Yannas-Sun/E-skin_MSc_final_report/power scalability/DATA/raw/README.md

# Raw inputs

This folder contains source evidence only. `canonical/` holds the continuous-read power matrix, source photographs, targeted retests and supplements; `intake/` holds the dated voltage additions before they are consumed by the review scripts. Do not edit these records in place. The scripts in `../../script/Main/` read them and write derived outputs under `../analysis/`.
