Yannas-Sun/E-skin_MSc_final_report/power scalability/DATA/reference/README.md

# Reference snapshots

These frozen analyses and figure packages are retained because current manifests cite their hashes. They document earlier report versions and are useful for audit or comparison. They are not additional current measurements and should not be used as a replacement for `../analysis/current/`.
