Yannas-Sun/E-skin_MSc_final_report/data scalability/analysis/20260907_delta_zero_review/README.md

# DELTA zero-load audit

This snapshot contains the independent audit, timing checks, per-slot activity statistics and path/hash records for the 45 selected DELTA zero-load windows. The report''s ordinary-mask trend and byte ledger use the derived CSVs in ../../data together with these audit outputs. Raw recordings remain under ../../data/DELTA/Zero_load/.
