Yannas-Sun/E-skin_MSc_final_report/data scalability/analysis/20260907_n4_connector_retest_review/README.md

# N=4 connector-reinstallation review

This snapshot documents the post-reinstallation M0-M3 simultaneous full-coverage DELTA batch. Three consecutive main windows passed the independent audit and are the selected N=4 dynamic performance set. Organization and hash-verification files distinguish this batch from the pre-reinstallation diagnostic batch in ../20260907_n4_full_coverage_review/.
