Yannas-Sun/E-skin_MSc_final_report/power scalability/DATA/reference/report_v2_4_analysis/README_CN.md

# Power record: reference / report_v2_4_analysis

Derived or source record for the report's power-scalability evidence. Raw measurements are retained as recorded; derived tables and figures are generated from the canonical inputs.

See power scalability/README.md and the nearest parent README for scope and provenance. Do not edit raw records in place.
