Yannas-Sun/E-skin_MSc_final_report/data scalability/data/DELTA/Dynamic_load/README.md

# DELTA dynamic batches

Seven three-window batches are indexed. Five complete passing batches provide the 15-window performance subset; two batches remain diagnostic because of earlier sequence or connector findings.

| Scenario | Windows | PASS / CHECK | Mean packet (B) | USB (Mbit/s) |
|---|---:|---:|---:|---:|
| Earliest M1 large-area batch (diagnostic) | 3 | 0 / 3 | 272.23 +/- 11.24 | 0.433820 +/- 0.019034 |
| M1 large-area follow-up | 3 | 3 / 0 | 282.42 +/- 4.74 | 0.452052 +/- 0.007582 |
| M1 repeated press/release | 3 | 3 / 0 | 210.64 +/- 10.57 | 0.337729 +/- 0.016879 |
| M1 rolling input | 3 | 3 / 0 | 357.72 +/- 11.18 | 0.573369 +/- 0.017977 |
| M1 + M3 simultaneous large-area | 3 | 3 / 0 | 510.90 +/- 11.14 | 0.815880 +/- 0.017786 |
| M0-M3 simultaneous full coverage, before connector reinstallation (diagnostic) | 3 | 1 / 2 | 1,674.37 +/- 55.07 | 2.634962 +/- 0.067917 |
| M0-M3 simultaneous full coverage, after connector reinstallation | 3 | 3 / 0 | 1,471.55 +/- 29.89 | 2.347583 +/- 0.048143 |

The main window is fixed at 10 seconds to recording stop. The pre-reinstallation N=4 batch is retained as diagnostic evidence; its connector-contact finding is not pooled with the post-reinstallation performance batch. No N=3 dynamic or independent small-area batch is present.
