Yannas-Sun/E-skin_MSc_final_report/data scalability/analysis/20260907_final_data_review/before_catalog/README.md

# Archived or internal record

This README belongs to data scalability\analysis\20260907_final_data_review\before_catalog, a superseded snapshot, audit workspace or historical report version. It is retained for provenance only and is outside the current report evidence boundary.

See the nearest current README for the release scope. No measurement data were changed.
