Yannas-Sun/E-skin_MSc_final_report/power scalability/DATA/analysis/current/report_v2_8_analysis/README.md

# Report v2.8 analysis snapshot

This is the latest compiled numerical snapshot used to export the current Power figure set. It contains configuration summaries, branch readings, group summaries, additivity checks, module-drop changes and a complete source_manifest.json.

The snapshot represents 30 ZERO/MAX configuration entries, 64 selected branch observations, 32 paired module-level load differences and seven pointwise targeted branch updates. No new complete-configuration repeat was added.

Use source_manifest.json to verify the upstream report_v2_4_analysis, raw-record, review and script hashes. The CSV fields are descriptive: between-combination SD is not repeatability, sequential branch sums are not simultaneous peaks, and voltage differences are not high-speed transient measurements.
