Yannas-Sun/E-skin_MSc_final_report/data scalability/data/FULL/N=1/200Hz/README.md

# Data record: FULL / N=1 / 200Hz

Canonical record for the report's data-scalability experiments. Raw files in this directory are retained unchanged.

Use the nearest parent README for the condition summary. The run indexes and selected windows are in the parent data directory; report-linked figures are under the LaTeX figures/data directory.
