Yannas-Sun/E-skin_MSc_final_report/data scalability/analysis/20260907_delta_zero_review/coverage_review.md

# DELTA 零载记录：覆盖范围、来源与时间戳复核

复核时间：2026-09-07。对象为 `20260907_013132_404213` 至
`20260907_020930_401399` 的 45 次记录。仅阅读原始目录并生成本分析目录中的派生文件；
读取前后文件大小及修改时间一致。原始流的独立解码验证见同次审计的其他输出。

## 实验覆盖

- 四个槽位的全部 15 种非空组合均齐全，每种恰好 3 次记录，无缺项。
- N=1、2、3、4 分别有 12、18、12、3 次记录。
- 15 个 batch 的重复编号均为 1、2、3，同一 batch 的模块组合保持一致。
- 45 次均标记 `DELTA`、`zero_load`、目标 200 Hz，实际开始观测模式为 DELTA。
- 每次请求录制 40 s，前段 10 s；实际总时长 40.000074–40.053896 s，
  主分析窗口 30.000074–30.053896 s。45 次均正常到时结束，没有未完成记录。
- 所有 block 均为 1。`batch_recording_method` 明确为
  `consecutive_capture_windows_same_setup`：这是同一次装配下连续采集的三次时间重复，
  并非三个独立重新接线、重新装配或重新加载的实验区组。重复统计应如实注明这一层级。

## 记录来源及身份的边界

全部 45 次保存的六项本地文件哈希一致（STM32 ELF、Teensy HEX、GUI、recorder、controls、
module detection）。版本目录为 `four-module-variable-spi`。这支持本地构建/记录器来源一致；
哈希没有读取设备 Flash，且 `deployment_confirmed=false`，不能单靠这些 JSON 证明板上镜像。
用户的烧录过程记录可作为另一个来源补充。

SPI 10 MHz、DELTA 阈值 8 是本地配置元数据，目标 200 Hz 是 GUI 设置；这些字段不是
SPI 波形测量或固件配置回读。45 次均采用自动槽位检测并冻结预期集合，但
`board_identity_handling=slots_only`、物理板映射为空。M0–M3 是 CS/IRQ 槽位，
协议未传输唯一板卡身份码；跨组合比较同名槽位时，仍需由实验操作记录确认是否为同一块物理板。

## 完整性状态为何全程 CHECK、主窗口 PASS

主窗口全部 45 次 PASS：270,412 个有效 MUL1 包、576,926 次预期模块更新，
有效模块更新数与预期数相等，诊断载荷为零。574,042 个 ESKD 与 2,884 个 ESKF
均在已建立的文件内基线后被应用。逐次 packet CSV 的主窗口有效包数与 summary 完全一致。

全程全部标记 CHECK REQUIRED，原因是录制是在正在运行的 DELTA 流中截取窗口：
45 次文件开头均有尚未在该文件内建立基线的 ESKD，累计 10,540 个模块帧。
这不能等同为实时 GUI 丢帧或缓存失效。30 次末端保留各 1 B 截断边界，
累计 30 B；另有 35 个跨录制起点的外包，其已知后缀累计 10,189 B 单独记账。
主窗口排除了最初 10 s，已获得完整帧基线；正常文件边界字节不作为内部传输错误。

全程及主窗口的会话差分计数均未出现 outer/inner CRC、序号缺口、重复、倒序、
format error 或 DELTA base mismatch；缺失预期模块更新均为零。
这支持“这些捕获窗口内未观测到所检查的传输/重建错误”，不构成物理 ADC 扫描绝不丢失的证明。

## 到包时间不是 SPI 时钟

主窗口共 270,367 个文件内相邻包间隔：

| 时间来源 | 中位数 | P95 | P99 | 最小值 | 最大值 |
|---|---:|---:|---:|---:|---:|
| PC 包完成时刻差 | 4.8551 ms | 10.8040 ms | 18.4817 ms | 0 ms | 4040.8594 ms |
| Teensy `host_ms` 差 | 5 ms | 5 ms | 6 ms | 3 ms | 7 ms |

PC 有 38,603 个零间隔，表示多个包共享同一次接收处理的完成时间戳；没有负间隔。
23 次记录出现过 PC 间隔超过 100 ms，累计 162 次；Teensy 时间戳没有超过 100 ms 的间隔。
这些相邻包的 MUL1 序号步长全部为 1。

最大的三个 PC 间隔分别为：

| run_id | PC 间隔 | 同一对包的 Teensy 间隔 | 序号步长 |
|---|---:|---:|---:|
| `20260907_020041_855845` | 4040.8594 ms | 5 ms | 1 |
| `20260907_014545_965962` | 3783.2828 ms | 5 ms | 1 |
| `20260907_015550_103879` | 3737.0086 ms | 5 ms | 1 |

这表明 PC 记录的完成时间明显受到接收缓冲、批处理或调度停顿影响；没有证据把它归因为
SPI SCK 不稳定。`host_ms` 由 Teensy 在构建/入队 MUL1 时调用 `millis()` 写入，
其 1 ms 分辨率也不是 SPI 边沿或 ADC 扫描时刻测量。

按同一批包的首尾 Teensy 时间戳计算，各次频率约为 200.0733–200.4065 Hz；
主窗口包数除以 PC 窗口时长则为 199.3419–204.0041 Hz。特别是
`20260907_015217_328962` 的主窗口有 6,121 个包，PC 统计约 204.0041 Hz，
这些包在 Teensy 时间轴上首尾相隔 30.549 s（约 200.3339 Hz）。
缓冲使 PC 窗口与源端时间窗口不完全对应，不能把 204 Hz 解读为实际扫描加速。
统计接收吞吐可以使用 PC 窗口，但分析扫描节奏、ESKF 时间间隔或短期时序应同时报告
Teensy 时间轴，并明确两者测量位置。绝对单程延迟不能从未同步的两个时钟直接求得。

复现：`python -B timing_review.py`。该脚本冻结上述 run_id 范围并递归定位目录，
方便整理目录后再次运行。详细输出为 `coverage_review.json`、`timing_summary.json`
及 `timing_per_run.csv`。
