Yannas-Sun/E-skin_MSc_final_report/data scalability/analysis/20260907_full_completion_review/ANALYSIS_CN.md

# FULL 补测完成审计：新 M012 批次与 N=4

固定六条新完成记录，只读 raw/packet_log/module_log/events/summary，不改原文件。旧 42 条不算新增未审计。M012 新批次独立存放，原 Repeat 1–3 与原失败证据不覆盖。

| 新批次 | n | 主窗 Hz 均值 ± 样本 SD | 完整包长度 B | 完整包吞吐 Mbit/s 均值 ± SD | main/full PASS |
|---|---:|---:|---:|---:|---:|
| M0+M1+M2 / N=3 | 3 | 200.084479 ± 0.057550 | 3172 | 5.077344 ± 0.001460 | 3/1 |
| M0+M1+M2+M3 / N=4 | 3 | 200.066062 ± 0.034040 | 4216 | 6.747828 ± 0.001148 | 3/2 |

逐包核验候选 48,070 / 有效 MUL1 48,070，有效 ESKF 168,243；主窗口候选 36,017 / 有效 MUL1 36,017 / ESKF 126,058。核对 192,280 行 module_log。

长度按 N 动态验证：40+1044N，因此 N=3 为 3172 B、N=4 为 4216 B。扫描每个 MAGIC，包括可能被坏候选覆盖的内部 MAGIC；候选与有效包分别统计。独立核对外 CRC、内 CRC、版本/flags/mask、MUL1 和模块序号、实际有效槽位、日志 offset/长度/序号/时间/字段、raw SHA256 及原 summary 同口径计数。

独立非零问题：`{}`。

全部六条主窗口 PASS，可用于各自条件的性能分析。全窗口三条 PASS，另三条仅因结束时保留 1 B M 片段而 CHECK；没有内部 unassigned、CRC、序号、漏更新或原日志未解析的有效重叠包。原状态不改。

启动边界共 4 个：2 个用前段真实尾字节+后段真实前缀双层 CRC 验证；2 个每批首段仅补推定 M 验证一致性。边界后缀单列，不回填前缀，不混入完整包率/K/q。

## 每段状态及时间停顿线索

- `20260907_004948_668301`：N=3；候选/有效 8005/8005；main=PASS / full=CHECK REQUIRED；主窗 200.138830 Hz。最大 PC 包完成间隔 32.222400 ms（桥端相邻间隔 5 ms）；最大桥端 host_ms 间隔 6 ms（2243844→2243845）。
- `20260907_005028_724004`：N=3；候选/有效 8014/8014；main=PASS / full=PASS；主窗 200.090418 Hz。最大 PC 包完成间隔 54.175100 ms（桥端相邻间隔 5 ms）；最大桥端 host_ms 间隔 6 ms（2252091→2252092）。
- `20260907_005108_797842`：N=3；候选/有效 8018/8018；main=PASS / full=CHECK REQUIRED；主窗 200.024190 Hz。最大 PC 包完成间隔 278.793500 ms（桥端相邻间隔 5 ms）；最大桥端 host_ms 间隔 6 ms（2258809→2258810）。
- `20260907_005250_875035`：N=4；候选/有效 8003/8003；main=PASS / full=CHECK REQUIRED；主窗 200.066611 Hz。最大 PC 包完成间隔 32.093100 ms（桥端相邻间隔 5 ms）；最大桥端 host_ms 间隔 6 ms（2278237→2278238）。
- `20260907_005330_930696`：N=4；候选/有效 8013/8013；main=PASS / full=PASS；主窗 200.031751 Hz。最大 PC 包完成间隔 48.704400 ms（桥端相邻间隔 5 ms）；最大桥端 host_ms 间隔 6 ms（2286880→2286881）。
- `20260907_005410_996854`：N=4；候选/有效 8017/8017；main=PASS / full=PASS；主窗 200.099825 Hz。最大 PC 包完成间隔 18.478100 ms（桥端相邻间隔 5 ms）；最大桥端 host_ms 间隔 6 ms（2296625→2296626）。

PC 完成间隔受读取、缓冲与调度影响，不等同 SPI 时钟周期；桥端 host_ms 也是协议时间字段。这些停顿线索与序号/CRC审计分开保留，不能只凭一次时间间隔定位硬件、USB或PC根因。

历史必须保留：原 M012 `20260907_000133_670681` 的主窗口仍为 CHECK，包含短缺/损坏候选及一个 raw 可恢复、PC漏解析的包。本轮新批次通过，不能改写为之前全部 48 条均无错误。新三条 M012 是补测批次；此前两条 PASS 可由父任务在明确批次来源后另行汇总，原失败条不覆写。

三段是同一 setup 的连续时间重复，不等于独立重新搭建 block；物理板身份不能从槽位ID唯一确定；记录内本地源文件hash不等于设备flash读回。本轮完成的是FULL零载条件，DELTA及动态/K实验仍需独立数据。

迁移后脚本按 summary.run_id 递归定位当前目录，可查父任务 run_index/path_map；原summary历史files路径不改。复现：`python -B audit_records.py`。新完成未纳入记录：无
