Yannas-Sun/E-skin_MSc_final_report/data scalability/analysis/20260907_n3_full_review/ANALYSIS_CN.md

# N=3 FULL 独立审计：保留异常与原统计口径

固定 12 条已完成记录，M012/M013/M023/M123 各 3 条；不改原始 raw、packet_log、module_log 或 summary。旧 N=1/N=2 不计作新增未审计。

| 组合 | PASS 性能 n | PASS 主窗 Hz 均值 ± 样本 SD | 全3条诊断 Hz 均值 ± SD |
|---|---:|---:|---:|
| M0+M1+M2 | 2 | 200.131100 ± 0.000728 | 200.091843 ± 0.067998 |
| M0+M1+M3 | 3 | 199.766908 ± 0.556959 | 199.766908 ± 0.556959 |
| M0+M2+M3 | 3 | 200.165942 ± 0.036616 | 200.165942 ± 0.036616 |
| M1+M2+M3 | 3 | 200.218529 ± 0.040178 | 200.218529 ± 0.040178 |

原日志共 96,120 个候选，其中 96,119 个外 CRC 有效，拒绝 1 个；主窗口候选 72,029、有效 72,028。核对 module_log 384,476 行，有效 ESKF 288,357 个。独立全 MAGIC 扫描另找到一个 CRC 有效但原日志漏解析的重叠包，故 forensic 数量与原日志口径分开。

主窗口有效 ESKF 216,084 个；11 条 PASS 性能子集仅包含 66,027 个主窗口 MUL1 / 198,081 个 ESKF。异常记录仍保留在全部 12 条诊断统计中。

## 首段异常：20260907_000133_670681（M0+M1+M2 Repeat 1）

异常发生在 elapsed **19.4723392 s**（主窗口开始后 9.4723392 s），PC 记录完成时间 **00:01:53.143020 +01:00**。原统计完整候选 8003 / CRC 有效 8002；主窗口候选 6002 / 有效 6001。该段 main/full CHECK 原样保留，性能汇总的 M012 仅使用另外两条 PASS，n=2；全三条另列诊断统计，不静默删除异常。

| 观察 | 序号 | raw 字节 offset | 长度/状态 |
|---|---:|---:|---|
| 前有效包 | 1675976 | 12326391 | 3172 B；双层 CRC 有效 |
| 被拒候选 | 1675977 | 12329563 | 声明 3172 B；外 CRC 错 |
| raw 中有效、原日志未解析包 | 1675978 | 12331711 | 3172 B；外 CRC 与三个 ESKF 内 CRC 全有效 |
| 原日志恢复有效解析 | 1675979 | 12334883 | 3172 B；双层 CRC 有效 |

5977 头到 5978 头实际相隔 **2148 B**，比头中声明 3172 B 少 **1024 B**。这直接支持字节流存在短缺/畸形片段，不能仅凭 raw 判定发生在 Teensy 构包、USB/驱动、串口缓冲或 PC 读取的哪一层。不能声称已证明 USB 物理丢了两个包。

当时 framer 从 5977 头取满声明的 3172 B，包含下一个有效 5978 的前 1024 B。CRC 被拒后，后续重同步跳过 5978 余下的 2148 B，直到 5979。因而原 Session **lost=2** 包含 **1 个短缺/损坏候选 5977，加 1 个 raw 中仍完整有效但被 PC 解析跳过的 5978**。独立所有 MAGIC 扫描恢复的是证据，未回填原日志或修改原计数。

原日志将区间 **[12332735,12334883)** 的 2148 B 标为 interior unassigned；这些字节实际是有效包 5978 的后缀，不是随机垃圾。若按独立有效包范围看，无法由有效包覆盖的是较早的 **[12329563,12331711)** 2148 B 短缺候选片段。两种范围碰巧同为 2148 B，但位置与含义不同，不能混淆。另有 1 B 结束边界。

有效包对应三个模块内序号为：5976 的 M0/M1/M2 = 8040/8041/8040；raw 恢复 5978 为 8042/8043/8042；5979 为 8043/8044/8043。原日志成功包跨过两次序号；计入 raw 可恢复包后只剩一次缺口。原 summary 的模块更新 18003/18003 是**以已接受外 CRC 有效包为条件**，不包含整个被拒包，不能据此声称主窗口完全没有传输异常。

## M013 Repeat 3：199.123828 Hz

20260907_001505_375008 的主窗口为 5974 个有效包 / 30.001432 s = **199.123828 Hz**；CRC、MUL1/模块序号和日志一致性没有异常，保留为 PASS，n=3 性能统计不得为提高均值而剔除。

桥端 host_ms 在连续序号 **1836089→1836090** 之间相隔 **123 ms**，三个模块内序号各增加 1。PC 完成时间最大间隔 **301.3735 ms**（1836053→1836054），对应桥端 host_ms 仅隔 5 ms，说明 PC 接收/调度时间和桥端时间不能混为一个时钟。数据支持这一段存在输出/观测节奏停顿，不能用低帧率直接断言包序号丢失，也不能仅凭记录定位停顿根因。末尾保留 **1020 B** 未完成包片段，是结束边界，不是首段的 interior 故障。

## 逐段原始状态

- `20260907_000133_670681`：main=CHECK REQUIRED / full=CHECK REQUIRED；候选/有效=8003/8002；主窗=200.013328 Hz；cross-check={}；full理由=['outer_crc_error', 'pc_parser_errors', 'outer_sequence_gap_events', 'session_lost_frames', 'session_outer_crc_errors', 'session_sequence_gap_events', 'unassigned_raw_bytes_in_full_capture']。
- `20260907_000213_737553`：main=PASS / full=PASS；候选/有效=8016/8016；主窗=200.131615 Hz；cross-check={}；full理由=[]。
- `20260907_000253_764287`：main=PASS / full=CHECK REQUIRED；候选/有效=7998/7998；主窗=200.130585 Hz；cross-check={}；full理由=['unassigned_raw_bytes_in_full_capture']。
- `20260907_001345_234235`：main=PASS / full=CHECK REQUIRED；候选/有效=8005/8005；主窗=200.094736 Hz；cross-check={}；full理由=['unassigned_raw_bytes_in_full_capture']。
- `20260907_001425_309099`：main=PASS / full=PASS；候选/有效=8018/8018；主窗=200.082161 Hz；cross-check={}；full理由=[]。
- `20260907_001505_375008`：main=PASS / full=CHECK REQUIRED；候选/有效=7988/7988；主窗=199.123828 Hz；cross-check={}；full理由=['unassigned_raw_bytes_in_full_capture']。
- `20260907_001710_986331`：main=PASS / full=CHECK REQUIRED；候选/有效=8007/8007；主窗=200.144160 Hz；cross-check={}；full理由=['unassigned_raw_bytes_in_full_capture']。
- `20260907_001751_034069`：main=PASS / full=CHECK REQUIRED；候选/有效=8015/8015；主窗=200.145451 Hz；cross-check={}；full理由=['unassigned_raw_bytes_in_full_capture']。
- `20260907_001831_069491`：main=PASS / full=CHECK REQUIRED；候选/有效=8014/8014；主窗=200.208216 Hz；cross-check={}；full理由=['unassigned_raw_bytes_in_full_capture']。
- `20260907_003258_918645`：main=PASS / full=PASS；候选/有效=8008/8008；主窗=200.231866 Hz；cross-check={}；full理由=[]。
- `20260907_003339_025463`：main=PASS / full=CHECK REQUIRED；候选/有效=8031/8031；主窗=200.250342 Hz；cross-check={}；full理由=['unassigned_raw_bytes_in_full_capture']。
- `20260907_003419_073823`：main=PASS / full=PASS；候选/有效=8017/8017；主窗=200.173378 Hz；cross-check={}；full理由=[]。

建议：首条 M012 Repeat 1 保留为完整性失败证据，并补一条同条件重复用于达到 3 条 PASS 性能数据；明确后补的时间与新 run_id，不覆写原 Repeat 1。其余 11 条主窗口可用；低率 PASS 记录保留。若研究目标包括恢复能力，可将此次坏包后的漏解析作为已发现的 PC 恢复行为局限，不能宣称协议已无损恢复。

三次是同一 setup 的时间重复，不是三个独立 block。所有有效完整包应为 3172 B（20+16+3×1044+4）。槽位不是唯一板卡身份；本地代码哈希不是设备 flash 读回。raw 本身无 PC 到达时间，主窗口依赖日志完成时间。

脚本按 summary.run_id 递归定位，因此搬迁后可复跑；原 summary 的历史 files 路径不改，可查父任务 run_index/path_map。复现：`python -B audit_records.py`。新完成未纳入记录：无
