Yannas-Sun/E-skin_MSc_final_report/power scalability/DATA/analysis/current/report_v2_8_figures/single_module_screening.pdf

Blocked, zero load | Continuous, zero load | Continuous, loaded

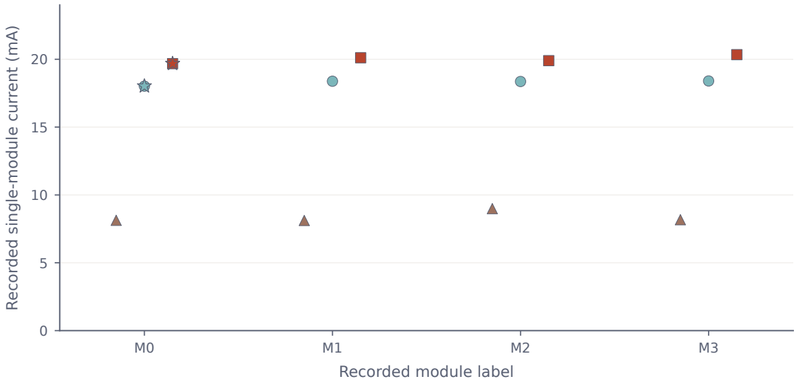
[picture p20: figure]
Recorded module label; Recorded single-module current (mA)
