Yannas-Sun/E-skin_MSc_final_report/data scalability/figures/exports/02b_usb_theoretical_200hz.pdf

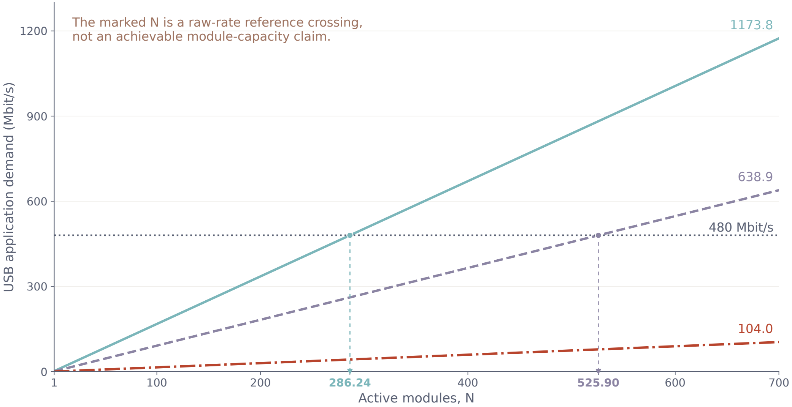
[picture p44: figure]
Active modules, N; USB application demand (Mbit/s); 480 Mbit/s; not an achievable module-capacity claim.

The marked N is a raw-rate reference crossing,

## 02B USB: 200 Hz demand across 700 modules

N = 1–700 | fixed round frequency = 200 Hz | theoretical demand, not achieved throughput

Nominal periodic ESKF only: T=1 s; q=min(1,1/fT); q_other=0. Continuous-cycle approximation. H(M) = 24 + 4M B; N <= M. Current M = 4; N > 4 uses M = max(4, N) as extrapolation.

FULL / mean DELTA K_D=480
Mean DELTA K_D=240

Mean DELTA K_D=0
USB 2.0 HS: 480 Mbit/s raw signaling
