Yannas-Sun/E-skin_MSc_final_report/data scalability/figures/exports/02d_host_spi_theoretical_200hz.pdf

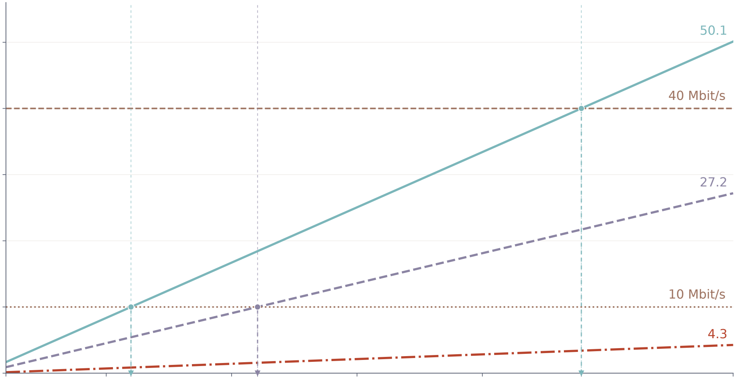
[picture p45: figure]
10 Mbit/s; 40 Mbit/s

1 | 5 5.99 | 1011.03 | 15 | 20 | 23.95 | 30

## Active modules, N

0

10

20

30

40

50

## Host SPI demand (Mbit/s)

# 02D Host SPI: 200 Hz mean DELTA demand

N = 1–30 | nominal periodic reference q=0.005 | no padding or MUL1 wrapper

Nominal periodic ESKF only: T=1 s; q=min(1,1/fT); q_other=0. Continuous-cycle approximation.
Mean SCK budget; no gaps, software or retries. FULL bursts may exceed a round deadline. N>4: extrapolation.

## Mean DELTA, K_D=0 Mean DELTA, K_D=240 FULL / mean DELTA K_D=480

## 10 MHz tested setting: 10 Mbit/s raw 40 MHz untested reference: 40 Mbit/s raw
