Yannas-Sun/E-skin_MSc_final_report/data scalability/figures/exports/07_delta_model_k.pdf

0 | 120 | 240 | 360 | 480
| | Changed cells per module, K

0

20

40

60

80

100

Equivalent round size (kB)

N=1: 1.08

N=25: 26.22

N=50: 52.42

N=100: 104.82

B Selected module counts

0

20

40

60

80

100

Equivalent round size (kB)

# DELTA frame-length model for 100 modules

Ordinary DELTA frames | K = changed cells per module | decimal kB = 1,000 B

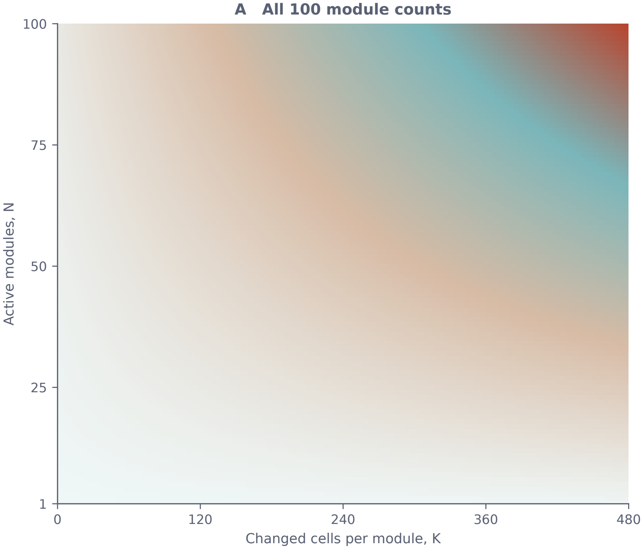
[picture p46: figure]
Changed cells per module, K; Active modules, N; A All 100 module counts

## LDELTA(N, K) = 24 + 4max(4, N) + N(84 + 2K) B

Four module headers are retained for N <= 4; one header per module is assumed for N > 4. Same K is assumed in each module. At K=480, DELTA equals FULL; K>480 triggers FULL fallback. N>4 is an extended logical-round model, not a current MUL1 packet.
