Yannas-Sun/E-skin_MSc_final_report/data scalability/analysis/20260907_delta_followup_review/raw_audit.md

# 三条新增 DELTA 记录：独立原始协议审计

固定记录：20260907_050453_154588、20260907_050533_183636、20260907_050613_222506。原始目录未移动或分类，GUI与原始summary未修改。

记录元数据均误选zero_load；用户明确确认三条均为大面积动态加载，与上一批相同。派生分析标记actual_condition=large_area（用户确认），原始summary保持不变。

完整扫描24,033个MUL1候选、24,033个有效模块内帧，并逐项核对96,132条模块CSV。共28个原始/记录生成文件前后SHA-256一致：True。

|窗口|候选MUL1|有效MUL1|ESKD|ESKF|初始无锚点ESKD|模块序号不连续|
|---|---:|---:|---:|---:|---:|---:|
|full_run|24033|24033|23897|136|201|0|
|initial|6024|6024|5994|30|201|0|
|main|18009|18009|17903|106|0|0|

|Repeat|原主窗口状态|独立协议结论|主窗K_D|主窗q_ESKF|主窗平均包B|主窗PC包率Hz|
|---|---|---|---:|---:|---:|---:|
|1|PASS|NO DETECTED PROTOCOL ANOMALY|74.534876|0.00666223|278.472352|200.109580|
|2|PASS|NO DETECTED PROTOCOL ANOMALY|76.134093|0.00599800|281.112962|200.040035|
|3|PASS|NO DETECTED PROTOCOL ANOMALY|79.836096|0.00499750|287.671831|200.091476|

跨ESKD与ESKF统一检查模块sequence，共发现0次不连续。有效ESKF建立新基线不会使本审计跳过sequence检查；此项独立检查覆盖原GUI的检查盲点，原GUI状态保持不变。

## CRC、缓存和文件边界

- 20260907_050453_154588：raw/log/summary差异={}；外CRC坏候选=0；外层序号事件=0；base不连续=0；目标缺更新=0；锚点后未应用=0。
  开始边界=[{"packet_sequence": 208203, "prefix_bytes": 1, "suffix_bytes": 123, "evidence": "inferred_single_magic_byte_not_recorded", "verified": true, "errors": [], "event_errors": [], "previous_run_id": null}]；未分配区=[{"offset": 1938633, "bytes": 1, "kind": "trailing"}]。
- 20260907_050533_183636：raw/log/summary差异={}；外CRC坏候选=0；外层序号事件=0；base不连续=0；目标缺更新=0；锚点后未应用=0。
  开始边界=[{"packet_sequence": 216213, "prefix_bytes": 1, "suffix_bytes": 131, "evidence": "actual_previous_raw_tail", "verified": true, "errors": [], "event_errors": [], "previous_run_id": "20260907_050453_154588"}]；未分配区=[{"offset": 1953647, "bytes": 1, "kind": "trailing"}]。
- 20260907_050613_222506：raw/log/summary差异={}；外CRC坏候选=0；外层序号事件=0；base不连续=0；目标缺更新=0；锚点后未应用=0。
  开始边界=[{"packet_sequence": 224225, "prefix_bytes": 1, "suffix_bytes": 125, "evidence": "actual_previous_raw_tail", "verified": true, "errors": [], "event_errors": [], "previous_run_id": "20260907_050533_183636"}]；未分配区=[{"offset": 1991913, "bytes": 1, "kind": "trailing"}]。

初始未锚定ESKD表示文件尚未包含基线，不证明传输丢帧；开始边界包不混入完整包数、K或q。实际前一文件尾部拼接与仅补magic单字节的推断在JSON中分别标注。

q=全部有效ESKF/(ESKF+ESKD)，K_D仅由普通ESKD两层mask计数。ESKF触发原因没有独立事件字段，不能由ESKF或其出现时刻确诊硬件重启、供电原因或丢失物理扫描。序号跳变仅表明记录中的编号不连续。

PC包完成时间决定初始/主窗口，桥host_ms是桥端时间字段；两者都不是直接SCK波形测量。三次连续录制是同一setup的时间重复。复现：`python -B -X utf8 raw_audit.py`。
