Yannas-Sun/E-skin_MSc_final_report/data scalability/analysis/20260907_delta_followup_review/REVIEW_CN.md

# 新增三条 M1 大面积动态加载记录分析

固定分析 2026-09-07 05:04:53、05:05:33、05:06:13 开始的三条记录，ID 分别为 20260907_050453_154588、20260907_050533_183636、20260907_050613_222506。

**结论：三条主分析窗口均通过本次独立协议检查，可以用于 M1、N=1 大面积动态加载的描述统计。上一批跨 ESKF 的模块序号回退/前跳在本批没有复现。** 这是本批观察结果，不能据此宣布旧故障已永久消除，或推断物理 SPI 时钟稳定性。

## 1. 实验条件与标签纠正

三条均为 M1 槽位、N=1、DELTA、目标 200 Hz、阈值 8、本地 SPI 配置 10 MHz。每条完整记录约 40 s，前 10 s 不进入主分析窗口，主窗口各约 30 s。

原 metadata 的 condition 均为 zero_load；用户在本次对话明确确认实际做的是“大面积动态加载，与上一批相同”。分析使用 actual_condition=large_area，确认来源另存 [condition_correction.json](condition_correction.json)。原始 summary、日志和图片中的采集时标签保留，不把这三条当作零载补测。

三段属于同一 batch 的 Repeat 1/2/3，是同一设置下连续的时间窗口，n=3、batch_n=1。没有新增独立装配、精确力、面积或加载节奏的记录，不能用 n=3 表示三个独立装配样本。槽位不是板卡唯一身份码；本地文件哈希不是设备烧录回读。

## 2. 数据完整性

完整解析全部 24,033 个有效 MUL1 和对应 24,033 个内帧，逐项核对 96,132 条逐槽日志。

| 范围 | 有效 MUL1 | 普通 ESKD | ESKF | 模块内序号不连续 |
|---|---:|---:|---:|---:|
| 完整三段 | 24,033 | 23,897 | 136 | 0 |
| 前 10 s 合计 | 6,024 | 5,994 | 30 | 0 |
| 主窗口合计 | 18,009 | 17,903 | 106 | 0 |

内外 CRC、帧布局、mask/K、FULL sentinel、外层序号、跨 ESKD/ESKF 的模块内序号、DELTA base 链、预期 M1 更新、raw 与 CSV/summary 对照均未发现异常。主窗口没有未建立基线的 DELTA，也没有基线建立后未能应用的帧。

原 GUI 全程 CHECK 保留：合计 201 个初始 ESKD 在各文件中尚无基线，三条各留末尾 1 B。三段分别在 0.2431、0.4443、0.2806 s 建立文件内基线，均早于主窗口。两个相邻文件边界经真实前尾/后首拼接验证；第一段开始边界仅补缺失 magic 单字节属于推断，证据等级已分别记录。

上一批三条大面积记录共 14 次模块内序号异常，本批为 0；两批应分别保留。上一批仍作为异常诊断数据，不能因为补测通过而改写其 CHECK，也不应直接混成六次合格实验。

## 3. 主窗口传输表现

包长和流量均包含 ESKF 成本；USB 列为实际完整有效 MUL1 字节除以主窗口实际时长，不是 USB 物理链路总占用。

| Repeat | 有效包数 | PC 包率 Hz | 平均 MUL1 B | 有效 USB Mbit/s | 普通 ESKD 平均 K | ESKF 数量 | ESKF 比例 |
|---|---:|---:|---:|---:|---:|---:|---:|
| 1 | 6,004 | 200.1096 | 278.4724 | 0.445800 | 74.5349 | 40 | 0.66622% |
| 2 | 6,002 | 200.0400 | 281.1130 | 0.449871 | 76.1341 | 36 | 0.59980% |
| 3 | 6,003 | 200.0915 | 287.6718 | 0.460485 | 79.8361 | 30 | 0.49975% |
| 三段均值 ± 样本 SD | — | 200.0804 ± 0.0361 | 282.4190 ± 4.7368 | 0.452052 ± 0.007582 | 76.8350 ± 2.7192 | — | 0.58859% ± 0.08380 个百分点 |

本例 N=1、最大槽位数 M=4，完整 MUL1 普通 DELTA 长度为 124+2K B，ESKF 为 1084 B。因此平均模型为：

\[\overline L=(1-q)(124+2\overline K_D)+1084q.\]

第三段 ESKF 最少，但平均包长最大，因为普通 ESKD 的平均 K 更大。评价带宽需要同时看 K 的分布和 ESKF 占比，不能只数 ESKF。普通 K 的中位数为 30/34/37，均值明显更高，反映动态记录中的高 K 段对平均流量有较大贡献；这不是字节模型误差。

相对于同一 N=1 的 FULL 每包 1084 B，在相同包率下，本批平均完整 MUL1 字节量减少约 73.95%，已计入 ESKF。此数值对应本批实际加载动作，不能推广成所有动态条件的固定压缩率。

相对于同一 N=1 的 FULL 每包 1084 B，在相同包率下，本批平均完整 MUL1 字节量减少约 73.95%，已计入 ESKF。此数值对应本批实际加载动作，不能推广成所有动态条件的固定压缩率。

上一批大面积三段的诊断均值为 272.2347 B、0.433820 Mbit/s。本批分别为 282.4190 B、0.452052 Mbit/s，包长约高 3.74%。用户确认实验类型相同，但实际加载波形未严格量化，因此不能据这点变化断言压缩算法改进或退化。

## 4. 时序与 ESKF 的解释

| Repeat | 主窗 PC 最大完成间隔 ms | 同窗桥端最大入队间隔 ms | 桥端首尾包跨度率 Hz |
|---|---:|---:|---:|
| 1 | 47.5784 | 7 | 200.1467 |
| 2 | 17.2000 | 7 | 200.0667 |
| 3 | 17.5684 | 7 | 200.0933 |

桥端时间字段在三段主窗口均未出现上一批的 22–126 ms 长间隔。PC 时间可能受串口接收批处理和调度影响；本批 PC 间隔大于桥端间隔，不能将其解释为 SPI SCK 不稳定。

三段完整记录的 ESKF 数分别为 50/46/40，主窗为 40/36/30。前两段部分 ESKF 的间隔短于通常约 1 s 的间隔，但内外序号和缓存链仍连续。这说明出现较多 ESKF 不必伴随本批可检测的传输异常，不能仅凭 ESKF 出现就解释上一批错误。

日志没有独立的 ESKF 触发原因字段。本次只报告全部 ESKF 和事件时间，不把这些事件强制拆成定时、K 超限或其他恢复原因，也不以时间间隔推断硬件重启。协议计数和 host_ms 都不能替代直接 SCK 波形或每次物理扫描计数。

## 5. 交付与后续使用

- [独立 raw 审计](raw_audit.md)、[机器可读结果](raw_audit.json)、[审计脚本](raw_audit.py)。
- [逐段/逐窗统计](statistics.csv)、[统计说明](statistics.md)、[快照与全部统计](statistics.json)。
- [PC/桥端时间核对](timing_review.json)、[复现脚本](timing_review.py)。
- [实际条件确认记录](condition_correction.json)。

可以使用这三条的主窗口制作 M1 大面积动态结果及 n=3 的时间重复统计。全部原始文件和现有图片保持原样，未移动目录或更新主索引；后续分类应使用用户确认的大面积动态条件，并与旧 CHECK 批次区分。

28 个现存记录文件共 21,944,443 B 在独立审计前后 SHA-256 一致，其中 raw 二进制合计 5,884,196 B；root 另核对 18 个原始测量文件均未变化。没有修改 GUI、设备固件或论文。
