Yannas-Sun/E-skin_MSc_final_report/data scalability/analysis/20260907_delta_followup_review/statistics.md

# M1 后续三条：统计审查

**用户已确认实际为大面积动态加载，与上一批相同。** 三条metadata仍保留`zero_load`原标签；派生分析使用`recorded_condition=zero_load / actual_condition=large_area`，纠正依据见[condition_correction.json](condition_correction.json)。这不是由曲线推断出的条件，也不是零载噪声补测。

新批run_id为20260907_050453_154588、20260907_050533_183636、20260907_050613_222506；同一batch、Block 1、Repeat 1/2/3。每条约40 s，主窗从10 s开始约30 s。三次均完整保留；n=3是同一setup的连续时间窗口，不是独立装配、独立板卡或独立加载重复。

全部对照均为CS槽位M1、N=1、M=4、DELTA、目标200 Hz、阈值8、本地SPI配置10 MHz。旧Large_area记录load_layers=both；新批原metadata为unspecified，用户确认按同一大面积加载条件操作，具体力、接触面积和节奏未量化。旧零载仅作为不同加载条件的基线。槽位不提供实体板卡UID，本地配置也不是烧录读回证明。

## 每批主窗与全程：均值 ± 样本SD

| 记录批次 | 窗口 | Hz | 有效包均长/B | 有效USB/Mbit/s | 普通ESKD K | 总ESKF q/% |
|---|---|---:|---:|---:|---:|---:|
| 新Large_area（用户确认） | main | 200.080364 ± 0.036080 | 282.419048 ± 4.736771 | 0.452052 ± 0.007582 | 76.835022 ± 2.719229 | 0.588591 ± 0.083800 |
| 新Large_area（用户确认） | full_run | 200.260260 ± 0.055897 | 244.821743 ± 3.369895 | 0.392226 ± 0.005507 | 58.022086 ± 1.959209 | 0.565899 ± 0.062967 |
| 旧Large_area（both层） | main | 199.181124 ± 0.797879 | 272.234655 ± 11.242027 | 0.433820 ± 0.019034 | 70.668405 ± 5.597340 | 0.842627 ± 0.171190 |
| 旧Large_area（both层） | full_run | 199.552504 ± 0.537483 | 244.100126 ± 2.807931 | 0.389688 ± 0.004837 | 56.851206 ± 1.226607 | 0.756002 ± 0.127756 |
| 旧zero_load（层未指定） | main | 200.338411 ± 0.027872 | 130.206632 ± 0.029988 | 0.208683 ± 0.000059 | 0.711124 ± 0.015177 | 0.499113 ± 0.000048 |
| 旧zero_load（层未指定） | full_run | 200.570462 ± 0.235133 | 130.206797 ± 0.033799 | 0.208925 ± 0.000281 | 0.713935 ± 0.018851 | 0.498546 ± 0.000578 |

各行n=3、batch=1；SD的分母为n−1。均值是三条run均值等权平均；没有把数千帧当作独立实验重复。三个不同批次分别列出，不按Repeat编号配对，也不混成n=9。

## 新批逐条结果

| Repeat | 窗口 | Hz | 均长/B | USB/Mbit/s | K均值 | K中位数 [Q1,Q3] | ESKF / ESKD | q/% | 原summary状态 |
|---:|---|---:|---:|---:|---:|---:|---:|---:|---|
| 1 | main | 200.109580 | 278.472352 | 0.445800 | 74.534876 | 30 [4,105] | 40 / 5964 | 0.666223 | PASS |
| 1 | full_run | 200.207177 | 242.041453 | 0.387667 | 56.376052 | 13 [1,64] | 50 / 7959 | 0.624298 | CHECK REQUIRED |
| 2 | main | 200.040035 | 281.112962 | 0.449871 | 76.134093 | 34 [8,103] | 36 / 5966 | 0.599800 | PASS |
| 2 | full_run | 200.255005 | 243.854200 | 0.390664 | 57.501067 | 16 [1,71] | 46 / 7965 | 0.574210 | CHECK REQUIRED |
| 3 | main | 200.091476 | 287.671831 | 0.460485 | 79.836096 | 37 [8,111] | 30 / 5973 | 0.499750 | PASS |
| 3 | full_run | 200.318600 | 248.569574 | 0.398345 | 60.189138 | 16 [1,74] | 40 / 7973 | 0.499189 | CHECK REQUIRED |

K由普通有效ESKD的histogram重算。中位数和四分位数用排序后(n−1)p位置线性插值，IQR=Q3−Q1；不为ESKF虚构物理K。JSON还提供各批合并ESKD histogram的描述性分位数，其样本单位是帧，不能代替run级不确定度。

## 有效字节与完整性口径

有效USB吞吐率=有效完整MUL1字节×8/该窗实际秒数；包率=完整有效MUL1数/实际秒数；Lmean=有效完整字节/完整包数。raw_arrival吞吐单独保留，涉及读取块和截断边界，不冒充有效完整包字节或USB物理总线占用。

本次N=1、M=4：ESKD完整MUL1=124+2K B；ESKF完整MUL1=1084 B。逐窗核验B_valid=40P+84 n_D+2ΣK+1044 n_F（另含任何诊断字节），所有ESKF都计入实际吞吐。q=n_F/(n_F+n_D)。ESKF触发原因没有线上字段，q不能拆成周期/高K/命令等原因。

内部summary/histogram/字节恒等式检查问题：[]。新三条GUI summary主窗PASS、全程CHECK REQUIRED均原样保留；全程初始无锚点ESKD和尾部字节不等同物理传输丢包。详细计数和错误字段在CSV/JSON。

独立raw审计资格：[新批raw审计](raw_audit.md)核验三条主窗共18,009个完整MUL1=17,903 ESKD+106 ESKF，与本统计一致；CRC、格式、K、base、外层序号以及跨全部ESKD/ESKF的内层序号异常均为0。因此仅新批主窗标记独立PASS。全程201个初始无锚点ESKD及每条尾部1 B仍保留CHECK REQUIRED；不称所有完整capture无误。

旧Large_area三条[独立审计](../20260907_delta_large_area_review/raw_audit.json)内层序号不连续事件分别为[1, 11, 2]，均保持CHECK REQUIRED；表中数值仅为含原异常窗口的描述性对照。新三条没有复现这些异常，但不能据一次批次推断原因已修复。两批不合并为n=6，也不覆盖旧异常记录。

## 描述性对照

- 新批相对旧Large_area（both层）：主窗平均有效包长差10.184393 B（3.741%），有效USB率差0.018232 Mbit/s，普通K均值差6.166616。条件关系：same_nominal_large_area_user_confirmed_not_quantitatively_matched。
- 新批相对旧zero_load（层未指定）：主窗平均有效包长差152.212417 B（116.901%），有效USB率差0.243369 Mbit/s，普通K均值差76.123897。条件关系：different_load_condition_baseline_only。

新批与旧Large_area按用户确认的相同名义加载条件作批次描述比较，但加载力、面积与节奏并未测定；不据均值差认定改进、退化或某ESKF触发原因。与旧零载的差异不能称为噪声增加。全部窗口均保留，未以高低速率筛选。

## 复现

运行`statistics_generate.py`读取固定9个summary；运行`statistics_generate.py --from-snapshot`仅用statistics.json内冻结输入。`--refresh-raw-audit`只额外读取同目录派生raw_audit.json。输入SHA256、原metadata与两种scope保存在JSON；不改原记录、索引或图。

[逐run逐窗CSV](statistics.csv) · [输入快照与全部结果](statistics.json) · [生成脚本](statistics_generate.py)
