Yannas-Sun/E-skin_MSc_final_report/data scalability/analysis/20260907_delta_large_area_review/raw_audit_CN.md

# DELTA 大面积加载三条记录：独立原始数据审计

**结论：三条记录的原 GUI 主窗口状态都是 PASS，但独立模块序号检查均需 CHECK。不能把这一批写成“没有任何数据完整性异常”。** 全部 CRC、外层 MUL1 序号、已建立基线后的 DELTA base 链和目标槽位更新检查通过；另外发现 14 次模块内序号不连续，全部在主窗口，且发生在有效 ESKF 上。原始 summary 的 PASS/CHECK 状态未被修改。

固定记录为 `20260907_040621_371357`、`20260907_040701_400114`、`20260907_040741_429011`。均为 M1 槽位、DELTA、large_area，元数据加载层为 both，目标 200 Hz、本地 SPI 设置 10 MHz、阈值 8。三次是同一批次下连续 40 秒时间窗口，每次前 10 秒保留为初始段，后约 30 秒为主窗口；不是三个独立装配或独立加载重复。面积数值、载荷大小、动作节奏和加载协议字段未记录，不能仅凭 large_area/both 标签补写这些实验事实。

## 1. 审计方法与原始文件

直接复用、未修改 `analysis/20260907_delta_zero_review/raw_audit.py` 的 `audit_one()`。其独立 struct/zlib 解码器重新核验 raw 中的包长、内外 CRC、四槽描述符、掩码 popcount、模块序号、DELTA base 链、逐包/逐槽日志以及主/全窗口统计。审计不是重新运行 GUI 的 PASS 判断。

六类原始文件逐条记录在审计前后计算 SHA-256：`mul1_raw.bin`、`packet_log.csv`、`module_log.csv`、`events.jsonl`、`summary.json`、`experiment_log.md`；共 18 个文件全部不变。本审计没有移动文件、修改测量值或重写原始状态。JSON 中 source_directory 保存审计读取时的路径，分类后的当前位置应查分类映射。

## 2. 完整性与窗口计数

|窗口|完整有效 MUL1|有效模块帧|ESKD|ESKF|文件起始无基线 ESKD|
|---|---:|---:|---:|---:|---:|
|全程|23,947|23,947|23,766|181|303|
|前 10 秒|6,020|6,020|5,990|30|303|
|主窗口|17,927|17,927|17,776|151|0|

- 完整包内外 CRC 错误、协议布局/掩码长度错误：0。
- 外层 MUL1 序号间断、重复、倒退：0。
- 目标 M1 缺少有效更新：0；每个有效 MUL1 都有 M1 更新。
- ESKD base 与前一个有效模块帧不连续、文件基线建立后的链断裂、链断裂后未应用的 DELTA 帧：0。
- 原始字节、packet/module CSV 和原 summary 的交叉检查差异：0；共核对 95,788 条逐槽日志。
- 模块内序号不连续：14 次。它们是另外的检查维度，不能被上述零错误计数抵消。

## 3. 必须保留的模块序号异常

|Repeat|主窗口内异常|具体事实|
|---|---:|---|
|1|1|37.345769 秒，ESKD 序号 35295 后收到 ESKF 序号 2，再收到 ESKD 序号 3、base=2。相邻外层包序号连续；桥端 host_ms 间隔为 27 ms。|
|2|11|24.974586–35.117520 秒之间，11 次从不同较大序号回退到 ESKF 序号 2；随后有效 DELTA 从 3、base=2 继续。回退事件对应桥端相邻时间差为 22–48 ms。|
|3|2|18.811820 秒与 18.815980 秒，模块序号为 4724 → ESKF 4728 → ESKF 4730 → ESKD 4731。前跳包含 4725、4726、4727、4729 共四个未在记录中观测到的序号值；第一处桥端相邻时间差为 126 ms。|

14 次均在主窗口，12 次为回退到 ESKF 序号 2，2 次为 ESKF 前跳。所有事件的前一包、当前包和后一包的外/内序号、base、marker、flags、包长、PC 时间与桥端 host_ms 已写入 JSON 的 `inner_sequence_discontinuities[].context`。

原 GUI 后端收到有效 ESKF 时直接设置新的基线；只有 ESKD 才核对前置 base，因此这一类跨 ESKF 的模块序号变化没有进入原 PASS 条件。这里保留原 PASS，同时给出独立 `CHECK REQUIRED`。

本地固件源码 `data_scalability_protocol.c` 显示：FULL 和 DELTA 编码均递增 `next_sequence`；普通周期 FULL、过大 K 回退以及 DELTA_RESYNC 请求均不会把该序号清零；`DataScalability_Init()` 才将其清零。故反复回到序号 2 与重新初始化/复位模式相符，属于需要核查的线索，尚不能由这些 USB 记录确诊硬件复位、供电问题或具体故障原因。局部日志也未证明烧录内容与本地源码完全一致。

三次记录期间 `commands` 都为空，没有已记录的用户或 PC 自动 RESYNC 命令。但 Teensy 本地自动处理不一定表现为 PC 发出的命令，所以不能据此排除桥端自动同步。第三次的四个未观测序号也不能直接解释为四个丢失物理扫描：需要区分编码、重新编码、桥端接受/丢弃以及 USB 入队。

桥端时间也在上述事件处拉长，尤其第三次 126 ms，因此这一批不能把所有间隔都归为 PC 缓冲，或者直接称为“只是 clk 不稳定”。桥端 host_ms 同样不是独立 SCK 波形测量。

## 4. 文件边界与初始化前缀

三条全程原状态均为 CHECK REQUIRED。每条初始未锚定 ESKD 数分别为 44、139、120，首次文件内有效 ESKF 基线分别在 0.222691、0.672563、0.584547 秒建立，均早于主窗口。它们表示录制文件没有保存之前的基线，不能称为已证明的传输丢帧。

Repeat 1 的开始包缺失一个未记录的 magic 字节 `M`：补入已知字节后可通过 CRC，属于推断证据。Repeat 3 的开始包缺失前一条文件尾部的一个字节：与 Repeat 2 实际尾字节拼接可通过 CRC，属于实际跨文件证据。两种证据在 JSON 中区分。Repeat 2、3 各有一个尾部字节没有形成完整包；无内部未分配字节。边界包不混入完整包数、K、q 或主窗口平均值。

## 5. 主窗口统计

|Repeat|有效包数|平均包长 B|普通 ESKD 的 K 均值|ESKF 总比例|PC 完成包率 Hz|PC 完成吞吐 Mbit/s|
|---|---:|---:|---:|---:|---:|---:|
|1|5,998|284.672558|77.044377|0.816939%|199.915985|0.455285|
|2|5,950|269.233950|68.397181|1.025210%|198.332449|0.427183|
|3|5,979|262.797458|66.563658|0.685733%|199.294937|0.418994|

三次记录等权的均值 ± 样本 SD，n=3 时间重复：

- 平均包长：272.234655 ± 11.242027 B。
- 普通 ESKD 的 K 均值：70.668405 ± 5.597340。
- ESKF 总比例：0.842627% ± 0.171190 个百分点。
- PC 完成包率：199.181124 ± 0.797879 Hz。
- PC 完成吞吐：0.433820 ± 0.019034 Mbit/s。

这组统计描述包含上述异常的实际记录，不应作为“无异常动态基线”不加说明地进入主结论。没有为了得到 PASS 或缩小 SD 删除事件时段。

K 仅由有效 ESKD 两层掩码的置位数得到，ESKF 不反推 K。各 run 的 ESKD 最大 K 分别为 480、479、479；ESKF 的成因可能不止一种，不能从 ESKF 包倒推出其原本 K，也不能将全部 ESKF 按 1 秒周期归类。q 的定义是全部有效 ESKF / (ESKF+ESKD)。

主窗口包长采用完整外层有效包的实测长度，吞吐采用其字节数除以实际 PC 主窗口时长；原始串口 read 块到达字节率属于不同统计。所有均值保留同步完整帧成本。时序和流量可如实描述当前记录，但不能代替物理扫描连续性或 SCK 稳定性证明。

## 6. 下一步核查

优先核查按压过程中 M1 是否重新初始化、是否出现供电/复位事件，并同步记录 NRST、供电或固件复位原因；对第三条 126 ms 的序号前跳补桥端/模块端事件记录，区分编码后未输出、桥端重同步和实际数据缺失。GUI 的独立模块序号提示也应覆盖跨 ESKF 的序号回退与前跳。当前记录保留作为诊断证据，是否重测应在原因核查后决定。

审计明细见同目录 `raw_audit.json`。当前记录位置由 `organization_plan.json` 映射至 `data/DELTA/Dynamic_load/N=1/200Hz/M1/Large_area/Repeat_1..3/`；JSON 的 `organized_directory` 为分类后位置，`source_directory` 保留审计时位置。分类索引保留原主窗口 PASS，独立检查标记为 CHECK，并排除出正常主矩阵；记录本身没有删除。本文件仅记录数据证据和适用边界，不修改固件、GUI 或测量文件。
