Yannas-Sun/E-skin_MSc_final_report/data scalability/analysis/20260907_delta_press_release_review/REVIEW_CN.md

# 新增大面积反复按压、释放：三条记录分析

固定记录为 20260907_051941_159689、20260907_052021_196300、20260907_052101_230925，对应 2026-09-07 05:19:41、05:20:21、05:21:01 开始的三段录制。

**三条主窗口均通过独立协议审计，可用于 M1、N=1 的大面积反复按压、释放场景统计。** 没有复现最早一批大面积数据中的跨 ESKF 模块序号异常。本结论限于本批观测窗口，不表示已查明或永久消除了旧故障原因。

## 条件与统计单位

实际条件由用户明确说明为“大面积反复按压、释放”。原 metadata 仍为 zero_load，派生记录使用 actual_condition=large_area、actual_load_protocol=repeated_press_release；纠正依据见 [condition_correction.json](condition_correction.json)。原始 summary、日志及图片保持原标签，不把本批归作零载实验。

三条均为 M1 槽位、N=1、DELTA、目标200 Hz、阈值8、本地SPI配置10 MHz，来自同一batch的Repeat1/2/3。每段约40 s，保留固定10–40 s主窗口，包含其中的加载和静息部分，不另挑高活动片段。n=3表示同一设置下连续的时间窗口，batch_n=1，不作为独立装配或三个独立板卡样本。

加载层在原记录中为unspecified；没有精确力、接触面积、按压频率或每次动作时间标记，不补写这些变量。M1为通信槽位，协议不传唯一板卡身份。记录中的SPI/阈值及文件哈希属于本地配置证据，不是设备读回或SCK实测。

## 独立完整性检查

完整扫描24,059个有效MUL1及对应内帧，并核对96,236条逐槽日志。

| 窗口 | 有效MUL1 | ESKD | ESKF | 跨ESKD/ESKF模块序号异常 |
|---|---:|---:|---:|---:|
| 全程三段 | 24,059 | 23,938 | 121 | 0 |
| 前10 s合计 | 6,020 | 5,990 | 30 | 0 |
| 主窗口合计 | 18,039 | 17,948 | 91 | 0 |

内外CRC、帧布局、K/mask、FULL sentinel、外层序号、模块内序号、DELTA base链、M1更新，以及raw/CSV/summary对照均无异常。基线建立后未能应用的帧数为0。

全程原CHECK保留：初始无文件基线的ESKD共367个；R1/R2各有末尾1 B，R3没有末尾残片。各文件在0.0414、0.9295、0.8225 s建立基线，均早于主窗口。R2/R3开始边界经前文件尾部真实拼接验证；R1缺失magic单字节的恢复仅属于推断，已区分记录。

## 主窗口传输统计

| Repeat | 有效包数 | PC包率 Hz | 平均包长 B | 有效USB Mbit/s | 普通K均值 | 普通K最大值 | ESKF数量 |
|---|---:|---:|---:|---:|---:|---:|---:|
| 1 | 6,012 | 200.3720 | 222.1826 | 0.356153 | 46.8579 | 314 | 31 |
| 2 | 6,014 | 200.4604 | 208.2840 | 0.334022 | 39.9469 | 293 | 30 |
| 3 | 6,013 | 200.4330 | 201.4455 | 0.323011 | 36.5101 | 264 | 30 |

三段等权均值±样本SD（n=3）：

- PC有效包率：200.4218 ± 0.0453 Hz。
- 平均完整MUL1包长：210.6374 ± 10.5670 B。
- 有效完整包USB流量：0.337729 ± 0.016879 Mbit/s。
- 普通ESKD的K：41.1050 ± 5.2702；逐段中位数18/15/14。
- 总ESKF比例：0.50446%，段间SD为0.00968个百分点。

本例N=1、M=4，普通DELTA的完整MUL1为124+2K B，ESKF为1084 B，采用：

\[\overline L=(1-q)(124+2\overline K_D)+1084q.\]

字节恒等式核对无差异。所有ESKF计入均值和流量；不把ESKF假设成某个观测到的物理K值。相对于同N、相同实际包率的FULL，本批平均完整包字节量减少 **80.57% ± 0.97个百分点**。这不包括USB物理链路额外开销，也不是所有加载动作都成立的固定节省比例。

## 按压、释放与同步事件

包长曲线呈现重复升高、回落的过程，与用户说明的重复加载场景相符。包长反映超过阈值的变化单元数量，不能仅凭峰高判断实际压力，也不能在缺少独立动作标记时，把每个峰严格标成按压或释放。

本批普通K最大值314/293/264，对应普通包峰值752/710/652 B。上一批通过审查的大面积动态记录平均K为76.8350、包长282.4190 B；本批平均K为41.1050、包长210.6374 B。两批带宽差异与K分布不同相符，动作强度、节奏和静息比例没有精确匹配，不能据此判断固件性能改变。两批按加载描述分别报告，不简单合并成六次同条件重复。

三段全程ESKF数为41/40/40，主窗为31/30/30。所有相邻ESKF的桥端时间间隔为997–999 ms，与约每秒一次同步的节奏相符，未出现密集的额外同步簇。第一段主窗31次与约30 s窗口的边界相位相容，不把多出的一次直接定为故障恢复。

协议没有逐帧触发原因字段，因此上述是事件时间的描述；不强行将全部ESKF确认为定时触发，也不能仅凭普通K最大值低于480就证明从未发生K超限回退。

## 时序

| Repeat | 主窗PC最大完成间隔 ms | 主窗桥端最大入队间隔 ms | 桥端首尾包跨度率 Hz |
|---|---:|---:|---:|
| 1 | 18.2242 | 7 | 200.3600 |
| 2 | 46.1612 | 7 | 200.3799 |
| 3 | 19.4200 | 7 | 200.4200 |

外层包序号连续。PC时间受读取批处理和调度影响，host_ms为Teensy构造/入队MUL1时的时间字段；两者都不是直接SPI时钟或物理扫描计数。因此本批支持“观测窗口内未发现协议序号或完整性异常”，不据此宣称绝对不会丢帧或SCK已经实测稳定。

## 文件与复现

- [独立raw审计](raw_audit.md)、[JSON](raw_audit.json)、[审计脚本](raw_audit.py)。
- [统计说明](statistics.md)、[逐窗CSV](statistics.csv)、[输入快照及统计](statistics.json)。
- [时间审查JSON](timing_review.json)、[时间审查脚本](timing_review.py)。
- [加载条件记录](condition_correction.json)。

独立审计前后28个现存记录文件共20,355,183 B的SHA256一致，raw合计4,586,577 B。未移动或分类原始目录，未改原数据、图、索引、GUI、设备固件及论文。此次结果单列为大面积反复按压/释放场景，后续分类可使用派生的实际条件和加载协议。
