Yannas-Sun/E-skin_MSc_final_report/data scalability/analysis/20260907_delta_press_release_review/statistics.md

# 大面积反复按压、释放：三条统计与对照

用户说明实际加载为“大面积反复按压、释放”。三条原metadata仍是zero_load，派生分析标为actual_condition=large_area、actual_load_protocol=repeated_press_release；原文件未修改。实际面积、力、节奏、占空比及层未量化，不补填这些值。

新批为CS槽位M1，N=1、M=4、DELTA、目标200 Hz、阈值8、本地SPI配置10 MHz；三条同一batch、Block 1、Repeat 1/2/3，每条约40 s，主窗从10 s开始约30 s。n=3指同一setup的连续时间窗口，不是独立装配或独立受试板卡。所有窗口都保留。

主统计固定使用约10–40 s，包含该窗内的静息与活动，不按曲线切出较高或较低流量片段。原记录没有加载事件标记，不能精确把某个峰识别为按压或释放。

## 每批、每窗：均值 ± 样本SD（n=3，batch=1）

| 批次 | 窗口 | Hz | Lmean/B | 有效USB/Mbit/s | 普通K均值 | 总q/% | 对FULL等包率节省/% |
|---|---|---:|---:|---:|---:|---:|---:|
| 新批：大面积反复按压、释放 | main | 200.421829 ± 0.045262 | 210.637391 ± 10.566960 | 0.337729 ± 0.016879 | 41.104951 ± 5.270197 | 0.504463 ± 0.009675 | 80.568506 ± 0.974812 |
| 新批：大面积反复按压、释放 | full_run | 200.483039 ± 0.115011 | 190.626021 ± 7.899521 | 0.305733 ± 0.012493 | 31.055305 ± 3.938115 | 0.502933 ± 0.007455 | 82.414574 ± 0.728738 |
| 上一批：大面积动态加载 | main | 200.080364 ± 0.036080 | 282.419048 ± 4.736771 | 0.452052 ± 0.007582 | 76.835022 ± 2.719229 | 0.588591 ± 0.083800 | 73.946582 ± 0.436971 |
| 上一批：大面积动态加载 | full_run | 200.260260 ± 0.055897 | 244.821743 ± 3.369895 | 0.392226 ± 0.005507 | 58.022086 ± 1.959209 | 0.565899 ± 0.062967 | 77.414968 ± 0.310876 |

SD使用三个run统计值、分母n−1；没有把帧数当作独立实验样本数。上一批只使用050453_154588、050533_183636、050613_222506三条，来自冻结统计快照；两批分开，不把Repeat编号当作配对实验。

## 新批逐条普通ESKD分布与完整帧

| Repeat | 窗口 | K均值 | 中位数 | Q1–Q3 | IQR | 普通K最大值 | ESKF / ESKD | q/% |
|---:|---|---:|---:|---:|---:|---:|---:|---:|
| 1 | main | 46.857883 | 18 | 1–81 | 80 | 314 | 31 / 5981 | 0.515635 |
| 1 | full_run | 35.331201 | 5 | 0–53 | 53 | 314 | 41 / 7974 | 0.511541 |
| 2 | main | 39.946858 | 15 | 1–65 | 64 | 293 | 30 / 5984 | 0.498836 |
| 2 | full_run | 30.257612 | 4 | 0–45 | 45 | 293 | 40 / 7981 | 0.498691 |
| 3 | main | 36.510112 | 14 | 2–59.5 | 57.5 | 264 | 30 / 5983 | 0.498919 |
| 3 | full_run | 27.577101 | 4 | 0–38 | 38 | 264 | 40 / 7983 | 0.498567 |

K分布仅来自有效普通ESKD的histogram；分位数使用(n−1)p位置线性插值，IQR=Q3−Q1。JSON另列每批合并帧的描述性分布，不能代替run级SD。ESKF不赋予物理K=480。观察到的普通Kmax低于480也不能排除某ESKF由高K触发，因为该次普通K未在线上传输。

## 实际混合字节与FULL参照

使用完整有效MUL1字节与该窗实际秒数：f=P/t、Lmean=B_valid/P、USB_valid=8B_valid/t。raw到达吞吐单独输出，保留读取块和边界差异。ESKF全部计入实际字节，没有从DELTA吞吐中删去。

M=4、N=1时包装为24+4M=40 B，普通包为124+2K B，ESKF包为1084 B。逐窗核对B_valid=40P+84n_D+2ΣK+1044n_F+诊断字节；q=n_F/(n_F+n_D)。等价Lmean=40+(1−q)(84+2K_D)+1044q（本数据每包一个有效模块且无诊断载荷）。

匹配FULL参照为(24+4M)+1044N=1084 B/包。等实际包率节省=1−Lmean/1084，使用本批实际f不变的反事实FULL字节率；它不是两批实际速率之比，不是新测FULL，也不是USB物理总线总开销。协议未记录ESKF触发原因，因此不将q自动归因于周期或按压。

统计与字节恒等式核验问题：[]。

## 完整性与比较边界

[独立raw审计](raw_audit.json)与本统计计数一致：新主窗18,039个MUL1=17,948 ESKD+91 ESKF；全程24,059=23,938 ESKD+121 ESKF。外内CRC、格式、K、base、目标更新及跨ESKD/ESKF内序号连续性未发现异常，新三条仅主窗标记独立PASS。原全程CHECK REQUIRED保留：有367个初始无锚点ESKD，Repeat 1/2各有1 B尾片，Repeat 3没有尾片。输入summary的SHA与独立审计清单一致，审计前后原文件SHA未改变。

新批相对上一批主窗均长差-71.781657 B（-25.417%），有效USB差-0.114323 Mbit/s，普通K均值差-35.730070。两批都为大面积加载，但反复按压/释放节奏和力没有定量匹配，不能据差值认定算法改进或退化。

最初Large_area批次仅作诊断背景：主窗均长272.234655±11.242027 B，USB0.433820±0.019034 Mbit/s；三条已有内序号事件[1, 11, 2]，保持CHECK REQUIRED，不进入本次通过审计批次的均值，也不被新记录覆盖。

## 复现

statistics_generate.py默认仅读取固定三条新summary及上一轮派生统计快照。--from-snapshot只读取本目录statistics.json；--refresh-raw-audit额外读取同目录派生审计及条件纠正文档。JSON保留输入metadata、scopes和SHA，原data、索引及图未改。

[逐run逐窗CSV](statistics.csv) · [输入及汇总JSON](statistics.json) · [生成脚本](statistics_generate.py)
