Yannas-Sun/E-skin_MSc_final_report/data scalability/analysis/20260907_delta_rolling_review/REVIEW_CN.md

# 新增 rolling 三条记录分析

固定记录：20260907_053858_001637、20260907_053938_027960、20260907_054018_056649，分别于2026-09-07 05:38:58、05:39:38、05:40:18开始。

**三条主窗口均通过独立协议审计，可以用于M1、N=1的rolling结果统计。** 本批没有发现CRC、内外序号、缓存链或目标模块更新异常，也未复现早先大面积记录中跨ESKF的模块序号回退/前跳。本结论限于本次观测窗口。

## 实验条件

用户明确说明新记录为rolling（滚动加载）。原metadata仍写zero_load，分析采用actual_condition=rolling；[condition_correction.json](condition_correction.json)保存用户说明，原summary、日志、图和索引不改写。

三条均为M1通信槽位、N=1、DELTA、目标200 Hz、阈值8、本地SPI设置10 MHz。加载层未指定，没有滚动物尺寸、接触面积、力、速度、路径或逐动作时间标记，不补写这些参数。槽位不等于唯一实体板卡身份；本地配置及文件哈希不是设备回读或SCK实测。

三段属于同一batch的Repeat1/2/3，每段约40 s，统计保持固定10–40 s主窗口。n=3为同一设置下连续时间窗口，batch_n=1，不代表三个独立装配或三个独立板卡。主窗口保留其中的滚动、过渡和静息时间，不挑选活动段。前10 s仅是排除于主统计的记录前段，不假定其始终零载。

## 完整性

独立完整扫描24,051个MUL1及其内帧，核对96,204条逐槽日志。

| 范围 | 有效MUL1 | ESKD | ESKF | 模块内序号不连续 |
|---|---:|---:|---:|---:|
| 全程 | 24,051 | 23,931 | 120 | 0 |
| 前10 s合计 | 6,018 | 5,988 | 30 | 0 |
| 主窗口合计 | 18,033 | 17,943 | 90 | 0 |

内外CRC、布局/K/mask、FULL sentinel、跨全部ESKD与ESKF的模块内序号、外层序号、base链、M1更新，以及raw/CSV/summary对照均无异常。建立基线后未能应用的帧数为0。

全程原CHECK保留：初始无文件内基线的ESKD分别195/182/162个，共539个；R1/R2各有尾部1 B，R3无尾部残片。三条分别在0.9753、0.8918、0.7911 s建立基线，均早于主窗口。R2/R3开始边界经真实前尾/后首拼接验证，R1缺失magic单字节的补足仍单列为推断；跨文件内外序号间距与排除的边界包一致。

## 主窗口统计

| Repeat | 有效包数 | PC包率 Hz | 平均包长 B | 有效USB Mbit/s | 普通K均值 | 普通K最大值 | ESKF数 |
|---|---:|---:|---:|---:|---:|---:|---:|
| 1 | 6,010 | 200.3279 | 344.8403 | 0.552649 | 108.5661 | 245 | 30 |
| 2 | 6,011 | 200.3434 | 364.8870 | 0.584822 | 118.6400 | 250 | 30 |
| 3 | 6,012 | 200.3960 | 363.4278 | 0.582636 | 117.9071 | 254 | 30 |

三段等权均值±样本SD，n=3：

- 有效包率：200.3558 ± 0.0357 Hz。
- 完整MUL1包长：357.7184 ± 11.1766 B。
- 有效完整包USB流量：0.573369 ± 0.017977 Mbit/s。
- 普通ESKD的K：115.0377 ± 5.6166；各段中位数126/134/135，IQR为88/90/83。
- 总ESKF比例：0.499085%，段间SD为0.000083个百分点。

USB流量为有效完整MUL1字节×8/实际窗口时长，不是USB物理链路全部开销。全部ESKF成本保留；N=1、M=4时，单条记录的平均模型为：

\[\overline L=(1-q)(124+2\overline K_D)+1084q.\]

相对于同N、相同实际包率下每包1084 B的FULL，本批完整包字节量减少 **67.00% ± 1.03个百分点**。此比例对应本批记录的加载方式和活动时间分布。

## 与此前动态记录比较

以下三批分别统计，均为主窗口、n=3连续时间重复，不合并成一个n=9结果。

| 用户说明的场景 | 平均包长 B | 有效USB Mbit/s | 普通K均值 |
|---|---:|---:|---:|
| 大面积动态加载（05:04批次） | 282.42 | 0.45205 | 76.84 |
| 大面积反复按压、释放（05:19批次） | 210.64 | 0.33773 | 41.10 |
| Rolling（本批） | 357.72 | 0.57337 | 115.04 |

Rolling的普通K最大值245–254，比前一批按压/释放的264–314低，但其平均K更高，平均流量也更高。曲线显示滚动阶段较长时间存在变化单元；带宽取决于整个窗口内K的分布和ESKF占比，不能只看最高峰。因外部力、速度、接触面积和活动时长未严格量化，这些是不同输入场景的描述性比较，不用于判断固件算法改变或推断压力大小。

这批增加了rolling的三段时间重复证据。它仍只覆盖N=1/M1，不单独验证跨模块数的扩展规律。

## ESKF与时序

全程每条40次ESKF，主窗每条30次；所有相邻ESKF桥端时间间隔为997–999 ms，与约每秒一次同步的节奏相符。日志没有逐帧触发原因字段，因此不将全部事件强制确认成定时触发，也不通过普通K上界反推ESKF的触发原因。

| Repeat | 主窗PC最大完成间隔 ms | 主窗桥端最大入队间隔 ms | 桥端首尾包跨度率 Hz |
|---|---:|---:|---:|
| 1 | 15.9971 | 7 | 200.2933 |
| 2 | 24.6621 | 7 | 200.3600 |
| 3 | 17.7504 | 7 | 200.3867 |

PC时间受读取批处理、调度影响，host_ms为Teensy构造/入队MUL1的时间字段；二者不等同于实际SCK或物理扫描时间。表中间隔与序号检查共同支持本窗口内未发现协议完整性异常，不证明所有未来负载下绝对无丢帧，也不诊断SCK频率稳定性。

## 文件与验证

- [独立raw审计](raw_audit.md)、[机器可读结果](raw_audit.json)、[复现脚本](raw_audit.py)。
- [统计说明](statistics.md)、[逐窗CSV](statistics.csv)、[快照与完整统计](statistics.json)。
- [时序核对](timing_review.json)、[时序脚本](timing_review.py)。
- [实际条件说明](condition_correction.json)。

28个现存记录文件共23,462,282 B在独立审计前后SHA256一致；raw合计7,507,441 B。未移动或分类原始目录，未改原数据、图片、主索引、GUI、设备固件或论文。后续分类应采用用户确认的rolling条件，保留原记录标签作为来源。
