Yannas-Sun/E-skin_MSc_final_report/data scalability/analysis/20260907_delta_rolling_review/statistics.md

# Rolling 三条：统计与前两批对照

用户说明实际条件为rolling。三条原metadata仍为zero_load，派生分析使用actual_condition=rolling；不改原文件，也不把这些记录当作零载。力、接触面积、滚动速度、路径、占空比及加载层未定量记录，不补填。

三条均为CS槽位M1、N=1、M=4、DELTA、目标200 Hz、阈值8、本地SPI配置10 MHz；同一batch、Block 1、Repeat 1/2/3。每条约40 s，固定主窗约10–40 s，包含静息与活动，不按曲线切片。n=3是同一setup内连续时间窗口，不是独立装配、独立板卡或独立加载实验。

## 每批每窗：均值 ± 样本SD（n=3、batch=1）

| 批次 | 窗口 | Hz | Lmean/B | 有效USB/Mbit/s | 普通ESKD K | 总ESKF q/% | 对FULL等包率节省/% |
|---|---|---:|---:|---:|---:|---:|---:|
| 新批：rolling | main | 200.355757 ± 0.035694 | 357.718373 ± 11.176607 | 0.573369 ± 0.017977 | 115.037712 ± 5.616590 | 0.499085 ± 0.000083 | 67.000150 ± 1.031052 |
| 新批：rolling | full_run | 200.416814 ± 0.106551 | 312.114150 ± 22.347766 | 0.500431 ± 0.035989 | 92.121782 ± 11.230616 | 0.498940 ± 0.000271 | 71.207182 ± 2.061602 |
| 前批：大面积反复按压、释放 | main | 200.421829 ± 0.045262 | 210.637391 ± 10.566960 | 0.337729 ± 0.016879 | 41.104951 ± 5.270197 | 0.504463 ± 0.009675 | 80.568506 ± 0.974812 |
| 前批：大面积反复按压、释放 | full_run | 200.483039 ± 0.115011 | 190.626021 ± 7.899521 | 0.305733 ± 0.012493 | 31.055305 ± 3.938115 | 0.502933 ± 0.007455 | 82.414574 ± 0.728738 |
| 前批：大面积动态加载 | main | 200.080364 ± 0.036080 | 282.419048 ± 4.736771 | 0.452052 ± 0.007582 | 76.835022 ± 2.719229 | 0.588591 ± 0.083800 | 73.946582 ± 0.436971 |
| 前批：大面积动态加载 | full_run | 200.260260 ± 0.055897 | 244.821743 ± 3.369895 | 0.392226 ± 0.005507 | 58.022086 ± 1.959209 | 0.565899 ± 0.062967 | 77.414968 ± 0.310876 |

各批单独统计，SD分母n−1。前两批从既有冻结statistics.json获取，均主窗独立PASS；不同批次的Repeat编号不表示配对，不合并为n=9，也不把内帧数当独立重复数。

## 新批逐条

| Repeat | 窗口 | Hz | Lmean/B | USB/Mbit/s | K均值 | 中位数 [Q1,Q3] | IQR | 普通Kmax | ESKF / ESKD | q/% |
|---:|---|---:|---:|---:|---:|---:|---:|---:|---:|---:|
| 1 | main | 200.327872 | 344.840266 | 0.552649 | 108.566054 | 126 [67,155] | 88 | 245 | 30 / 5980 | 0.499168 |
| 1 | full_run | 200.295905 | 292.971043 | 0.469447 | 82.501004 | 93 [1,146] | 145 | 245 | 40 / 7972 | 0.499251 |
| 2 | main | 200.343414 | 364.887040 | 0.584822 | 118.640027 | 134 [75,165] | 90 | 250 | 30 / 5981 | 0.499085 |
| 2 | full_run | 200.457551 | 336.671655 | 0.539907 | 104.462589 | 109 [53,155] | 102 | 250 | 40 / 7979 | 0.498815 |
| 3 | main | 200.395985 | 363.427811 | 0.582636 | 117.907054 | 135 [80,163] | 83 | 254 | 30 / 5982 | 0.499002 |
| 3 | full_run | 200.496987 | 306.699751 | 0.491939 | 89.401754 | 103 [3,153] | 150 | 254 | 40 / 7980 | 0.498753 |

K由有效普通ESKD的histogram重算；分位数在(n−1)p位置线性插值，IQR=Q3−Q1。普通Kmax是ESKD中实际观察到的最大值，ESKF不赋予物理K=480。普通Kmax低于480不能排除某ESKF的高K触发，因为完整帧未携带该次普通变化计数。

## 实际混合字节与FULL参照

f=P/t，Lmean=B_valid/P，有效USB=8B_valid/t；t使用实际窗口时长，B_valid是有效完整MUL1字节。raw到达字节率另列，保留读取块与边界差异。全部ESKF都计入实际吞吐。

M=4、N=1时包装40 B，普通MUL1=124+2K B，ESKF MUL1=1084 B。逐窗核验B_valid=40P+84n_D+2ΣK+1044n_F+诊断字节；q=n_F/(n_F+n_D)。本数据每包一个有效模块且无诊断字节，亦满足Lmean=40+(1−q)(84+2K_D)+1044q。

同M/N的FULL参照为(24+4M)+1044N=1084 B/包；等实际包率节省=1−Lmean/1084，保持本批实际f不变。它是匹配协议字节模型的反事实FULL比较，不是新测FULL或不同批次raw速率比，也不代表USB物理总线全部开销。没有在线触发原因字段，不能把全部ESKF自动归因为周期刷新。

统计与混合字节恒等式问题：[]。

## 独立完整性与解释限制

[独立raw审计](raw_audit.json)与本统计一致：主窗18,033个MUL1=17,943 ESKD+90 ESKF；全程24,051=23,931 ESKD+120 ESKF。外内CRC、格式、K、base、缺模块更新、跨全部ESKD/ESKF内序号以及日志/summary差异均未发现异常，新三条只对主窗标独立PASS。

全程原CHECK REQUIRED保留：初始无锚点ESKD为195/182/162（合计539），尾片1/1/0 B，不能套用其他批次的边界数量。summary SHA与独立审计源文件清单一致，审计前后原文件SHA不变。

- Rolling相对前批：大面积反复按压、释放：主均长差147.080981 B（69.827%），有效USB差0.235640 Mbit/s，普通K均值差73.932760。
- Rolling相对前批：大面积动态加载：主均长差75.299324 B（26.662%），有效USB差0.121317 Mbit/s，普通K均值差38.202690。

这是不同加载方式/批次的描述比较；滚动路径、力和节奏未匹配，不能把差异归因于算法改进、退化或统一噪声变化。加载事件没有同步标记，不精确识别单次滚动接触或释放。

最初Large_area批次仍为诊断背景：主均长272.234655±11.242027 B，三条内序号事件[1, 11, 2]，保留CHECK REQUIRED。该旧批未加入上述通过审计批次的统计，也未被新数据覆盖。

## 复现

statistics_generate.py仅读固定三条新summary及前批派生统计快照；--from-snapshot仅从本目录statistics.json重建，--refresh-raw-audit额外读取同目录派生raw审计与条件说明。JSON冻结原metadata、scopes、源SHA与独立审计。原data、索引和图未改。

[逐run逐窗CSV](statistics.csv) · [输入与全部汇总JSON](statistics.json) · [生成脚本](statistics_generate.py)
