Yannas-Sun/E-skin_MSc_final_report/data scalability/analysis/20260907_delta_zero_review/ANALYSIS_CN.md

# DELTA 零负载 N=1～4：整理与核验总结

**全部15种组合完成，每组合三段，共45条主窗口PASS；本轮零负载主矩阵已齐，无需为补齐组合或重复次数再测。**

每组合三段是同一次设置下的连续时间重复，n=3、batch_n=1；不是三次独立重新接线或装配。
均值 ± SD 使用段间样本标准差，不把数千帧当作独立实验重复。各段统一保留40秒原记录，主分析使用10秒之后的实际约30秒。
PC包率与流量按包完成时间窗口统计，不能直接当作ADC扫描频率或SPI边沿频率。ESKF已计入平均包长和实测流量，不能再重复加算。

## 覆盖与主要结果

| N | 组合数 | 时间段数 n | USB完整包流量 / Mbit/s | 普通 ESKD K | 平均包长 / B | 等帧率USB字节减少 |
|---|---:|---:|---:|---:|---:|---:|
| 1 | 4 | 12 | 0.2326 ± 0.0264 | 8.26 ± 8.29 | 145.24 | 86.60% |
| 2 | 6 | 18 | 0.4039 ± 0.0259 | 8.64 ± 4.11 | 251.98 | 88.16% |
| 3 | 4 | 12 | 0.5776 ± 0.0387 | 9.10 ± 4.05 | 360.74 | 88.63% |
| 4 | 1 | 3 | 0.7625 ± 0.0124 | 10.04 ± 0.72 | 475.15 | 88.73% |

此表在每个N内等权汇总各组合，因每组合都是三段，也等于所有段的等权均值。表中SD为跨该N全部段的样本SD，包含组合差异；每组合的三次段间SD见下表。N=4仅有一种组合。USB减少按同一实际帧率的 `1−L_DELTA/L_FULL` 计算，FULL包长分别1084、2128、3172、4216 B；它将帧率变化与字节压缩收益分开。两种模式分时采集，并非同时配对测量。

## 每组合结果

每行n=3、batch_n=1；保留全部45条，没有按帧率或K筛选。

| N | 组合 | PC包率 / Hz | 平均包长 / B | USB / Mbit/s | 普通 K | 总 ESKF / % | 等帧率USB字节减少 |
|---|---|---:|---:|---:|---:|---:|---:|
| 1 | M0 | 200.124 ± 0.034 | 145.991 ± 1.811 | 0.2337 ± 0.0029 | 8.61 ± 0.92 | 0.505218 ± 0.009543 | 86.53% |
| 1 | M1 | 200.338 ± 0.028 | 130.207 ± 0.030 | 0.2087 ± 0.0001 | 0.71 ± 0.02 | 0.499113 ± 0.000048 | 87.99% |
| 1 | M2 | 200.168 ± 0.079 | 170.636 ± 0.620 | 0.2732 ± 0.0009 | 21.03 ± 0.31 | 0.499556 ± 0.000209 | 84.26% |
| 1 | M3 | 200.001 ± 0.573 | 134.116 ± 0.368 | 0.2146 ± 0.0007 | 2.67 ± 0.18 | 0.499668 ± 0.000946 | 87.63% |
| 2 | M0+M1 | 200.119 ± 0.018 | 233.440 ± 2.375 | 0.3737 ± 0.0038 | 3.98 ± 0.60 | 0.499695 ± 0.000048 | 89.03% |
| 2 | M0+M2 | 200.324 ± 0.481 | 269.002 ± 3.994 | 0.4311 ± 0.0060 | 12.91 ± 1.01 | 0.501880 ± 0.003617 | 87.36% |
| 2 | M0+M3 | 199.856 ± 0.348 | 236.267 ± 2.604 | 0.3778 ± 0.0045 | 4.69 ± 0.66 | 0.500251 ± 0.000796 | 88.90% |
| 2 | M1+M2 | 200.107 ± 0.095 | 265.939 ± 0.383 | 0.4257 ± 0.0008 | 12.15 ± 0.10 | 0.499556 ± 0.000048 | 87.50% |
| 2 | M1+M3 | 201.613 ± 2.071 | 239.454 ± 4.828 | 0.3862 ± 0.0043 | 5.51 ± 1.19 | 0.495985 ± 0.005085 | 88.75% |
| 2 | M2+M3 | 200.216 ± 0.018 | 267.788 ± 0.553 | 0.4289 ± 0.0009 | 12.61 ± 0.14 | 0.499307 ± 0.000127 | 87.42% |
| 3 | M0+M1+M2 | 200.196 ± 0.016 | 389.648 ± 9.040 | 0.6240 ± 0.0145 | 13.95 ± 1.51 | 0.499473 ± 0.000048 | 87.72% |
| 3 | M0+M1+M3 | 200.133 ± 0.055 | 327.993 ± 3.342 | 0.5251 ± 0.0055 | 3.62 ± 0.56 | 0.499639 ± 0.000127 | 89.66% |
| 3 | M0+M2+M3 | 200.109 ± 0.015 | 367.875 ± 4.160 | 0.5889 ± 0.0067 | 10.30 ± 0.70 | 0.499695 ± 0.000048 | 88.40% |
| 3 | M1+M2+M3 | 200.200 ± 0.051 | 357.445 ± 11.992 | 0.5725 ± 0.0191 | 8.54 ± 2.00 | 0.501323 ± 0.003301 | 88.73% |
| 4 | M0+M1+M2+M3 | 200.600 ± 0.845 | 475.148 ± 5.720 | 0.7625 ± 0.0124 | 10.04 ± 0.72 | 0.499833 ± 0.000288 | 88.73% |

## 完整性检查

- 独立解析全程360,824个完整有效MUL1及769,607个有效模块内帧，并逐行核对packet_log、module_log和summary。
- 主窗口270,412个MUL1、576,926次预期模块更新，包含574,042个ESKD和2,884个ESKF；有效更新覆盖率100%。
- 主窗口内外CRC、布局/长度错误、内外序号缺口、重复/倒序、DELTA基线断裂、缺失目标模块更新、诊断载荷、内部未分配字节均未检出；三个阶段分别保留计数。
- 45条full_run仍保持原CHECK REQUIRED。记录从运行中的DELTA流截取，文件起点尚无本文件ESKF基线，累计10,540个初始无锚点ESKD；不是已证实的实时GUI丢帧。96个“记录×活跃模块”的文件基线都在首秒内建立，主窗口前已完成。
- 30条文件末端各有1 B边界碎片；35个跨文件起点包另记账。其中20个用前段真实尾字节核对，15个只补单字节标记的分析属于推断，不视为完整原始证据。边界字节不回填或删改。
- 锚点后未应用更新与由已观测错误导致的FULL恢复事件均为0。本轮没有故障恢复样本，不能由此估计发生故障后的恢复时长或宣称物理扫描绝不丢失。

## ESKF与K：能回答什么

总ESKF比例约0.5%，各段为0.4901%～0.5162%；分母是有效模块内帧而非USB外包。marker不含触发原因，因此不把这些计数全部命名为“周期FULL”，也不把高于0.5%的部分直接判为异常恢复。

普通ESKD的K只由掩码计算；ESKF不伪记为真实K=480。新的N=1/2/3/4普通K均值为8.26、8.64、9.10、10.04。
本轮的跨N变化比历史记录温和，但不能据此证明K为常数或将变化归因于固件。记录跨组合、时间和接线条件，尚无ABBA顺序控制。
同一槽位标签的结果也并不一致：M2的普通K大约21～25，主要来自FSR1；M1多数明显较低。需要区分模块/层差异与模块数量效应。
M0～M3是CS/IRQ槽位，记录没有唯一板卡身份；跨组合物理板一致性仍依赖实际接线约定。逐槽位、逐层结果单独保存。

## 时间戳的限制

PC相邻包完成时间最大间隔为4.0409秒；对应两包序号连续、Teensy host_ms仅差5 ms。
所有主窗口相邻桥端时间戳间隔为3～7 ms。PC存在批量处理和调度停顿，不能称为SPI时钟不稳定。
主窗口PC包率范围199.3419～204.0041 Hz；按同一批包的桥端首尾时间估计约200.0733～200.4065 Hz。
例如最高PC包率记录在约30秒接收窗口中包含源端约30.549秒跨度的数据。这是窗口与缓冲效应，不是扫描频率已升至204 Hz。
本次保留这些记录及其实际接收统计，不事后挑选“更稳定”的窗口。USB流量图与字节模型检验应同时报告Lmean、PC窗口时长及时间戳来源。

## 整理与可追溯性

45个目录已分类为 `DELTA/Zero_load/N=<N>/200Hz/<槽位组合>/Repeat_1..3/`。
270个原文件合计306,090,893 B，搬迁前后SHA256逐文件一致；原run_id、batch_id、Repeat、采集时间、状态及嵌入旧路径均保留。
当前data总索引93条（FULL48＋DELTA45），其中92条主PASS、1条先前FULL失败。
用于主矩阵的90条为FULL45＋DELTA45，30种“模式×组合”配置；原FULL补测选择和失败证据完整保留。
本地固件与记录器哈希一致，属于本地文件来源记录，不是设备Flash读回。原deployment_confirmed字段不补造。
旧固件历史数据仍独立归档；本次没有更新论文PDF或将历史结果改名为新版实测。

## 文件入口

- [整理后的DELTA零载数据](../../data/DELTA/Zero_load/README.md)
- [45条run索引](run_index.csv) / [15组合统计](stats_combinations_pass.csv) / [N汇总](stats_by_n_balanced.csv)
- [匹配FULL比较](stats_full_comparison.csv) / [逐槽位跨N活动量](module_activity_by_slot_n.csv)
- [独立原始流审计](raw_audit_CN.md) / [覆盖与时间戳复核](coverage_review.md) / [详细统计说明](statistical_note.md)
- [270文件路径和哈希](path_map.csv) / [搬迁验证](organization_verification.json) / [总目录验证](catalog_validation.json)

本轮完成的是FULL/DELTA零载主矩阵。DELTA动态负载、独立恢复实验、SPI波形/时序和长时稳定性需分别按相应证据确认，不能由零载PASS代替。
