Yannas-Sun/E-skin_MSc_final_report/data scalability/analysis/20260907_delta_zero_review/raw_audit_CN.md

# DELTA 零载 45 条记录独立原始数据审计

固定快照：20260907_013132_404213 至 20260907_020930_401399，共45条；15个槽位组合，每组合连续三次。

所有统计保留原记录状态，不自动重标。前10秒为初始窗口，主窗口从10秒至实际结束；完整窗口包含两者。边界跨文件包单列，不混入完整包率、K和q。

|窗口|候选MUL1|有效MUL1|有效ESK|ESKF|ESKD|无锚点前缀|锚点后未应用|
|---|---:|---:|---:|---:|---:|---:|---:|
|full_run|360824|360824|769607|3847|765760|10540|0|
|initial|90412|90412|192681|963|191718|10540|0|
|main|270412|270412|576926|2884|574042|0|0|

原始字节/日志独立校验出现问题的run：无。

原summary状态：主窗口{'PASS': 45}；全窗口{'CHECK REQUIRED': 45}。全窗口CHECK的原因保留逐run JSON，不重标为PASS。

35个开始边界包中，20个由前一run实际尾字节拼接验证，15个仅补已知magic单字节M后验证；两者证据等级不同。所有可重建边界均通过CRC。尾部未分配共30B，内部0B。

96个模块/run的首次文件内FULL基线最迟在0.9942713s建立。初始前缀不属于锚点后链断裂，本批锚点后未应用帧和真正FULL恢复事件均为0。

PC完成时间存在批量到达：最大相邻完成间隔4.0408594s，run 20260907_020041_855845，seq 2996399→2996400，elapsed=17.9833607s；对应桥host_ms差仅5ms且内外序号连续。PC窗口帧率不能直接当作硬件瞬时采集频率，也不能据此断言硬件暂停。

|槽位组合|n|主窗口Hz均值±样本SD|平均包B|K_D均值|q_ESKF|
|---|---:|---:|---:|---:|---:|
|M0|3|200.1238 ± 0.0339|145.9908|8.6139|0.0050522|
|M1|3|200.3384 ± 0.0279|130.2066|0.7111|0.0049911|
|M2|3|200.1683 ± 0.0785|170.6365|21.0254|0.0049956|
|M3|3|200.0012 ± 0.5734|134.1158|2.6728|0.0049967|
|M0,M1|3|200.1194 ± 0.0180|233.4398|3.9813|0.0049969|
|M0,M2|3|200.3242 ± 0.4812|269.0017|12.9062|0.0050188|
|M0,M3|3|199.8561 ± 0.3477|236.2665|4.6889|0.0050025|
|M1,M2|3|200.1066 ± 0.0945|265.9385|12.1474|0.0049956|
|M1,M3|3|201.6132 ± 2.0713|239.4545|5.5103|0.0049598|
|M2,M3|3|200.2164 ± 0.0184|267.7885|12.6134|0.0049931|
|M0,M1,M2|3|200.1956 ± 0.0156|389.6481|13.9469|0.0049947|
|M0,M1,M3|3|200.1326 ± 0.0553|327.9933|3.6187|0.0049964|
|M0,M2,M3|3|200.1087 ± 0.0154|367.8746|10.2987|0.0049969|
|M1,M2,M3|3|200.1995 ± 0.0514|357.4449|8.5440|0.0050132|
|M0,M1,M2,M3|3|200.6002 ± 0.8454|475.1478|10.0445|0.0049983|

K_D仅由有效ESKD的64字节mask逐位计数；ESKF不反推K。q=ESKF/(ESKF+ESKD)。组均值按每条run等权，SD为三次时间重复间样本SD；帧内K离散性另存JSON人口SD和分位数。

无锚点前缀表示录制开始时没有记录前置FULL，不能据此声称传输丢帧；只有已建立锚点后的base链破坏才计实际文件内缓存错误。ESKF触发原因未被协议编码，不能仅按marker判断周期/回退/恢复。

本轮 raw SHA256、每个完整候选长度/外CRC、内CRC、掩码popcount、逐槽日志、模块序号与base、主/全窗口summary均有独立核对。边界包实际拼接与单字节推断在JSON中分开。原始到达字节按read块的窗口归属沿用summary，不能由raw单独恢复串口read时间。

复现：`python -B -X utf8 raw_audit.py`。仅按固定organization_plan的旧/新路径及summary.run_id定位，分类搬迁后仍可运行，不扫描后来加入的数据。
