Yannas-Sun/E-skin_MSc_final_report/data scalability/analysis/20260907_delta_zero_review/statistical_note.md

# DELTA 零载45条：主窗口统计与FULL匹配比较

固定读取 organization_plan.json 的45个run_id；每条40 s、前10 s预留，统计使用 scopes.main 的实际约30 s窗口。所有原记录保留，完整性PASS子集另表，不按帧率或K筛选。

15种非空槽位组合各3段、每组合1个batch。均为DELTA、zero_load、目标200 Hz、threshold=8、M=4。三段是同一setup内的时间重复；没有重新搭建的独立重复证明。

主窗口状态：{'PASS': 45}；全程状态：{'CHECK REQUIRED': 45}。全部45条full_run的初始DELTA前缀无法仅从文件建立cache，另30条有尾部1 B；这些全程状态不能改写为PASS。主窗口在10 s之后，所有valid_expected_update覆盖率为1，summary错误计数为0。独立raw验证由同目录其他审计负责。

主窗口共270,412个完整MUL1、576,926个有效内帧，其中ESKD=574,042、ESKF=2,884。

## 每组合：均值 ± 样本SD，n=3，batch=1

| 组合 | Hz | 平均MUL1 / B | USB完整包 / Mbit/s | 普通ESKD K | 总ESKF q / % | 等帧率USB字节减少 / % |
|---|---:|---:|---:|---:|---:|---:|
| M0 | 200.123782 ± 0.033941 | 145.990807 ± 1.810518 | 0.233730 ± 0.002877 | 8.613862 ± 0.919943 | 0.505218 ± 0.009543 | 86.532 |
| M1 | 200.338411 ± 0.027872 | 130.206632 ± 0.029988 | 0.208683 ± 0.000059 | 0.711124 ± 0.015177 | 0.499113 ± 0.000048 | 87.988 |
| M2 | 200.168298 ± 0.078507 | 170.636486 ± 0.619767 | 0.273248 ± 0.000895 | 21.025408 ± 0.310532 | 0.499556 ± 0.000209 | 84.259 |
| M3 | 200.001229 ± 0.573447 | 134.115776 ± 0.367613 | 0.214586 ± 0.000679 | 2.672837 ± 0.182948 | 0.499668 ± 0.000946 | 87.628 |
| M0_M1 | 200.119365 ± 0.018001 | 233.439827 ± 2.375007 | 0.373726 ± 0.003769 | 3.981317 ± 0.596506 | 0.499695 ± 0.000048 | 89.030 |
| M0_M2 | 200.324237 ± 0.481191 | 269.001661 ± 3.993924 | 0.431095 ± 0.005961 | 12.906154 ± 1.011630 | 0.501880 ± 0.003617 | 87.359 |
| M0_M3 | 199.856098 ± 0.347656 | 236.266520 ± 2.603806 | 0.377757 ± 0.004532 | 4.688880 ± 0.656148 | 0.500251 ± 0.000796 | 88.897 |
| M1_M2 | 200.106606 ± 0.094515 | 265.938521 ± 0.382745 | 0.425729 ± 0.000791 | 12.147445 ± 0.095969 | 0.499556 ± 0.000048 | 87.503 |
| M1_M3 | 201.613154 ± 2.071304 | 239.454457 ± 4.828412 | 0.386167 ± 0.004339 | 5.510255 ± 1.190507 | 0.495985 ± 0.005085 | 88.747 |
| M2_M3 | 200.216373 ± 0.018360 | 267.788450 ± 0.553186 | 0.428925 ± 0.000851 | 12.613421 ± 0.139410 | 0.499307 ± 0.000127 | 87.416 |
| M0_M1_M2 | 200.195619 ± 0.015613 | 389.648094 ± 9.039914 | 0.624047 ± 0.014480 | 13.946874 ± 1.514108 | 0.499473 ± 0.000048 | 87.716 |
| M0_M1_M3 | 200.132622 ± 0.055319 | 327.993327 ± 3.341699 | 0.525138 ± 0.005490 | 3.618700 ± 0.560355 | 0.499639 ± 0.000127 | 89.660 |
| M0_M2_M3 | 200.108726 ± 0.015357 | 367.874610 ± 4.159847 | 0.588919 ± 0.006670 | 10.298696 ± 0.696998 | 0.499695 ± 0.000048 | 88.402 |
| M1_M2_M3 | 200.199540 ± 0.051394 | 357.444932 ± 11.991720 | 0.572481 ± 0.019135 | 8.543993 ± 2.000684 | 0.501323 ± 0.003301 | 88.731 |
| M0_M1_M2_M3 | 200.600197 ± 0.845397 | 475.147794 ± 5.719526 | 0.762543 ± 0.012375 | 10.044483 ± 0.717198 | 0.499833 ± 0.000288 | 88.730 |

SD以每段统计值为样本，分母n−1；ESKD K从有效ESKD mask histogram加权重算，与summary均值核对。ESKF没有普通变化计数，不能当成K=480的物理变化；K_effective=(1−q)K_D+480q仅是字节等效值。q分母是有效ESKF+ESKD模块内帧，不是含完整帧的USB包数。

总q逐段范围为0.490116%–0.516236%，接近0.5%的周期参考，但协议没有trigger code，不能把记录中的全部ESKF都归因于周期同步或据间隔推断触发原因。

## 按N平衡描述

对同一N下每种组合先取三段均值，再等权平均组合。下表SD是组合均值之间的样本SD；N=4只有一个组合，因此该SD未定义。CSV另列所有run均值的描述性SD，不能与组合间SD混用。

| N | 组合数 / 时间窗口数 | USB均值 / Mbit/s | 组合间SD | 普通K均值 | 总q均值 / % |
|---:|---:|---:|---:|---:|---:|
| 1 | 4 / 12 | 0.232562 | 0.029155 | 8.255808 | 0.500889 |
| 2 | 6 / 18 | 0.403900 | 0.027389 | 8.641245 | 0.499445 |
| 3 | 4 / 12 | 0.577646 | 0.041085 | 9.102066 | 0.500032 |
| 4 | 1 / 3 | 0.762543 | 未定义 | 10.044483 | 0.499833 |

## 同一CS槽位的活动差异

| 槽位 | N=1 K | N=2 K | N=3 K | N=4 K |
|---|---:|---:|---:|---:|
| M0 | 8.614 | 5.653 | 8.293 | 6.753 |
| M1 | 0.711 | 3.764 | 3.184 | 2.187 |
| M2 | 21.025 | 21.913 | 20.564 | 24.597 |
| M3 | 2.673 | 3.236 | 4.367 | 6.641 |

每个槽位在N=1/2/3/4中分别有3/9/9/3段，来自1/3/3/1个组合批次，均衡平均不改变槽位权重。M2的普通mask活动较高，主要来自FSR1通道；M3在本次按N分组中描述性增加，其他槽位并非一致单调。因此不能由总体K随N的变化推断统一噪声增长机制。CS槽位不是物理板卡UID，采集时间、搭接/装配、负载确认和实体映射未被控制；不能归因于某块板、供电、SPI时钟或模块数本身。

## FULL对照与字节口径

每个DELTA组合匹配 data/primary_matrix.csv 中同组合最新完整FULL批次的三条主窗口，不把两个不同批次的Repeat编号当作成对实验。FULL参考包长来自测量，均符合40+1044N。等实际帧率USB减少=1−L_DELTA/L_FULL；这比较整个MUL1包。去掉共同40 B包装后另算模块载荷减少，两个百分数不混称。

stats_full_comparison.csv另列各批实际raw到达字节率的比值，该比值包含实际包率和读块边界影响。它不是等频率字节减少，也不是USB总线物理带宽占用；没有把FULL组均值的变化传播成配对置信区间。

完整性PASS不保证严格200 Hz或每轮截止时间。保留M1_M3等较高/波动包率和所有较低包率记录；这里不依据统计差异推断时钟故障。原始模块扫描是否全部送达及具体时间停顿原因需额外证据。

## 独立raw审计与时间边界

[独立raw审计](raw_audit_CN.md)核对的主窗口MUL1/ESKD/ESKF总数与本统计一致；交叉校验问题run为[]。全窗口有10,540个录制起点后的无锚点ESKD，全部位于前10 s；主窗口无此前缀。它们解释文件独立重放的初始状态限制，不能直接当作传输丢包。

PC包完成时间受到缓冲和调度影响。独立审计记录的最大间隔如下；对应MUL1序号仍连续，桥端时间相邻仅5 ms。保持原PASS、原时长和原字节率，不自动删除、校正时间戳或推断硬件停顿。

| run_id | PC间隔 / s | 桥端间隔 / ms | 到达序号 |
|---|---:|---:|---:|
| 20260907_020041_855845 | 4.0408594 | 5 | 2996400 |
| 20260907_014545_965962 | 3.7832828 | 5 | 2822430 |
| 20260907_015550_103879 | 3.7370086 | 5 | 2937579 |

因此跨采集批次的raw到达速率差异还可能包含主窗口边界积压影响；等帧率的包长比较减少这类速率差异的混入，但不代表测得物理扫描截止时间。

## 输出与复现

stats_generate.py默认只读固定plan的source/destination位置；完成快照后可用 --from-snapshot 从本目录JSON重建，完全不再访问原记录。输入summary SHA256和FULL索引SHA256保存在 zero_load_stats_summary.json。所有一致性问题会列入JSON；不会据问题自动删除某条记录。

[每条主统计](stats_runs.csv) · [全部组合](stats_combinations.csv) · [PASS组合](stats_combinations_pass.csv) · [平衡N描述](stats_by_n_balanced.csv) · [FULL匹配](stats_full_comparison.csv) · [模块逐次](module_activity_runs.csv) · [同槽位按N](module_activity_by_slot_n.csv) · [机器可读汇总](zero_load_stats_summary.json)
