Yannas-Sun/E-skin_MSc_final_report/data scalability/analysis/20260907_full_completion_review/TIMING_NOTE_CN.md

# FULL 补测与 N=4：六条记录的时间核对

本说明核对本目录 run_index.csv 中的六条完成记录。主窗口状态、时长和字节率来自原 summary，时间分布来自 packet_log.csv，内帧序号来自 module_log.csv；独立 raw CRC 与边界恢复证据另见 ANALYSIS_CN.md。原始文件和状态均不修改。

| 新批次 | 时间重复 n | 主窗口 MUL1 包率 / Hz | USB 完整包数据率 / Mbit/s | 完整包长 / B |
|---|---:|---:|---:|---:|
| M012 补测，BATCH_6b6313d281364eaa891ce82942b3d531 | 3 | 200.084479 ± 0.057550 | 5.077344 ± 0.001460 | 3172 ± 0 |
| N4，BATCH_9fd1ea44282d4e30a57739ebb1856112 | 3 | 200.066062 ± 0.034040 | 6.747828 ± 0.001148 | 4216 ± 0 |

均值与样本 SD 按每段主窗口统计值计算，n 表示同一 setup 内的连续时间重复，不是独立重建次数。每段约 40 s，前 10 s 预留。六条主窗口均 PASS，CRC、序号间断和目标模块缺失错误增量均为零。

## 时间分布

表中六个分箱依次为 PC 完成时间 [10,15)、[15,20)、[20,25)、[25,30)、[30,35)、[35,40) s。本次六条均没有 40 s 后、实际截止前的主窗口完整包。

| run_id | 最大 PC 完成间隔 / ms | 该间隔对应桥端间隔 / ms | 最大桥端间隔 / ms | 六个 5 s 分箱的有效包数 |
|---|---:|---:|---:|---|
| 20260907_004948_668301 | 32.2224 | 5 | 6 | 1002, 1000, 1001, 1001, 1000, 1001 |
| 20260907_005028_724004 | 54.1751 | 5 | 6 | 1000, 999, 1002, 1001, 1001, 1000 |
| 20260907_005108_797842 | 278.7935 | 5 | 6 | 1000, 1001, 1000, 1000, 1001, 1000 |
| 20260907_005250_875035 | 32.0931 | 5 | 6 | 1000, 1001, 1000, 1001, 1000, 1000 |
| 20260907_005330_930696 | 48.7044 | 5 | 6 | 1000, 1000, 999, 1002, 1001, 1000 |
| 20260907_005410_996854 | 18.4781 | 5 | 6 | 1001, 1000, 1000, 1000, 1001, 1001 |

M012 补测 Repeat 3（20260907_005108_797842）在 elapsed_s=38.727428 附近，序号 2264309→2264310 的 PC 完成观察相隔 **278.7935 ms**，桥端 host_ms 仅相隔 **5 ms**。主窗口有 1052 对相邻包共享 PC 时间戳，显示批量接收/处理的影响；序号连续，5 s 分箱保持约 1000 包。该条主包率为 200.024190 Hz，仍保留在整批三次统计中。

六条主窗口均未再次出现旧 M013 Repeat 3 的 123 ms 桥端入队停顿。旧 M013 低率记录依然属于主矩阵，不能因为现在有后续数据而将其剔除；其时间证据见 [原 N3 时间诊断](../20260907_n3_full_review/TIMING_NOTE_CN.md)。

host_ms 是 Teensy enqueueMultiPacket 构造 MUL1 时写入的 millis()，不是 STM32 的物理扫描时间，也不是 USB 总线事务时间。PC elapsed_s 是完成观察时间。可以确认新补测中存在 PC 观察停顿和批量化，同时桥端已记录的相邻入队间隔保持不超过 6 ms；不能据此证明所有物理扫描均已送达，也不能单凭 PC 间隔将责任定位到 USB、操作系统或某个设备。

## 完整性边界

M012 新批次全程状态为 1 PASS、2 CHECK；N4 为 2 PASS、1 CHECK。三条全程 CHECK 都只有文件末尾 1 B 截止片段，位于 004948、005108、005250 三条记录。其余三条尾部为 0 B。四条记录含已知跨开始边界包，005108 与 005410 没有该边界包。所有主窗口 PASS 保持原值；完整包字节率和 raw 块到达字节率不混用。

## 批次选择与可审计性

M012 的原 batch 保留两条 PASS 与一条 CHECK，原 Repeat 目录不移动、不改号。后续完整三次补测 batch 整体用于主矩阵同一组合的位置；选择理由是补齐完整批次，不依据哪条帧率更快。旧两条 PASS 仍具完整性资格，归辅助分析；失败记录持续用于可靠性评估。

主矩阵为 15 种非空槽位组合 × 每组 3 段 = **45 条**。全部原始记录为 **48 条，47 个主窗口 PASS、1 个 CHECK**。M012 全部 PASS 可作为 5 条、2 batches 的辅助诊断，不能标为同一批次或五次独立重建。索引分别保存完整性资格、主矩阵选择、选择理由和 replacement batch，不能用单一 PASS 标志覆盖这些含义。

## 复现

在本目录运行 audit_timing.py，读取固定六条索引与原 CSV/summary，输出 timing_audit.json；支持搬迁前或搬迁后的唯一文件位置。脚本复用上一轮只读时间算法，并在 JSON 中保存算法 SHA256。JSON 还保存每条日志 SHA256、分箱、最大间隔、间隔处序号和模块内帧序号。不会写原始数据。

[本次逐条索引](run_index.csv) · [时间结果 JSON](timing_audit.json) · [复现脚本](audit_timing.py) · [独立 raw 审计](ANALYSIS_CN.md) · [路径与 SHA256 映射](path_map.csv)
