Yannas-Sun/E-skin_MSc_final_report/data scalability/analysis/20260907_n2_large_area_review/raw_audit.md

# N=2 大面积覆盖三条 DELTA 记录：独立原始协议审计

固定记录：20260907_054752_155421、20260907_054832_183609、20260907_054912_204552。原始目录未移动或分类，GUI与原始summary未修改。

实际配置为N=2、目标槽位M1与M3、最大槽位数M=4。记录元数据均为zero_load；用户明确说明实际为“大面积覆盖”。派生分析保留原标签，另记actual_condition=large_area；不改写原始summary，也不推定两模块承受完全相同的加载。

完整扫描23,988个MUL1候选、47,976个有效模块内帧，并逐项核对95,952条模块CSV。共28个原始/记录生成文件前后SHA-256一致：True。

|窗口|候选MUL1|有效MUL1|ESKD|ESKF|初始无锚点ESKD|模块序号不连续|
|---|---:|---:|---:|---:|---:|---:|
|full_run|23988|23988|47680|296|628|0|
|initial|6020|6020|11980|60|628|0|
|main|17968|17968|35700|236|0|0|

|Repeat|原主窗口状态|独立协议结论|主窗K_D|主窗q_ESKF|主窗平均包B|主窗PC包率Hz|
|---|---|---|---:|---:|---:|---:|
|1|PASS|NO DETECTED PROTOCOL ANOMALY|76.176095|0.00676240|523.627651|199.611502|
|2|PASS|NO DETECTED PROTOCOL ANOMALY|71.193296|0.00617799|502.875605|199.605804|
|3|PASS|NO DETECTED PROTOCOL ANOMALY|71.791579|0.00676127|506.206344|199.633995|

每包两模块帧型由raw独立解码。下表顺序为M1/M3，D=ESKD、F=ESKF，计数单位为外层MUL1包；不能将含任意ESKF的包比例当作模块内q。

|Repeat|主窗DD|主窗DF|主窗FD|主窗FF|
|---|---:|---:|---:|---:|
|1|5908|48|33|0|
|2|5915|38|36|0|
|3|5913|43|30|4|

跨ESKD与ESKF统一检查模块sequence，共发现0次不连续。有效ESKF建立新基线不会使本审计跳过sequence检查；此项独立检查覆盖原GUI的检查盲点，原GUI状态保持不变。

## CRC、缓存和文件边界

- 20260907_054752_155421：raw/log/summary差异={}；外CRC坏候选=0；外层序号事件=0；base不连续=0；目标缺更新=0；锚点后未应用=0。
  开始边界=[{"packet_sequence": 581640, "prefix_bytes": 1, "suffix_bytes": 305, "evidence": "inferred_single_magic_byte_not_recorded", "verified": true, "errors": [], "event_errors": [], "previous_run_id": null}]；未分配区=[]。
- 20260907_054832_183609：raw/log/summary差异={}；外CRC坏候选=0；外层序号事件=0；base不连续=0；目标缺更新=0；锚点后未应用=0。
  开始边界=[]；未分配区=[]。
- 20260907_054912_204552：raw/log/summary差异={}；外CRC坏候选=0；外层序号事件=0；base不连续=0；目标缺更新=0；锚点后未应用=0。
  开始边界=[]；未分配区=[{"offset": 3563450, "bytes": 1, "kind": "trailing"}]。

初始未锚定ESKD表示文件尚未包含基线，不证明传输丢帧；开始边界包不混入完整包数、K或q。实际前一文件尾部拼接与仅补magic单字节的推断在JSON中分别标注。

q=全部有效ESKF/(ESKF+ESKD)，K_D仅由普通ESKD两层mask计数。ESKF触发原因没有独立事件字段，不能由ESKF或其出现时刻确诊硬件重启、供电原因或丢失物理扫描。序号跳变仅表明记录中的编号不连续。

PC包完成时间决定初始/主窗口，桥host_ms是桥端时间字段；两者都不是直接SCK波形测量。三次连续录制是同一setup的时间重复。复现：`python -B -X utf8 raw_audit.py`。
