Yannas-Sun/E-skin_MSc_final_report/data scalability/analysis/20260907_n2_large_area_review/REVIEW_CN.md

# N=2 大面积覆盖：M1＋M3 三条记录分析

固定记录为20260907_054752_155421、20260907_054832_183609、20260907_054912_204552，分别于2026-09-07 05:47:52、05:48:32、05:49:12开始。

**三条主窗口均通过独立协议审计，可用于M1＋M3、N=2的大面积覆盖结果统计。每一个完整MUL1包都含两个目标模块的有效更新。** 两模块跨ESKD/ESKF的序号、CRC、缓存链均未发现异常。本结论不推定两个模块承受相同外部加载，也不表示旧故障原因已经查明。

## 条件与窗口

用户确认实际为N=2大面积覆盖，**同时覆盖、加载M1和M3两个模块**。原metadata仍为zero_load；[condition_correction.json](condition_correction.json)记录实际large_area、large_area_coverage及同时加载关系，原summary、日志、图和索引保持不变。同时加载不等于两模块承受相等的力或覆盖面积；这些量未记录。

目标槽位为M1、M3，N=2、最大槽位数M=4、DELTA、目标200 Hz、阈值8、本地SPI配置10 MHz。加载层未指定，未记录精确力、面积及动作时间。槽位不等于唯一实体板卡身份；本地配置/文件哈希不是设备读回或SCK实测。

同一batch连续Repeat1/2/3，每条约40 s，固定主窗10–40 s，不按峰值选择片段。n=3是同一设置的时间重复，batch_n=1，不能作为三个独立装配或三个独立板卡样本。

## 独立完整性检查

完整解析23,988个MUL1和47,976个有效模块内帧，核对95,952条逐槽日志。每个有效外包都包含M1、M3各一个有效内帧。

| 窗口 | 有效MUL1包 | 有效模块内帧 | ESKD内帧 | ESKF内帧 | 模块序号不连续 |
|---|---:|---:|---:|---:|---:|
| 全程 | 23,988 | 47,976 | 47,680 | 296 | 0 |
| 前10 s合计 | 6,020 | 12,040 | 11,980 | 60 | 0 |
| 主窗口合计 | 17,968 | 35,936 | 35,700 | 236 | 0 |

主窗口M1为17,865 ESKD＋103 ESKF，M3为17,835 ESKD＋133 ESKF，各17,968个有效内帧。内外CRC、帧布局/K/mask、FULL sentinel、内外序号、base链、预期更新、raw/CSV/summary对照均无异常；建立基线后未能应用的帧为0。

全程原CHECK保留：初始无文件内基线的ESKD共628个，六个模块×记录均在0.862 s之前建立基线。三条末尾残片为0/0/1 B；仅R1有开始跨界后缀305 B，补缺失magic单字节属于推断。R2/R3起点无需跨文件拼包，跨录制内外序号连续。边界证据分别记录，不套用此前批次的残片数量。

## 主窗口传输结果

| Repeat | 有效包数 | PC包率 Hz | 平均MUL1 B | 有效USB Mbit/s | ESKF内帧 M1/M3 |
|---|---:|---:|---:|---:|---:|
| 1 | 5,989 | 199.6115 | 523.6277 | 0.836177 | 33 / 48 |
| 2 | 5,989 | 199.6058 | 502.8756 | 0.803015 | 36 / 38 |
| 3 | 5,990 | 199.6340 | 506.2063 | 0.808448 | 34 / 47 |

三段等权均值±样本SD（n=3）：包率199.6171 ± 0.0149 Hz，平均包长510.9032 ± 11.1448 B，有效USB流量0.815880 ± 0.017786 Mbit/s。全部ESKF均包含在包长与流量中。

本例固定包装为24+4M=40 B。双模块全FULL为2128 B，全普通DELTA且两个K均为0时为208 B。以相同实际包率的2128 B FULL为参照，平均完整包字节量减少 **75.99% ± 0.52个百分点**。这是协议字节参照，不是新测FULL或USB物理总线总开销。

有效包率约199.62 Hz，略低于目标200 Hz；该观察窗口内内外序号连续，不把与目标的差值直接解释为丢失物理扫描或不稳定SCK。

## 双模块ESKF不能按单模块方式计数

下面按M1/M3顺序，D为ESKD，F为ESKF，单位为外层MUL1包：

| Repeat | DD | DF | FD | FF | 含任一ESKF的包数 |
|---|---:|---:|---:|---:|---:|
| 1 | 5,908 | 48 | 33 | 0 | 81 |
| 2 | 5,915 | 38 | 36 | 0 | 74 |
| 3 | 5,913 | 43 | 30 | 4 | 77 |
| 合计 | 17,736 | 129 | 99 | 4 | 232 |

两个模块多数时候独立发送同步帧，仅4个包同时含两个ESKF。

- 模块内ESKF比例为236/35,936，约0.657%；其分母是模块内帧。
- 含任一ESKF的外包比例为232/17,968，约1.29%；其分母是MUL1包。
- FF为4个包，占比约0.022%；不能把全部含ESKF的包都按2128 B计费。

本批每包两个模块都成功更新，因此逐模块平均模型为：

\[\overline L=40+\sum_{m\in\{1,3\}}\left[(1-q_m)(84+2\overline K_{D,m})+1044q_m\right].\]

q_m是该模块的ESKF比例，K_D,m仅统计该模块普通ESKD。该求和不要求两个模块的ESKF独立或同时发生。逐包类型的长度分别为DD：208+2(K_M1+K_M3)；DF/FD：1168+2K_D；FF：2128 B。实际字节账核对采用每个内帧的类型与K，避免重复或遗漏同步成本。

全部普通ESKD合并后的K均值约73.05，三段SD约2.72；这是按普通内帧汇集的值，不代表两个模块K或外部加载相同。逐模块K与q在统计附件中单列。

逐模块主窗均值±样本SD：M1的K为75.0307±3.4592、ESKF比例为0.57324%（SD0.02552个百分点）；M3的K为71.0738±2.6885、ESKF比例为0.74020%（SD0.09193个百分点）。这两种指标分别描述普通帧分布和同步帧占比，不由其中一个替代另一个。

两个模块在三条记录中均出现过普通K=480，内帧长度为84+2×480=1044 B，与单模块ESKF等长，仍是合法ESKD。这为接近等长边界的双模块传输增加了观测证据；较高的普通包峰值本身不是协议错误。不能据此推断两个模块的K峰值必定在同一时刻，或已测试所有更高活动条件。

## 时序与较密集ESKF

| Repeat | 主窗PC最大完成间隔 ms | 主窗桥端最大入队间隔 ms | M1相邻ESKF间隔范围 ms | M3相邻ESKF间隔范围 ms |
|---|---:|---:|---:|---:|
| 1 | 48.5940 | 7 | 10–1002 | 5–1003 |
| 2 | 17.3086 | 7 | 5–1003 | 5–1005 |
| 3 | 21.9381 | 7 | 5–1002 | 5–1004 |

ESKF间隔范围按每个槽位的全程记录计算。不能把M1和M3交错事件的总时间线误解为任一模块的刷新周期。

本批每个模块都存在接近约1 s的同步间隔，也存在5–10 ms的短间隔。但短间隔处内帧序号、CRC和base链仍正常，没有因出现较密集ESKF就出现可检测的协议错误。协议未传逐帧触发原因，不能直接确认为K超限回退、定时同步或故障恢复；完整帧也不提供该次普通变化计数。

PC时间可能受接收批处理/调度影响，host_ms为Teensy构造/入队MUL1的时间字段，二者均不等于SCK或直接扫描时间。本批桥端最大相邻入队间隔7 ms支持窗口内规律交付的观察，不作为对SPI时钟稳定性的实测结论。

## 结果使用与文件

本批可以补充N=2、M1＋M3同时大面积覆盖加载的主窗口结果。跨N比较还需说明模块组合、实际加载方式以及每模块K，不能因为N=2总包长近似N=1的两倍，就认为同输入、固定K的扩展假设已经验证。原始误选的零载标签不进入零载统计。

- [独立raw审计](raw_audit.md)、[JSON](raw_audit.json)、[脚本](raw_audit.py)。
- [统计说明](statistics.md)、[逐窗CSV](statistics.csv)、[逐模块CSV](statistics.modules.csv)、[快照与统计](statistics.json)。
- [按模块的同步与时序核对](timing_review.json)、[脚本](timing_review.py)。
- [条件说明](condition_correction.json)。

28个现存记录文件共27,165,756 B在独立审计前后哈希一致；raw合计10,796,198 B。未移动/分类原目录，未改原始数据、图片、主索引、GUI、设备固件或论文。
