Yannas-Sun/E-skin_MSc_final_report/data scalability/analysis/20260907_n2_large_area_review/statistics.md

# N2 大面积覆盖：统计与模块/包级ESKF口径

用户确认“同时覆盖、加载两个模块（M1、M3）”。原metadata的zero_load保留；派生actual_condition=large_area、actual_load_protocol=large_area_coverage。两模块同时加载，但各自力、接触面积、节奏及层未量化，不能据此认定等力或等面积。条件依据见[condition_correction.json](condition_correction.json)。

配置为M1+M3、N=2、M=4、DELTA、目标200 Hz、阈值8、本地SPI配置10 MHz。同一batch、Block 1、Repeat 1/2/3；每条约40 s，固定主窗10–40 s，全部保留，不按波峰切片。n=3是同一setup内连续时间窗口，不是独立装配。

## 主窗和全程：均值 ± 样本SD（n=3，batch=1）

| 窗口 | Hz | Lmean/B | 有效USB/Mbit/s | 普通K pooled-inner | 内帧ESKF q/% | 含任一ESKF包/% | 对FULL等包率节省/% |
|---|---:|---:|---:|---:|---:|---:|---:|
| main | 199.617100 ± 0.014906 | 510.903200 ± 11.144828 | 0.815880 ± 0.017786 | 73.053657 ± 2.720607 | 0.656722 ± 0.033708 | 1.291185 ± 0.058649 | 75.991391 ± 0.523723 |
| full_run | 199.879464 ± 0.083032 | 450.057033 ± 11.136328 | 0.719652 ± 0.017507 | 57.910341 ± 2.733397 | 0.616979 ± 0.025403 | 1.217287 ± 0.044405 | 78.850703 ± 0.523324 |

SD分母n−1，以三个run统计值计算。pooled-inner K的单位是一个普通模块ESKD内帧；它不是每个MUL1包两模块变化数之和。模块帧数和包数均不能当作独立实验重复。

## 逐条包统计与异步完整帧

| Repeat | 窗口 | Hz | Lmean/B | USB/Mbit/s | ESKF / ESKD内帧 | DD | DF | FD | FF |
|---:|---|---:|---:|---:|---:|---:|---:|---:|---:|
| 1 | main | 199.611502 | 523.627651 | 0.836177 | 81 / 11897 | 5908 | 48 | 33 | 0 |
| 1 | full_run | 199.783613 | 462.741742 | 0.739586 | 101 / 15883 | 7891 | 58 | 43 | 0 |
| 2 | main | 199.605804 | 502.875605 | 0.803015 | 74 / 11904 | 5915 | 38 | 36 | 0 |
| 2 | full_run | 199.929319 | 441.886722 | 0.706769 | 94 / 15902 | 7904 | 48 | 46 | 0 |
| 3 | main | 199.633995 | 506.206344 | 0.808448 | 81 / 11899 | 5913 | 43 | 30 | 4 |
| 3 | full_run | 199.925460 | 445.542636 | 0.712603 | 101 / 15895 | 7901 | 53 | 40 | 4 |

顺序固定为M1、M3：D=ESKD，F=ESKF。例如DF仅M3发ESKF。q_inner=nF/(nD+nF)；packet_any=(DF+FD+FF)/P；nF=DF+FD+2FF。两模块可异步发ESKF，不假设一次完整刷新同时占据两个模块。

## 逐模块普通ESKD分布

| Repeat | 窗口 | 槽位 | 有效更新数 | 覆盖率 | K均值 | 中位数 [Q1,Q3] | IQR | Kmax | ESKF / ESKD | q_m/% |
|---:|---|---|---:|---:|---:|---:|---:|---:|---:|---:|
| 1 | main | M1 | 5989 | 1.000000 | 78.831598 | 29 [8,78] | 70 | 480 | 33 / 5956 | 0.551010 |
| 1 | main | M3 | 5989 | 1.000000 | 73.513887 | 24 [8,58] | 50 | 480 | 48 / 5941 | 0.801469 |
| 1 | full_run | M1 | 7992 | 1.000000 | 64.073594 | 22 [7,55] | 48 | 480 | 43 / 7949 | 0.538038 |
| 1 | full_run | M3 | 7992 | 1.000000 | 57.996849 | 18 [4,40] | 36 | 480 | 58 / 7934 | 0.725726 |
| 2 | main | M1 | 5989 | 1.000000 | 74.193852 | 21 [8,58] | 50 | 480 | 36 / 5953 | 0.601102 |
| 2 | main | M3 | 5989 | 1.000000 | 68.191732 | 22 [5,59] | 54 | 480 | 38 / 5951 | 0.634497 |
| 2 | full_run | M1 | 7998 | 1.000000 | 58.220070 | 17 [4,39] | 35 | 480 | 46 / 7952 | 0.575144 |
| 2 | full_run | M3 | 7998 | 1.000000 | 53.739245 | 16 [4,40] | 36 | 480 | 48 / 7950 | 0.600150 |
| 3 | main | M1 | 5990 | 1.000000 | 72.066655 | 19 [6,64.25] | 58.25 | 480 | 34 / 5956 | 0.567613 |
| 3 | main | M3 | 5990 | 1.000000 | 71.515901 | 25 [10,68] | 58 | 480 | 47 / 5943 | 0.784641 |
| 3 | full_run | M1 | 7998 | 1.000000 | 56.921800 | 15 [4,39] | 35 | 480 | 44 / 7954 | 0.550138 |
| 3 | full_run | M3 | 7998 | 1.000000 | 56.503841 | 20 [6,45] | 39 | 480 | 57 / 7941 | 0.712678 |

K从各模块histogram重算；分位数采用(n−1)p线性插值，IQR=Q3−Q1。普通K=480仍合法，对应1044 B模块帧；ESKF不伪造物理K。q_m的分母为该模块有效内更新数，两个q_m与包级含F比例不可混称。CSV/JSON另存逐模块均值±SD。

## 实际混合字节

M=4的包装为24+4M=40 B；N=2的FULL完整MUL1为40+2×1044=2128 B；双D且K1=K3=0时为40+2×84=208 B。逐窗核验B_valid=40P+84nD+2ΣK+1044nF+诊断字节。也按各模块核验Lmean=40+Σ_m[(1−q_m)(84+2K_D,m)+1044q_m]。全部ESKF计入实际字节，不能套用N1的1084 B分母。

f=P/t、Lmean=B_valid/P、有效USB=8B_valid/t，t采用实际窗口秒数。raw到达吞吐另列。FULL等实际包率节省=1−Lmean/2128，是同M/N且保持本批f不变的协议字节反事实，不是新测FULL或物理USB总开销。没有ESKF触发原因码，不自动拆成周期/高K/命令。

统计、packet mix和字节恒等式检查问题：[]。

## 独立完整性与参照

[独立raw审计](raw_audit.json)与本统计一致：主窗17,968个MUL1、35,936内更新=35,700 ESKD+236 ESKF；全程23,988个MUL1、47,976内更新=47,680 ESKD+296 ESKF。两个槽位在每个有效包都更新；外内CRC、格式、K、base、跨ESKD/ESKF内序号与日志差异未见异常。仅主窗标独立PASS，原全程CHECK REQUIRED保持。

本批初始无锚点ESKD分别[174, 200, 254]，尾部未归属字节分别[0, 0, 1]；不套用其他批次。summary和packet_log的SHA与独立审计源清单一致。

- N1/M1大面积动态加载主PASS批次：L=282.419048±4.736771 B，USB=0.452052±0.007582 Mbit/s，仅作名义场景对照；不能假定本批两模块各自复现该N1负载或固定K线性扩展。
- N2/M1_M3旧零载批次：L=239.454457±4.828412 B，USB=0.386167±0.004339 Mbit/s，f=201.613154±2.071304 Hz。槽位组合相同但加载条件不同，另批描述不合并。

槽位不是实体板卡UID，各槽位受力、面积及节奏未定量匹配；以上差异不能推断算法退化、某模块噪声或单独的模块数效应。最初N1 Large_area的CHECK记录及内序号事件仍在参照审计中保留，不被后续PASS覆盖。独立raw审计保留当时的条件说明快照，本次用户确认不改写该历史审计。

## 复现

默认固定读取三条新summary和packet_log，以及两份既有派生统计。--from-snapshot仅从statistics.json重建；--refresh-condition仅读同目录条件说明，保留已冻结的历史raw审计；--refresh-raw-audit读取同目录派生raw审计及条件说明。源SHA、metadata、scopes、packet模式计数均冻结。原data、索引及图未修改。

[逐run逐窗CSV](statistics.csv) · [逐模块CSV](statistics.modules.csv) · [全部汇总JSON](statistics.json) · [脚本](statistics_generate.py)
