Yannas-Sun/E-skin_MSc_final_report/data scalability/analysis/20260907_n4_connector_retest_review/raw_audit_CN.md

# DELTA N=4 connector 重装后复测：独立原始数据审计

固定快照：20260907_115145_448767 至 20260907_115305_535263，共3条；M0--M3同时全覆盖动态加载，connector重新安装后连续三次。

所有统计保留原记录状态，不自动重标。前10秒为初始窗口，主窗口从10秒至实际结束；完整窗口包含两者。边界跨文件包单列，不混入完整包率、K和q。

|窗口|候选MUL1|有效MUL1|有效ESK|ESKF|ESKD|无锚点前缀|锚点后未应用|
|---|---:|---:|---:|---:|---:|---:|---:|
|full_run|23968|23968|95872|493|95379|1421|0|
|initial|6020|6020|24080|120|23960|1421|0|
|main|17948|17948|71792|373|71419|0|0|

原始字节/日志独立校验出现问题的run：无。

原summary状态：主窗口{'PASS': 3}；全窗口{'CHECK REQUIRED': 3}。全窗口CHECK的原因保留逐run JSON，不重标为PASS。

3个开始边界包中，2个由前一run实际尾字节拼接验证，1个仅补已知magic单字节M后验证；两者证据等级不同。所有可重建边界均通过CRC。尾部未分配共3B，内部0B。

各槽位首次文件内FULL基线最迟在0.8544744s建立。初始前缀不属于锚点后链断裂，本批锚点后未应用帧和真正FULL恢复事件均为0。

PC完成时间存在批量到达：最大相邻完成间隔0.0185052s，run 20260907_115145_448767，seq 2494062→2494063，elapsed=18.1579428s；对应桥host_ms差仅5ms且内外序号连续。PC窗口帧率不能直接当作硬件瞬时采集频率，也不能据此断言硬件暂停。

|槽位组合|n|主窗口Hz均值±样本SD|平均包B|K_D均值|q_ESKF|
|---|---:|---:|---:|---:|---:|
|M0,M1,M2,M3|3|199.4136 ± 0.0682|1471.5498|135.1519|0.0051956|

K_D仅由有效ESKD的64字节mask逐位计数；ESKF不反推K。q=ESKF/(ESKF+ESKD)。组均值按每条run等权，SD为三次时间重复间样本SD；帧内K离散性另存JSON人口SD和分位数。

无锚点前缀表示录制开始时没有记录前置FULL，不能据此声称传输丢帧；只有已建立锚点后的base链破坏才计实际文件内缓存错误。ESKF触发原因未被协议编码，不能仅按marker判断周期/回退/恢复。

本轮 raw SHA256、每个完整候选长度/外CRC、内CRC、掩码popcount、逐槽日志、模块序号与base、主/全窗口summary均有独立核对。边界包实际拼接与单字节推断在JSON中分开。原始到达字节按read块的窗口归属沿用summary，不能由raw单独恢复串口read时间。

复现：`python -B -X utf8 raw_audit.py`。仅按固定organization_plan的旧/新路径及summary.run_id定位，分类搬迁后仍可运行，不扫描后来加入的数据。
