Yannas-Sun/E-skin_MSc_final_report/data scalability/analysis/20260907_n4_full_coverage_review/raw_audit.md

# N=4 四模块同时全覆盖三条 DELTA 记录：独立原始协议审计

固定记录：20260907_060147_020562、20260907_060227_053987、20260907_060307_083182。原始目录未移动或分类，GUI与原始summary未修改。

实际配置为N=4、目标槽位M0/M1/M2/M3、最大槽位数M=4。记录元数据均为zero_load；用户明确说明“四模块同时全覆盖按下”。派生分析保留原标签，另记actual_condition=large_area及用户说明；不改写原始summary，不推定四模块受力相等。

完整扫描23,725个MUL1候选、94,896个有效模块内帧，并逐项核对94,900条模块CSV。共28个原始/记录生成文件前后SHA-256一致：True。

|窗口|候选MUL1|有效MUL1|ESKD|ESKF|初始无锚点ESKD|模块序号不连续|
|---|---:|---:|---:|---:|---:|---:|
|full_run|23725|23725|94392|504|1308|14|
|initial|6016|6016|23944|120|1308|0|
|main|17709|17709|70448|384|0|14|

|Repeat|原主窗口状态|独立协议结论|主窗K_D|主窗q_ESKF|主窗平均包B|主窗PC包率Hz|
|---|---|---|---:|---:|---:|---:|
|1|PASS|NO DETECTED PROTOCOL ANOMALY|153.777017|0.00506022|1619.422215|199.242989|
|2|CHECK REQUIRED|CHECK REQUIRED|160.553446|0.00546915|1674.125085|195.050159|
|3|CHECK REQUIRED|CHECK REQUIRED|167.399512|0.00574077|1729.552645|195.954634|

每包四模块帧型由raw独立解码，JSON顺序为M0/M1/M2/M3，D=ESKD、F=ESKF、X=槽位无有效更新。下表按一包内有效ESKF个数统计，含X的包独立列出；不能将含任意ESKF的包比例当作模块内q。

|Repeat|主窗0F|主窗1F|主窗2F|主窗3F|主窗4F|有槽位未更新|
|---|---:|---:|---:|---:|---:|---:|
|1|5857|121|0|0|0|0|
|2|5740|97|12|1|1|1|
|3|5757|112|8|1|1|0|

跨ESKD与ESKF统一检查模块sequence，共发现14次不连续。有效ESKF建立新基线不会使本审计跳过sequence检查；此项独立检查覆盖原GUI的检查盲点，原GUI状态保持不变。

## 20260907_060227_053987 的模块序号事件

|elapsed s|前帧→当前帧|后帧|桥host_ms差/ms|PC间隔/ms|窗口|
|---:|---|---|---:|---:|---|
|22.8446298|ESKD 122721 → ESKF 122729|ESKF 122731|614|567.292000|main|
|22.8446298|ESKD 127226 → ESKF 127234|ESKF 127236|614|567.292000|main|
|22.8446298|ESKD 125252 → ESKF 125260|ESKF 125262|614|567.292000|main|
|22.8446298|ESKD 183545 → ESKF 183667|ESKD 183668|614|567.292000|main|
|22.8492335|ESKF 122729 → ESKF 122731|ESKD 122732|5|4.603700|main|
|22.8492335|ESKF 127234 → ESKF 127236|ESKD 127237|5|4.603700|main|
|22.8492335|ESKF 125260 → ESKF 125262|ESKD 125263|5|4.603700|main|

## 20260907_060307_083182 的模块序号事件

|elapsed s|前帧→当前帧|后帧|桥host_ms差/ms|PC间隔/ms|窗口|
|---:|---|---|---:|---:|---|
|16.7725519|ESKD 129412 → ESKF 129420|ESKF 129422|453|417.575800|main|
|16.7725519|ESKD 133917 → ESKF 133925|ESKF 133927|453|417.575800|main|
|16.7725519|ESKD 131943 → ESKF 131951|ESKF 131953|453|417.575800|main|
|16.7725519|ESKD 190349 → ESKF 190441|ESKD 190442|453|417.575800|main|
|16.7747294|ESKF 129420 → ESKF 129422|ESKD 129423|5|2.177500|main|
|16.7747294|ESKF 133925 → ESKF 133927|ESKD 133928|5|2.177500|main|
|16.7747294|ESKF 131951 → ESKF 131953|ESKD 131954|5|2.177500|main|

## CRC、缓存和文件边界

- 20260907_060147_020562：raw/log/summary差异={}；外CRC坏候选=0；外层序号事件=0；base不连续=0；目标缺更新=0；锚点后未应用=0。
  开始边界=[{"packet_sequence": 748310, "prefix_bytes": 1, "suffix_bytes": 975, "evidence": "inferred_single_magic_byte_not_recorded", "verified": true, "errors": [], "event_errors": [], "previous_run_id": null}]；未分配区=[{"offset": 11016021, "bytes": 1, "kind": "trailing"}]。
- 20260907_060227_053987：raw/log/summary差异={}；外CRC坏候选=0；外层序号事件=1；base不连续=0；目标缺更新=4；锚点后未应用=0。
  开始边界=[{"packet_sequence": 756290, "prefix_bytes": 1, "suffix_bytes": 1007, "evidence": "actual_previous_raw_tail", "verified": true, "errors": [], "event_errors": [], "previous_run_id": "20260907_060147_020562"}]；未分配区=[{"offset": 11459767, "bytes": 1, "kind": "trailing"}]。
  外层序号760731→760736，未观测编号4个，elapsed=22.7522755s、raw_offset=5768383、桥host_ms差=522ms。这是记录编号缺口，不能直接等同物理扫描丢失数。
  有效MUL1 seq=760736，elapsed=22.7522755s、raw_offset=5768383，目标槽位[0, 1, 2, 3]未有效更新，status={0: '0x80', 1: '0x80', 2: '0x80', 3: '0x86'}。该包保留，不从计数中删除。
- 20260907_060307_083182：raw/log/summary差异={}；外CRC坏候选=0；外层序号事件=1；base不连续=0；目标缺更新=0；锚点后未应用=0。
  开始边界=[{"packet_sequence": 764155, "prefix_bytes": 1, "suffix_bytes": 669, "evidence": "actual_previous_raw_tail", "verified": true, "errors": [], "event_errors": [], "previous_run_id": "20260907_060227_053987"}]；未分配区=[{"offset": 11926123, "bytes": 1, "kind": "trailing"}]。
  外层序号767419→767424，未观测编号4个，elapsed=16.7725519s、raw_offset=3712149、桥host_ms差=453ms。这是记录编号缺口，不能直接等同物理扫描丢失数。

初始未锚定ESKD表示文件尚未包含基线，不证明传输丢帧；开始边界包不混入完整包数、K或q。实际前一文件尾部拼接与仅补magic单字节的推断在JSON中分别标注。

本批模块序号事件均在有效ESKF上前跳，ESKF当时即提供完整基线；下一批观察到的ESKD的base与前一个有效模块帧匹配，锚点后未应用ESKD为0。这并不填补序号缺口：未录到的数据、异常真正开始时刻及触发原因仍未知。JSON逐事件保留首个后续ESKD及其PC/桥端时间，不能将这段观察间隔称为物理故障恢复延迟。

q=全部有效ESKF/(ESKF+ESKD)，K_D仅由普通ESKD两层mask计数。ESKF触发原因没有独立事件字段，不能由ESKF或其出现时刻确诊硬件重启、供电原因或丢失物理扫描。序号跳变仅表明记录中的编号不连续。

PC包完成时间决定初始/主窗口，桥host_ms是桥端时间字段；两者都不是直接SCK波形测量。三次连续录制是同一setup的时间重复。复现：`python -B -X utf8 raw_audit.py`。
