Yannas-Sun/E-skin_MSc_final_report/data scalability/analysis/20260907_n4_full_coverage_review/REVIEW_CN.md

# N=4 同时全覆盖：最终检查结论

## 一段通过，两段有记录缺口

用户确认M0、M1、M2、M3同时全覆盖按下，模式仍是DELTA。三段各40 s，主分析窗口固定为10–40 s。原文件中zero_load标签保留为来源，派生条件改记large_area / full_coverage_all_modules。没有按错误时段或帧率剪裁记录。

| Repeat | 独立主窗 | 包率 / Hz | 平均包长 / B | 有效USB / Mbit/s | 外层缺号 | 内序号事件 | 已收到包内缺模块更新 |
|---:|---|---:|---:|---:|---:|---:|---:|
| 1 | PASS | 199.243 | 1619.42 | 2.581268 | 0 | 0 | 0 |
| 2 | CHECK REQUIRED | 195.050 | 1674.13 | 2.612307 | 4 | 7 | 4 |
| 3 | CHECK REQUIRED | 195.955 | 1729.55 | 2.711311 | 4 | 7 | 0 |

R2在22.7522755 s出现760731→760736的外层缺号，桥端相邻包间隔522 ms；该760736包为40 B，CRC有效，但四槽均没有有效更新。22.8446298 s四槽有效ESKF到达；其模块内序号前跳，之后M0～M2又各发生一次前跳。R3在16.7725519 s出现767419→767424、桥端453 ms间隔和四槽ESKF前跳，之后M0～M2再次前跳。两段各7次内序号事件，共14次；外层共有8个未观测编号。

全部已解析候选的内外CRC、布局、K和base链检查正常；有效ESKF后建立了基线，随后收到的ESKD可应用，锚点后未应用ESKD为0。**这些事实不能填补未观测编号，不能说“只因PC缓冲、系统没有丢帧”，也不能确定是ESKF、高K或SCK导致。** 外层与模块内的编号缺口分别报告，不能直接相加为物理扫描丢失数。

三段全部保留的诊断均值±样本SD：包率196.749261±2.206474 Hz，包长1674.366648±55.065612 B，有效USB 2.634962±0.067917 Mbit/s，普通内帧K=160.576658±6.811278，ESKF内帧比例0.542338%±0.034258个百分点。相同已观测包率下，相对4216 B FULL的字节减少约60.29%；因为该组含缺号和空更新包，此数值不能当作无损压缩性能结论。

只有R1主窗口独立通过，n=1无法计算段间SD。R1仍可作为明确标注的单段实例；整个N4批次作为诊断资料保留，不加入完整三次通过的动态性能子集。全程的初始1308个无锚点ESKD和尾片1/1/1 B与主窗内部事件分开记录。

[N4独立审计](../20260907_n4_full_coverage_review/raw_audit.md) / [逐模块统计及字节模型](../20260907_n4_full_coverage_review/statistics.md)。

记录已分类至data/DELTA/Dynamic_load/N=4/200Hz/M0_M1_M2_M3/Full_coverage_all_modules/Repeat_1～3；原审计文件内时间戳路径为分类前来源。

[全部实验最终总结](../20260907_final_data_review/FINAL_SUMMARY_CN.md)。
