Yannas-Sun/E-skin_MSc_final_report/data scalability/analysis/20260907_n4_full_coverage_review/statistics.md

# N4 同时全覆盖按下：完整统计与异常保留

用户确认所有四个模块同时全覆盖按下。派生条件为large_area / full_coverage_all_modules，原metadata的zero_load不改；固件实际模式为DELTA。每模块力、接触面积、加载层及节奏未量化，不推断四模块等力或等面积。条件说明见[condition_correction.json](condition_correction.json)。

配置M0/M1/M2/M3、N=4、M=4、目标200 Hz、阈值8、本地SPI配置10 MHz。三条同一batch，Repeat 1/2/3是连续40 s时间窗口；主窗固定10–40 s，全部保留。没有将数千内帧视为独立实验，没有切除异常段或以速度选择记录。

## 全部三窗口描述：均值 ± 样本SD（包含CHECK）

| 窗口 | Hz | Lmean/B | 有效USB/Mbit/s | 普通K pooled-inner | 内帧q/% | 含任一ESKF包/% | 对FULL观察字节减少/% |
|---|---:|---:|---:|---:|---:|---:|---:|
| main | 196.749261 ± 2.206474 | 1674.366648 ± 55.065612 | 2.634962 ± 0.067917 | 160.576658 ± 6.811278 | 0.542338 ± 0.034258 | 1.998686 ± 0.091870 | 60.285421 ± 1.306110 |
| full_run | 197.695224 ± 1.560516 | 1450.197708 ± 66.196450 | 2.293133 ± 0.091094 | 132.437310 ± 8.231232 | 0.531216 ± 0.025318 | 1.997730 ± 0.068808 | 65.602521 ± 1.570125 |

以上n=3、batch=1是包含失败窗口的描述统计，不能作为三次全部通过的性能证明。SD使用run统计值、分母n−1。pooled-inner K是一个普通模块内帧的变化数，不是四个模块每包K之和。

## 逐条结果与完整性

| Repeat | 窗口 | Hz | Lmean/B | USB/Mbit/s | 原summary | 独立raw | 外层缺号 | 已收到包内缺更新 |
|---:|---|---:|---:|---:|---|---|---:|---:|
| 1 | main | 199.242989 | 1619.422215 | 2.581268 | PASS | PASS | 0 | 0 |
| 1 | full_run | 199.457222 | 1380.504575 | 2.202813 | CHECK REQUIRED | CHECK REQUIRED | 0 | 0 |
| 2 | main | 195.050159 | 1674.125085 | 2.612307 | CHECK REQUIRED | CHECK REQUIRED | 4 | 4 |
| 2 | full_run | 196.487528 | 1457.857506 | 2.291607 | CHECK REQUIRED | CHECK REQUIRED | 4 | 4 |
| 3 | main | 195.954634 | 1729.552645 | 2.711311 | CHECK REQUIRED | CHECK REQUIRED | 4 | 0 |
| 3 | full_run | 197.140921 | 1512.231042 | 2.384981 | CHECK REQUIRED | CHECK REQUIRED | 4 | 0 |

R2主窗有一个40 B状态包，四个模块都没有有效内更新，不能当成正常的DDDD/K=0包。R2、R3各缺4个外层序号，真实含义不能直接等同物理扫描损失数。已收到包内缺更新与外层缺号分别保留，不凭空补帧或补字节。

## 独立PASS子集（另列，原三条不删除）

| 窗口 | PASS窗口n | batch n | Hz | Lmean/B | USB/Mbit/s | run间SD |
|---|---:|---:|---:|---:|---:|---|
| main | 1 | 1 | 199.242989 | 1619.422215 | 2.581268 | 未定义（n<2） |
| full_run | 0 | 0 | 未定义 | 未定义 | 未定义 | 未定义（n<2） |

当前主窗仅R1独立通过，n=1的SD未定义；全程没有独立PASS窗口。R2/R3各有7次跨ESKF内序号前跳与一次外层缺号，仍保留CHECK，不能称三个重复通过。

## 每包0–4个ESKF

| Repeat | 窗口 | 0F | 1F | 2F | 3F | 4F | 全DDDD | 含无更新槽包 | ESKF / ESKD内帧 |
|---:|---|---:|---:|---:|---:|---:|---:|---:|---:|
| 1 | main | 5857 | 121 | 0 | 0 | 0 | 5857 | 0 | 121 / 23791 |
| 1 | full_run | 7818 | 161 | 0 | 0 | 0 | 7818 | 0 | 161 / 31755 |
| 2 | main | 5741 | 97 | 12 | 1 | 1 | 5740 | 1 | 128 / 23276 |
| 2 | full_run | 7709 | 137 | 12 | 1 | 1 | 7708 | 1 | 168 / 31268 |
| 3 | main | 5757 | 112 | 8 | 1 | 1 | 5757 | 0 | 135 / 23381 |
| 3 | full_run | 7724 | 152 | 8 | 1 | 1 | 7724 | 0 | 175 / 31369 |

模式顺序M0/M1/M2/M3；D=ESKD，F=ESKF，X=无有效内更新。0F包含可能的XXXX状态包，故与DDDD分开。完整16种D/F模式及异常模式在JSON/CSV保留。packet_any=(1F+2F+3F+4F)/P；q_inner=nF/(nD+nF)，nF=Σ_k k×包数(kF)。不能把两种比例混为一谈，不能假设四模块同步发完整帧。

## 逐模块ESKD与更新覆盖

| Repeat | 窗口 | 槽位 | 有效更新 | 覆盖率 | K均值 | 中位数 [Q1,Q3] | IQR | Kmax | ESKF / ESKD | q_m/% |
|---:|---|---|---:|---:|---:|---:|---:|---:|---:|---:|
| 1 | main | M0 | 5978 | 1.00000000 | 137.277068 | 113 [89,162] | 73 | 379 | 30 / 5948 | 0.501840 |
| 1 | main | M1 | 5978 | 1.00000000 | 155.071465 | 103 [59,217] | 158 | 480 | 31 / 5947 | 0.518568 |
| 1 | main | M2 | 5978 | 1.00000000 | 171.304640 | 149 [106,221] | 115 | 411 | 30 / 5948 | 0.501840 |
| 1 | main | M3 | 5978 | 1.00000000 | 151.455111 | 115 [70,204] | 134 | 471 | 30 / 5948 | 0.501840 |
| 1 | full_run | M0 | 7979 | 1.00000000 | 108.275224 | 97 [39,141] | 102 | 379 | 40 / 7939 | 0.501316 |
| 1 | full_run | M1 | 7979 | 1.00000000 | 122.838876 | 72 [38,172] | 134 | 480 | 41 / 7938 | 0.513849 |
| 1 | full_run | M2 | 7979 | 1.00000000 | 139.277491 | 121 [64,190] | 126 | 411 | 40 / 7939 | 0.501316 |
| 1 | full_run | M3 | 7979 | 1.00000000 | 124.672503 | 89 [46,161] | 115 | 471 | 40 / 7939 | 0.501316 |
| 2 | main | M0 | 5851 | 0.99982912 | 139.390961 | 113 [88,161] | 73 | 392 | 32 / 5819 | 0.546915 |
| 2 | main | M1 | 5851 | 0.99982912 | 162.879642 | 120 [83,224] | 141 | 480 | 35 / 5816 | 0.598188 |
| 2 | main | M2 | 5851 | 0.99982912 | 169.231787 | 141 [87,238] | 151 | 440 | 31 / 5820 | 0.529824 |
| 2 | main | M3 | 5851 | 0.99982912 | 170.707610 | 122 [75,254] | 179 | 478 | 30 / 5821 | 0.512733 |
| 2 | full_run | M0 | 7859 | 0.99987277 | 119.065370 | 99 [62,135] | 73 | 392 | 42 / 7817 | 0.534419 |
| 2 | full_run | M1 | 7859 | 0.99987277 | 132.217430 | 96 [47,163.75] | 116.75 | 480 | 45 / 7814 | 0.572592 |
| 2 | full_run | M2 | 7859 | 0.99987277 | 139.562164 | 103 [58,199] | 141 | 440 | 41 / 7818 | 0.521695 |
| 2 | full_run | M3 | 7859 | 0.99987277 | 142.761223 | 94 [59,195.5] | 136.5 | 478 | 40 / 7819 | 0.508971 |
| 3 | main | M0 | 5879 | 1.00000000 | 140.614845 | 115 [82,169] | 87 | 398 | 32 / 5847 | 0.544310 |
| 3 | main | M1 | 5879 | 1.00000000 | 152.683967 | 102 [56,234] | 178 | 480 | 41 / 5838 | 0.697398 |
| 3 | main | M2 | 5879 | 1.00000000 | 197.839405 | 167 [113,286] | 173 | 448 | 32 / 5847 | 0.544310 |
| 3 | main | M3 | 5879 | 1.00000000 | 178.433407 | 136 [92,257] | 165 | 478 | 30 / 5849 | 0.510291 |
| 3 | full_run | M0 | 7886 | 1.00000000 | 121.759179 | 97 [64,145] | 81 | 398 | 42 / 7844 | 0.532589 |
| 3 | full_run | M1 | 7886 | 1.00000000 | 126.752265 | 78 [45,167] | 122 | 480 | 51 / 7835 | 0.646716 |
| 3 | full_run | M2 | 7886 | 1.00000000 | 163.335671 | 128 [69,242] | 173 | 448 | 42 / 7844 | 0.532589 |
| 3 | full_run | M3 | 7886 | 1.00000000 | 148.709024 | 107 [67,213] | 146 | 478 | 40 / 7846 | 0.507228 |

K从各slot有效ESKD histogram重算；分位数为(n−1)p线性插值，IQR=Q3−Q1。ESKF不赋予物理K=480。覆盖率c_m=已收到有效内更新数/P，只描述已收到有效外包的更新完整度，不能证明每次预期扫描都已传到PC。

## 准确字节账

包装24+4M=40 B；四模块FULL完整MUL1=40+4×1044=4216 B；四模块全D且各K=0为40+4×84=376 B。实际有效外包字节B_valid=40P+84nD+2ΣK+1044nF+诊断载荷字节，全部ESKF及40 B状态包均保留。

存在缺更新时必须带覆盖率：Lmean=40+Σ_m c_m[(1−q_m)(84+2K_D,m)+1044q_m]+诊断字节/P。R2的c_m<1，不能套用每包四个完整内更新的简化均值。f=P/t、有效USB=8B_valid/t，另存全模块更新包率和raw到达字节率。

1−Lmean/4216仅表示保持实际收到包率不变时相对FULL模型的观察字节减少。失败窗口缺帧、缺更新也影响观察流量，不能把它解释为可靠压缩收益或修复后的性能。没有补足丢失包的字节，更没有将低帧率筛掉。ESKF线上无触发原因码，不据短间隔诊断原因。

统计/日志/混合字节恒等式检查问题：[]。这只表示计算一致，绝不表示协议完整性没有异常。

[独立raw审计](raw_audit.json)及[资格判定](qualification.json)已附入并核对SHA，逐窗风险在JSON的independent_review_reasons保留。逐slot全部K histogram、有效更新数和每包D/F/X模式均与独立raw一致。原全程初始无锚点与尾部边界CHECK也保持；异常不会因CRC通过或统计一致而消失。

## 复现

默认固定读取三条新summary、packet_log和本目录条件说明。--from-snapshot只读statistics.json；--refresh-raw-audit仅读同目录派生raw审计，按事件保留CHECK。原metadata、scopes、日志模式及SHA均冻结；源data与索引未改。

[逐run逐窗CSV](statistics.csv) · [逐模块CSV](statistics.modules.csv) · [全部汇总JSON](statistics.json) · [脚本](statistics_generate.py)
