Yannas-Sun/E-skin_MSc_final_report/data scalability/analysis/20260907_delta_zero_review/before_documents/PLAN_CN.md

# 新版固件 Data 实验安排（半天）

2026-09-06。状态：计划，尚未执行。用户确认半天以内，逻辑分析仪、示波器、电流测量设备齐全。**本轮只重做 Data，Power 和 Calibration 不安排重测。**

**当前 GUI 操作已按用户要求改为三连录（2026-09-06）：** 每点一次 Record x3，在同一配置下自动产生 Repeat 1、2、3，默认每段40 s、每段前缀10 s，合计约120 s；Block不自动递增，三段共享batch_id。先做FULL零载时，15种组合各点一次即可得到45段，无需再把每个组合手动录三遍。下文142行CSV保留为原“每行一次、三个区组”的设计清单，不能把当前三连录直接当作完成三个独立区组；若逐行各点一次会增加到三倍记录数。新数据分析应区分同一装配下的连续时间窗口与重新建立条件的独立重复，按batch_id保留关联。

目标：N=1–4 的数据实测图表统一使用配套 four-module-variable-spi 固件，同时补齐重复性、SPI时序、FULL/DELTA比较、完整同步帧及更新完整性。N>4、40 MHz、理想容量交点仍为理论预测。

## 1. 当前选定的半天方案

现场使用 halfday_schedule.csv；每行都是 PLANNED_NOT_RUN，采集后回填实际 run_id。

| 项目 | 条件 | 记录数 |
|---|---|---:|
| 零载 | 全部15种模块组合×FULL/DELTA×3区组 | 90 |
| 动态 | 7条件×FULL/DELTA×3次重新加载 | 42 |
| K排查 | 固定M0，ABBA及BAAB各一组 | 8 |
| 连续运行 | N4 DELTA零载/动态，各5分钟 | 2 |
| 合计 | 140个短记录、2个长记录 | 142 |

短记录40 s，前10 s建立基线/稳定，后30 s分析；长记录310 s，后300 s分析。分析窗口总80 min，原始录制约103.7 min，装夹、接线、预热和检查另计。主数据132段是第一优先级；时间不足时顺延K/长时扩展，不把未完成重复写成已经完成。

## 2. 正式采集前的记录工具与试录制

- 固定STM32、Teensy配套固件及PC记录器SHA256，固定物理模块与CS/IRQ映射。统一200 Hz、10 MHz、阈值8、持续USB接收，记录接线、预热、环境与加载规程。
- 2026-09-06 GUI已接入本CSV计划，并将Settings简化为人工实验条件选项。手动录制自动识别近期正常通信槽位和实际模式，Record时锁定清单；计划录制仍保留CSV预期模块，用自动检测核对。目标扫描率/本地固件配置自动记录来源，实际包率另测，不能把配置值当设备读回。
- 打开Settings时暂停热力图刷新，接收和录制继续；Save或关闭后恢复最新画面。当前先做FULL零载时，可用手动设置选择zero_load和轮次，等待模块识别后Record；Next仍按混合计划发送模式/频率，勿用来代替手动FULL零载的下一次记录。板卡唯一身份未随协议传输，物理标签与槽位映射用人工约定/备注保留。
- GUI已支持可配置时长，短记录默认40 s、前缀10 s，长记录310 s、前缀10 s。保留全部前缀，每模块从文件首个有效ESKF建立基线，分别保存full_run和main统计；短记录分析预先规定的后30 s，不按结果挑稳定片段。
- dump_usb_stream虽支持时长参数，但逐包打印且元数据、缓存检查不足，不直接当作已验证的正式性能记录器。采集时避免高频控制台输出干扰接收。
- 先试录N4 FULL、DELTA各一段，核对raw、条件、时间窗、实际模式、K/q、状态和解析。试录标PILOT，预先决定是否纳入。出错先定位，冻结修正版后开始正式区组；异常run保留。
- 历史数据已归档到 data scalability/history/pre_variable_spi_20260906/data；新记录保存到活动data目录。绘图入口已支持--data-root，历史复现显式指定归档；正式新版图表的run选择/manifest仍须在采集后按新数据更新。PLAN编号不是实际run_id，必须回填真实时间和路径。

## 3. SPI波形验证

记录SCK、CS/NSS、MISO、IRQ，必要时加MOSI；保存仪器采样率、窗口和触发条件。

| 检查 | 预期/输出 |
|---|---|
| FULL | 1044 B，8352个SCK |
| 普通ESKD | L=84+2K，时钟数8L |
| K=27示例 | 138 B，1104个SCK；实测以实际K为准 |
| 头/体读取 | 16 B头与剩余L−16 B之间CS始终低；测软件停顿 |
| 长短交替 | 短DELTA→完整ESKF→DELTA正常，无错位 |
| N1–4 | 在各N的FULL/DELTA保存波形，测CS时长、IRQ等待和轮次间隔 |

先测单模块，再随主矩阵采集各N波形。SPI利用率如果称“实测”，各N/模式必须有实际时钟/CS记录及窗口、重复数。只用USB内帧求和，应标“由新版实测内帧推算的SPI字节需求”。失败SPI事务的全部时钟不能仅由USB保留的16 B诊断头恢复。

CS时间包含停顿，不能用8L/10 MHz代替实际时长。零载不等于K=0；不要为了构造K=480/481无限加力。精确K边界是受控输入/测试固件任务，单列版本，不要求半天完成。

## 4. 零载矩阵：90段

| N | 物理模块组合 | FULL段数 | DELTA段数 |
|---|---|---:|---:|
| 1 | M0、M1、M2、M3 | 12 | 12 |
| 2 | M0M1、M0M2、M0M3、M1M2、M1M3、M2M3 | 18 | 18 |
| 3 | M0M1M2、M0M1M3、M0M2M3、M1M2M3 | 12 | 12 |
| 4 | M0M1M2M3 | 3 | 3 |
| 合计 | 15组合×2模式×3区组 | 45 | 45 |

每区组全部15组合，每组合FULL/DELTA相邻，模式先后平衡。CSV固定种子20260906，并把同接线组合的零载、动态集中，减少换线。三个区组重新建立条件，记录实际偏离；不要先做全部FULL再做全部DELTA。

主图先在每区组内等权平均同N各组合，再对三个区组均值计算均值±SD，标n_blocks=3，并保留组合数、run数及逐模块结果。六种双模块组合不是同一条件六次重复，帧数不是独立样本数。三个区组是务实的小规模重复设计，不是已完成统计功效论证。

## 5. 动态矩阵：42段

每行FULL/DELTA各3次，共6段。每次重新执行加载。

| 条件 | 模块 | 段数 |
|---|---|---:|
| 原小面积按压3×1.6 cm | M1 | 6 |
| 原大面积按压 | M1 | 6 |
| 原rolling，固定路径/节奏 | M1 | 6 |
| 标准全区域动态N1 | M1 | 6 |
| 标准全区域动态N2 | M1、M3 | 6 |
| 标准全区域动态N3 | M0、M1、M3 | 6 |
| 标准全区域动态N4 | 四模块 | 6 |

先固定施力幅度/参考质量、面积、垫片、位置、加载层、节奏和占空比。rolling固定路径/往返次数。手动加载记录其不确定性，FULL/DELTA使用同样规程并平衡先后、规定卸载恢复时间；不是完全相同ADC输入的逐字节比较。

标准N1–4保持每模块相同活动条件，不把同一总力分给更多模块。静态重物不等于高K。无法同时控制所有模块/层时写明实际对象，不宣称全覆盖。这条动态曲线标“所选嵌套组合”，不能声称完全消除模块身份影响。

大面积条件只有确实与标准N1相同时才合并；届时动态36段、主数据126段，当前CSV保守保留两者。全组合动态增强方案会使主数据增加到198段，不列半天要求。

## 6. K随N：8段初步配对

A=M0单独工作；B=四模块工作。固定M0的FSR、装配、接线和零载状态，只比较M0。做ABBA及BAAB各一组，合计2区组8段，每段后30 s分析，比较区组内ΔK=mean(K_B)−mean(K_A)及返回A后是否恢复。

若重现趋势，用示波器检查目标模块电源/参考/地线扰动，用逻辑分析仪检查扫描周期、IRQ等待和SPI相位；这是Data机制排查，不是重做Power scalability。一次改变一个因素。FULL原始矩阵可补充看漂移/差分，但总线活动不同，不是完全相同电气条件。

不先调高阈值掩盖趋势；当前也没有运行时阈值命令。停止轮询会改变STM32等待DMA行为，不能假设未轮询模块仍以原频率扫描。如果K依赖N，报告保留依赖，固定K外推是条件预测。扩展版才是4区组16段；半天不标n=4。

## 7. 完整性、同步和恢复

全部132段主记录都检查完整性。N4 DELTA零载/动态另各记录310 s，后300 s分析；每条件长运行n=1，不写成三次长时重复。正常长记录不主动插入故障。

另用独立事件日志记录FULL↔DELTA、RESYNC DELTA，时间允许各10次，观察每模块完整基线及随后DELTA链。若要保留异常恢复结论，再做有时标的单模块复位/PC暂停接收，建议各3次；时间不足就保留为未验证，不能从正常运行推断恢复时间。

记录命令/故障起止、涉及模块、首个有效ESKF和随后有效ESKD。准确测所有物理扫描损失还需生成/排队/丢弃计数或独立硬件观测；USB日志不足以证明。PC暂停期间自身记录器不能观察未接收的数据，恢复起点需独立标记。

9月5日5个有效USB包缺6次模块更新，不等于6次物理扫描丢失。按窗口核验status、未更新、诊断字节、CRC、序号/base链。启动、稳态、受控异常分开；首个ESKF前无基线前缀单列。连续MUL1序号不能证明所有扫描送达，约199 Hz包率不能证明10 MHz SCK不稳定。零错误只报告该条件/时长内未观察到错误。

## 8. 每段输出与模型修订

| 类别 | 输出 |
|---|---|
| 来源 | run_id、日期/时区、两端固件/PC哈希、区组、物理模块/槽位、模式、阈值、负载、时间窗 |
| 字节/速率 | raw字节/T、有效包字节/包数、USB包率、各模块更新率、全目标模块更新包率 |
| 活动量 | 仅ESKD的K1/K2/K统计；ESKF/ESKD计数和完整帧比例q |
| 完整性 | status、未更新、诊断字节、CRC/格式/序号/base异常、会话计数起止差 |
| 波形 | SCK频率/个数、CS时长/停顿、IRQ等待、采集窗口 |
| 对照 | 配对FULL/DELTA流量差、平均包长差，同时报告更新覆盖率 |

- 逐包长度40+Σ槽长。正常模块混合平均长度q×1044+(1−q)×(84+2×mean(K_D))；未更新/诊断用通用逐槽模型。ESKF不当作真实K=480。
- raw碎片/无效字节单列，分子分母对应，不把全部raw除以仅有效包数当作干净平均包长。
- ESKF标记不能区分周期同步、高K回退和异常恢复；无事件证据的原因标unknown，完整帧成本仍计入q。
- 逐包代入本帧K得到精确一致只是结构检查，不是独立预测能力。可用前两区组K/q预测第三组平均包长，保留偏差。
- 0.41%等现象分开实际帧率、平均包长和bit/s解释。模块未更新或帧率下降不能伪装成压缩收益。
- 当前编码比较相邻原始扫描，PC缺少未发送的小变化；缓存链完整不等于原始ADC无损，也不保证偏差始终≤8。报告last reported value等用词需与代码核对。

## 9. 本轮能弥补哪些问题

| Data问题 | 证据 |
|---|---|
| 开销常数、FULL/DELTA交点 | 统一24+4M、M=4；每模块交点480；逐包核验 |
| SPI变长与FULL回归 | 新版波形、同条件FULL/DELTA配对 |
| K随N、固定K外推 | 全组合、逐模块分析和ABBA/BAAB |
| 忽略ESKF | 真实q进入混合模型，原因未知不猜测 |
| 字节/帧率/流量混淆 | 分开Lmean、f、R及有效更新率 |
| 缓存/模块未更新 | 窗口内事件及缓存链，恢复需要独立时标 |
| N4动态、rolling没有重复 | 每模式每条件3次重新加载；SD和n按run/区组 |
| 容量数字 | 新版帧长、q、实测时序修正条件预测；40 MHz/N>4仍理论 |

压力面积、CV/MAD、零点纠正、平台合并、P-H1及加载功耗属于另两章，不安排重测，也不能因本轮Data完成而打勾为解决。

## 10. 四小时顺序

| 时间 | 工作 |
|---|---|
| 0–30 min | 工具/版本、N4试录制、SPI基本波形；工具未就绪则顺延 |
| 30–75 min | 区组1：30段零载+14段动态，按接线组合集中 |
| 75–120 min | 区组2，重新执行条件与加载 |
| 120–165 min | 区组3，补齐主数据重复 |
| 165–180 min | K的ABBA/BAAB，共8段 |
| 180–200 min | 两段5分钟连续运行，独立模式/resync检查 |
| 200–240 min | 核验完整性/条件/重复数，备份、补缺及超时缓冲 |

这是预算，接线、稳定和故障排查可能超时。优先保主矩阵、SPI和可追溯性。50/100 Hz目前只作历史补充，不进入新版200 Hz主图；40 MHz、阈值扫描、精确K边界、更多长时重复另排。

## 文件

- halfday_schedule.csv：当前142行现场顺序。
- acquisition_schedule.csv：154行Data扩展计划（132主数据+16 K+6长运行），半天不执行全部。
- run_metadata_template.json：建议字段参考；GUI实际输出schema_version=2，以summary.metadata及test_condition为准。
- generate_schedule.py：固定种子生成计划、核对计数，不连接硬件。
- schedule_summary.json：段数及时间核验。

区组、配对与避免伪重复原则参考：[NIST随机区组](https://www.itl.nist.gov/div898/handbook/pri/section3/pri332.htm)。协议与工具要求依据当前项目源码及既有88条记录审计。

实验尚未执行。2026-09-06已完成PC GUI/记录器更新、13+8项离线测试及原生协议回归，并对88次历史实验470文件完成SHA256归档核验；没有修改STM32/Teensy固件、报告或历史原始文件内容，也未将实验项目打勾。范围为仅重做Data。
