Yannas-Sun/E-skin_MSc_final_report/data scalability/figures/exports/05_module_scaling.pdf

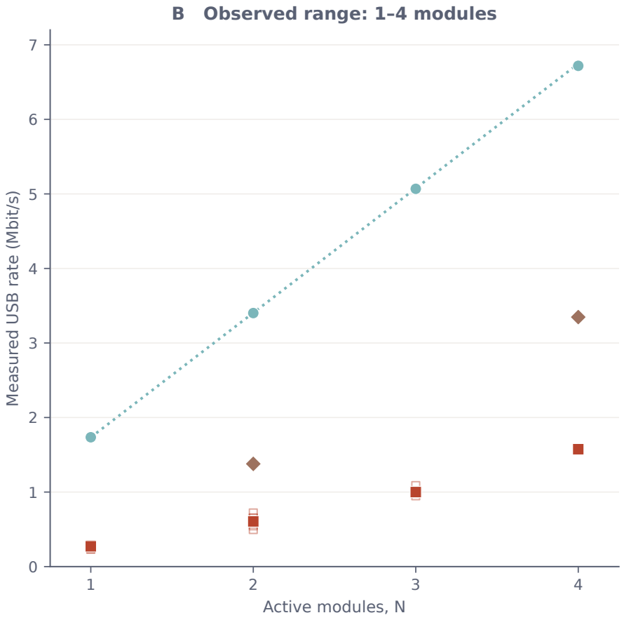
[picture p48: figure]
Active modules, N; Measured USB rate (Mbit/s); B Observed range: 1–4 modules

A 1–100 modules: bandwidth demand model

# Module scaling: observations and conditional projections

Target 200 Hz | observed N = 1–4 | modelled extension to N = 100

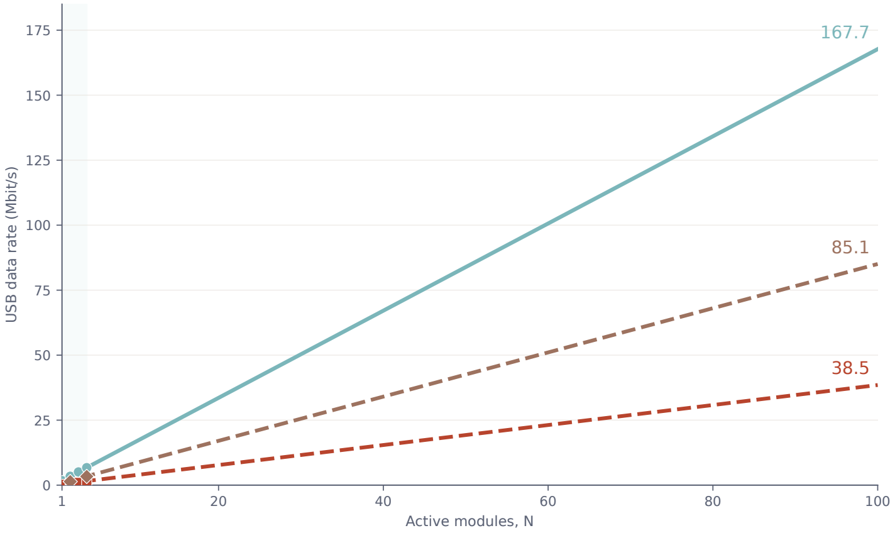
[picture p49: figure]
Active modules, N; USB data rate (Mbit/s)

DELTA projections hold the N=4 mean payload constant: 236.47 B/module (zero load), 527.44 B/module (full coverage).
Payload means include periodic syncs; projections assume 200 Hz and unchanged activity per module. Beyond N=4 is unmeasured. Filled markers: arithmetic means of run rates; open markers: individual runs. All recorded runs, including CHECK REQUIRED, are retained.

FULL: theoretical model
DELTA zero load: projection

DELTA full coverage: projection FULL observed

DELTA zero load observed
DELTA full coverage observed
