Yannas-Sun/E-skin_MSc_final_report/power scalability/DATA/analysis/current/voltage_drop_by_N_20260907/module_drop_N1.pdf

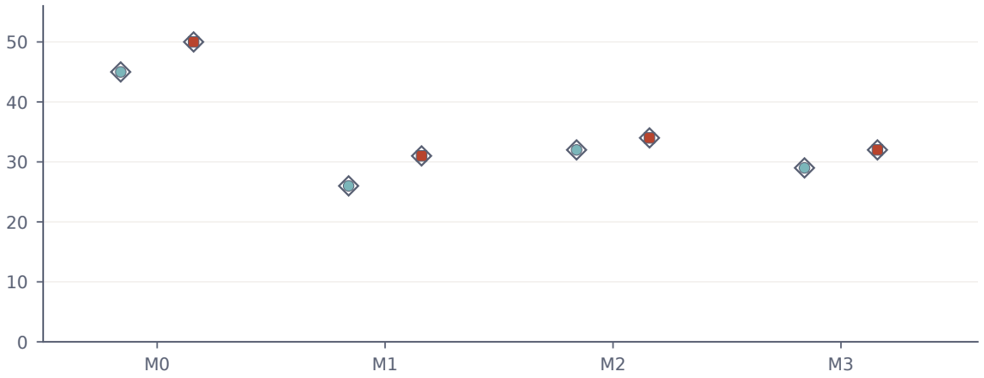
[picture p50: figure]

### Module ID

### Source-to-module difference (mV)

### N = 1 | n = 1 per module

Points = individual combinations; diamonds = means. SD unavailable: n=1 per module.

Zero load | Loaded (recorded) | Mean ± combination SD
