Yannas-Sun/E-skin_MSc_final_report/power scalability/DATA/analysis/current/voltage_drop_by_N_20260907/module_drop_N2.pdf

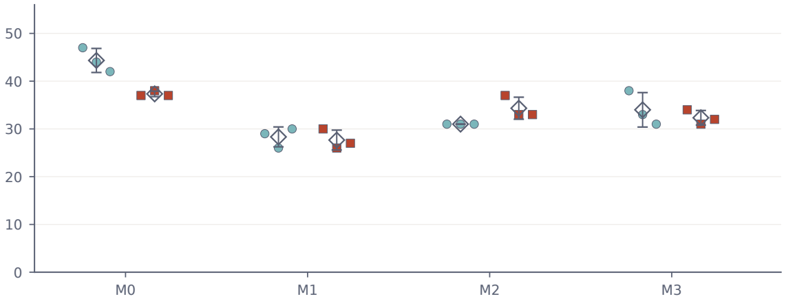
[picture p51: figure]

### Module ID

### Source-to-module difference (mV)

### N = 2 | n = 3 per module

Points = individual combinations; diamonds = means; SD describes combination spread.

Zero load | Loaded (recorded) | Mean ± combination SD
