Yannas-Sun/E-skin_MSc_final_report/power scalability/DATA/analysis/current/voltage_drop_by_N_20260907/module_drop_N3.pdf

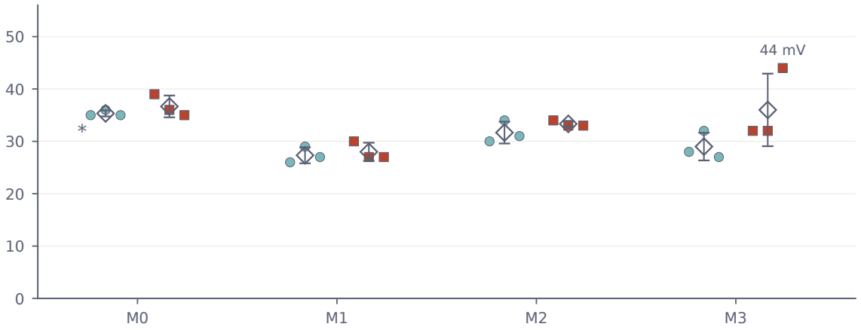
[picture p52: figure]

### Module ID

### Source-to-module difference (mV)

### N = 3 | n = 3 per module

Points = individual combinations; diamonds = means; SD describes combination spread. * One ZERO M0 value uses the separate retest; the 44 mV loaded M3 point is retained.

Zero load | Loaded (recorded) | Mean ± combination SD
