Yannas-Sun/E-skin_MSc_final_report/data scalability/archive/README.md

# Data scalability archive

This archive contains material removed from the active evidence path for the current report. Nothing was deleted.

| Archive path | Contents and reason |
|---|---|
| legacy_analysis/20260906_current_data_review | Superseded current-data review snapshot from 6 September |
| legacy_analysis/20260906_n2_full_review | Superseded N=2 FULL review snapshot |
| legacy_analysis/20260906_record_boundary | Earlier recording-boundary audit |
| legacy_analysis/20260906_v2_review | Earlier v2 parser and per-run analysis output |
| generated_cache/figure_review | Two temporary PNG checks for the 02E figure |
| generated_cache/figure_source_pycache | Python bytecode generated while running figure scripts |
| generated_cache/script_pycache | Python bytecode generated while running monitor/helper scripts |
| legacy_scripts/archive_legacy_data.ps1 | One-time migration utility that created the historical pre-variable-SPI archive; not part of current recording workflow |
| historical_documents/Data_Scalability_CN.md | Superseded standalone Chinese planning note, replaced by docs/Data_Scalability.md |
| historical_documents/CHANGELOG_CN.md | Original Chinese changelog, replaced by concise English docs/CHANGELOG.md |
| historical_documents/current_recordings_README_CN.md | Original Chinese diagnostic-figure note, replaced by figures/current_recordings/README.md |

The active history/pre_variable_spi_20260906/ directory is intentionally retained because the paper appendix cites it as historical provenance. The 2026-09-07 audit directories are also retained because they support final selection and diagnostic statements.

move_manifest.json records every source-to-destination move performed during this reorganisation.
