Yannas-Sun/E-skin_MSc_final_report/power scalability/archive/workflow/README.md

# Archived power workflow

`power_v28_figures.py` is the exact historical export script cited by the report appendix. The source release copy is `../../../report_versions/v2.8/workflow/power_v28_figures.py`; this package-local copy has the same SHA-256 and is retained for discoverability. It is not part of the active analysis workflow.
