Yannas-Sun/E-skin_MSc_final_report/power scalability/DATA/archive/m0_n1_n2_preview_20260907/README.md

# Latest M0 retest preview

This directory is an isolated preview generated from the report v2.4 compiled view plus five pointwise M0 retests. Its tables and figures are not copied into the manuscript automatically.

- data/ contains the compiled preview tables and source manifest.
- figures/ contains PNG/SVG previews and their manifests.
- preview_gallery.md is the English quick-review page; ../../archive/historical_documents/preview_gallery_cn_original.md preserves the earlier source note.
- ../../archive/historical_snapshots/preview_removed_mean_heatmap/ contains the retired mean-drop heatmap.

The preview retains 30 combination/load entries and 64 selected branch observations. It does not add a complete repeat or establish transient power capacity.
