Yannas-Sun/E-skin_MSc_final_report/hardware/firmware/archive/legacy-components/docs/E_skin_plan_report.pdf

# Planning Report: Scalable Electronics for Modular Multi-Layer e-Skin

### Student: Yange Sun Supervisor: Alexis W.M. Devillard

### April 23, 2026

Abstract

This planning report investigates scalable electronics for modular multi-layer e-skin, with particular attention to three system-level challenges: data scalability, power scalability, and calibration scalability. Building on the baseline platform developed by Devillard et al. and its later extension by Dutta et al., the report reviews the current literature, identifies key technical bottlenecks, and proposes preliminary experimental directions for a more compact and scalable modular architecture. As this is an early-stage planning report, the emphasis is placed primarily on literature review and theory-driven experimental design rather than on completed implementation. The experimental workflow presented here should therefore be understood as provisional and may be refined in response to results obtained at different stages of the project. Some figures were generated with AI assistance to help illustrate concepts and design ideas, and may not be fully accurate in scale, proportion, or geometry.

Word count: 3985

I acknowledge the use of Gemini 3 pro (Google, https: // gemini. google. com/ app (https://gemini.google.com/app) ) to help me with language polishing and image generation. I confirm that no content generated by AI has been presented as my own idea.

## Contents

1 Project Specification | 3
2 Literature Review | 4

2.2 Baseline Prototype e-Skin and Its Extension Towards Embodied Tactile

2.3 Research Gap: No Scalable Reference Architecture for e-Skin Electronics . | 8
2.6.1 | Power and Thermal Constraints Are Not Treated as First-Class
3 Implementation Plan and Objectives | 10
4 Risks and Mitigations | 13
5 Evaluation | 13
6 Ethical Analysis | 13
7 Preliminary Results | 14

## 1 Project Specification

Electronic skin (e-skin) is an important area in robotics because it enables distributed tactile sensing over large and curved surfaces, supporting safer interaction, richer perception, and more adaptive manipulation [1–5]. Recent work has advanced multi-modal sensing [6– 13], large-area fabrication [10,14–22], and robotic deployment [2,4,5,9,11,12,20,21,23–28]. However, much of this work still focuses on sensors [29–39], materials [12,15,16,29,40,41], structures [9,16], and AI-driven or bio-inspired algorithms [4,5,11,12,20,21,25–28,42,43], while giving less attention to a key barrier to practical deployment, namely electronics scalability.

A promising route is a modular e-skin architecture, where larger systems are built by integrating multiple modules without major redesign. Previous studies have already explored this direction [6–8, 10, 13, 18, 21, 40, 42, 44–46]. Building on the multi-modal, multi-layer platform of Devillard et al. [23] and its later extension by Dutta et al. [24], this project investigates how the baseline prototype can be redesigned into a compact and scalable modular system. The project is primarily hardware-oriented. It does not aim to replace the sensing principles of the baseline device, but to develop and evaluate an electronics architecture that supports miniaturisation, multi-module integration, and future multi-patch expansion while preserving useful tactile performance.

To address this aim, the project tests four hypotheses.

- H1 (Core). A miniaturised five-module patch can preserve the core sensing capability of the baseline platform, such that normal- and shear-force regression NMSE remain within 20% of the baseline under comparable experimental conditions.
- H2 (Data scalability). A hierarchical host–patch–module architecture can reduce communication load sufficiently to support scalable multi-module integration while keeping per-host bandwidth below a defined limit for several patches. In addition, event-driven algorithms can be combined with clock synchronization without violating H1.
- H3 (Calibration scalability). A repeatable calibration workflow can be established such that calibration transfer error after disassembly and reassembly remains below 10%, indicating that the system remains functional and maintainable as module count increases.
- H4 (Power scalability). A scalable patch-level power architecture can support stable operation of the miniaturised five-module patch, such that power consumption remains below a defined limit under continuous multimodal acquisition and scales approximately linearly with sampling rate and the number of enabled modules.

The main contribution of the project is therefore a miniaturised five-module scalable eskin patch together with a reference architecture for scalable data, power, and calibration management. Larger goals, including multi-patch chaining, whole-arm deployment, and dual-arm robotic implementation, are treated as longer-term extensions rather than primary MSc deliverables [6,19,42,47]. Success will be judged by whether the proposed architecture can manage communication load, preserve acceptable force-sensing accuracy relative to the baseline, and maintain calibration repeatability after reassembly.

## 2 Literature Review

This section begins with a detailed review of the two foundational papers on which this project is based. It then examines, summarises, and compares related studies in the field to identify the main bottlenecks and research gaps that constrain electronics scalability. Finally, it discusses a number of existing and potential approaches for addressing these limitations.

### 2.1 Overview

The development of electronic skin (e-skin) has progressed from individual tactile sensors and small arrays for basic contact or pressure detection [1, 2, 33, 38, 39, 43], to large-area flexible robotic skins that introduced challenges in wiring, readout, and deployment [18, 21,44]. More recent work has moved towards bio-inspired multimodal systems integrating force, vibration, temperature, and texture sensing, supported by advances in soft materials [3, 26, 48]. As sensing scale and complexity have increased, AI, neuromorphic sensing, and event-driven processing have also become important for tactile inference and data handling [4,27,49]. Overall, e-skin development has shifted from simple tactile sensing to intelligent multimodal systems, with scalability and deployability becoming increasingly important [5, 50].

### 2.2 Baseline Prototype e-Skin and Its Extension Towards Embodied Tactile Perception

This project builds on the modular multi-layer e-skin platform introduced by Devillard et al. [23] and later extended by Dutta et al. [24]. Together, these studies provide the main hardware and methodological basis for the present work: the former establishes the prototype design and readout architecture, while the latter extends it towards embodied tactile perception.

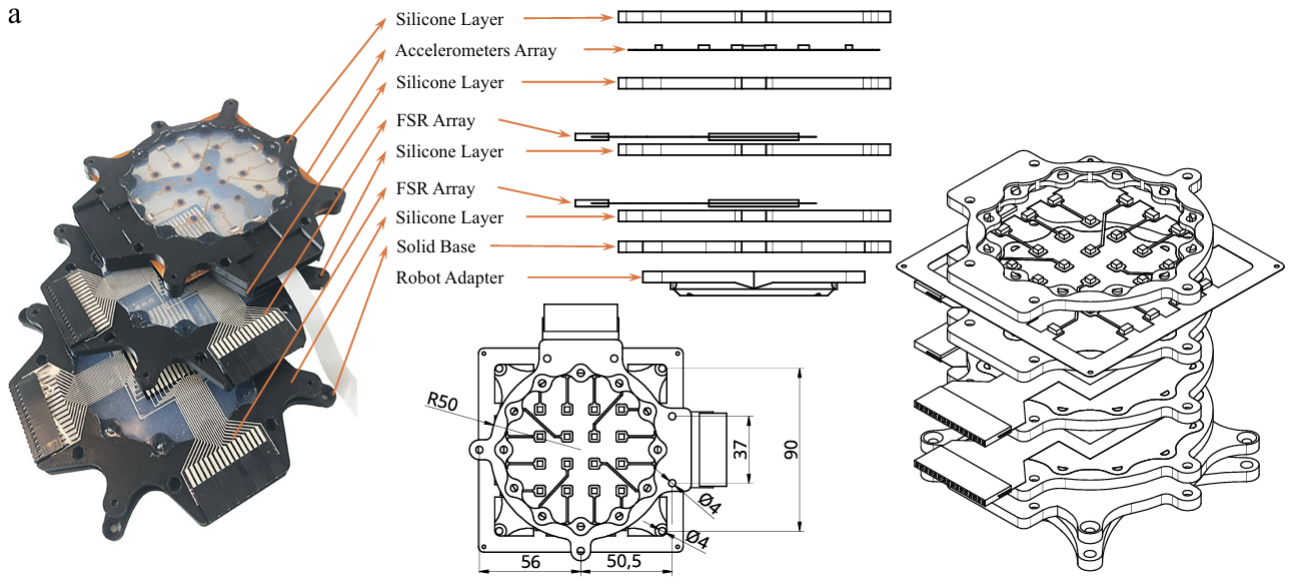
[picture p54: figure]

Figure 1: Structural design of the baseline modular multi-layer e-skin platform [24].

### 2.2.1 Modular Structure

As shown in Figure 1, the baseline e-skin is a modular 1
, multi-modal artificial skin inspired by biological skin. It consists of multiple sensorized layers embedded within silicone, including an outer vibration-sensing layer, two internal force-sensing layers, silicone interlayers, a solid base, and a robot adapter. This layered design allows sensing configuration and local compliance to be varied while keeping the overall patch geometry consistent. In the later study, the same structure is further treated as an embodiment variable rather than a fixed sensing substrate.

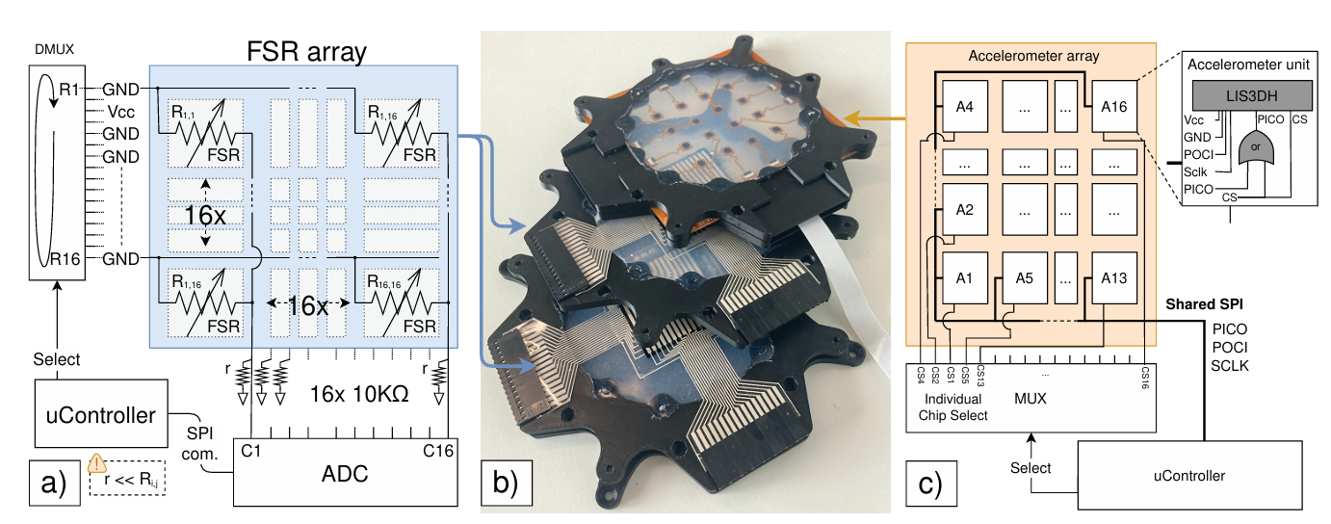
[picture p55: figure]

Figure 2: Baseline modular multi-layer e-skin platform and its sensing architecture [23].
(a) FSR array readout architecture. (b) Photograph of the assembled multi-layer e-skin prototype. (c) Accelerometer array architecture.

### 2.2.2 Hardware Structure

The prototype integrates force and vibration sensing within the same contact area. Two 16×16 FSR arrays provide 512 taxels for distributed force sensing, while a 4×4 array of 3-axis LIS3DH accelerometers provides 48 vibration channels. The system uses Ecoflex 00-31 and DragonSkin 30A as alternative silicone materials, with overall dimensions of approximately 120 × 120 × 25 mm. As shown in Figure 2(a), FSR readout uses matrix scanning with row–column addressing, while the accelerometer array uses SPI with multiplexed chip selection, as shown in Figure 2(c). Data are acquired by a Teensy 4.1 at 700 Hz with real-time USB transmission [23]. A full summary of the hardware parameters is provided in Appendix A Table A1.

### 2.2.3 Algorithmic Implementation

The two papers differ mainly in algorithmic scope. Devillard et al. use task-specific models for force estimation and object-property prediction, whereas Dutta et al. introduce the Latent Filter, an action-conditioned deep state-space model for embodied tactile perception [24]. As shown in Figure 3, this model combines modality-specific encoders,

1The term ‘modular” in the paper [23] is different from the meaning of modular” adopted in this report. Here, modular” refers to local modularity within a single e-skin unit, namely a layered structure in which sensing and silicone layers can be detached, replaced, and reconfigured. It does not yet refer to a system-level modular network of multiple e-skin patches.

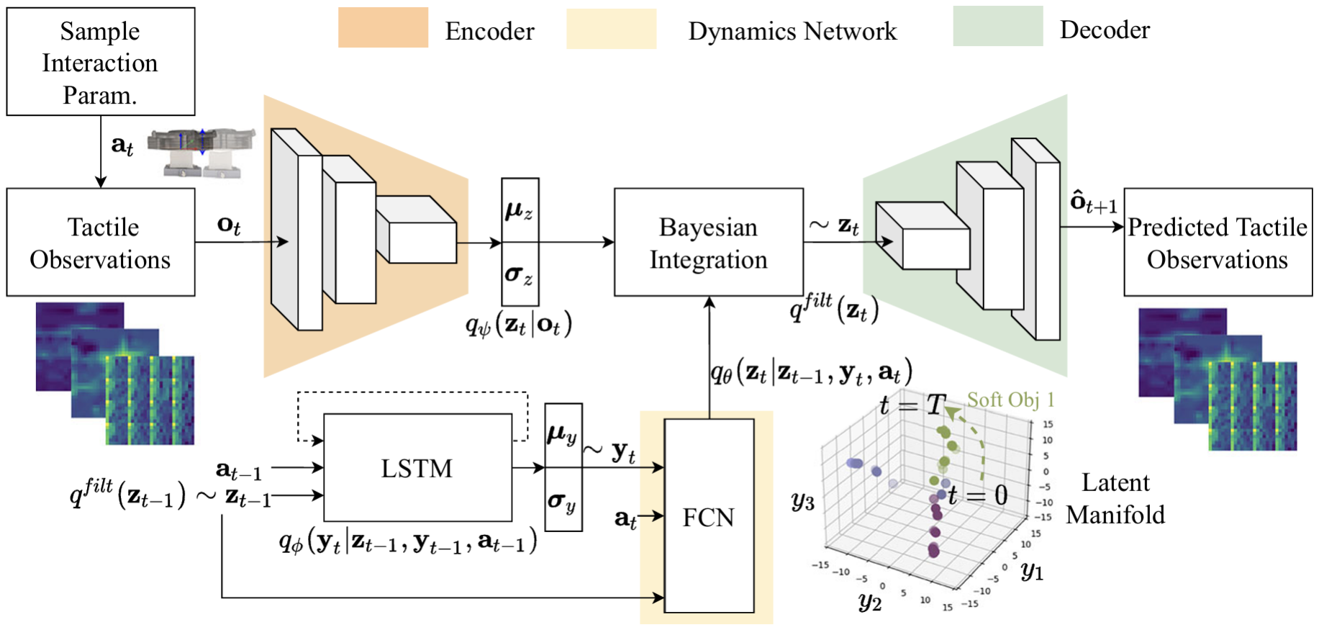
[picture p56: figure]

Figure 3: Architecture of the proposed Latent Filter for embodied tactile perception [24].

latent inference, dynamics modelling, and reconstruction. The full Latent Filter algorithm is provided in Appendix B Algorithm B1.

### 2.2.4 Experimental Design

Both studies use similar robotic experiments based on pressing, precession, and sliding over structured objects [23, 24]. The later work extends the earlier one by using a richer object set and incorporating robot proprioceptive and action information, while retaining the same multimodal sensing platform and 700 Hz acquisition setting.

### 2.2.5 Performance and Findings

Taken together, the two papers show that the platform can capture both quasi-static force and dynamic vibration signals in a robust and interpretable way. As shown in Figure 4a, the earlier work demonstrates reasonable normal- and shear-force estimation performance and shows that combining two FSR layers can improve force sensing [23]. As shown in Figure 4b, the later work further shows that multimodal sensing and interaction strategy strongly affect perceptual performance [24]. Overall, the baseline platform provides a strong starting point for this project while also exposing the need for a more compact and scalable electronics architecture.

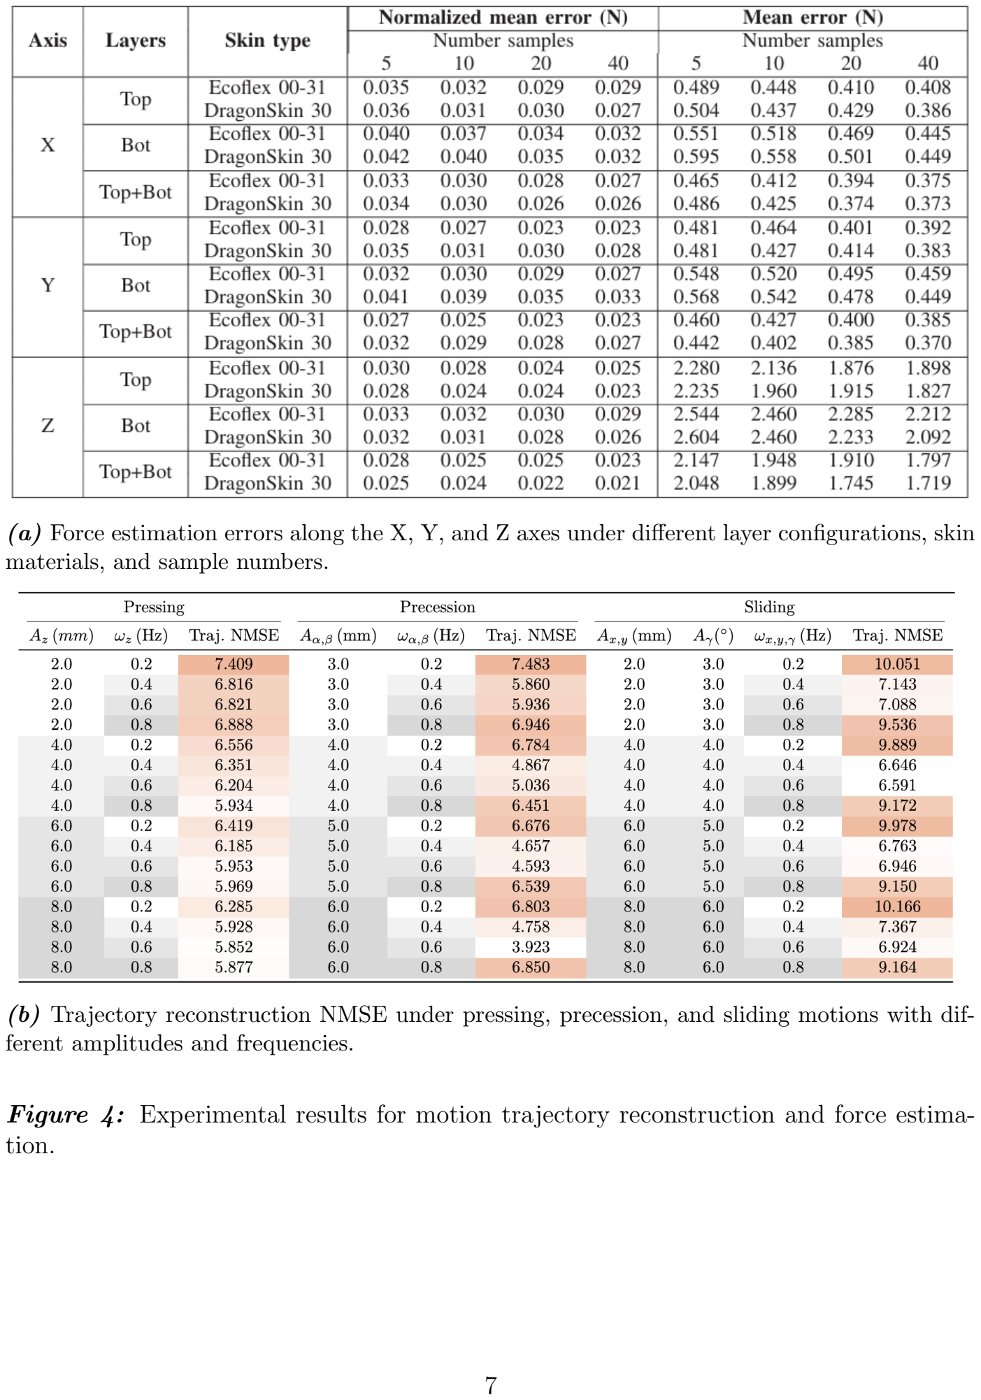
[picture p57: page 7]

(a) Force estimation errors along the X, Y, and Z axes under different layer configurations, skin materials, and sample numbers.
(b) Trajectory reconstruction NMSE under pressing, precession, and sliding motions with different amplitudes and frequencies.

Figure 4: Experimental results for motion trajectory reconstruction and force estimation.

### 2.3 Research Gap: No Scalable Reference Architecture for e-Skin Electronics

This project investigates how an existing e-skin prototype can be redesigned into a scalable, generalisable, and deployable modular platform, and is therefore positioned primarily as a hardware-oriented study. Devillard et al. provide the main hardware foundation, while Dutta et al. serve mainly as a software-side reference for later evaluation.

Although existing reviews discuss e-skin in terms of materials, sensing mechanisms, hardware, signal processing, and applications [3–5, 26, 43, 48], scalability is rarely treated as a systems-engineering problem. Many studies mention large-area deployment, but few define a modular power and data backbone that can scale from one patch to many [19,21,27,51]. Similarly, modular e-skin studies mainly focus on function, structure, or materials rather than on data, power, and calibration scalability [6–8,10,13,21,40,42,44–46]. Appendix C Table A3 and Appendix C Table A2 summarise these limitations. The key gap is therefore the lack of a scalable reference architecture to support the transition from one patch to many.

### 2.4 Data Scalability

As e-skin systems scale, data volume increases rapidly, making bandwidth and synchronization central bottlenecks.

### 2.4.1 Bandwidth is Under-Specified

The baseline prototype already suggests that communication load can become a limiting factor [23]. Although multimodal sensing and high refresh rates improve tactile richness [6–13, 23, 24], they also greatly increase channel count and transmission demand. The key challenge is therefore to reduce communication load without significantly sacrificing sensing performance.

Hierarchical signal processing.
Hierarchical architectures such as HEX-O-SKIN and ROBOSKIN distribute processing locally before patch-level transmission [7, 8, 18, 21, 42, 46]. This improves maintainability and scalability, but existing implementations use lower sensor density and sampling rates than the present prototype, so hierarchical processing alone is unlikely to be sufficient.

Event-driven algorithms.
Event-driven methods reduce traffic by transmitting only salient changes [19, 27, 49, 52– 54]. SoDP is effective but threshold-sensitive [19], while Cao’s dual-layer design is more relevant here because it better matches the two-layer FSR structure [52].

### 2.4.2 synchronization is under-specified

Data scalability also depends on reliable temporal alignment. Intra-module synchronization is required across sensing modalities, while inter-module synchronization is required across distributed controllers. Existing solutions include programmable units, synchronization protocols, and hardware-level implementations [55–57], but scalable multimodal e-skin still lacks a clear synchronization strategy.

### 2.5 Calibration Scalability

### 2.5.1 Calibration Does Not Scale with Sensor Count

As sensor count increases, calibration becomes a major bottleneck. Dense FSR arrays require per-taxel correction, while multi-layer systems also require cross-layer alignment for reliable shear-force inference. Because calibration depends on material properties, geometry, and assembly conditions, methods developed for one prototype may not transfer well to another. A scalable e-skin system therefore requires a calibration pipeline that is repeatable, transferable, and extensible.

Automatic in situ calibration.
Automatic in situ calibration improves deployment efficiency by calibrating sensors directly on the robot using controlled contact and force–torque sensing [58]. However, it remains essentially a taxel-level method.

Plenum-based array calibration.
Plenum-based calibration improves throughput by exposing an entire skin patch to a uniform pressure field, allowing many taxels to be calibrated in parallel [28]. This is more scalable than point-by-point calibration.

Limitations and possible improvements.
Neither approach fully addresses dense modular e-skin. The in situ method remains limited by hysteresis and coupling effects [58], while the plenum-based method is constrained by pressure noise, leakage, and chamber robustness [28]. Current methods therefore do not yet provide a complete solution for high-density, multi-layer, modular calibration.

### 2.6 Power Scalability

### 2.6.1 Power and Thermal Constraints Are Not Treated as First-Class Design

Variables

As e-skin systems scale in area, sensor density, and functional complexity, power consumption becomes a systems-level constraint. This is especially important for large or mobile robotic platforms, where additional sensors, controllers, and communication interfaces increase both electrical demand and thermal load, with possible effects on sensing stability and long-term reliability.

However, power and thermal issues are still rarely treated as core design variables. Existing work has proposed partial solutions, including event-driven acquisition [19, 27, 53], structural simplification [9], neuromorphic approaches [25], and modular patch-level integration [13, 21, 23]. These studies address parts of the problem, but do not define a complete power architecture for modular multi-layer e-skin.

Distributed energy perspectives for scalable robotics.
Mukherjee et al. argue that energy in robotics should be treated as a system-architecture problem rather than only a battery-capacity issue [59]. This perspective is relevant here because scalable e-skin depends not only on supplying power, but also on how it is distributed and regulated.

Limitations and possible improvements.
The literature still lacks a general reference architecture for modular multi-layer e-skin power design, particularly for power-tree design, domain isolation, subsystem monitoring, and power scaling with system size. This is the gap targeted by the present project.

## 3 Implementation Plan and Objectives

This section provides a detailed description of the final objectives of the project and the milestones for each phase.

### 3.1 Primary Objective

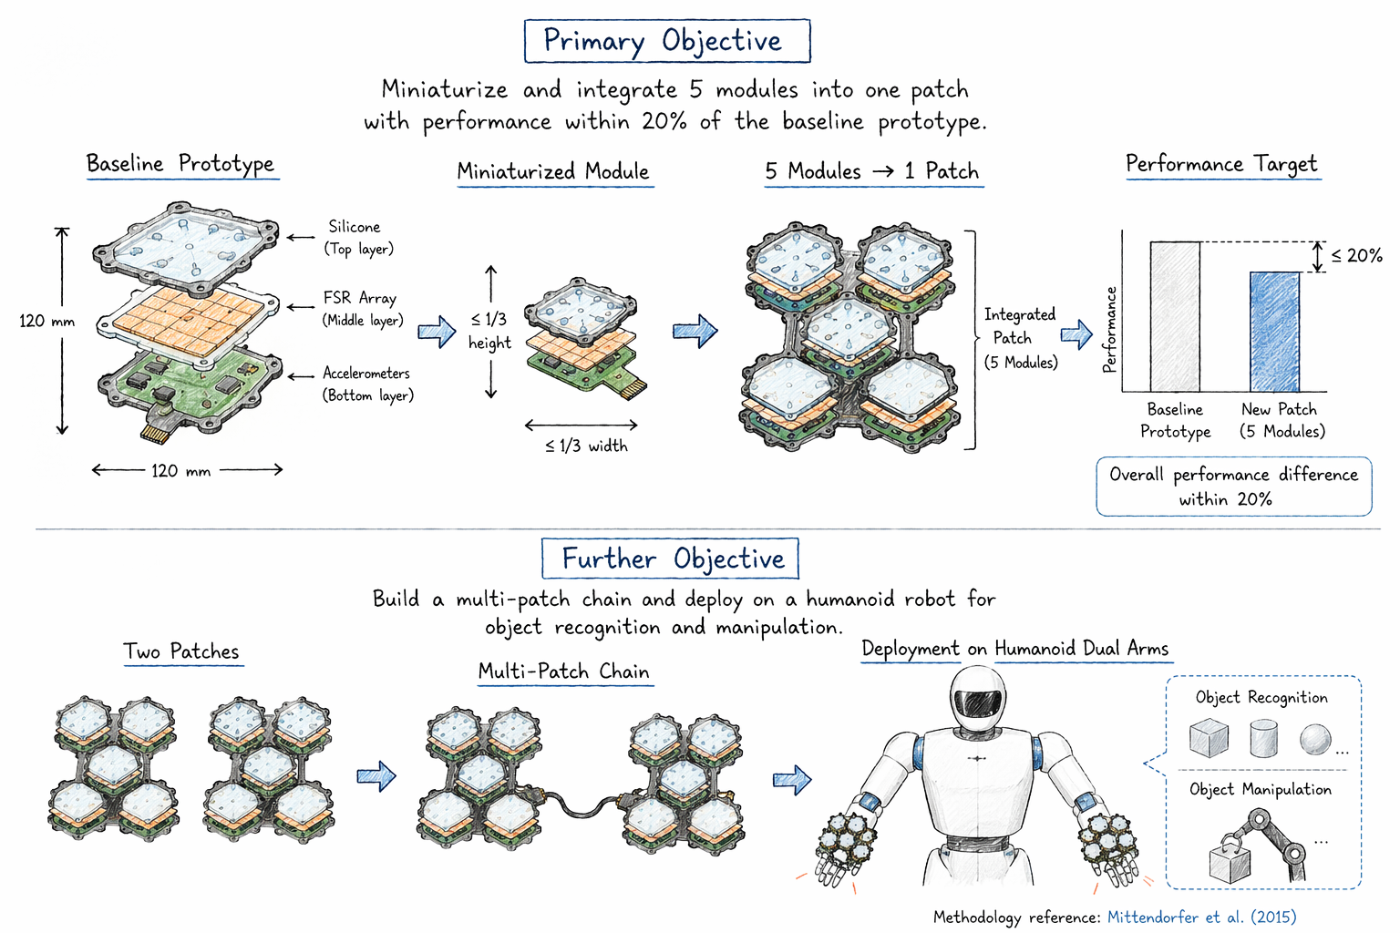
[picture p58: figure]

Figure 5: Figure illustration of the project objectives.

The primary objective of this project is to transform the current modular multi-layer e-skin prototype into a more compact and scalable system. Specifically, the electronics and structural footprint will be reduced to at least one third of the original size while preserving the core sensing functions of the baseline design.

Building on this miniaturised design, the project aims to integrate five e-skin modules into a single patch and evaluate it using a protocol similar to that in Section 2.2.4 [23]. The target is to keep tactile sensing performance close to the baseline prototype, defined here as the Ecoflex 00-31 structure with both sensing layers. Using Figure 4a as reference, the final mean force estimation error should remain within 20% of baseline:

- X-axis shear force: 0.375 ± 0.075 N

- Y-axis shear force: 0.385 ± 0.077 N
- Z-axis normal force: 1.797 ± 0.3594 N

Force estimation error is used as the main criterion because it more directly reflects core tactile sensing capability than trajectory RMSE shown in Figure 4b. Figure 5 illustrates the objective more clearly.

### 3.2 Intermediate Milestones

To achieve the final objective, the project is divided into five intermediate milestones, as illustrated in Figure 6.

O0. Modular system architecture (preliminarily completed in theory)

Define the overall scalable system architecture:

- O0.1 Define module-level and patch-level interfaces for sensing, communication, and power.
- O0.2 Establish an integration strategy for combining five miniaturised modules into one patch.
- O0.3 Specify the partitioning between module electronics, patch coordination, and host-side processing.
- O0.4 Ensure extensibility towards future multi-patch deployment.

O1. Data scalability

Establish reliable multimodal data acquisition for the five-module patch:

- O1.1 Build a continuous streaming pipeline for the integrated patch.
- O1.2 Maintain low frame drop, low timing jitter, and stable packet delivery.
- O1.3 Preserve temporal alignment between FSR and accelerometer signals.
- O1.4 Assess host-side logging and processing load for future expansion.

O2. Power scalability

Evaluate whether the integrated patch remains energetically practical:

- O2.1 Develop a power architecture for stable five-module operation.
- O2.2 Quantify current draw as a function of sampling rate. 2
- O2.3 Quantify current draw as a function of enabled modules or sensors.
- O2.4 Assess suitability for future dual-patch deployment.

2Preliminary Power Budget calculate in subsection 7.3

O3. Calibration scalability

Develop a repeatable and transferable calibration workflow:

- O3.1 Define a repeatable calibration procedure for the integrated patch.
- O3.2 Define a synchronization calibration procedure.
- O3.3 Control inter-module variation across the assembled patch.
- O3.4 Verify post-reassembly performance against the baseline.

O4. Reference design package

Deliver a reusable package for future e-skin development:

- O4.1 Consolidate the electronics architecture, firmware, and calibration workflow.
- O4.2 Document module design, patch integration, and validation in reproducible form.
- O4.3 Summarise validation results for future comparison.
- O4.4 Deliver a reference toolkit for future extensions.

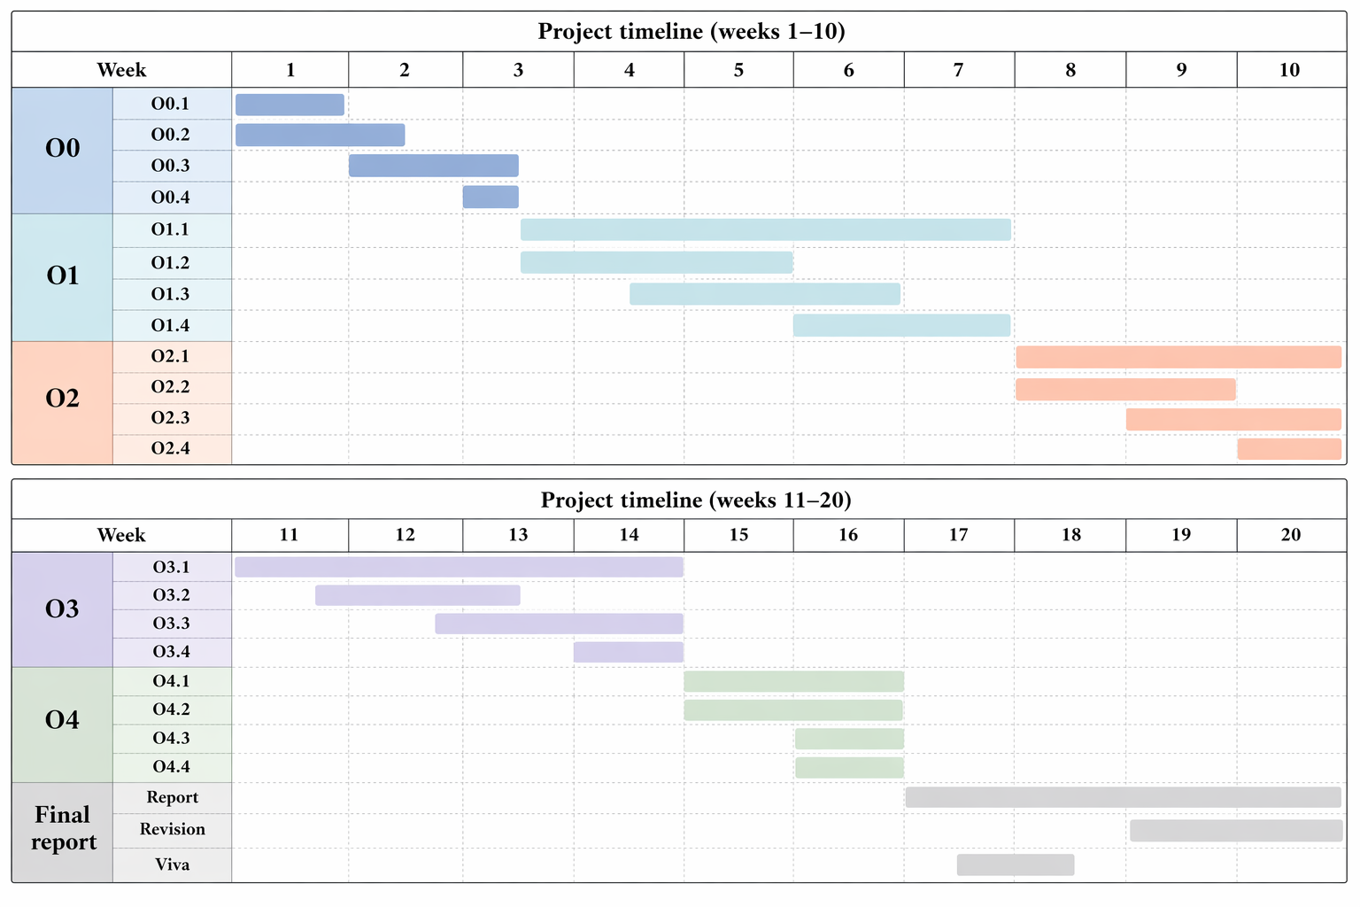
[picture p59: figure]

Figure 6: Project timeline over 20 weeks. The first phase, covering Weeks 1–10, focuses on modular system architecture, data scalability, and power scalability. The second phase, covering Weeks 11–20, focuses on calibration scalability, delivery of the reference design package, final report writing, revision, and viva preparation.

## 4 Risks and Mitigations

As the project progresses from a single baseline prototype to a miniaturised five-module patch and, potentially, a multi-patch system, several technical risks may affect system reliability and scalability. The main risks concern high-throughput streaming, timing consistency, analog sensing quality, calibration transferability, and future system expansion. Table A5 summarises the key risks, causes, and mitigation strategies.

At the current stage, data instability and timing inconsistency are the most critical because they determine whether the five-module patch can operate as a coherent multimodal sensing system. Calibration-related risks become more important after assembly and reassembly, when small mechanical variations may reduce repeatability. Multi-patch scaling is treated as a forward-looking risk so that early design choices do not constrain future expansion.

## 5 Evaluation

The evaluation plan is organised around four main milestones. Table A6 defines the metrics for O1 data scalability, including streaming reliability, packet stability, inter-modal temporal alignment, and host-side readiness for future expansion. Table A7 addresses O2 power scalability, covering stable power delivery, current draw versus sampling rate, current draw versus enabled modules, and the suitability of the resulting power budget for future dual-patch deployment. Table A8 evaluates O3 calibration scalability, including calibration repeatability, synchronization calibration, inter-module consistency, and post-reassembly performance retention. Table A9 defines the criteria for O4 reference design package, focusing on completeness, reproducibility, validation coverage, and future usability.

Together, these tables translate the project objectives into measurable criteria by specifying metrics, protocols, acceptance thresholds, and statistical analysis where appropriate. In addition, preliminary outcomes from O0, discussed in Section 7.1.2, are summarised in Table 1 and Table 2, which provide an initial basis for the current architecture choices.

## 6 Ethical Analysis

This project involves relatively low direct ethical risk because it does not use human participants, animal subjects, or biological specimens. The work is based on robotic e-skin hardware and controlled robot–object interactions, and the collected data are nonpersonal sensor and calibration data. The main ethical considerations therefore concern safe engineering practice, responsible data handling, and the longer-term implications of tactile sensing in robotics.

A project-specific issue is safety during robotic testing and waste generated through iterative prototyping. Since experiments might will be conducted on a Kinova robotic arm, testing must follow laboratory risk assessments and established robot-safety procedures, including collision prevention, emergency stop access, workspace clearance, and supervised operation. More broadly, the work should remain consistent with recognised standards such as ISO 10218 and ISO/TS 15066 for future human–robot interaction contexts. In addition, PCB fabrication, silicone moulding, and component replacement may generate material waste, so unnecessary iteration should be minimised and waste should be handled responsibly.

Overall, the ethical risk is low, but safe experimentation and responsible design remain essential.

## 7 Preliminary Results

At present, the work completed in this project is mainly theoretical. In particular, the main progress so far has been the development of the Data Throughput Model and the design of the Modular System Architecture.

### 7.1 Modular System Architecture

### 7.1.1 Module Structure

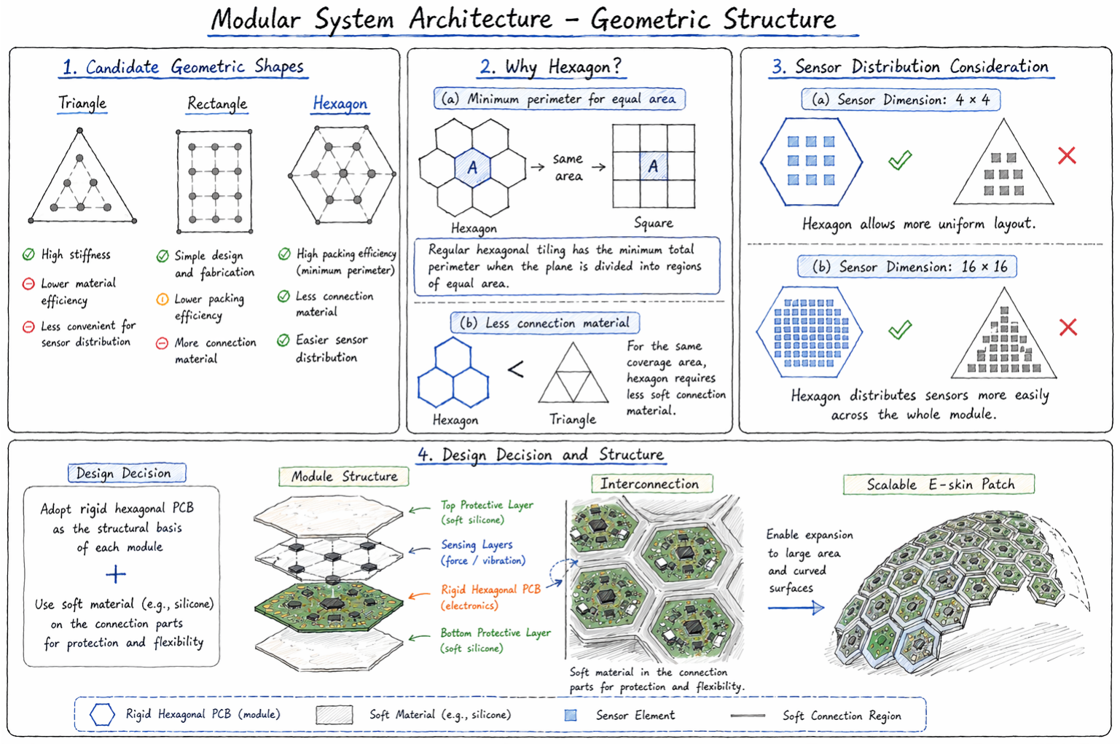
[picture p60: figure]

Figure 7: Figure illustration of the proposed geometric structure in the modular e-skin architecture.

At present, the regular geometric forms most commonly adopted in modular e-skin designs are triangular [7,8,42] , rectangular [6], and hexagonal [7,8,13,42] units. These geometries are widely used because they provide clear tessellation rules, facilitate physical assembly, and support scalable integration over larger sensing areas.

Currently, some studies have compared triangular and hexagonal mechanical structures and found that triangular configurations can provide higher bending and torsional stiffness

[60]. However, these advantages are not the primary concern for e-skin scalability. By contrast, a well-known study from a biomimetic perspective explains why honeycombs are predominantly hexagonal: when a plane is divided into regions of equal area, regular hexagonal tiling achieves the minimum total perimeter [61].

In other words, for the same coverage area, hexagonal modules require less compliant interconnection material between adjacent units. In addition, given that the sensor dimensions in this project are 4×4 and 16×16, a regular hexagon provides a more practical basis than a triangle for distributing sensors across the entire module area.

For these reasons, the proposed design will preliminarily adopt a rigid hexagonal PCB as the structural basis of each module, while using compliant materials such as silicone to protect the interconnecting regions. This configuration is expected to better support future e-skin expansion over large areas and curved surfaces. Figure 7 illustrates modular structure more clearly.

### 7.1.2 Macro Structure

The system hierarchy is defined as follows:

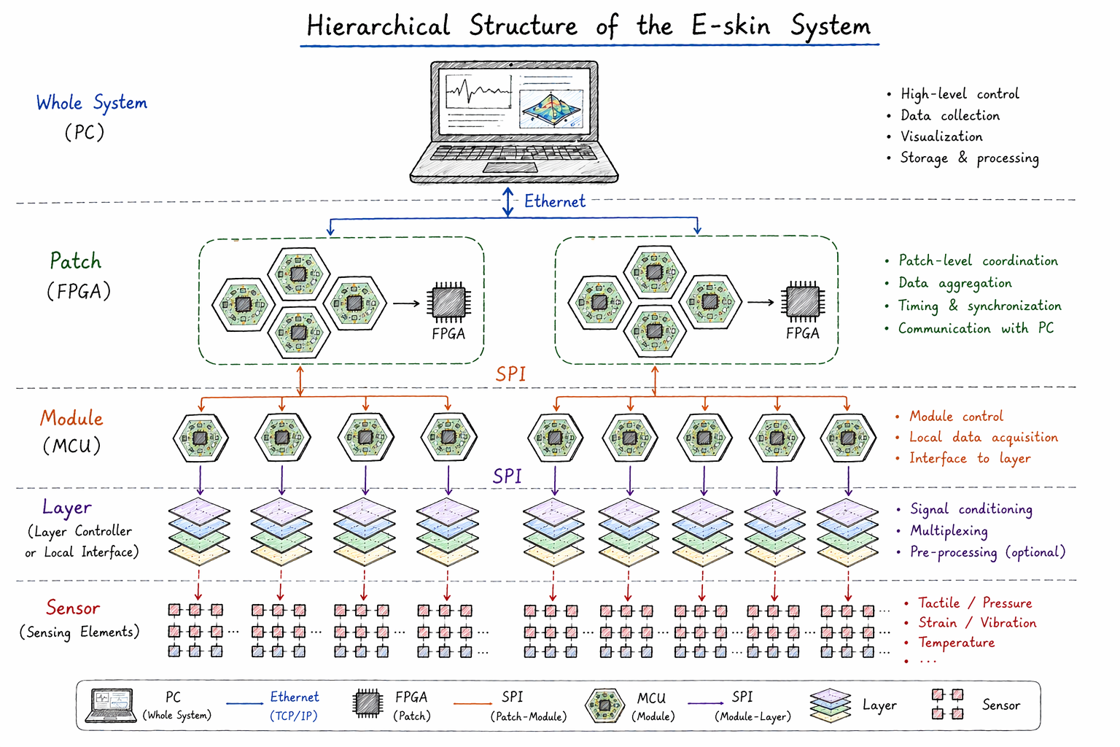
[picture p61: figure]

Figure 8: Figure illustration of the hierarchical structure of the proposed modular e-skin system.

This structure is intended to support both modular integration and future scalability.

Hierarchical Structure
At the macro level, the proposed e-skin follows a hierarchy from system to patch, module, layer, and sensor. The whole system is currently a PC responsible for high-level control, logging, and processing. Each patch contains a patch-level controller that aggregates data from five modules, aligns timing, packetizes the data stream, and communicates with the host via Ethernet. Each module is controlled by a local MCU, and is further divided into sensing layers and individual sensors.

A key design question is whether the patch-level controller should be a high-performance MCU or an FPGA. Although an FPGA increases cost and development complexity, it is better suited to parallel aggregation, deterministic timing, synchronization, and SPI-to-Ethernet bridging as system scale increases. For this reason, the current design provisionally adopts an FPGA at the patch level. Table 1 presents the preliminary decision matrix, and Figure 8 illustrates the hierarchy.

Table 1: Preliminary decision matrix for the patch-level controller selection. Higher scores indicate a more favorable option.

Criterion | Weight | High-performance
| | MCU | FPGA
Hardware cost | 0.20 | 5 | 2
Bring-up simplicity / development risk | 0.20 | 5 | 2
Parallel multi-module aggregation | 0.20 | 2 | 5
Synchronization | 0.20 | 3 | 5
SPI-to-Ethernet bridging scalability | 0.20 | 2 | 5
Weighted total | 1.00 | 3.4 | 3.8

Communication Protocol
The communication protocol follows the same hierarchy. Communication between the PC and each patch uses Ethernet, which provides a robust host-to-patch link and is supported by the DTM analysis in Section 7.2.3. Within each patch, SPI is provisionally retained between the patch-level controller and the five modules. Although SPI is not ideal for long-term scaling, it remains suitable at this stage because distances are short, module count is limited, and deterministic high-throughput communication is required. Alternative protocols such as RS-485, CAN-FD, and LVDS involve either lower effective throughput or greater physical-layer complexity; a comparison is given in Table A4. SPI is therefore used here as a practical short-range solution.

A second open question concerns the module-level controller. Reusing one Teensy 4.1 per module is likely to be inefficient, so two alternatives are considered: a master–slave design and a lower-cost MCU design. The latter currently appears more favorable in cost, integration, and scalability. Table 2 summarises this preliminary comparison; the final choice will be made after O0.2.

Table 2: Decision matrix for module-level controller selection. Higher scores indicate a more favorable option.

Criterion | Weight | Master–slave | Cheaper MCU
Hardware cost | 0.35 | 4 | 5
Wiring / integration simplicity | 0.20 | 2 | 4
Determinism | 0.20 | 3 | 4
Firmware reuse | 0.15 | 5 | 3
Scalability / modularity | 0.10 | 2 | 5
Weighted total | 1.00 | 3.35 | 4.35

### 7.1.3 Edge Computing (Optional)

Edge computing is considered here as an optional extension of the proposed architecture. The core idea is to distribute part of the computation across different levels of the system, rather than transmitting all raw data to the final host controller. This concept has already been explored in recent e-skin research designed by Li et al.,2026 [53].

In the present design, a similar idea could be introduced through the hierarchical structure by adding encoder and decoder functions at different levels. In principle, each level could first process its own data locally, for example through feature extraction or compression, and then transmit only the reduced representation to the upper or lower level, where further decoding or interpretation would be performed. A possible future direction is to explore a VAE-based method for this purpose. However, this remains only a preliminary concept at the current stage. The specific implementation strategy will require further study and practical validation.

### 7.2 Data Throughput Model

This section estimates the raw data throughput at each level of the hierarchy.

### 7.2.1 DTM for each module

Each module contains two FSR layers and one accelerometer array, giving

Cmodule = 512 + 48 = 560

channels per frame. At 700 Hz, the sample throughput is

Rsamples,module = 560 × 700 = 392,000 samples/s

Assuming 16-bit encoding³
, the raw module bandwidth is

Rmodule,raw = 392,000 × 2 = 784,000 B/s ≈ 0.784 MB/s

With 20 B/frame metadata (timestamp, frame counter, module ID, flags, and CRC),

3
In this section, B denotes byte and b denotes bit. 1 MB ≈ 1,000 kB ≈ 1,000,000 B ≈ 8,000,000 b.

Hmeta = 20 B/frame

the effective frame size is

Dmodule = 1120 + 20 = 1140 B/frame

and the total module bandwidth becomes

Rmodule,total = 1140 × 700 = 798,000 B/s ≈ 0.8 MB/s ≈ 6.4 Mb/s

### 7.2.2 DTM for each patch

One patch contains five modules, so the aggregated payload is

Dpatch,agg = 5 × 1140 = 5700 B/frame

Adding 20 B patch-level metadata gives

Dpatch,total = 5700 + 20 = 5720 B/frame

and the FPGA-side output bandwidth is

Rpatch,FPGA = 5720 × 700 = 4,004,000 B/s ≈ 4.0 MB/s ≈ 32.0 Mb/s

Since this exceeds the conventional Ethernet MTU, fragmentation is required. With a maximum UDP payload of 1472 B,

Npkt =

5720

1472
= 4

Assuming 66 B Ethernet overhead per packet,

Dpatch,eth = 5720 + 4 × 66 = 5984 B/frame

so the required Ethernet bandwidth per patch is

Rpatch,eth = 5984 × 700 = 4,188,800 B/s ≈ 4.19 MB/s ≈ 33.5 Mb/s

### 7.2.3 DTM for the whole system and link budget

For two identical patches,

Rtotal,eth = 2 × 4,188,800 = 8,377,600 B/s ≈ 8.38 MB/s ≈ 67.0 Mb/s

This corresponds to

U100 =

8.38
12.5

≈ 67.0%

for 100BASE-TX , and

U1000 =

8.38
125

≈ 6.7%

for 1000BASE-T. The remaining headroom is

H100 = 12.5 − 8.38 = 4.12 MB/s

H1000 = 125 − 8.38 = 116.62 MB/s

with theoretical saturation at

Nmax,100 =

12.5
4.19

≈ 2–3 patches

for 100BASE-TX , and

Nmax,1000 =

125
4.19

≈ 29 patches

for 1000BASE-T.

At the current stage, 100BASE-TX is sufficient for two patches, whereas larger-scale applications will likely require 1000BASE-T. The initial implementation therefore adopts 100BASE-TX .

### 7.3 Preliminary Power Budget

Although O2.2 and O2.3 will provide direct current measurements in later stages, a rough estimate is useful at this point. For the accelerometer array, the LIS3DH datasheet reports a typical current of about 11–20 µA. For 16 sensors per module and 5 modules per patch, this gives a total accelerometer current of approximately

IACC,total ≈ 0.88–1.60 mA

or
PACC,total ≈ 2.9–5.3 mW

assuming a 3.3 V supply.

By contrast, controller-side power is likely to dominate. A Teensy 4.1 consumes approximately 100 mA at 600 MHz, so retaining one MCU on each of the five modules would require roughly

IMCU,total ≈ 500 mA

or

PMCU,total ≈ 1.65W.

FSR divider losses are more dependent on contact conditions, but under a simple 3.3 V voltage-divider assumption, one actively loaded taxel may already dissipate power on the order of sub-mW to about 1 mW. This suggests that aggregate FSR losses may also become significant when many taxels are simultaneously engaged.

These values are only preliminary estimates, but they already indicate that controller-side power is likely to dominate over accelerometer power, while FSR readout losses may become relevant under dense contact conditions. The estimates will be refined through direct measurements in O2.2 and O2.3.

## Appendix

### A. Additional Hardware Information

Table A1: Summary of key hardware parameters of the baseline modular multi-layer e-skin platform.

Parameter | Value | Notes
Prototype size | 120 × 120 × 25 mm | Overall e-skin dimensions.
Silicone materials | Ecoflex 00-31, DragonSkin 30A | Soft and relatively stiff embodiments.
FSR layers | 2 × 16 × 16 arrays | 512 taxels in total.
FSR cell size | 2 × 2 mm² | With 1 mm pitch.
Accelerometer layer | 4 × 4 LIS3DH array | 16 sensors and 48 channels in total.
Accelerometer spacing | 15 mm | Inter-sensor spacing.
LIS3DH size | 3 × 3 mm² | Sensor footprint.
LIS3DH sensitivity | 0.98 mg/LSB | Reported in the prototype paper.
LIS3DH range | ±16g | Dynamic range.
Microcontroller | Teensy 4.1 | Main acquisition unit.
Clock speed | 600 MHz | Supports synchronized high-rate sampling.
Sampling rate | 700 Hz | For FSR and accelerometer acquisition.
Communication | USB HS, 480 Mbit/s | Real-time host streaming.
FSR readout | Demux + 16-channel ADC | Matrix-scanned architecture.
Accelerometer bus | SPI | Selected over I²C for speed.

### B. Latent Filter Algorithm Pseudocode

Algorithm B1 Training logic of the action-conditioned Latent Filter

Require: tactile observations o1:T , action observations a1:T , parameters θ, ψ, ϕ
Require: encoder qψ(zt | ot), inference model qϕ(yt | zt−1, yt−1, at−1)
Require: dynamics model pθ(zt | zt−1, yt, at), decoder pθ(ot | zt)
Ensure: trained latent filter parameters
1: Initialize θ, ψ, ϕ
2: for each training epoch do
3: | for each sequence (o1:T , a1:T ) do
4: | Initialize z0, y0
5: | L ← 0
6: | for t = 1 to T do
7: | (µzt , σzt
| ) ← qψ(zt | ot) | ▷ encode tactile observation
8: | if t > 1 then
9: | (µyt , σyt
| ) ← qϕ(yt | zt−1, yt−1, at−1) | ▷ infer hidden latent state
10: | pθ(zt | zt−1, yt, at) | ▷ predict latent prior
11: | q
| filt(zt) ← BayesFuse(qψ(zt | ot), pθ(zt | zt−1, yt, at)) | ▷ Bayesian integration
12: | else
13: | q
| filt(zt) ← qψ(zt | ot) | ▷ use encoder output directly
14: | end if
15: | zt ∼ q
| filt(zt) | ▷ sample filtered latent variable
16: | oˆt ∼ pθ(ot | zt) | ▷ reconstruct tactile observation
17: | Lrec ← − log pθ(ot | zt) | ▷ reconstruction loss
18: | if t > 1 then
19: | Lz ← KL q filt(zt) ∥ pθ(zt | zt−1, yt, at)
| | ▷ latent dynamics regularization
20: | Ly ← KL(qϕ(yt | ·) ∥ p(yt | at, N)) | ▷ hierarchical prior regularization
21: | else
22: | Lz ← 0, Ly ← 0
23: | end if
24: | L ← L + Lrec + Lz + Ly
25: | end for
26: | Update θ, ψ, ϕ using Adam and backpropagation
27: | end for
28: end for

### C. Comparision between different modular e-skin prototype

Table A2: Comparison of representative modular e-skin systems from the perspective of scalability

Image | Prototype | Data scalability | Power scalability | Calibration scalability
ROBOSKIN Ohmura 2006 [44] | Curved-surface scalability | N/A | N/A
Cannata 2008 [46] | Embedded humanoid skin | Low-power optical design | N/A
Mittendorfer 2011 [42] | Local preprocessing | Active tactile modules | N/A
Maiolino 2013 [21] | Large-area patch tiling | N/A | Thermal-drift compensation
ProxySKIN 2024 [13] | EtherCAT-based distributed sensing | N/A | N/A
TacSuit 2024 [10] | Hierarchical event fusion | Local computing MCU | N/A
Xue 2025 [6] | Adjustable module size | N/A | N/A

Hierarchical Safety Framework
2024 [62]
Whole-body sensing | N/A | N/A
Living Layers 2025 [40] | Layered modular construction | N/A | N/A
Full-body Modular E-skin 2025 [45] | Full-body deployment | N/A | N/A

Modular Multi-Layer e-Skin 2025 [23]

Prototype-level multimodal DAQ | Prototype-level only | Prototype-level only

23

Table A3: Comparison of representative modular e-skin systems

Image | Prototype | Module form | Multilayer | Function | Sensors | Main characteristics

ROBOSKIN Ohmura
2006 [44]
Conformal patch | No | Curved-surface touch; conformal coverage
Pressure-sensitive tactile elements | Conformal scalable skin for
curved robot surfaces
Cannata 2008 [46] | Triangular cell | No | Whole-body touch; contact detection
Embedded artificial skin sensing elements

Early embedded humanoid
skin
Mittendorfer 2011 [42] | Hexagonal cell | No | Contact detection; multimodal tactile sensing
Multimodal tactile sensing module | Local preprocessing
Maiolino 2013 [21] | Triangular cell | No | Normal pressure; large-area touch
Capacitive tactile taxels | Robust patch tiling
ProxySKIN 2024 [13] | Triangular cell | No | Contact sensing; pre-contact detection; HRI
Tactile sensors + ToF proximity sensors

Multi-modal HRI skin

TacSuit 2024 [10] | Hexagonal cell | No | Pressure; proximity; vibration; temperature; collision detection
Pressure sensor, proximity sensor, accelerometer, temperature sensor

Hierarchical event fusion

Xue 2025 [6] | Rectangular cell | No | Collision detection; robot body touch
Multimodal flexible e-skin sensors | Adjustable module size

Hierarchical Safety
Framework 2024 [62]
Irregular patch | No | Whole-body safety monitoring; contact-aware robot safety
Whole-body tactile sensors | Hierarchical safety framework
Living Layers 2025 [40] | Layered patch | Yes | Modular e-skin construction | Bacterial-cellulose-based modular e-skin platform
Biofabricated layering

Full-body Modular E-skin
2025 [45]
Irregular patch | No | Whole-body touch; tactile gesture recognition

Pressure sensing points + pose information

Geometry-aware full body

Modular Multi-Layer e-Skin 2025 [23]

Multi-layer patch | Yes | Normal pressure; vibration; embodied tactile perception
FSR array + accelerometer layer | Core project platform

24

### D. Summary of differnet protocols

Table A4: Comparison of mainstream transmission protocols

Protocol | Bandwidth Max data rate | Signal wires Typical topology / distance | Key features
I²C | Low to medium 100 kb/s, 400 kb/s, 1 Mb/s, 3.4 Mb/s
2 | Short-distance, multi-drop
| | bus | Low pin count; easy expansion; low speed
I3C | Medium | 12.5 Mb/s SDR | 2 | Short-distance sensor bus | Higher speed; backward-compatible; efficient bus management
SPI | Medium to high
Typically up to tens of Mb/s 4 | Short-distance point-to-point
| | | | or multi-slave | High speed; full duplex; simple protocol
UART | Low to
medium

Typically kb/s to several
Mb/s
2 | Point-to-point, short to
medium distance

Simple interface; no clock; low complexity

CAN FD | Medium | 1 Mb/s arbitration, up to 8 Mb/s data phase
| | 2 | Differential multi-drop bus | Robust; anti-interference; good error detec- tion
RS-485 | Medium | Up to 10 Mb/s at short distance
2 or 4 | Long-distance differential bus Long range; strong noise immunity; indus-
| | | | trial use
USB 2.0 | High | 1.5 Mb/s, 12 Mb/s, 480 Mb/s 2 | Host-device, short cable | Plug-and-play; mature ecosystem; moderate complexity
USB 3.2 | Very high | 5 Gb/s, 10 Gb/s, 20 Gb/s | Depends on
| | connector | Host-device, short cable | Very high throughput; complex PHY

100BASE-TX
Ethernet
High | 100 Mb/s | 4 | Switched network, up to 100 m
Mature standard; reliable; network capable

1000BASE-

T Ethernet Very high | 1 Gb/s | 8 | Switched network, up to 100 m | High throughput; scalable; complex hardware

25

### E. Risk Metric

Table A5: Main project risks and mitigation strategies. Likelihood and impact are scored on a 1–5 scale, and the risk score is calculated
as L × I. Risk | Why it happens | L × I | Mitigation
Data dropouts | bandwidth spikes, host buffering, or
framing errors during continuous acquisition
3 × 4 = 12 | use fixed-size frames, CRC, ring buffers, and stress-test log-
ging before full integration
Timing jitter | non-deterministic firmware scheduling
and asynchronous acquisition paths
3 × 4 = 12 | use timer-driven acquisition, DMA where possible, and ex-
plicit timestamp validation
Noisy force readings | ADC reference instability, ground
bounce, and analog–digital interference
3 × 3 = 9 | separate analog and digital domains, improve grounding, and
add filtering and shielding if needed

Calibration does not
transfer

silicone assembly variance, layer shift, and reassembly inconsistency

4 × 4 = 16 | log full calibration metadata, add an alignment step, and
evaluate repeatability after reassembly

Multi-patch scaling fails bus contention, synchronization drift, and increased communication overhead

3 × 5 = 15 | use shared synchronization, deterministic framing, and vali-
date bandwidth limits early with DTM

PCB bring-up failure or
fabrication delay

miniaturisation may require more than one board spin, while fabrication and assembly delays can accumulate

4 × 5 = 20 | plan for at least two board spins, place the second order be-
fore full debugging of the first, and keep a fallback test board if possible

Silicone mould or
sensor-layer
misalignment

shrinking the footprint increases assembly sensitivity and makes layer registration more difficult

4 × 4 = 16 | introduce alignment features in the mould, use assembly jigs,
and verify registration before final bonding

FPGA toolchain
ramp-up

FPGA development adds learning overhead, bring-up risk, and debugging complexity compared with MCU-only designs

3 × 4 = 12 | start toolchain learning early, validate a minimal FPGA data path first, and keep the MCU option as a fallback

26

### E. Evaluation Metrics

Table A6: Evaluation metrics for O1 data scalability.

Obj. | Metric | Protocol | Acceptance criterion | Statistical test
O1.1 | Streaming success rate | 10 repeated multimodal streaming runs, each lasting 10 min, from the integrated five-module patch at 700 Hz. | ≥ 9/10 successful runs, with no unrecoverable failure. | Descriptive statistics.
O1.2 | Frame drop rate / jitter / CRC failure
3 long-duration runs, each lasting 50 min, under nominal load.

Frame drop < 1%, p95
inter-frame time < 1.5×
nominal period, CRC failure rate = 0.

Paired t-test or Wilcoxon.

O1.3 | Inter-modal alignment error | 30 shared physical events, repeated across 3 runs, using controlled tapping or press–release actions.

Median FSR–accelerometer lag < 5 ms, with no systematic drift.

Wilcoxon or paired t-test.

O1.4 | Host CPU usage / logging
stability

3 logging runs, each lasting 50 min, under nominal load and replayed higher traffic load.

Mean CPU usage < 70%, p95
CPU usage < 85%, no
dropped-write events.

Repeated-measures
ANOVA | or | Friedman
test.

27

Table A7: Evaluation metrics for O2 power scalability.

Obj. | Metric | Protocol | Acceptance criterion | Statistical test
O2.1 | Stable power delivery | 3 continuous runs of 30 min under full five-module operation, with rail voltage and current logged throughout. | No brownout or reset. Rail variation within ±5% of nominal voltage. | Descriptive statistics.
O2.2 | Current draw vs sampling rate | Measure current at 100, 300, 500, and
700 Hz, using 10 min runs at each condition.

Current increases
approximately linearly with sampling rate, with no unstable jump between adjacent settings.
Linear | regression | and
repeated-measures
ANOVA | or | Friedman
test.
O2.3 | Current draw vs enabled
modules

Measure current with 1, 2, 3, 4, and 5 modules enabled, using 10 min runs at each condition.

Current increases
approximately linearly with enabled module count.
Linear | regression | and
repeated-measures
ANOVA | or | Friedman
test.
O2.4 | Dual-patch power budget
suitability

Estimate total power from measured single-patch results and validate with one 20 min emulated dual-patch load test if feasible.

Projected dual-patch power remains within supply budget, with at least 20% margin.

Descriptive analysis.

28

Table A8: Evaluation metrics for O3 calibration scalability.

Obj. | Metric | Protocol | Acceptance criterion | Statistical test
O3.1 | Calibration repeatability | Repeat the full calibration procedure 3 times on the same five-module patch, with identical loading conditions and 10 test samples per module. | Inter-run calibration variation remains below 10%. | Repeated-measures
ANOVA | or | Friedman
| | | | test.
O3.2 | Synchronization calibration
error

Apply 30 shared physical events across 3 runs and compare the calibrated temporal offset between FSR and accelerometer signals.

Median residual
synchronization error remains below 5 ms.

Wilcoxon signed-rank
test or paired t-test.
O3.3 | Inter-module variation | Apply the same reference load to all 5
modules and compare normalized output before and after calibration.

Post-calibration inter-module variation remains below 10%.

One-way | ANOVA | or
Kruskal–Wallis test.
O3.4 | Post-reassembly performance retention
Disassemble and reassemble the patch 3 times, recalibrate, and evaluate force-regression performance using the same test protocol as H1.

Post-calibration performance remains within 20% of the
baseline prototype.

Paired t-test or Wilcoxon
signed-rank test.

29

Table A9: Evaluation metrics for O4 reference design package.

Obj. | Metric | Protocol | Acceptance criterion | Statistical test
O4.1 | Architecture package completeness | Review whether the electronics architecture, firmware workflow, and calibration procedure are all documented in one package. | All three components are documented and cross-referenced in a reusable form. | Checklist-based review.
O4.2 | Reproducibility of design documentation

A second reader follows the documentation to trace the module design, patch integration steps, and validation workflow.

≥ 90% of required steps can be reproduced without additional clarification.

Descriptive analysis.

O4.3 | Coverage of validation results | Check whether the package includes summarized results for data, power, and calibration validation.

Results from O1, O2, and O3 are all included and clearly linked to the corresponding objectives.

Checklist-based review.

O4.4 | Toolkit usability for future iterations

Review whether the final package includes reusable design files, procedures, and parameter records for later patch or multi-patch extension.

The toolkit supports at least one future single-patch iteration and provides sufficient
information for later
multi-patch extension.

Descriptive analysis.

30

## References

[1] Mark H. Lee. Tactile sensing: New directions, new challenges. The International Journal of Robotics Research, 19(7):636–643, 2000.
[2] Robert D. Howe. Tactile sensing and control of robotic manipulation. Advanced Robotics, 8(3):245–261, 1993.
[3] N. Yogeswaran, W. Dang, W.T. Navaraj, D. Shakthivel, S. Khan, E.O. Polat,
S. Gupta, H. Heidari, M. Kaboli, L. Lorenzelli, G. Cheng, and R. Dahiya. New materials and advances in making electronic skin for interactive robots. Advanced Robotics, 29(21):1359–1373, 2015.
[4] Xuemei Fu, Wen Cheng, Guanxiang Wan, Zijie Yang, and Benjamin C. K. Tee. Toward an ai era: Advances in electronic skins. Chemical Reviews, 124(17):9899– 9948, 2024.
[5] Elisabetta Leogrande, Mariangela Filosa, Sara Ballanti, Luca De Cicco, Stefano Mazzoleni, Rochelle Ackerley, Calogero Maria Oddo, and Francesco Dell’Olio. Electronic skin technologies: From hardware building blocks and tactile sensing to control algorithms and applications. Sensors and Actuators Reports, 9:100312, 2025.
[6] Guangming Xue, Guodong Chen, Lining Sun, and Huicong Liu. Multimodal flexible electronic skin with adjustable module size for robot collision detection. Industrial Robot: the international journal of robotics research and application, 52(2):258–265, 10 2024.
[7] Philipp Mittendorfer and Gordon Cheng. Integrating discrete force cells into multimodal artificial skin. In 2012 12th IEEE-RAS International Conference on Humanoid Robots (Humanoids 2012), pages 847–852, Nov 2012.
[8] P. Mittendorfer, E. Yoshida, and G. Cheng. Realizing whole-body tactile interactions with a self-organizing, multi-modal artificial skin on a humanoid robot. Advanced Robotics, 29(1):51–67, 2015.
[9] Qian Xu, Boyang Zhang, Yik Kin Cheung, Zhiwei Yang, Rui Jiao, Shuhuai Yao, Wei Hong, and Hongyu Yu. A bio-inspired origami capacitive robotic e-skin with multimodal sensing capabilities. npj Flexible Electronics, 2026.
[10] Tacsuit: A wearable large-area, bioinspired multimodal tactile skin for collaborative robots. IEEE Transactions on Industrial Electronics, 71(2):1708–1717, Feb 2024.
[11] Hakhyun Lim, Jungrak Choi, Chankyu Han, Dabin Kim, Hanbit Jin, Minki Kim, Yunjeong Kim, Jinhyeok Yang, Saerom Seo, Jaehoon Jung, Hunpyo Ju, Chan-Hwa Hong, Dongyoung Lee, Junseong Ahn, and Hye Jin Kim. Scalable in-situ fabrication of multimodal electronic skin for intelligent robotics and interactive systems. npj Flexible Electronics, 10(1):34, 2026.
[12] Chenhui Bai, Xinyu Dong, Quyang Liu, Ming Zhao, Kun Yang, Yu Niu, Hulin Zhang, and Wei Zhai. A self-powered hydrogel electronic skin with decoupled multimodal sensing for closed-loop human-machine interactions. Nature Communications, 17(1):2675, 2026.

[13] Francesco Giovinazzo, Francesco Grella, Marco Sartore, Manuela Adami, Riccardo Galletti, and Giorgio Cannata. From cyskin to proxyskin: Design, implementation and testing of a multi-modal robotic skin for human–robot interaction. Sensors (Basel, Switzerland), 24, 2024.
[14] Shahbaz Youssefi, Simone Denei, Fulvio Mastrogiovanni, and Giorgio Cannata. Skinware: A real-time middleware for acquisition of tactile data from large scale robotic skins. In 2014 IEEE International Conference on Robotics and Automation (ICRA), pages 6421–6426, May 2014.
[15] Beibei Shao, Ming-Han Lu, Tai-Chen Wu, Wei-Chen Peng, Tien-Yu Ko, Yung-Chi Hsiao, Jiann-Yeu Chen, Baoquan Sun, Ruiyuan Liu, and Ying-Chih Lai. Large-area, untethered, metamorphic, and omnidirectionally stretchable multiplexing self-powered triboelectric skins. Nature Communications, 15(1):1238, 2024.
[16] Xiao Chen, Youzhi Zhang, Jinmiao Chen, Haibin Wang, Luchuan Yu, and Xizhang Chen. Full-textile less-wires large-area flexible robot electronic skin for human–robot interaction. IEEE Sensors Journal, 26(2):1705–1715, Jan 2026.
[17] Ana Clara Pereira Resende da Costa, Mariangela Filosa, Alcimar Barbosa Soares, and Calogero Maria Oddo. Type ii mechanoreceptors and cuneate spiking neuronal network enable touch localization on a large-area e-skin. Nature Machine Intelligence, 7(8):1278–1291, 2025.
[18] Alexander Schmitz, Perla Maiolino, Marco Maggiali, Lorenzo Natale, Giorgio Cannata, and Giorgio Metta. Methods and technologies for the implementation of large-scale robot tactile sensors. IEEE Transactions on Robotics, 27(3):389–400, June 2011.
[19] Florian Bergner, Emmanuel Dean, and Gordon Cheng. Design and realization of an efficient large-area event-driven e-skin. Sensors, 20:1965, 03 2020.
[20] Yulong Li, Peng Cheng, Jinhua Hong, Yuting Wang, Xiaokai Wang, Lieen Guo, and Jizhong Liu. Large-area high-resolution skin-inspired flexible tactile sensor for robotic electronic skin. ACS Applied Electronic Materials, 7(19):8861–8870, 2025.
[21] Perla Maiolino, Marco Maggiali, Giorgio Cannata, Giorgio Metta, and Lorenzo Natale. A flexible and robust large scale capacitive tactile system for robots. IEEE Sensors Journal, 13(10):3910–3917, Oct 2013.
[22] Ravinder Dahiya, Nivasan Yogeswaran, Fengyuan Liu, Libu Manjakkal, Etienne Burdet, Vincent Hayward, and Henrik J¨orntell. Large-area soft e-skin: The challenges beyond sensor designs. Proceedings of the IEEE, 107(10):2016–2033, Oct 2019.
[23] Alexis WM Devillard, Anirvan Dutta, Zhihuan Zhang, Xiaoxiao Cheng, Mohsen Kaboli, and Etienne Burdet. Modular, multi-layer e-skin for robotics investigations and applications. In 2025 IEEE World Haptics Conference (WHC), pages 15–23, July 2025.
[24] Anirvan Dutta, Alexis W. M. Devillard, Zhihua Zhang, Xiaoxiao Cheng, and Etienne Burdet. Embodied tactile perception of soft objects properties. npj Robotics, 4(1):15, 2026.

[25] Andrea Ortone, Mariangela Filosa, Giacomo Indiveri, Giuseppe Desoli, Alberto Mazzoni, and Calogero Maria Oddo. Bioinspired spiking architecture enables energy constrained touch encoding. Nature Communications, 17(1):2108, 2026.
[26] Fengyuan Liu, Sweety Deswal, Adamos Christou, Yulia Sandamirskaya, Mohsen Kaboli, and Ravinder Dahiya. Neuro-inspired electronic skin for robots. Science Robotics, 7(67):eabl7344, 2022.
[27] Florian Bergner, Philipp Mittendorfer, Emmanuel Dean-Leon, and Gordon Cheng. Event-based signaling for reducing required data rates and processing power in a large-scale artificial robotic skin. In 2015 IEEE/RSJ International Conference on Intelligent Robots and Systems (IROS), pages 2124–2129, Sep. 2015.
[28] Joan Kangro, Anand Vazhapilli Sureshbabu, Silvio Traversaro, Daniele Pucci, and Francesco Nori. A plenum-based calibration device for tactile sensor arrays. IEEE Robotics and Automation Letters, 3(4):3937–3943, Oct 2018.
[29] Robert A. Nawrocki, Naoji Matsuhisa, Tomoyuki Yokota, and Takao Someya. 300-nm imperceptible, ultraflexible, and biocompatible e-skin fit with tactile sensors and organic transistors. Advanced Electronic Materials, 2(4):1500452, 2016.
[30] Arielle Berman, Baiyu Shi, Tomasz Zaluska, Annika Yong, Sean Clees, Chengyi Xu, Levent Beker, and Zhenan Bao. A skin-inspired, capacitive array for tactile modulus detection via a scalable rigid-island architecture. npj Flexible Electronics, 10(1):5, 2025.
[31] Zhou Lu, Yuan Su, Qi Ye, Ze Wang, Xiufang Shi, Gaofeng Li, and Jiming Chen. A low-cost super-resolution tactile sensor: Design, fabrication, and validation. IEEE Sensors Journal, 24(22):36518–36529, Nov 2024.
[32] M. Raibert. An all digital vlsi tactile array sensor. In Proceedings. 1984 IEEE International Conference on Robotics and Automation, volume 1, pages 314–319, March 1984.
[33] V.J. Lumelsky, M.S. Shur, and S. Wagner. Sensitive skin. IEEE Sensors Journal, 1(1):41–51, June 2001.
[34] Raunaq M. Bhirangi, Tess Lee Hellebrekers, Carmel Majidi, and Abhinav Kumar Gupta. Reskin: versatile, replaceable, lasting tactile skins. In Conference on Robot Learning, 2021.
[35] Mike Lambeta, Po-Wei Chou, Stephen Tian, Brian Yang, Benjamin Maloon, Victoria Rose Most, Dave Stroud, Raymond Santos, Ahmad Byagowi, Gregg Kammerer, Dinesh Jayaraman, and Roberto Calandra. Digit: A novel design for a low-cost compact high-resolution tactile sensor with application to in-hand manipulation. IEEE Robotics and Automation Letters, 5(3):3838–3845, July 2020.
[36] Jeremy A. Fishel and Gerald E. Loeb. Sensing tactile microvibrations with the biotac — comparison with human sensitivity. In 2012 4th IEEE RAS EMBS International Conference on Biomedical Robotics and Biomechatronics (BioRob), pages 1122–1127, June 2012.
[37] Wenzhen Yuan, Siyuan Dong, and Edward H. Adelson. Gelsight: High-resolution robot tactile sensors for estimating geometry and force. Sensors, 17(12), 2017.

[38] S.I. Yaniger. Force sensing resistors: A review of the technology. In Electro International, 1991, pages 666–668, April 1991.
[39] Z. Chu, P.M. Sarro, and S. Middelhoek. Silicon three-axial tactile sensor. In Proceedings of the International Solid-State Sensors and Actuators Conference - TRANS-DUCERS ’95, volume 1, pages 656–659, June 1995.
[40] Maximilian Krieger, Madalina Nicolae, and J¨urgen Steimle. Living layers: Designing modular e-skin with bacterial cellulose. In Proceedings of the Nineteenth International Conference on Tangible, Embedded, and Embodied Interaction, TEI ’25, New York, NY, USA, 2025. Association for Computing Machinery.
[41] Xuewen Wang, Yang Gu, Zuoping Xiong, Zheng Cui, and Ting Zhang. Silk-molded flexible, ultrasensitive, and highly stable electronic skin for monitoring human physiological signals. Advanced Materials, 26(9):1336–1342.
[42] Philipp Mittendorfer and Gordon Cheng. Humanoid multimodal tactile-sensing modules. IEEE Transactions on Robotics, 27(3):401–410, June 2011.
[43] Mallory L. Hammock, Alex Chortos, Benjamin C.-K. Tee, Jeffrey B.-H. Tok, and Zhenan Bao. 25th anniversary article: The evolution of electronic skin (e-skin): A brief history, design considerations, and recent progress. Advanced Materials, 25(42):5997–6038, 2013.
[44] Y. Ohmura, Y. Kuniyoshi, and A. Nagakubo. Conformable and scalable tactile sensor skin for curved surfaces. In Proceedings 2006 IEEE International Conference on Robotics and Automation, 2006. ICRA 2006., pages 1348–1353, May 2006.
[45] Shuo Jiang, Boce Hu, Linfeng Zhao, and Lawson L. S. Wong. Robot tactile gesture recognition based on full-body modular e-skin. CoRR, abs/2506.18256, 2025.
[46] Giorgio Cannata, Marco Maggiali, Giorgio Metta, and Giulio Sandini. An embedded artificial skin for humanoid robots. In 2008 IEEE International Conference on Multisensor Fusion and Integration for Intelligent Systems, pages 434–438, Aug 2008.
[47] Mahesh Soni and Ravinder Dahiya. Soft eskin: distributed touch sensing with harmonized energy and computing. Philosophical Transactions of the Royal Society A: Mathematical, Physical and Engineering Sciences, 378(2164):20190156, 12 2019.
[48] Kuniharu Takei, Wei Gao, Chuan Wang, and Ali Javey. Physical and chemical sensing with electronic skin. Proceedings of the IEEE, 107(10):2155–2167, Oct 2019.
[49] Chiara Bartolozzi, Paolo Motto Ros, Francesco Diotalevi, Nawid Jamali, Lorenzo Natale, Marco Crepaldi, and Danilo Demarchi. Event-driven encoding of off-theshelf tactile sensors for compression and latency optimisation for robotic skin. In 2017 IEEE/RSJ International Conference on Intelligent Robots and Systems (IROS), pages 166–173, Sep. 2017.
[50] Jie Wen, Chenxing Xiang, Lidan Zhang, Xuewei Shi, Shuqin Zhou, Ting Fan, Huiming Ning, Shu Wang, Kaiyan Huang, Alamusi Lee, Lingxiao Gao, E. Cheng, Ziying Wang, Kexu An, Mengmeng Yang, and Ning Hu. Recent advances in i/e-skin: mechanism, signal processing, and applications. Nano Materials Science, 2025.
[51] Tareq Assaf. A frequency modulation-based taxel array: A bio-inspired architecture for large-scale artificial skin. Sensors, 21:5112, 07 2021.

[52] Zhicheng Cao, Yijing Xu, Shifan Yu, Zijian Huang, Yu Hu, Lin Wansheng, Huasen Wang, Yanhao Luo, Yuanjin Zheng, Zhong Chen, Qingliang Liao, and Xinqin Liao. A programmable electronic skin with event-driven in-sensor touch differential and decision-making. Advanced Functional Materials, 35, 09 2024.
[53] Gaishan Li, Zhengnan Fu, Anubhab Tripathi, Junyi Yang, and Arindam Basu. An event-driven e-skin system with dynamic binary scanning and real time snn classification. 2026.
[54] Ariel Slepyan and Nitish Thakor. Towards scalable soft e-skin: Flexible event-based tactile-sensors using wireless sensor elements embedded in soft elastomer. In 2020 8th IEEE RAS/EMBS International Conference for Biomedical Robotics and Biomechatronics (BioRob), pages 334–339, Nov 2020.
[55] Chen Gao and Sabari Kannan Muthalagu. How to synchronize the timing between chips with programmable real-time unit. Application Note SPRADQ5, Texas Instruments, March 2025. Texas Instruments Application Note.
[56] Bo Xue, Zhitian Li, Pengyu Lei, Yingzi Wang, and Xudong Zou. Wicsync: A wireless multi-node clock synchronization solution based on optimized uwb two-way clock synchronization protocol. Measurement, 183:109760, 2021.
[57] Yueqi Wang, Tangyou Liu, Licheng Feng, Jinze Wang, Yang Yang, Jianjun Bao, Binghao Li, and Liao Wu. Hardware-based time synchronization for a multi-sensor system. pages 4600–4607, 10 2024.
[58] Lowiek Stockt, Remko Proesmans, and Francis wyffels. Automatic calibration for an open-source magnetic tactile sensor. 05 2024.
[59] Rudra Mukherjee, Priyanka Ganguly, and Ravinder Dahiya. Bioinspired distributed energy in robotics and enabling technologies. Advanced Intelligent Systems, 5(4):2100036, 2023.
[60] C.H. Wu, H.R. Wang, A.L. Liu, Z.H. Xie, Y.H. Deng, and Y. Zhang. Failure analysis of titanium honeycomb sandwich structures subjected to three-point bending in hightemperature condition. Engineering Failure Analysis, 165:108735, 2024.
[61] T. C. Hales. The honeycomb conjecture. Discrete & Computational Geometry, 25(1):1–22, 2001.
[62] Shuo Jiang and Lawson L.S. Wong. A hierarchical framework for robot safety using whole-body tactile sensors. In 2024 IEEE International Conference on Robotics and Automation (ICRA), pages 8021–8028, May 2024.
