Yannas-Sun/E-skin_MSc_final_report/power scalability/archive/legacy_analysis/DATA_analysis/figures/module_voltage_drop.pdf

14 | 17 | 16 | 18

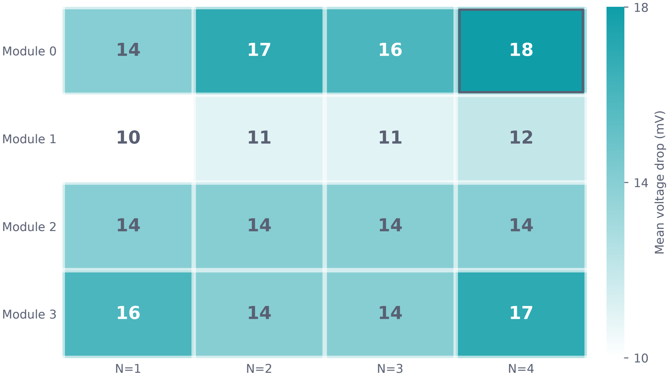
[picture p62: page 1]

N=1 | N=2 | N=3 | N=4

Module 0

Module 1

Module 2

Module 3

10 | 11 | 11 | 12
14 | 14 | 14 | 14
16 | 14 | 14 | 17

10

14

18

Mean voltage drop (mV)
