Yannas-Sun/E-skin_MSc_final_report/power scalability/archive/legacy_analysis/DATA_analysis/figures/peak_current_upper_estimate.pdf

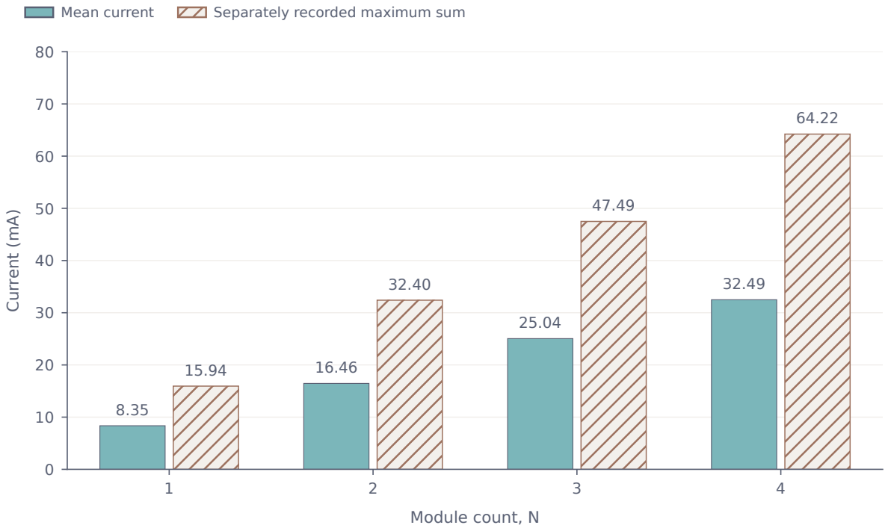
[picture p63: figure]
Module count, N; Current (mA); Mean current; Separately recorded maximum sum
