Yannas-Sun/E-skin_MSc_final_report/power scalability/archive/legacy_analysis/DATA_analysis/figures/single_module_screening.pdf

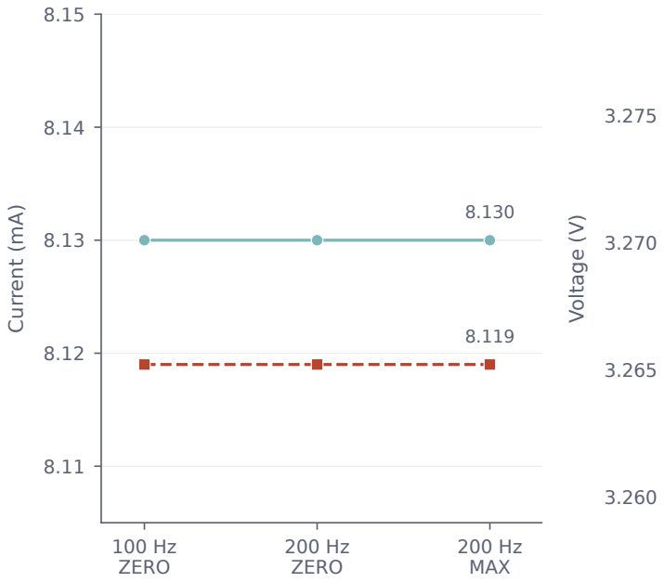
[picture p64: figure]
100 Hz ZERO; 200 Hz ZERO; 200 Hz MAX; Current (mA); Voltage (V)
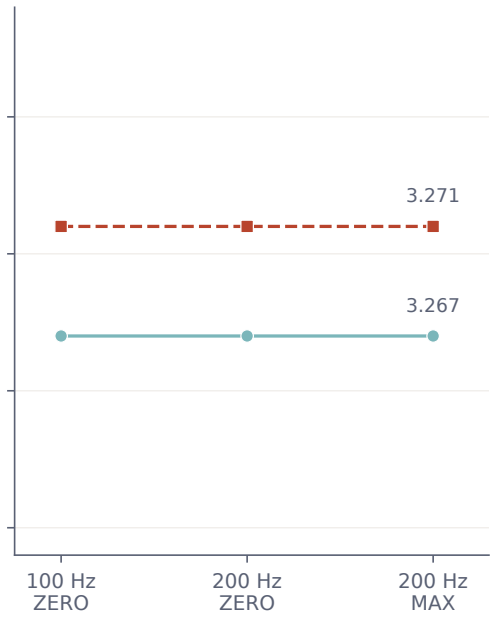
[picture p65: figure]
100 Hz ZERO; 200 Hz ZERO; 200 Hz MAX

Module 0 | Module 1
