Yannas-Sun/E-skin_MSc_final_report/power scalability/archive/legacy_analysis/DATA_analysis/figures/temperature_scaling.pdf

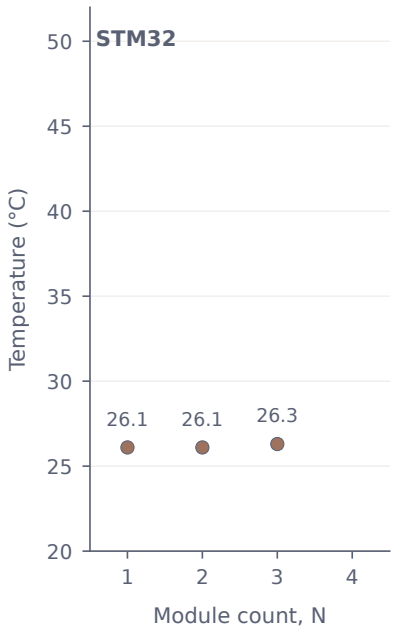
[picture p66: figure]
Module count, N; Temperature (°C); STM32

1 | 2 | 3 | 4
Module count, N

20

25

30

35

40

45

50

28.4 | 29.1 | 28.9

LM2596

1 | 2 | 3 | 4
Module count, N

20

25

30

35

40

45

50

43.6

45.3 45.7

Teensy
