Yannas-Sun/E-skin_MSc_final_report/power scalability/archive/legacy_analysis/DATA_analysis/figures/voltage_scaling.pdf

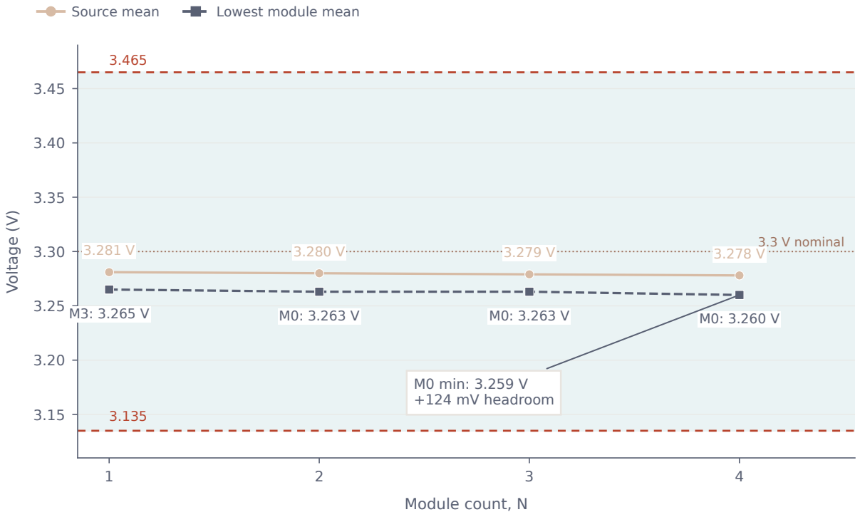
[picture p67: figure]
Module count, N; Voltage (V); 3.3 V nominal; M0 min: 3.259 V +124 mV headroom; Source mean; Lowest module mean
