Yannas-Sun/E-skin_MSc_final_report/power scalability/archive/legacy_analysis/DATA_analysis/figures/branch_current_balance.pdf

Module 0 | Module 1 | Module 2 | Module 3

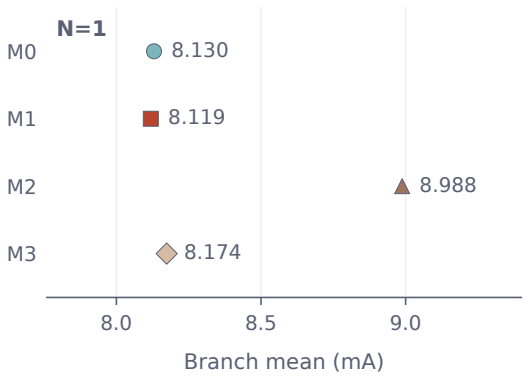
[picture p68: figure]
Branch mean (mA)
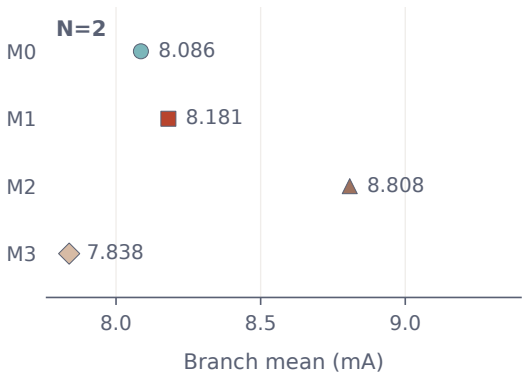
[picture p69: figure]
Branch mean (mA)
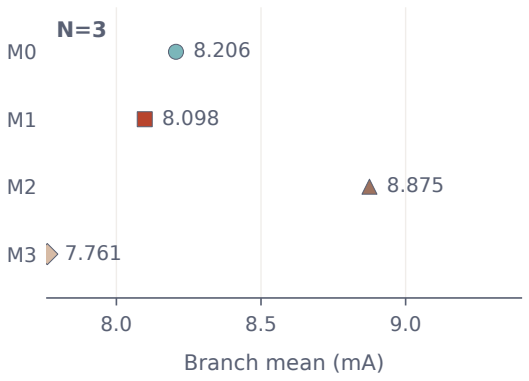
[picture p70: figure]
Branch mean (mA)
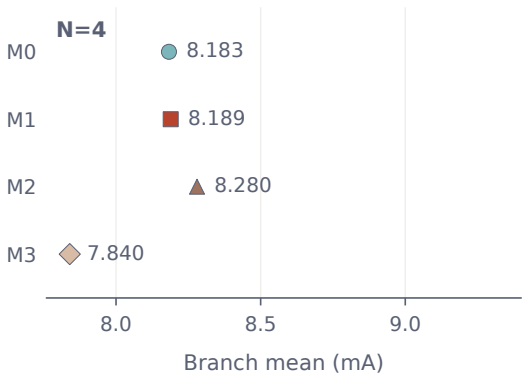
[picture p71: figure]
Branch mean (mA)
