Yannas-Sun/E-skin_MSc_final_report/power scalability/DATA/analysis/current/report_v2_8_figures/module_voltage_drop.png

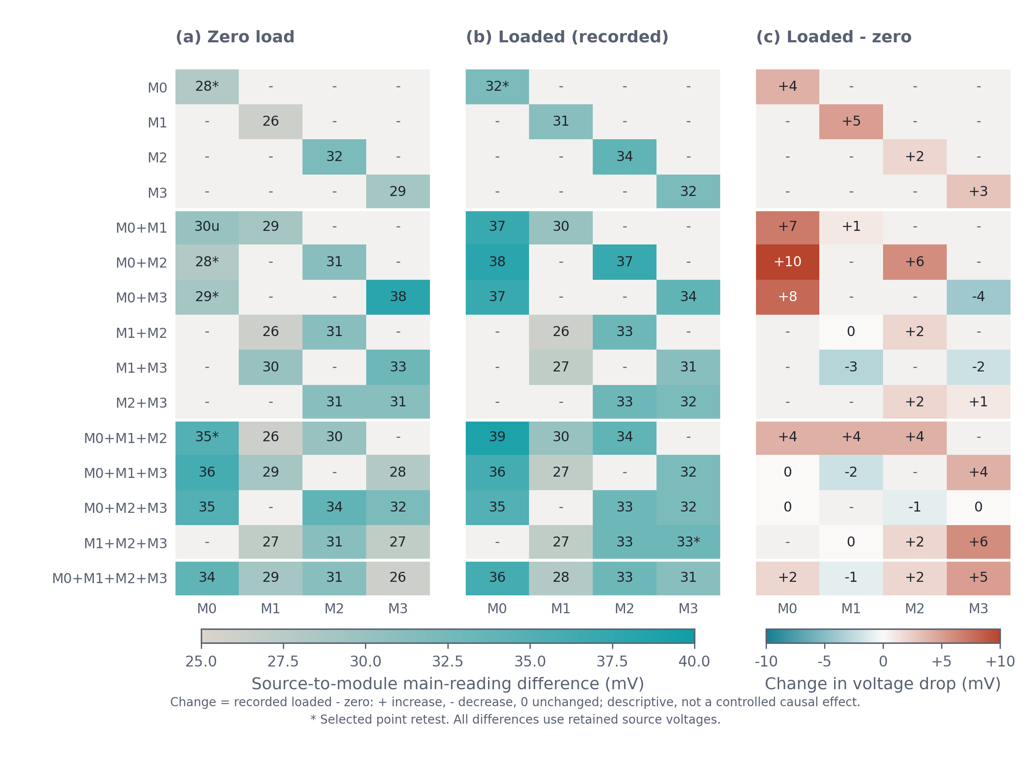
power scalability/DATA/analysis/current/report_v2_8_figures/module_voltage_drop.png
