Yannas-Sun/E-skin_MSc_final_report/power scalability/DATA/analysis/current/report_v2_8_figures/single_module_screening.png

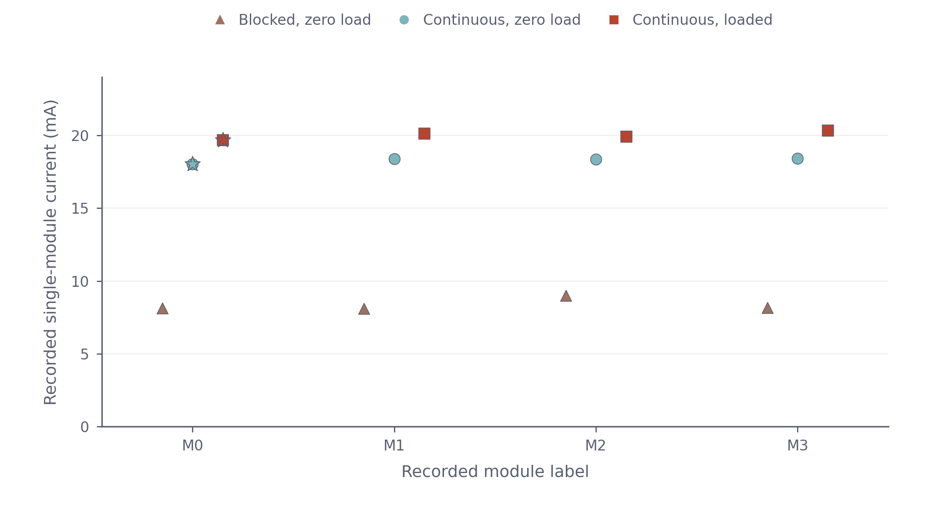
power scalability/DATA/analysis/current/report_v2_8_figures/single_module_screening.png
