Yannas-Sun/E-skin_MSc_final_report/power scalability/DATA/reference/report_v2_4_figures/temperature_scaling.png

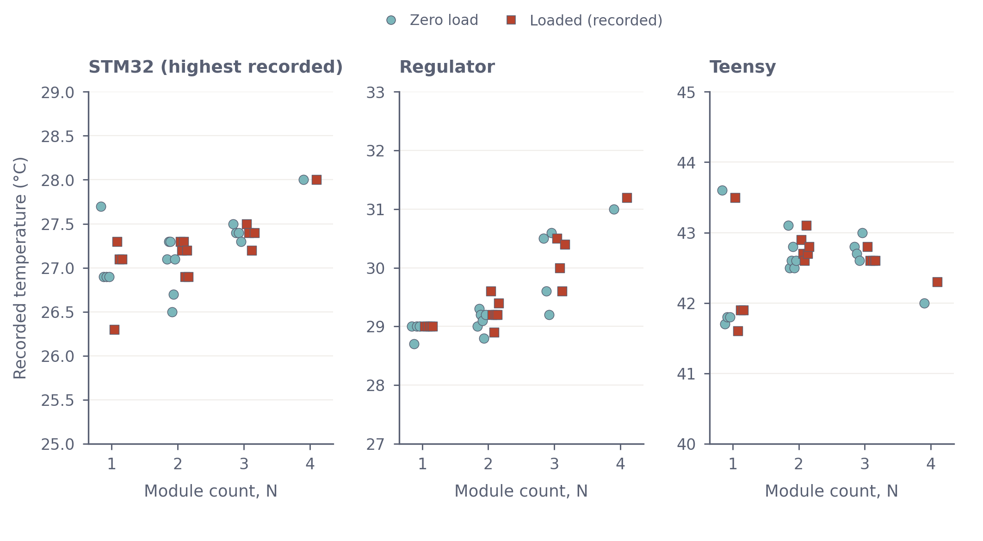
power scalability/DATA/reference/report_v2_4_figures/temperature_scaling.png
