Yannas-Sun/E-skin_MSc_final_report/data scalability/analysis/20260907_delta_large_area_review/run_index.csv

run_id | started_at | mode | condition | N | target_hz | modules | block | batch_id | repeat | old_relative_path | new_relative_path | duration_s | main_duration_s | main_packets | main_status | full_status | full_review_reasons | main_rate_Hz | main_Lmean_B | main_packet_Mbit_s | main_raw_arrival_Mbit_s | main_K_ESKD_mean | main_q_ESKF | main_ESKF_count | main_ESKD_count | source_local_firmware | deployment_confirmed | main_eligible | main_review_reasons | main_outer_crc_errors | main_outer_missing_sequence_numbers | main_missing_valid_expected_updates | main_interior_unassigned_raw_bytes | source_review | timing_note | replacement_batch_id | primary_matrix_selected | selection_reason | pc_max_completion_gap_ms | host_max_enqueue_gap_ms | host_packet_span_rate_Hz | independent_raw_audit | load_layers | load_description | independent_review_reasons | main_inner_sequence_events
20260907_040621_371357 | 2026-09-07T04:06:21.371357+01:00 | DELTA | large_area | 1 | 200 | M1 | 1 | BATCH_b85c7425a5b149dabf8cd9a9dcb33094 | 1 | 20260907_040621_371357 | DELTA/Dynamic_load/N=1/200Hz/M1/Large_area/Repeat_1 | 40.00260340000386 | 30.002603400003863 | 5998 | PASS | CHECK REQUIRED | initial_delta_prefix_cache_not_verifiable_from_file | 199.9159846241619 | 284.67255751917304 | 0.45528475705539073 | 0.45528475705539073 | 77.04437720625315 | 0.008169389796598866 | 49 | 5949 | four-module-variable-spi | False | False |  | 0 | 0 | 0 | 0 | 20260907_delta_large_area_review | PC maximum completion gap 106.9175 ms; bridge maximum enqueue gap 27 ms. Do not infer physical scan loss or SCK instability. |  | False | excluded_pending_independent_inner_sequence_review; original recorder PASS preserved | 106.91750000114553 | 27 | 199.91332755517035 | CHECK_inner_sequence_discontinuity | both | large_area; both layers; area/force/rhythm not recorded | inner_sequence_reset_to_2_on_ESKF | 1
20260907_040701_400114 | 2026-09-07T04:07:01.400114+01:00 | DELTA | large_area | 1 | 200 | M1 | 1 | BATCH_b85c7425a5b149dabf8cd9a9dcb33094 | 2 | 20260907_040701_400114 | DELTA/Dynamic_load/N=1/200Hz/M1/Large_area/Repeat_2 | 40.000133699999424 | 30.000133699999424 | 5950 | PASS | CHECK REQUIRED | initial_delta_prefix_cache_not_verifiable_from_file;unassigned_raw_bytes_in_full_capture | 198.33244943172085 | 269.2339495798319 | 0.427182629522756 | 0.4271828961882342 | 68.39718118526065 | 0.010252100840336134 | 61 | 5889 | four-module-variable-spi | False | False |  | 0 | 0 | 0 | 0 | 20260907_delta_large_area_review | PC maximum completion gap 55.7936 ms; bridge maximum enqueue gap 48 ms. Do not infer physical scan loss or SCK instability. |  | False | excluded_pending_independent_inner_sequence_review; original recorder PASS preserved | 55.793600011384115 | 48 | 198.33966793358672 | CHECK_inner_sequence_discontinuity | both | large_area; both layers; area/force/rhythm not recorded | inner_sequence_reset_to_2_on_ESKF | 11
20260907_040741_429011 | 2026-09-07T04:07:41.429011+01:00 | DELTA | large_area | 1 | 200 | M1 | 1 | BATCH_b85c7425a5b149dabf8cd9a9dcb33094 | 3 | 20260907_040741_429011 | DELTA/Dynamic_load/N=1/200Hz/M1/Large_area/Repeat_3 | 40.000762200012105 | 30.000762200012105 | 5979 | PASS | CHECK REQUIRED | initial_delta_prefix_cache_not_verifiable_from_file;unassigned_raw_bytes_in_full_capture | 199.29493657989755 | 262.79745776885767 | 0.41899362143522234 | 0.41899388809511406 | 66.56365779723812 | 0.0068573340023415285 | 41 | 5938 | four-module-variable-spi | False | False |  | 0 | 0 | 0 | 0 | 20260907_delta_large_area_review | PC maximum completion gap 127.6216 ms; bridge maximum enqueue gap 126 ms. Do not infer physical scan loss or SCK instability. |  | False | excluded_pending_independent_inner_sequence_review; original recorder PASS preserved | 127.62159999692813 | 126 | 199.29323909854648 | CHECK_inner_sequence_discontinuity | both | large_area; both layers; area/force/rhythm not recorded | inner_sequence_forward_gaps_on_ESKF | 2
