Yannas-Sun/E-skin_MSc_final_report/hardware/firmware/archive/legacy-components/docs/updates/README.md

# Progress update index

Progress reports are historical records, not deployment instructions. The newest dated report is the current summary for that experiment; older reports preserve the state and conclusions at their original date.

| Date | Report | Scope |
|---|---|---|
| 2026-08-30 | [Four-module FSR-only three-mode update](2026-08-30-four-module-fsr-only/PROGRESS_UPDATE.md) | FSR-only FULL/DELTA/SPATIAL path, scan-rate control, variable-length MUL1 blocks and GUI |
| 2026-08-30 | [Firmware reorganisation](2026-08-30-firmware-reorganisation/PROGRESS_UPDATE.md) | Active, research, diagnostics, simulation, archive and command classification |
| 2026-08-30 | [ACC array CMake configuration fix](2026-08-30-acc-array-cmake-fix/PROGRESS_UPDATE.md) | Standalone ACC build-cache repair |
| 2026-08-19 | [Scan-rate limitation analysis](2026-08-19-scan-rate-limit/PROGRESS_UPDATE.md) | STM32/Teensy scan-rate limits and transport roadmap |
| 2026-08-18 | [Four-module communication test](2026-08-18-four-module-communication/PROGRESS_UPDATE.md) | Four-module bridge and staged hardware validation |
| 2026-08-15 | [Four-module evaluation plan](2026-08-14-four-module-power-evaluation/PROGRESS_UPDATE.md) | Data, power, calibration and scalability test plan |
| 2026-08-12 | [ACC maximum-rate benchmark](2026-08-12-acc-rate-benchmark/PROGRESS_UPDATE.md) | Isolated ACC-rate measurement |
| 2026-08-12 | [SCLK frequency sweep](2026-08-12-sclk-frequency-sweep/PROGRESS_UPDATE.md) | ADC SCLK quality windows |
| 2026-08-12 | [Standalone FSR1 high-rate update](2026-08-12-fsr1-high-rate/PROGRESS_UPDATE.md) | High-rate FSR1 diagnostic path |
| 2026-08-11 | [Legacy SCLK scan reproduction](2026-08-11-sclk33-replication/PROGRESS_UPDATE.md) | SCLK33 reproduction and failure analysis |
| 2026-08-11 | [700 Hz fresh-scan attempt](2026-08-11-full-scan-700hz/PROGRESS_UPDATE.md) | Full-scan rate and hardware-limit result |
| 2026-08-10 | [700 Hz transport update](2026-08-10-700hz/PROGRESS_UPDATE.md) | 10 MHz HOST SPI transport experiment |
| 2026-08-10 | [80 MHz validation update](2026-08-10-80mhz/PROGRESS_UPDATE.md) | STM32 clock and NSS timing validation |
| 2026-08-10 | [Performance update](2026-08-10/PROGRESS_UPDATE.md) | DMA and ping-pong buffering |
| 2026-08-05 | [Integration update](2026-08-05/PROGRESS_UPDATE.md) | Complete-module integration |
| 2026-07-31 | [Bring-up update](2026-07-31/PROGRESS_UPDATE.md) | Initial sensor and board bring-up |

Chinese source reports, where present, remain linked by their original filenames for provenance.
