Yannas-Sun/E-skin_MSc_final_report/data scalability/data/DELTA/Dynamic_load/N=4/200Hz/M0_M1_M2_M3/Full_coverage_all_modules/Batch_after_connector_reinstallation/Repeat_3/mul1_length_over_time.png

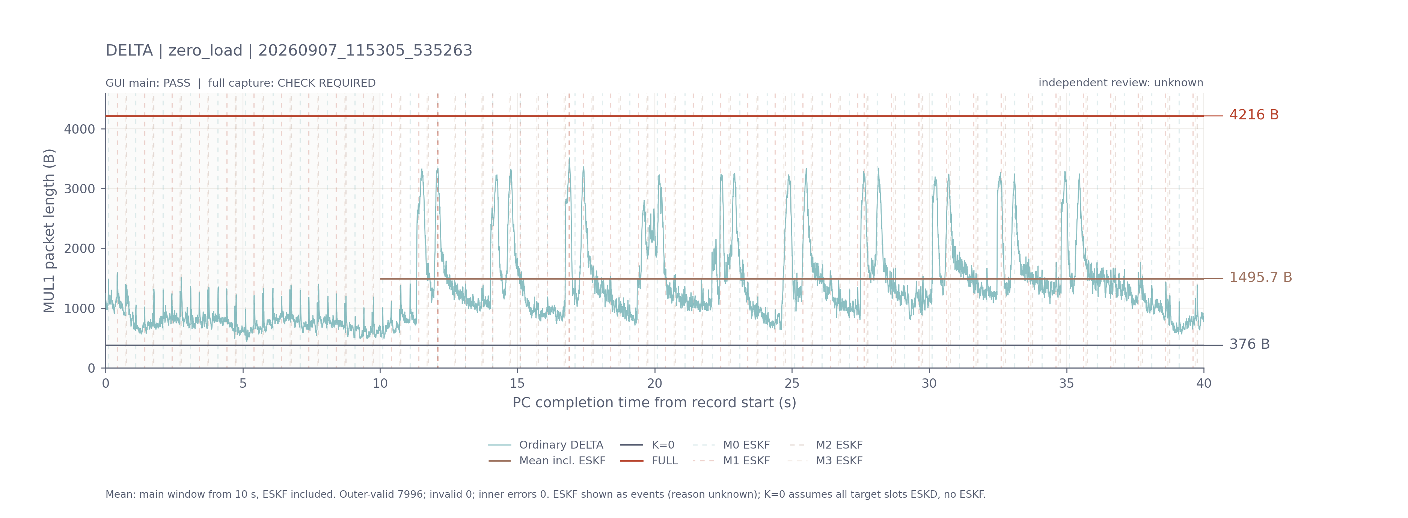
data scalability/data/DELTA/Dynamic_load/N=4/200Hz/M0_M1_M2_M3/Full_coverage_all_modules/Batch_after_connector_reinstallation/Repeat_3/mul1_length_over_time.png
