Yannas-Sun/E-skin_MSc_final_report/power scalability/DATA/raw/canonical/power_experiment_records/targeted_retests/20260907_M0-M1-M2_ZERO_M0/README.md

# Targeted M0 ZERO current retest

Current is from the preserved photograph; voltage 3.241 V is user-confirmed. New voltage MIN/MAX are not supplied.
See record.json for provenance and DATA/analysis/retest_reviews/m0_zero_retest_20260907 for comparison.
