Yannas-Sun/E-skin_MSc_final_report/data scalability/data/FULL/N=1/200Hz/M1/Repeat_1/experiment_log.md

# Experiment 20260906_230200_451593

Started: 2026-09-06T23:02:00.451593+01:00
Actual duration: 40.003054 s; requested: 40 s; settle: 10 s.
Result (main window): PASS: main window checks passed

## Conditions

```json
{
  "target_modules": [
    1
  ],
  "module_selection_source": "automatic",
  "target_mode": "FULL",
  "target_hz": 200,
  "delta_threshold": 8,
  "spi_setting_hz": 10000000,
  "condition": "zero_load",
  "block": "1",
  "repeat": "1",
  "operator": "",
  "load_protocol_id": "",
  "load_layers": "unspecified",
  "load_notes": "",
  "notes": "",
  "deployment_note": "",
  "deployment_confirmed": false,
  "board_identity_handling": "slots_only",
  "physical_modules_to_slots": {},
  "board_identity_source": "unknown_not_transmitted_by_protocol",
  "target_hz_source": "GUI default 200 Hz; not firmware readback",
  "module_detection_at_record": {
    "source": "recent_successful_protocol_slots_not_board_uids",
    "ready": true,
    "modules": [
      1
    ],
    "mode": "FULL",
    "slot_modes": {
      "1": "FULL"
    },
    "slot_last_success_monotonic": {
      "1": 185917.5495439
    },
    "last_packet_monotonic": 185917.5495439,
    "observed_at_monotonic": 185917.5495439,
    "window_span_seconds": 1.497287200007122,
    "window_seconds": 1.5,
    "stale_seconds": 0.5,
    "packet_count": 301,
    "limitation": "No response cannot establish whether a board is physically attached. The recent union can retain a briefly missing slot; recording freezes the set."
  },
  "observed_mode_at_record": "FULL",
  "observed_mul1_rate_at_record_Hz": 200.70768932103425,
  "spi_setting_source": "local firmware configuration; not measured or read back",
  "delta_threshold_source": "local firmware configuration; not measured or read back",
  "module_identity_source": "CS/IRQ slot; protocol carries no unique board identity",
  "N": 1,
  "M": 4,
  "local_provenance": {
    "source": "local_files_not_device_flash_readback",
    "firmware_variant": "four-module-variable-spi",
    "files": {
      "stm32_elf": {
        "path": "D:\\study\\programming\\ESKIN\\E-SKIN\\hardware\\new\\firmware\\active\\four-module-variable-spi\\stm32\\combined-system\\build\\Release\\ESKIN_STM32.elf",
        "sha256": "8fb1791504f3c2bf23dce9d57ca9b877b8cd1653d167dfe5a58b0c5176c4c8b6"
      },
      "teensy_hex": {
        "path": "D:\\study\\programming\\ESKIN\\E-SKIN\\hardware\\new\\firmware\\active\\four-module-variable-spi\\build\\teensy\\four_module.ino.hex",
        "sha256": "32a95ff60bef1029a8b25a62d4ece524abc97813955e6586fc50fc9bf4cd2a67"
      },
      "pc_monitor": {
        "path": "D:\\study\\programming\\ESKIN\\E-SKIN\\hardware\\new\\firmware\\active\\four-module-variable-spi\\pc\\four-module-fsr-monitor.py",
        "sha256": "f3cb2910054e26300a223cbac611e08eb4eae6ac6fa2a60ebd3c414695758949"
      },
      "pc_recorder": {
        "path": "D:\\study\\programming\\ESKIN\\E-SKIN\\hardware\\new\\firmware\\active\\four-module-variable-spi\\pc\\experiment_recording.py",
        "sha256": "aff5787daa91bdb16719b0601d71707307e9d3471f636192cc5308445bf1b9ed"
      },
      "pc_controls": {
        "path": "D:\\study\\programming\\ESKIN\\E-SKIN\\hardware\\new\\firmware\\active\\four-module-variable-spi\\pc\\experiment_controls.py",
        "sha256": "9e7ff3b5678de04c46dbf9653385e7dbac9a8ec59f95737122020de50299b194"
      },
      "pc_module_detection": {
        "path": "D:\\study\\programming\\ESKIN\\E-SKIN\\hardware\\new\\firmware\\active\\four-module-variable-spi\\pc\\module_detection.py",
        "sha256": "52e35e8991c13e70e8f1e64d7b32d6b25bfa0fa7aeda8ec2333033540eb59ec1"
      }
    }
  },
  "batch_id": "BATCH_d49624f461e24a80b1176d3a6386840c",
  "batch_repeat_index": 1,
  "batch_repeat_count": 3,
  "batch_recording_method": "consecutive_capture_windows_same_setup",
  "batch_interpretation": "Temporal repeats under one setup; not independent setup blocks or automatic reloading",
  "batch_initial_observations": "GUI at_record fields describe the initial batch request; each run measures its own statistics",
  "module_detection_at_repeat_start": {
    "source": "recent_successful_protocol_slots_not_board_uids",
    "ready": true,
    "modules": [
      1
    ],
    "mode": "FULL",
    "slot_modes": {
      "1": "FULL"
    },
    "slot_last_success_monotonic": {
      "1": 185917.5495439
    },
    "last_packet_monotonic": 185917.5495439,
    "observed_at_monotonic": 185917.5543796,
    "window_span_seconds": 1.4921880000038072,
    "window_seconds": 1.5,
    "stale_seconds": 0.5,
    "packet_count": 300,
    "limitation": "No response cannot establish whether a board is physically attached. The recent union can retain a briefly missing slot; recording freezes the set."
  },
  "module_detection_at_worker_start": {
    "source": "recent_successful_protocol_slots_not_board_uids",
    "ready": true,
    "modules": [
      1
    ],
    "mode": "FULL",
    "slot_modes": {
      "1": "FULL"
    },
    "slot_last_success_monotonic": {
      "1": 185917.5495439
    },
    "last_packet_monotonic": 185917.5495439,
    "observed_at_monotonic": 185917.554472,
    "window_span_seconds": 1.4921880000038072,
    "window_seconds": 1.5,
    "stale_seconds": 0.5,
    "packet_count": 300,
    "limitation": "No response cannot establish whether a board is physically attached. The recent union can retain a briefly missing slot; recording freezes the set."
  },
  "pre_record_commands": [],
  "stream_start_offset": 32042153,
  "live_parser_buffer_bytes_at_start": 1,
  "live_parser_continuous_across_recordings": true,
  "module_count": 1,
  "algorithm": "FULL",
  "modules": [
    "M1"
  ],
  "active_module_ids": [
    "M1"
  ],
  "scan_hz": 200,
  "target_scan_rate_hz": 200,
  "load_label": "zero_load"
}
```

## Scope checks

- full_run: CHECK REQUIRED; 40.003054 s; 8014 valid MUL1; 8014/8014 target updates.
  Review reasons: unassigned_raw_bytes_in_full_capture.
- main: PASS; 30.003054 s; 6010 valid MUL1; 6010/6010 target updates.
  Review reasons: none.

Raw bytes are assigned by chunk arrival; complete packet bytes by completion time.
Start-boundary packets: 1; suffixes are audited separately and excluded from complete packet rates, K and q.
Missing updates and unknown initial cache prefixes are not proven physical-scan losses.
Local artifact hashes identify source/build files; no device flash readback was performed by this recorder.
