Yannas-Sun/E-skin_MSc_final_report/Calibration scalability/DATA/module_1/FSR1/evaluation/analysis/dispersion/dispersion_variance.png

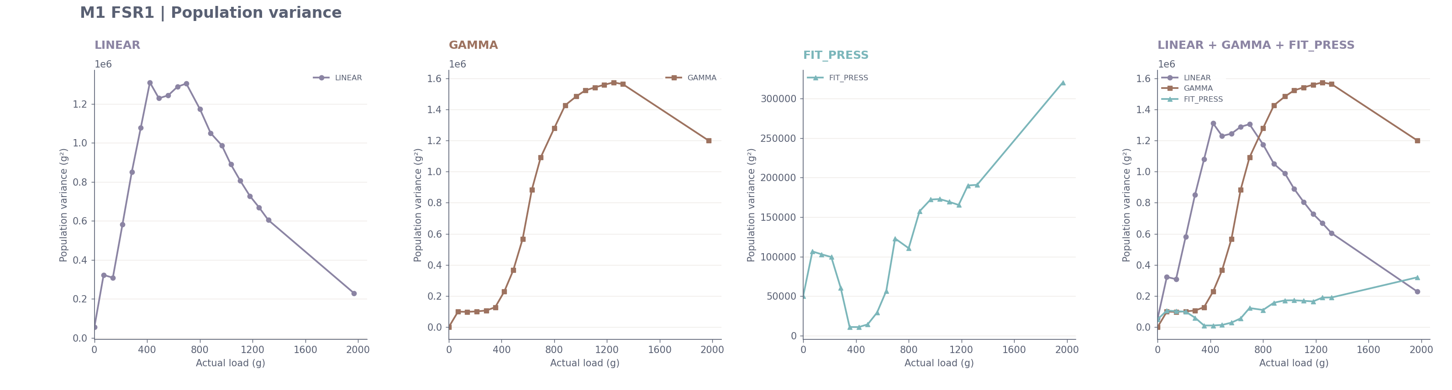
Calibration scalability/DATA/module_1/FSR1/evaluation/analysis/dispersion/dispersion_variance.png
