Yannas-Sun/E-skin_MSc_final_report/Calibration scalability/DATA/module_1/FSR1/evaluation/view_distribution/load_70g_20260907_090619_651549/distribution_comparison.png

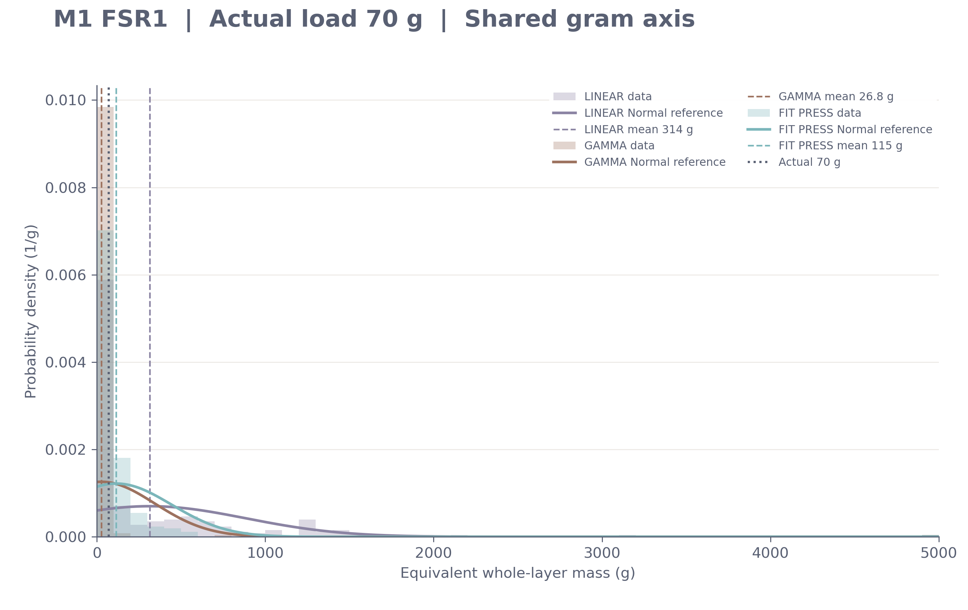
Calibration scalability/DATA/module_1/FSR1/evaluation/view_distribution/load_70g_20260907_090619_651549/distribution_comparison.png
