Yannas-Sun/E-skin_MSc_final_report/Calibration scalability/DATA/module_1/FSR1/evaluation/view_distribution/load_284g_20260907_090711_654414/distribution_comparison.png

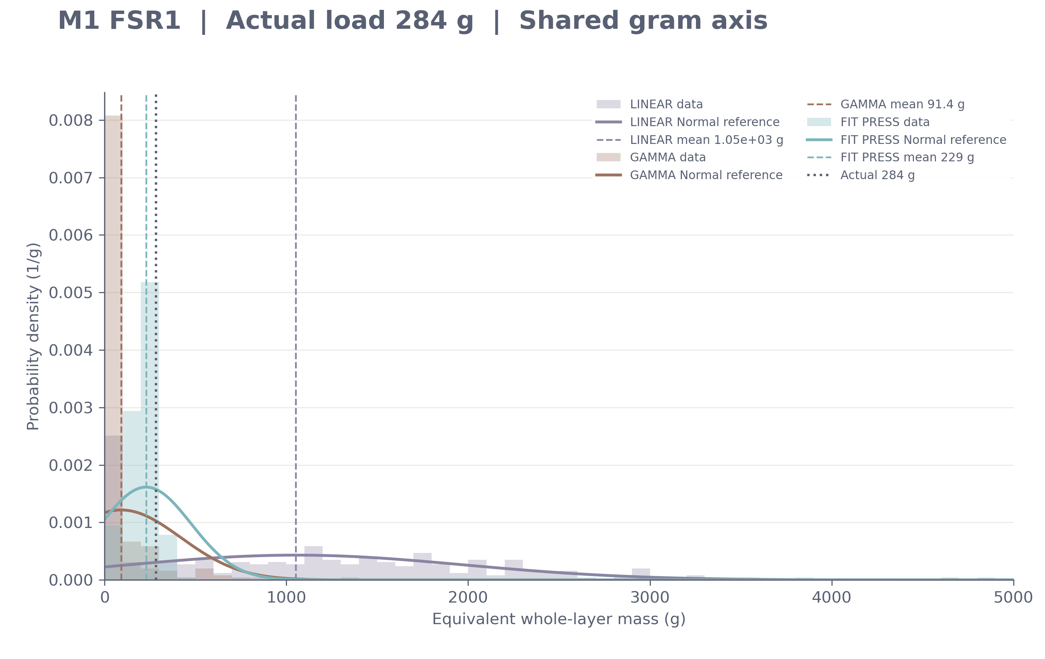
Calibration scalability/DATA/module_1/FSR1/evaluation/view_distribution/load_284g_20260907_090711_654414/distribution_comparison.png
