Yannas-Sun/E-skin_MSc_final_report/Calibration scalability/DATA/module_1/FSR1/evaluation/view_distribution/load_352g_20260907_090729_092912/linear_distribution.png

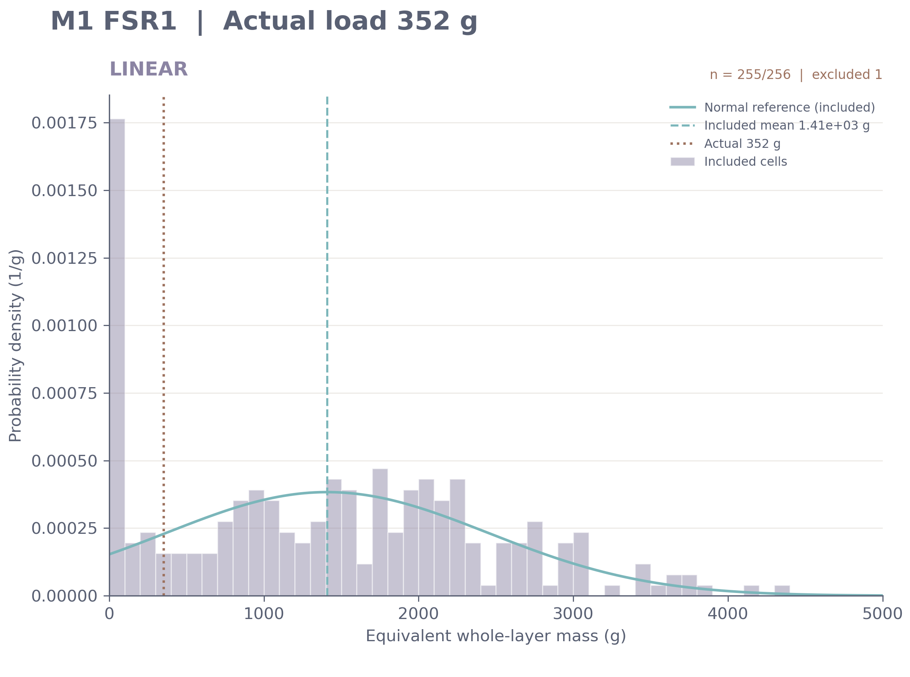
Calibration scalability/DATA/module_1/FSR1/evaluation/view_distribution/load_352g_20260907_090729_092912/linear_distribution.png
