Yannas-Sun/E-skin_MSc_final_report/Calibration scalability/DATA/module_1/FSR1/evaluation/view_distribution/load_560g_20260907_090816_506779/boxplot_distributions.png

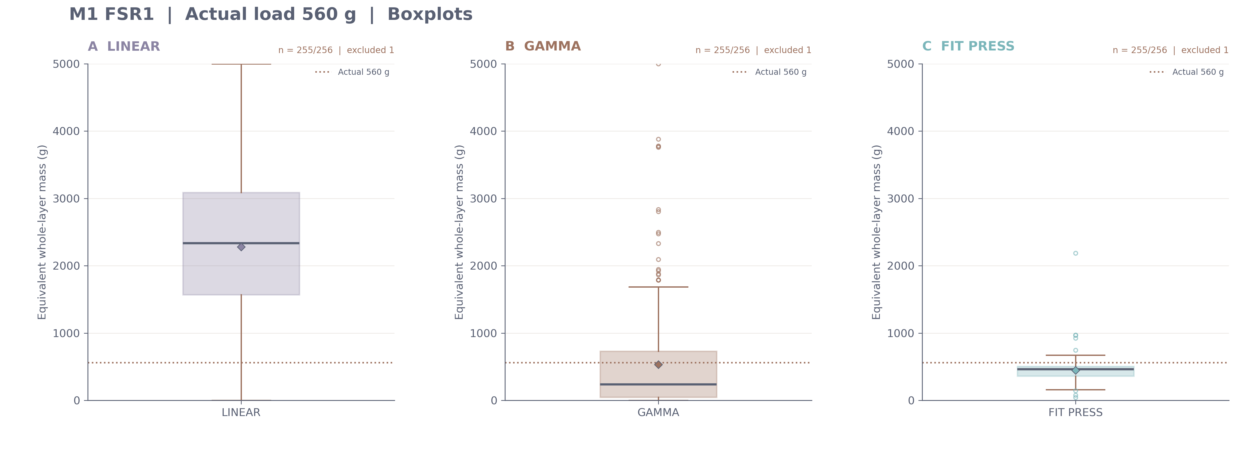
Calibration scalability/DATA/module_1/FSR1/evaluation/view_distribution/load_560g_20260907_090816_506779/boxplot_distributions.png
