Yannas-Sun/E-skin_MSc_final_report/Calibration scalability/DATA/module_1/FSR1/evaluation/view_distribution/load_882g_20260907_090911_957081/fit_press_distribution.png

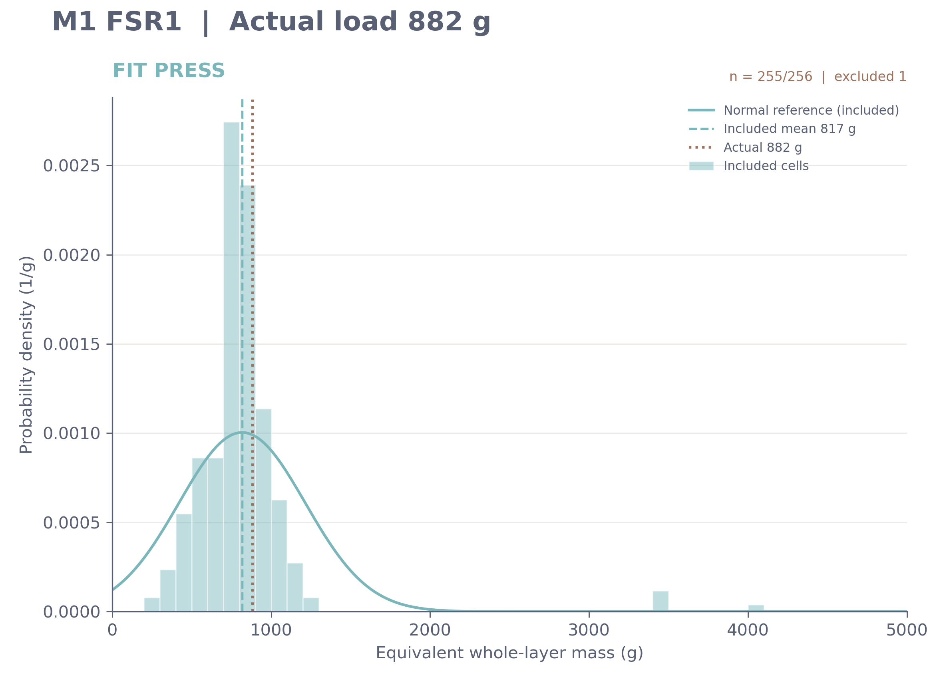
Calibration scalability/DATA/module_1/FSR1/evaluation/view_distribution/load_882g_20260907_090911_957081/fit_press_distribution.png
