Yannas-Sun/E-skin_MSc_final_report/Calibration scalability/DATA/module_1/FSR1/evaluation/view_distribution/load_1035g_20260907_090941_334101/view_distributions.png

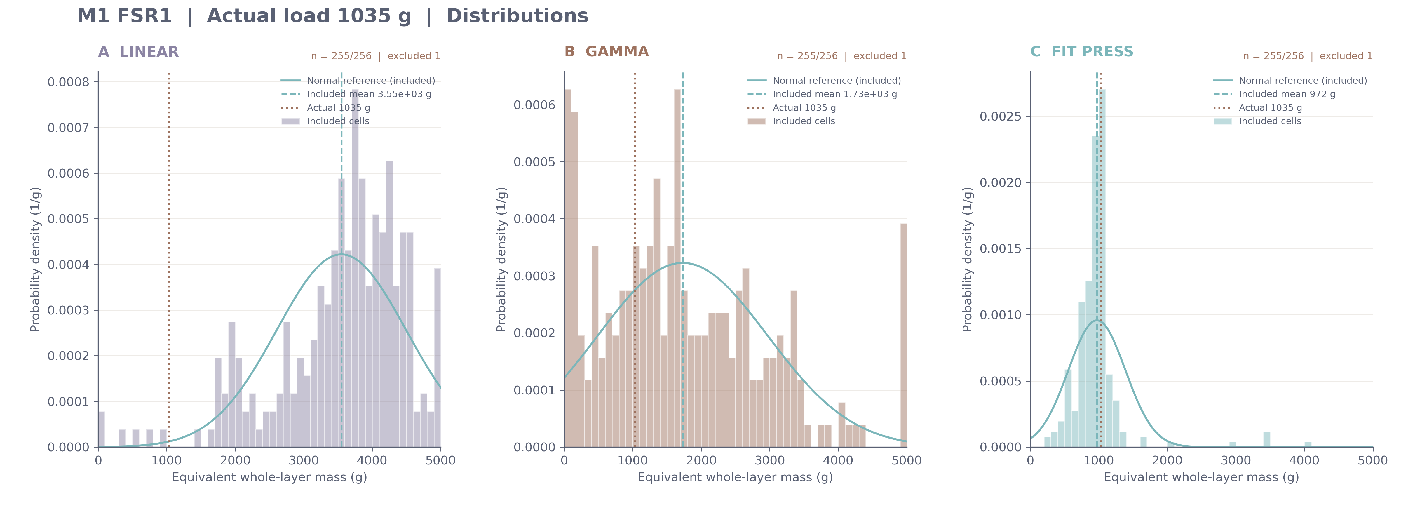
Calibration scalability/DATA/module_1/FSR1/evaluation/view_distribution/load_1035g_20260907_090941_334101/view_distributions.png
