Yannas-Sun/E-skin_MSc_final_report/Calibration scalability/DATA/module_1/FSR1/evaluation/view_distribution/load_1319g_20260907_091036_135224/view_distributions.png

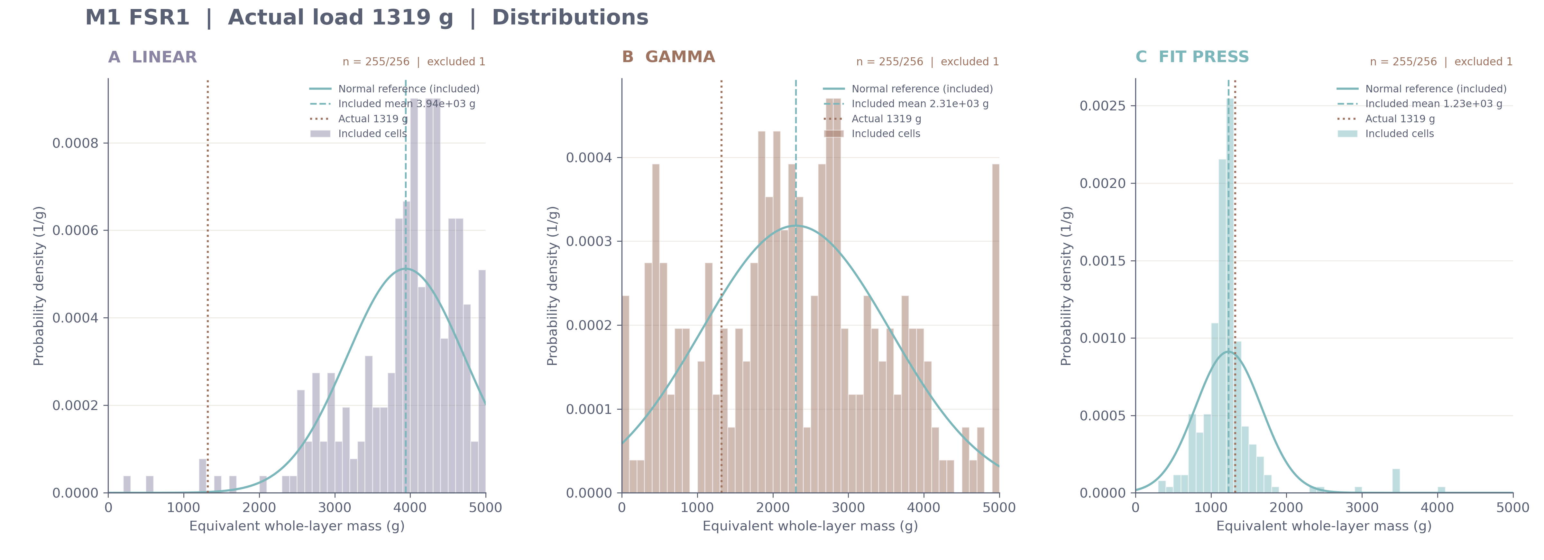
Calibration scalability/DATA/module_1/FSR1/evaluation/view_distribution/load_1319g_20260907_091036_135224/view_distributions.png
