Yannas-Sun/E-skin_MSc_final_report/Calibration scalability/DATA/module_1/FSR1/evaluation/view_distribution/load_1969g_20260907_091048_335833/analysis/20260907_101236_809904/capture/view_distributions.png

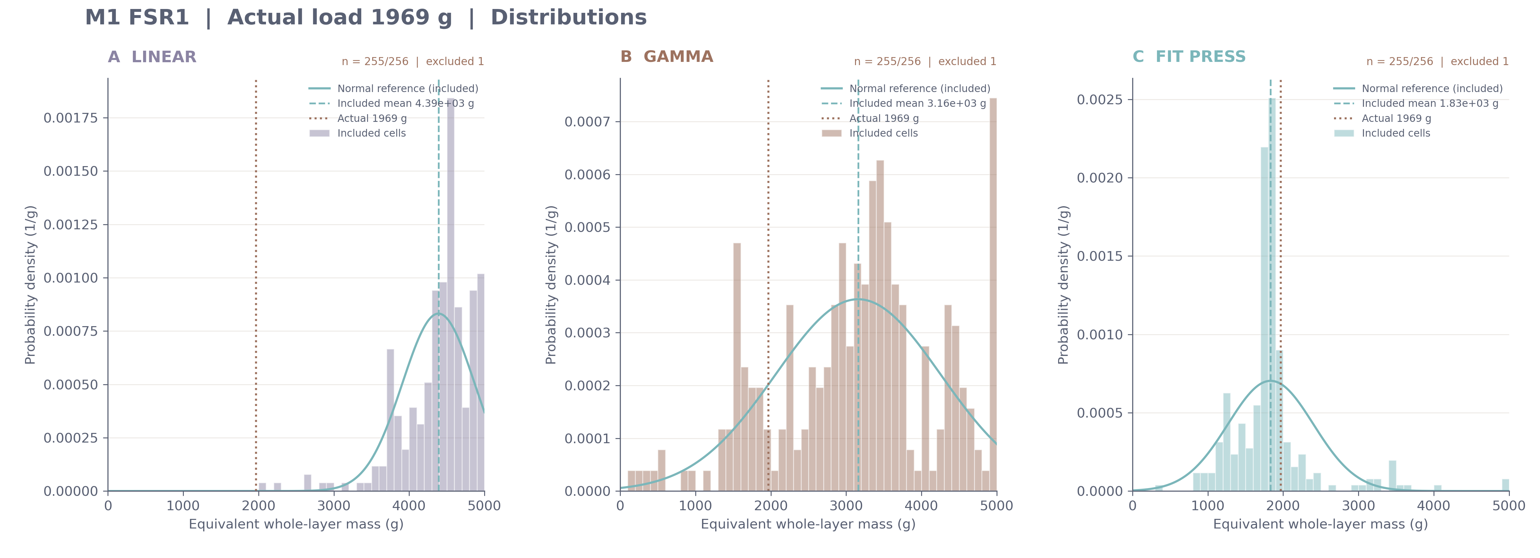
Calibration scalability/DATA/module_1/FSR1/evaluation/view_distribution/load_1969g_20260907_091048_335833/analysis/20260907_101236_809904/capture/view_distributions.png
