Yannas-Sun/E-skin_MSc_final_report/Calibration scalability/DATA/module_1/FSR1/fit/analysis/20260907_082603_615037/per_cell_response_grid.png

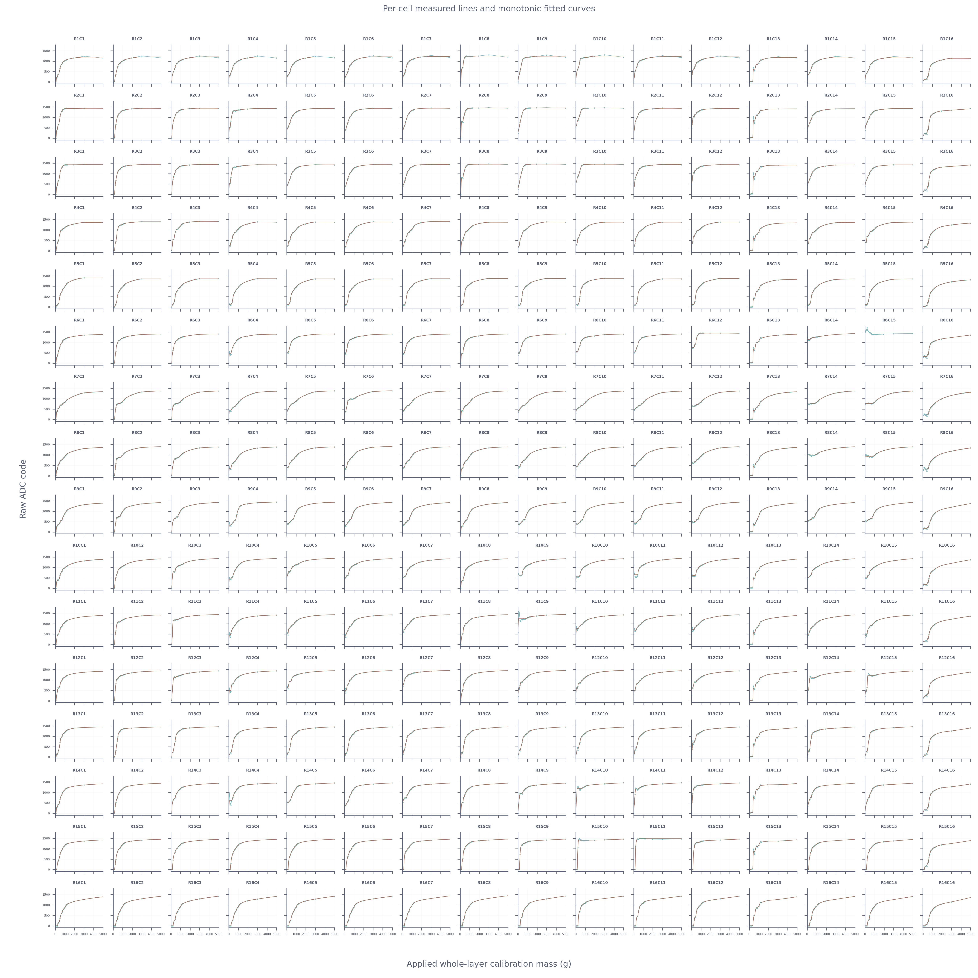
Calibration scalability/DATA/module_1/FSR1/fit/analysis/20260907_082603_615037/per_cell_response_grid.png
