Yannas-Sun/E-skin_MSc_final_report/Calibration scalability/DATA/module_1/FSR2/evaluation/analysis/error/load_comparison.png

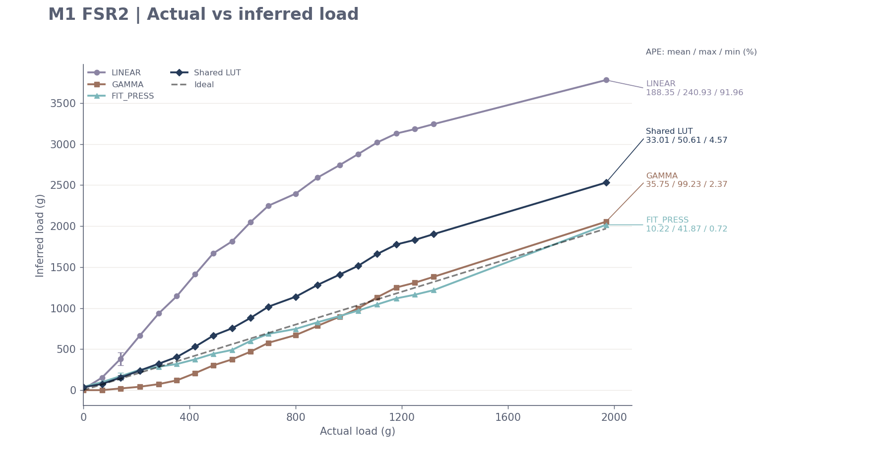
Calibration scalability/DATA/module_1/FSR2/evaluation/analysis/error/load_comparison.png
