Yannas-Sun/E-skin_MSc_final_report/Calibration scalability/DATA/module_1/FSR2/evaluation/view_distribution/load_70g_20260907_101028_704906/gamma_distribution.png

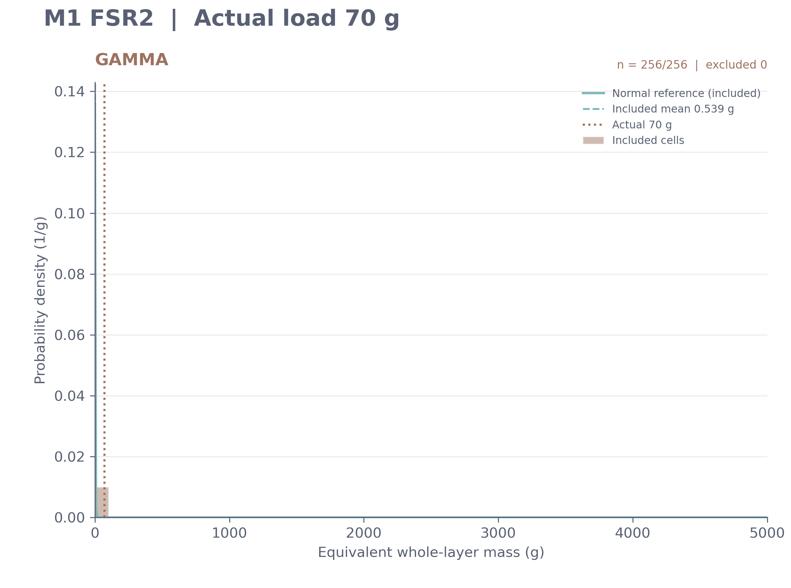
Calibration scalability/DATA/module_1/FSR2/evaluation/view_distribution/load_70g_20260907_101028_704906/gamma_distribution.png
