Yannas-Sun/E-skin_MSc_final_report/Calibration scalability/DATA/module_1/FSR2/evaluation/view_distribution/load_212g_20260907_101500_336732/distribution_comparison.png

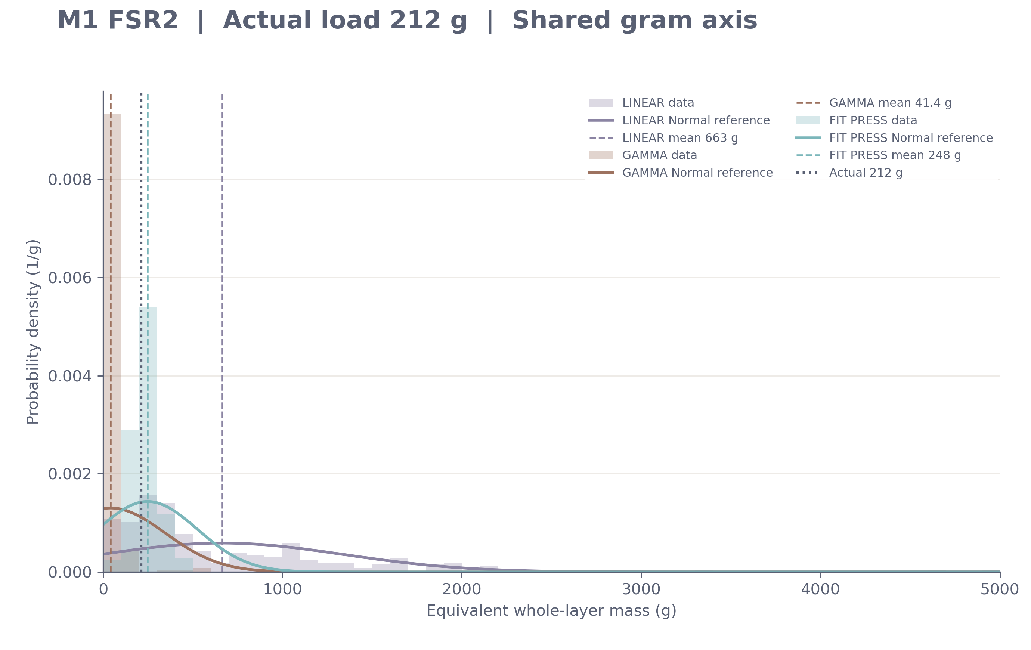
Calibration scalability/DATA/module_1/FSR2/evaluation/view_distribution/load_212g_20260907_101500_336732/distribution_comparison.png
