Yannas-Sun/E-skin_MSc_final_report/Calibration scalability/DATA/module_1/FSR2/evaluation/view_distribution/load_352g_20260907_101538_902482/fit_press_distribution.png

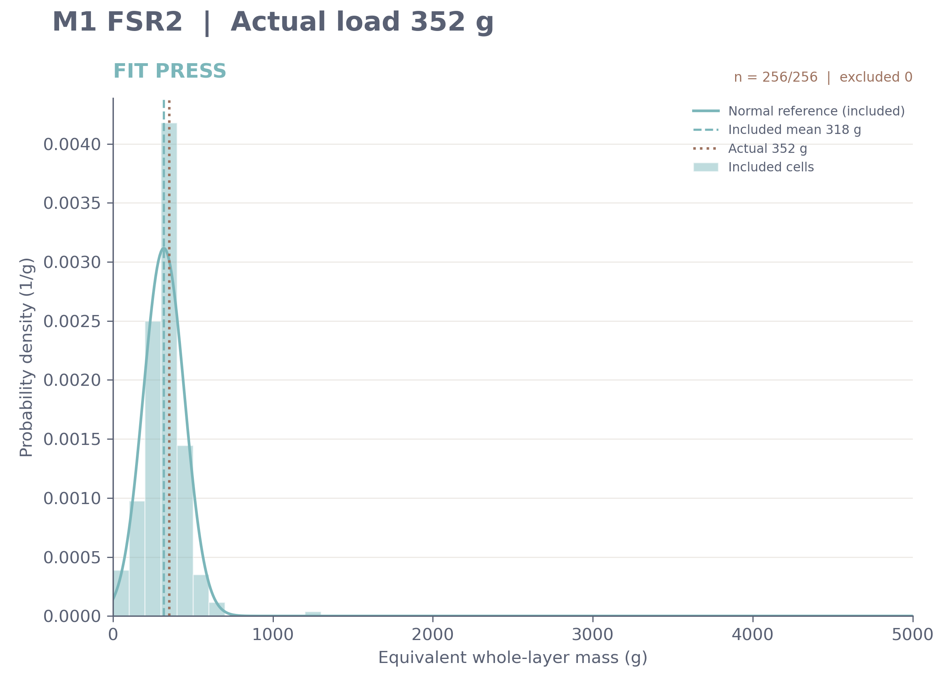
Calibration scalability/DATA/module_1/FSR2/evaluation/view_distribution/load_352g_20260907_101538_902482/fit_press_distribution.png
