Yannas-Sun/E-skin_MSc_final_report/Calibration scalability/DATA/module_1/FSR2/evaluation/view_distribution/load_421g_20260907_101603_160223/fit_press_distribution.png

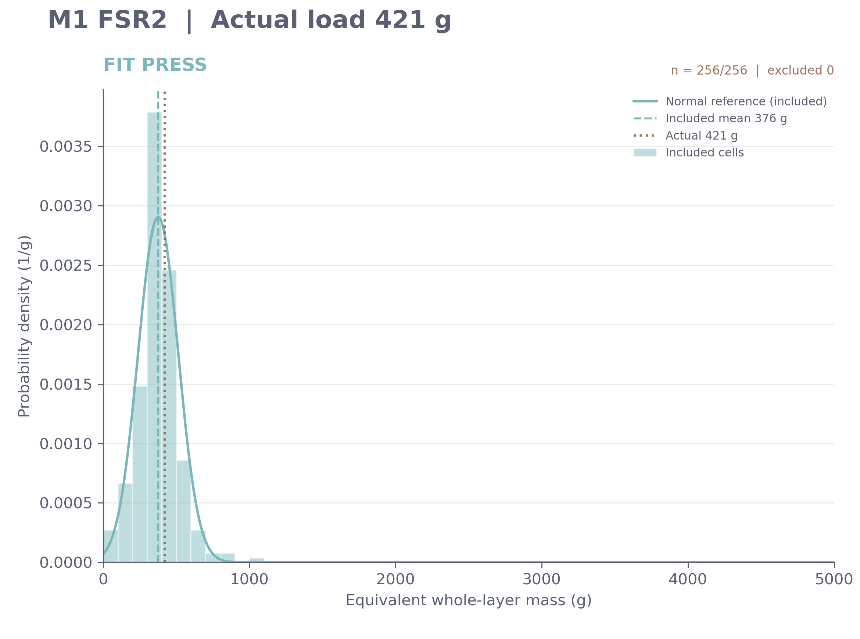
Calibration scalability/DATA/module_1/FSR2/evaluation/view_distribution/load_421g_20260907_101603_160223/fit_press_distribution.png
