Yannas-Sun/E-skin_MSc_final_report/Calibration scalability/DATA/module_1/FSR2/evaluation/view_distribution/load_489g_20260907_101626_871977/distribution_comparison.png

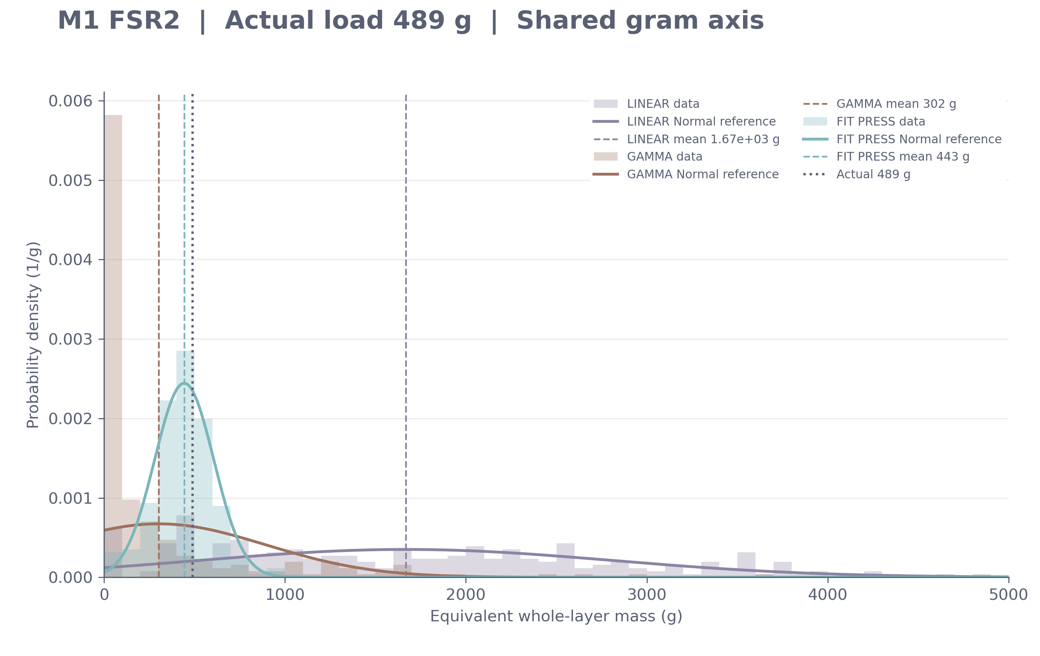
Calibration scalability/DATA/module_1/FSR2/evaluation/view_distribution/load_489g_20260907_101626_871977/distribution_comparison.png
