Yannas-Sun/E-skin_MSc_final_report/Calibration scalability/DATA/module_1/FSR2/evaluation/view_distribution/load_560g_20260907_101642_577982/linear_distribution.png

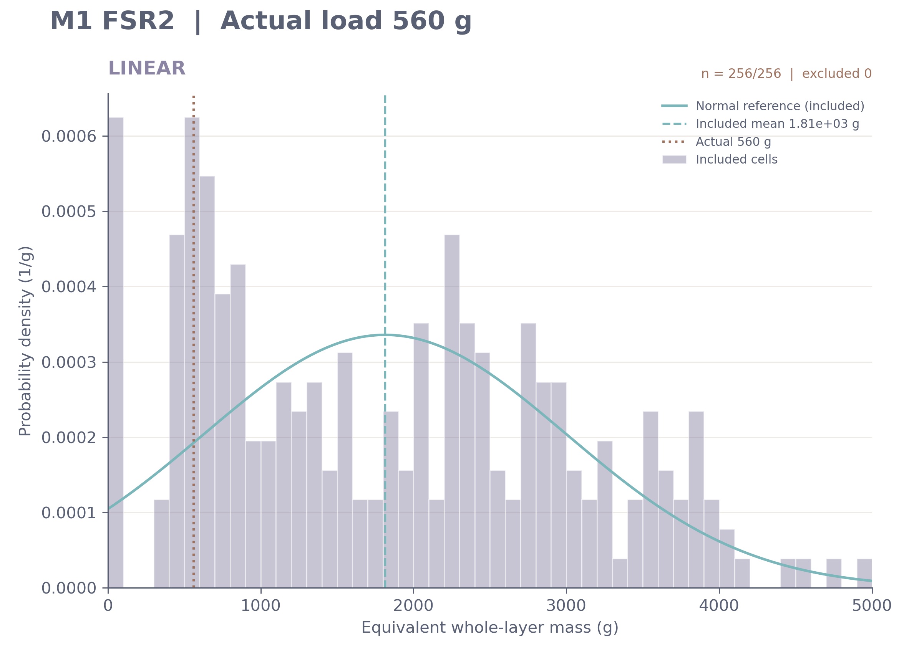
Calibration scalability/DATA/module_1/FSR2/evaluation/view_distribution/load_560g_20260907_101642_577982/linear_distribution.png
