Yannas-Sun/E-skin_MSc_final_report/Calibration scalability/DATA/module_1/FSR2/evaluation/view_distribution/load_630g_20260907_101701_032011/distribution_comparison.png

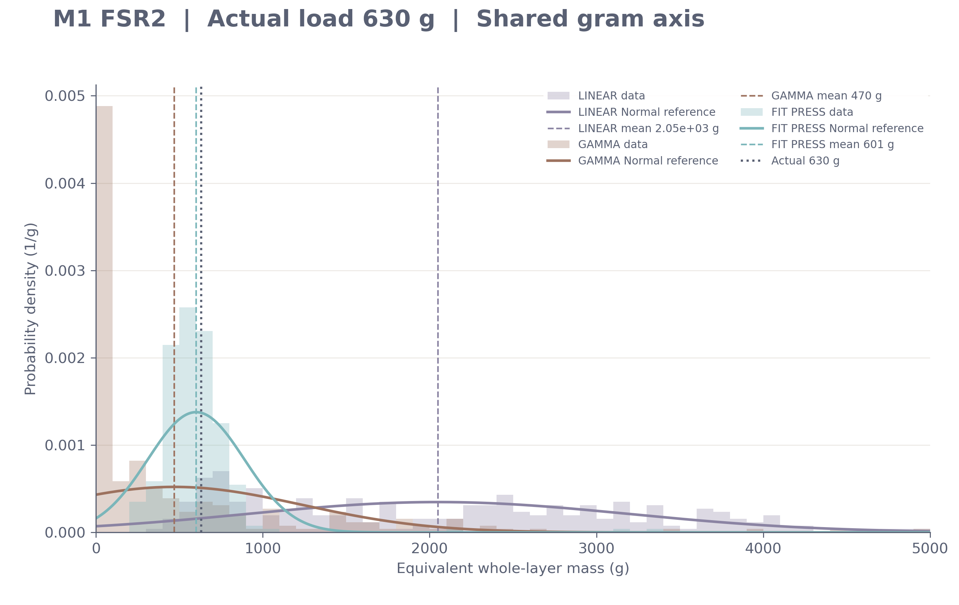
Calibration scalability/DATA/module_1/FSR2/evaluation/view_distribution/load_630g_20260907_101701_032011/distribution_comparison.png
