Yannas-Sun/E-skin_MSc_final_report/Calibration scalability/DATA/module_1/FSR2/evaluation/view_distribution/load_697g_20260907_101720_232441/fit_press_distribution.png

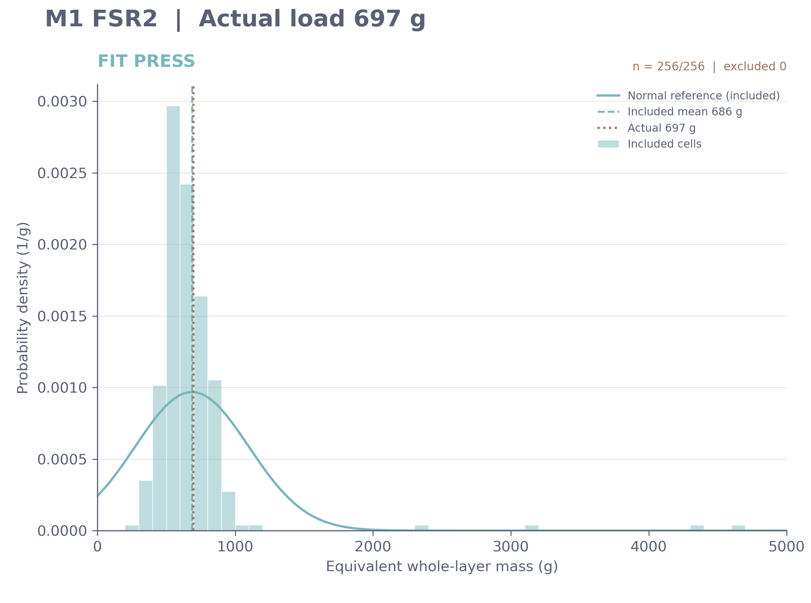
Calibration scalability/DATA/module_1/FSR2/evaluation/view_distribution/load_697g_20260907_101720_232441/fit_press_distribution.png
