Yannas-Sun/E-skin_MSc_final_report/Calibration scalability/DATA/module_1/FSR2/evaluation/view_distribution/load_800g_20260907_101736_025594/linear_distribution.png

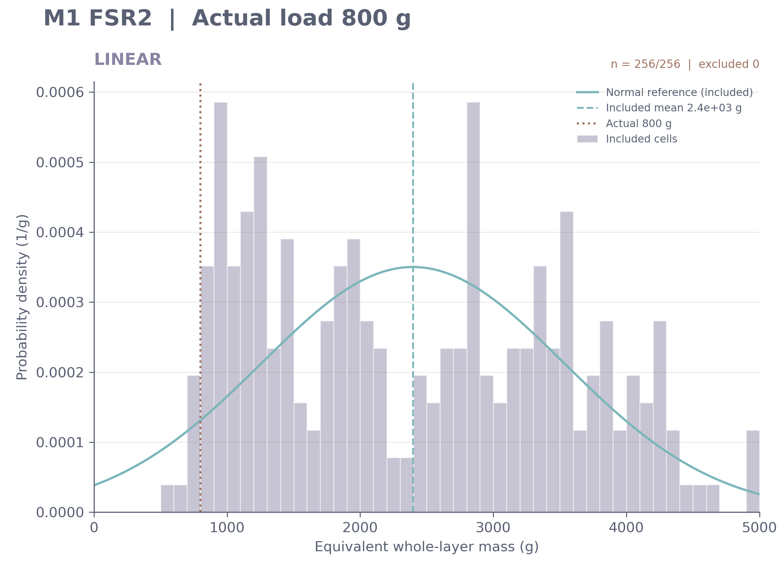
Calibration scalability/DATA/module_1/FSR2/evaluation/view_distribution/load_800g_20260907_101736_025594/linear_distribution.png
