Yannas-Sun/E-skin_MSc_final_report/Calibration scalability/DATA/module_1/FSR2/evaluation/view_distribution/load_882g_20260907_101755_639952/view_distributions.png

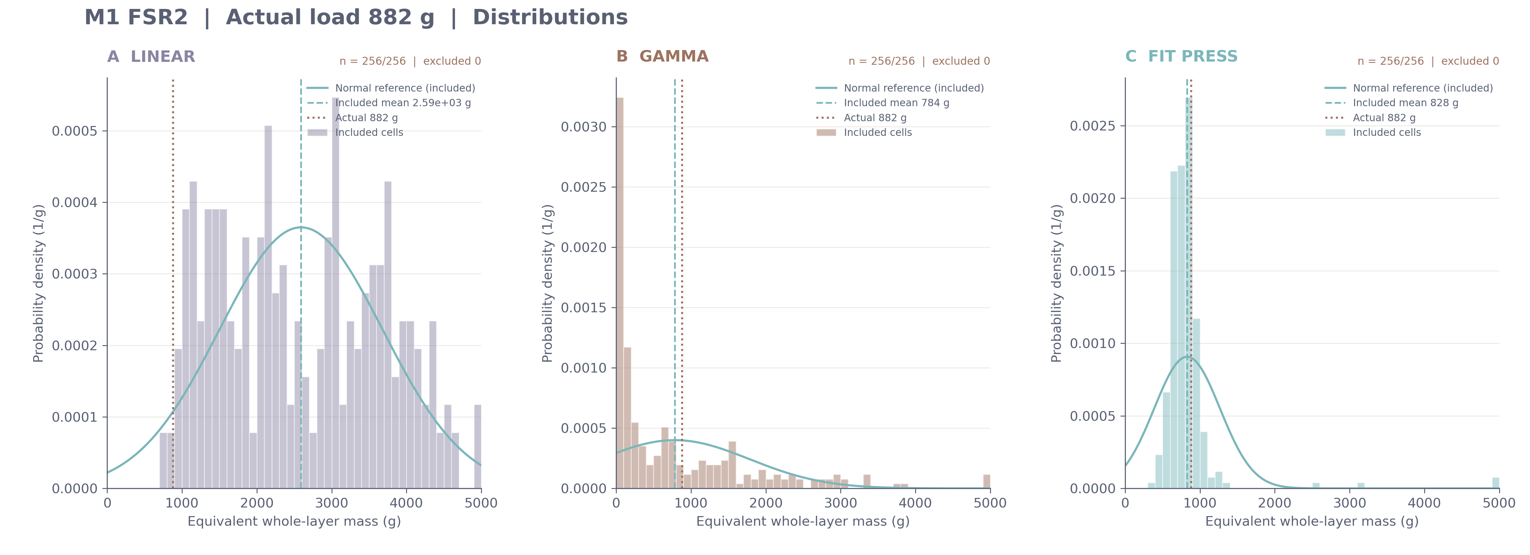
Calibration scalability/DATA/module_1/FSR2/evaluation/view_distribution/load_882g_20260907_101755_639952/view_distributions.png
