Yannas-Sun/E-skin_MSc_final_report/Calibration scalability/DATA/module_1/FSR2/evaluation/view_distribution/load_966g_20260907_101828_862451/view_distributions.png

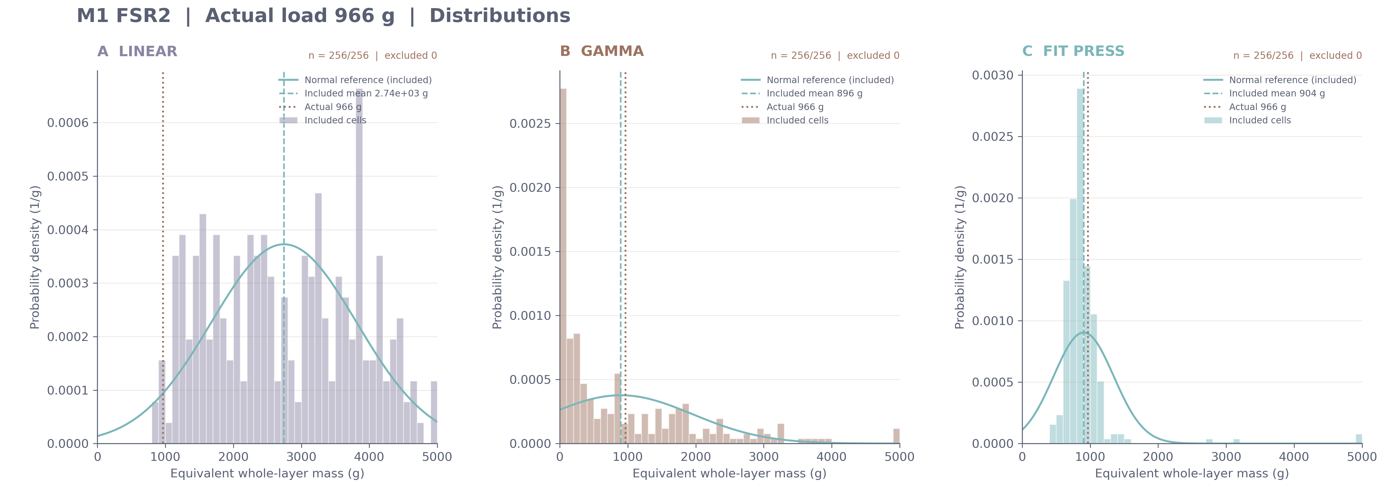
Calibration scalability/DATA/module_1/FSR2/evaluation/view_distribution/load_966g_20260907_101828_862451/view_distributions.png
