Yannas-Sun/E-skin_MSc_final_report/Calibration scalability/DATA/module_1/FSR2/evaluation/view_distribution/load_1107g_20260907_101925_222795/linear_distribution.png

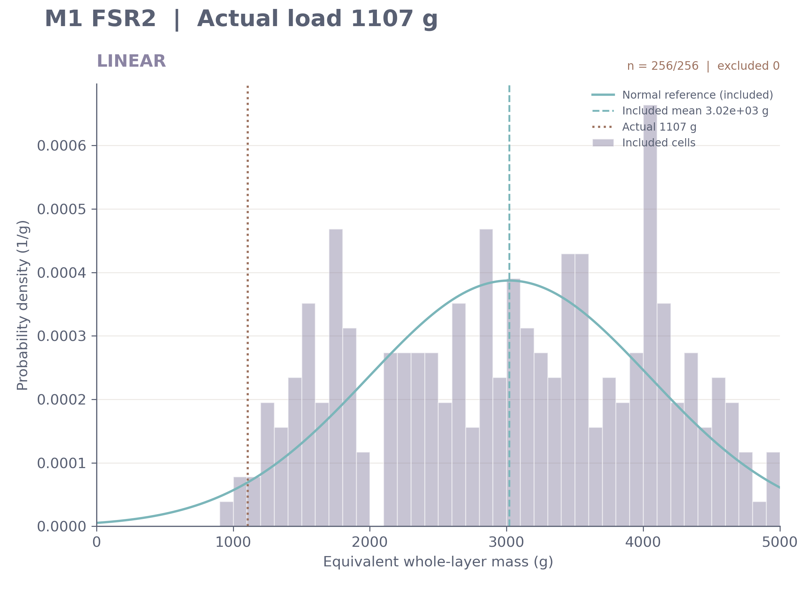
Calibration scalability/DATA/module_1/FSR2/evaluation/view_distribution/load_1107g_20260907_101925_222795/linear_distribution.png
