Yannas-Sun/E-skin_MSc_final_report/Calibration scalability/DATA/module_1/FSR2/evaluation/view_distribution/load_1179g_20260907_101941_768328/gamma_distribution.png

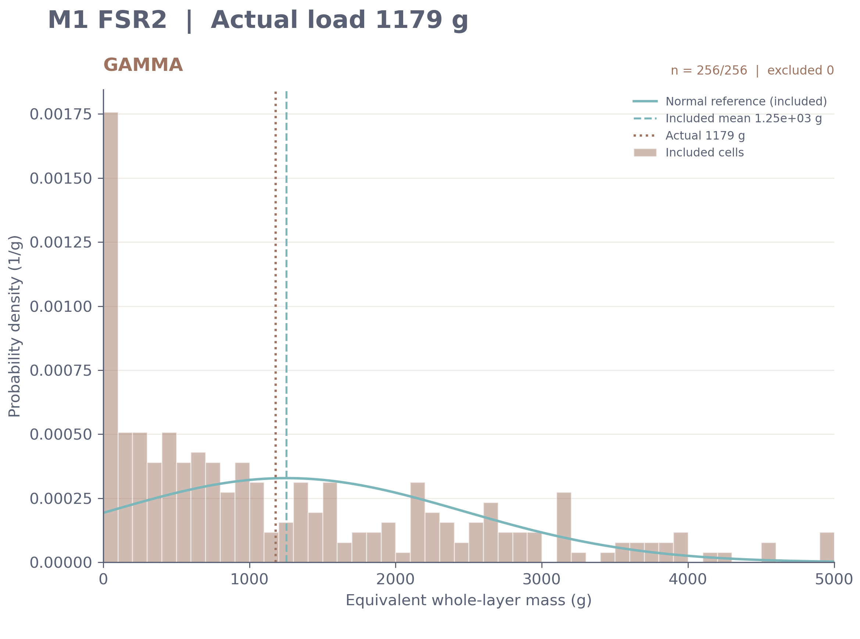
Calibration scalability/DATA/module_1/FSR2/evaluation/view_distribution/load_1179g_20260907_101941_768328/gamma_distribution.png
