Yannas-Sun/E-skin_MSc_final_report/Calibration scalability/DATA/module_1/FSR2/evaluation/view_distribution/load_1249g_20260907_101957_232734/boxplot_distributions.png

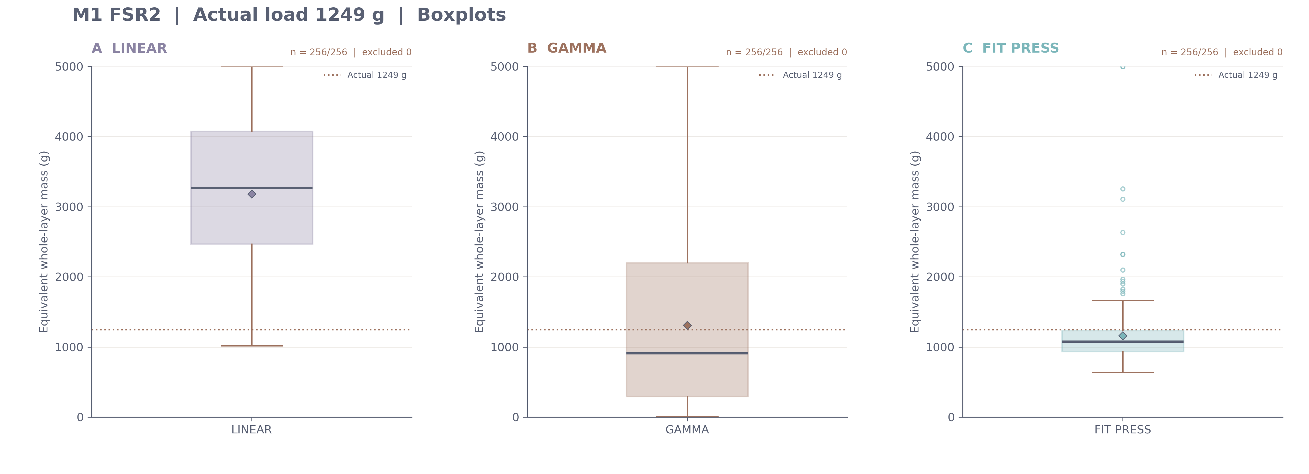
Calibration scalability/DATA/module_1/FSR2/evaluation/view_distribution/load_1249g_20260907_101957_232734/boxplot_distributions.png
