Yannas-Sun/E-skin_MSc_final_report/Calibration scalability/DATA/module_1/FSR2/evaluation/view_distribution/load_1969g_20260907_102032_192980/analysis/20260907_101244_202016/dispersion/dispersion_sd.png

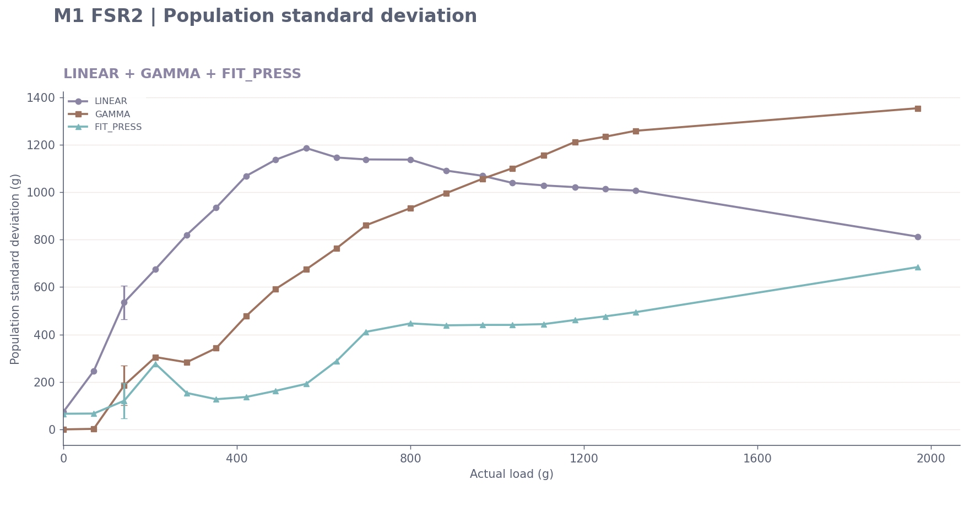
Calibration scalability/DATA/module_1/FSR2/evaluation/view_distribution/load_1969g_20260907_102032_192980/analysis/20260907_101244_202016/dispersion/dispersion_sd.png
