Yannas-Sun/E-skin_MSc_final_report/Calibration scalability/DATA/module_1/FSR2/fit/analysis/20260907_100736_196850/all_cells_fitted_curves.png

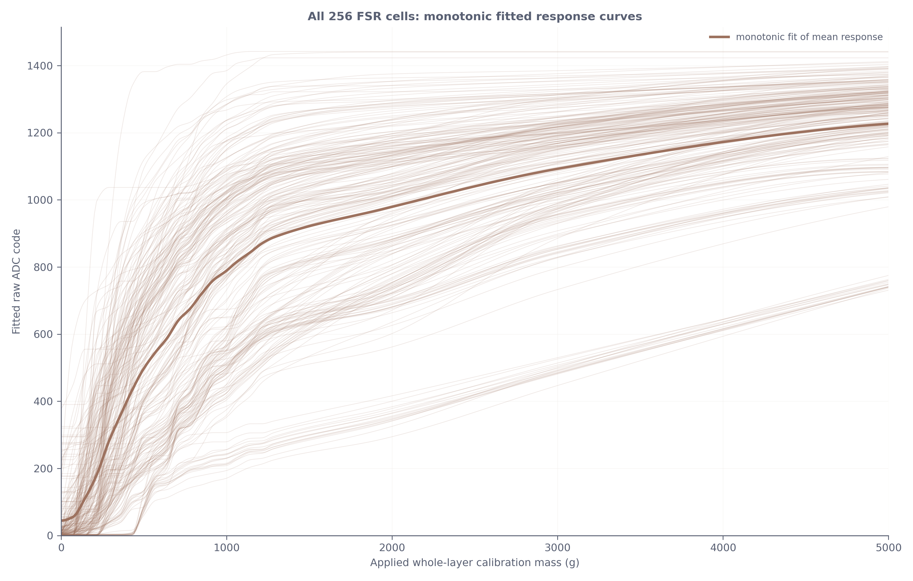
Calibration scalability/DATA/module_1/FSR2/fit/analysis/20260907_100736_196850/all_cells_fitted_curves.png
