Yannas-Sun/E-skin_MSc_final_report/data scalability/figures/exports/08_delta_combined_results.png

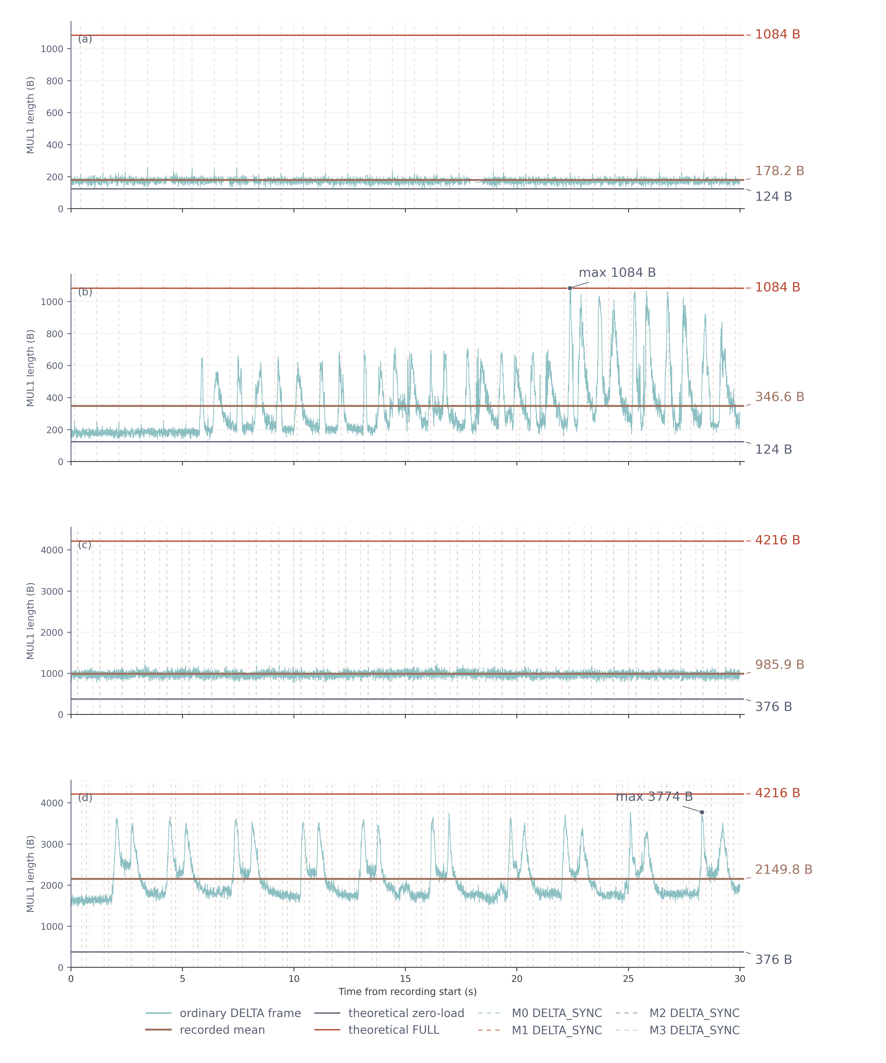
data scalability/figures/exports/08_delta_combined_results.png
