Yannas-Sun/E-skin_MSc_final_report/data scalability/figures/exports/08a_delta_single_module_results.png

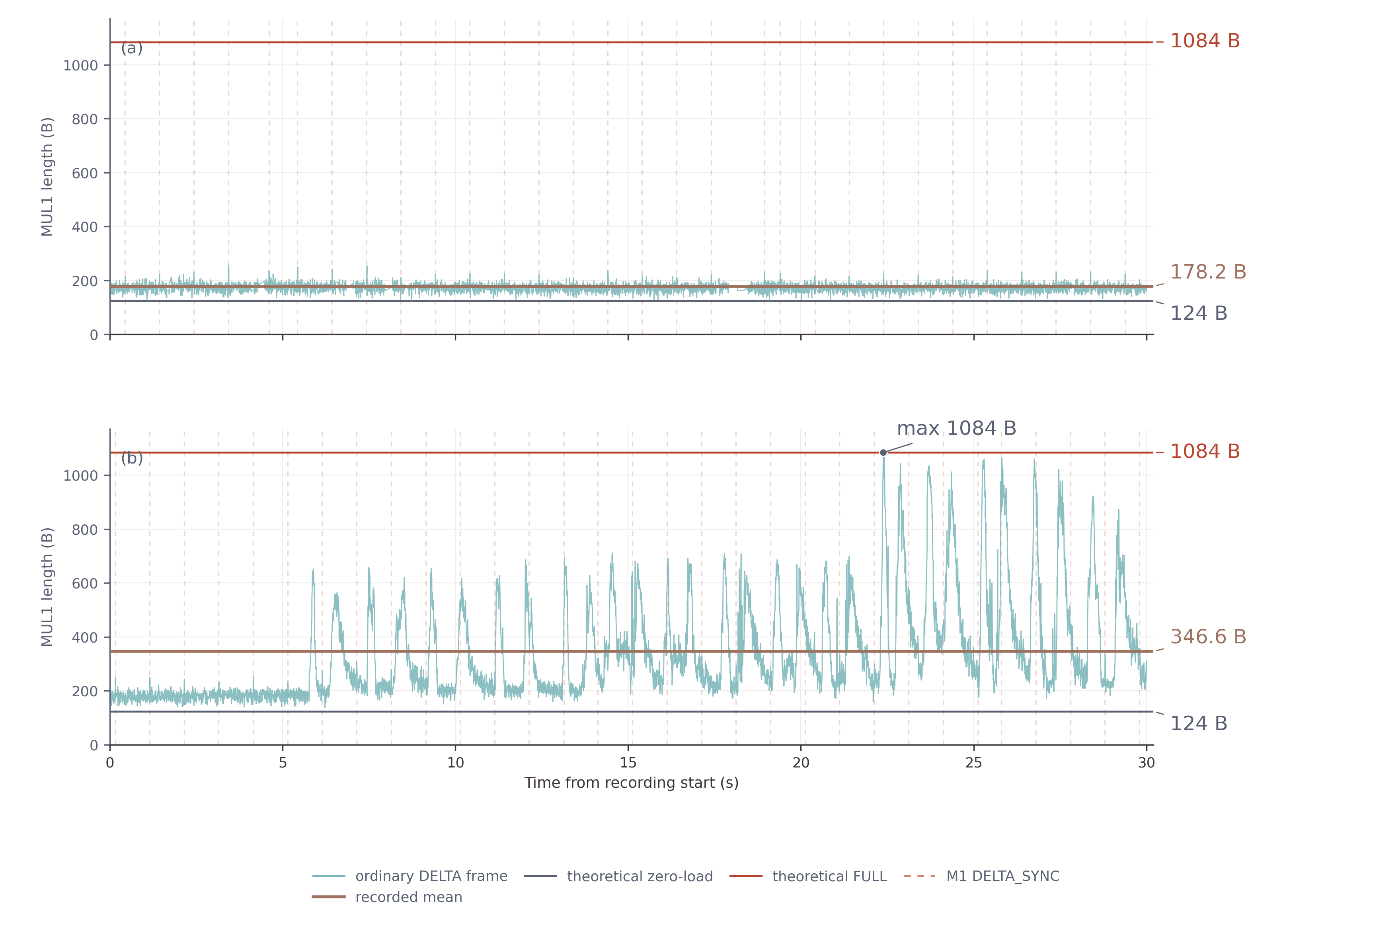
data scalability/figures/exports/08a_delta_single_module_results.png
