Yannas-Sun/E-skin_MSc_final_report/data scalability/figures/exports/08b_delta_four_module_results.png

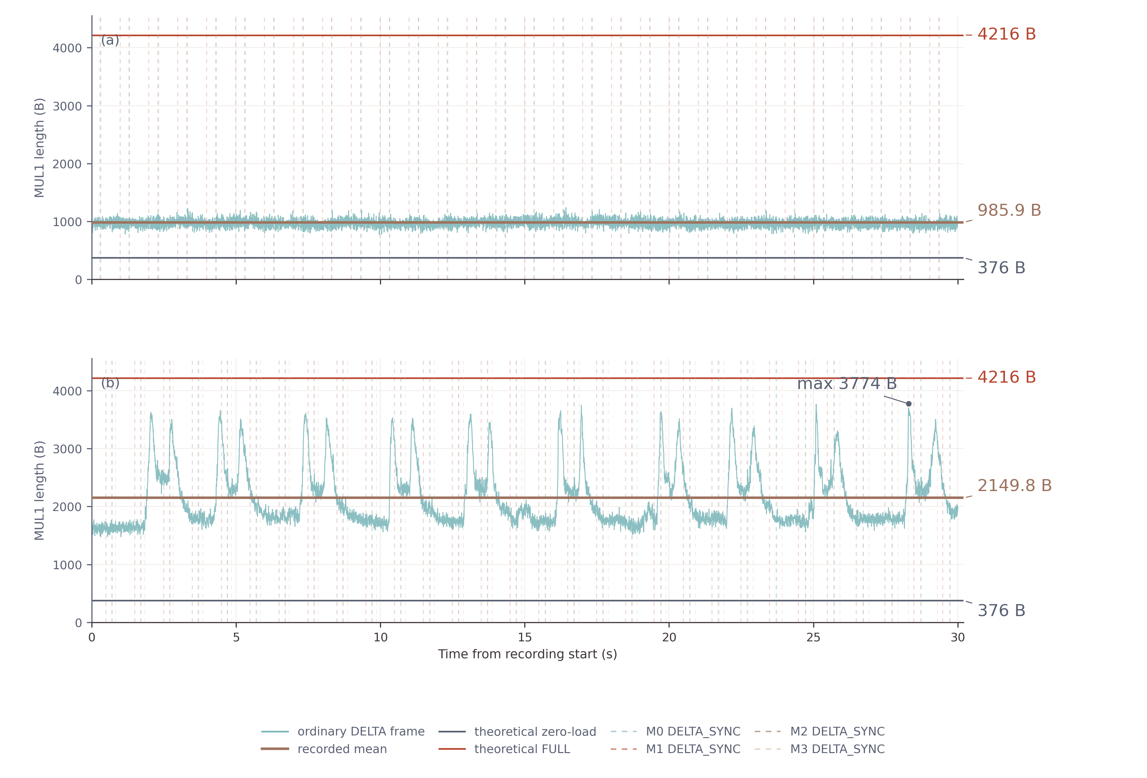
data scalability/figures/exports/08b_delta_four_module_results.png
