Yannas-Sun/E-skin_MSc_final_report/power scalability/DATA/raw/canonical/power_experiment_records/no_transmission/n=2/M0-M1/zero_load/IMG_20260831_182743.jpg

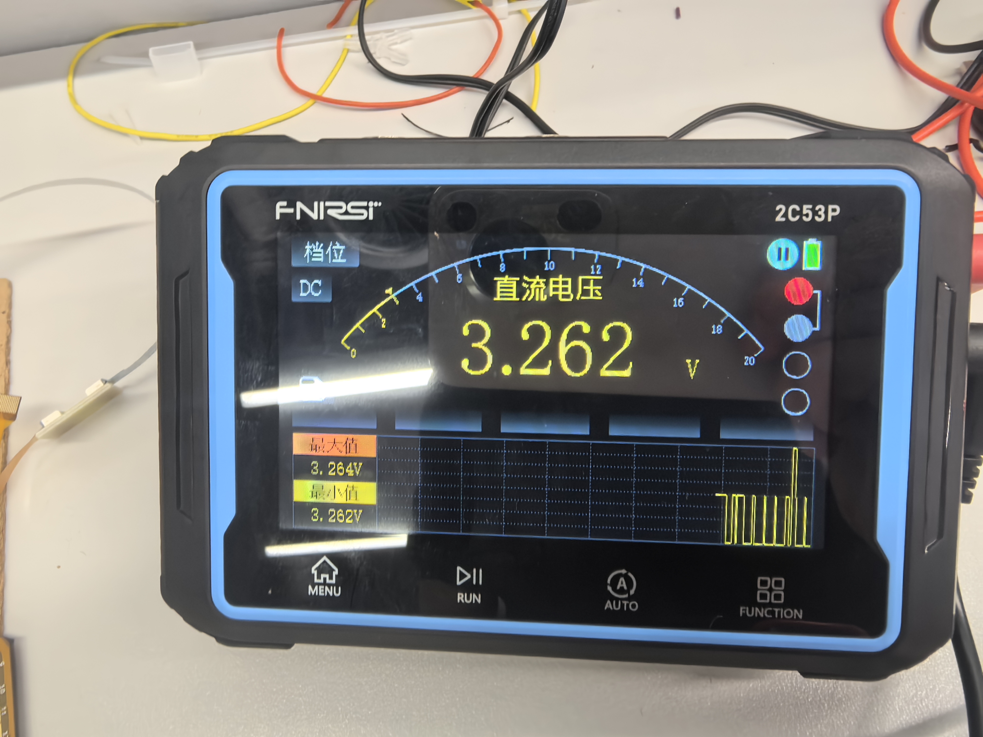
power scalability/DATA/raw/canonical/power_experiment_records/no_transmission/n=2/M0-M1/zero_load/IMG_20260831_182743.jpg
