Yannas-Sun/E-skin_MSc_final_report/power scalability/DATA/raw/canonical/power_experiment_records/no_transmission/n=2/M2-M3/zero_load/IMG_20260904_170426.jpg

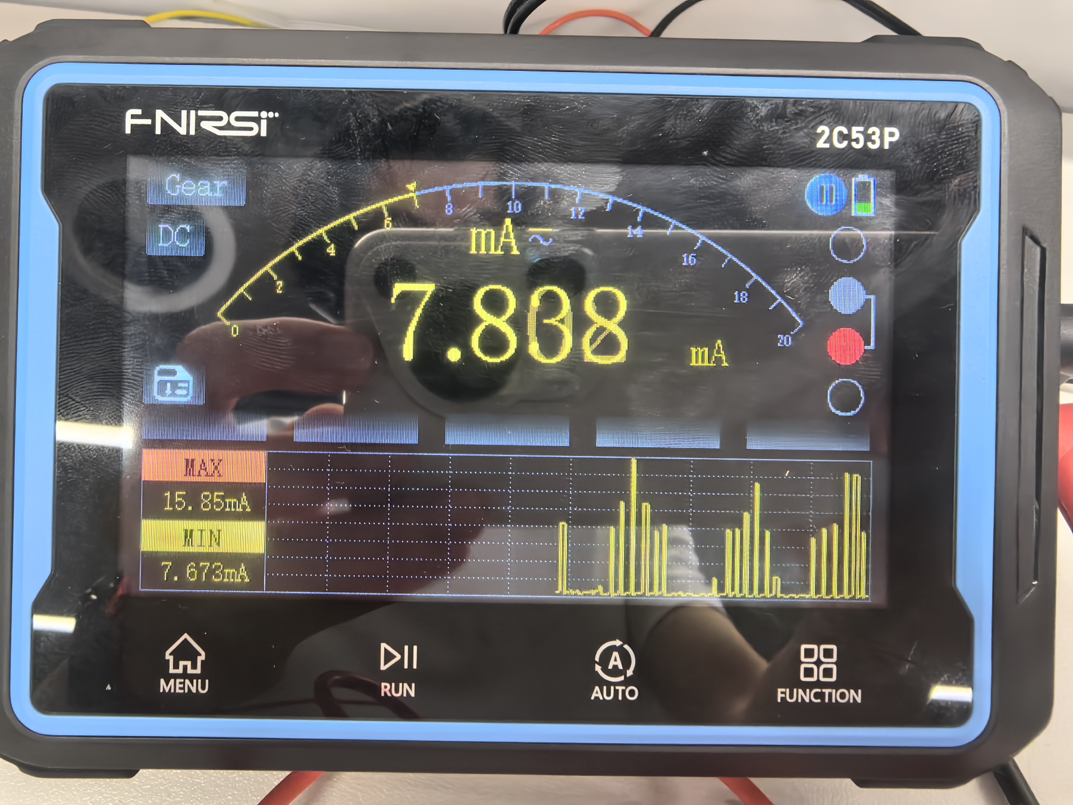
power scalability/DATA/raw/canonical/power_experiment_records/no_transmission/n=2/M2-M3/zero_load/IMG_20260904_170426.jpg
