Yannas-Sun/E-skin_MSc_final_report/power scalability/DATA/raw/canonical/power_experiment_records/no_transmission/n=4/M0-M1-M2-M3/historical_unmatched_1st_20260831/IMG_20260831_225619.jpg

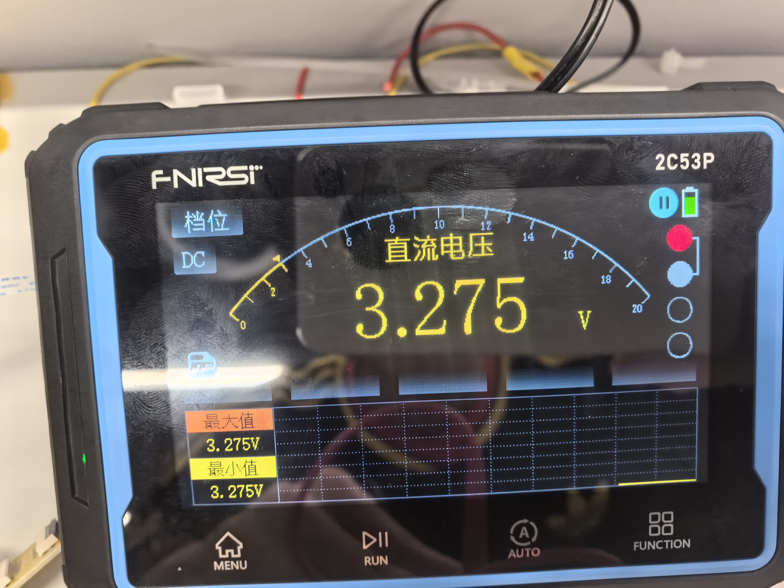
power scalability/DATA/raw/canonical/power_experiment_records/no_transmission/n=4/M0-M1-M2-M3/historical_unmatched_1st_20260831/IMG_20260831_225619.jpg
