Yannas-Sun/E-skin_MSc_final_report/power scalability/DATA/raw/canonical/power_experiment_records/no_transmission/photos/IMG_20260831_132305.jpg

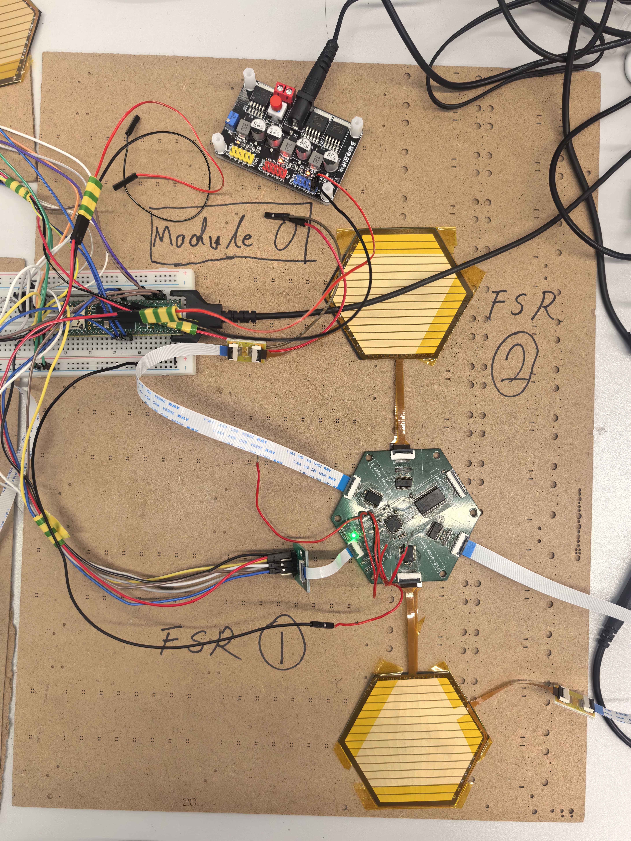
power scalability/DATA/raw/canonical/power_experiment_records/no_transmission/photos/IMG_20260831_132305.jpg
