Yannas-Sun/E-skin_MSc_final_report/power scalability/DATA/raw/canonical/power_experiment_records/no_transmission/photos/No_transmission/n=1/IMG_20260831_174832.jpg

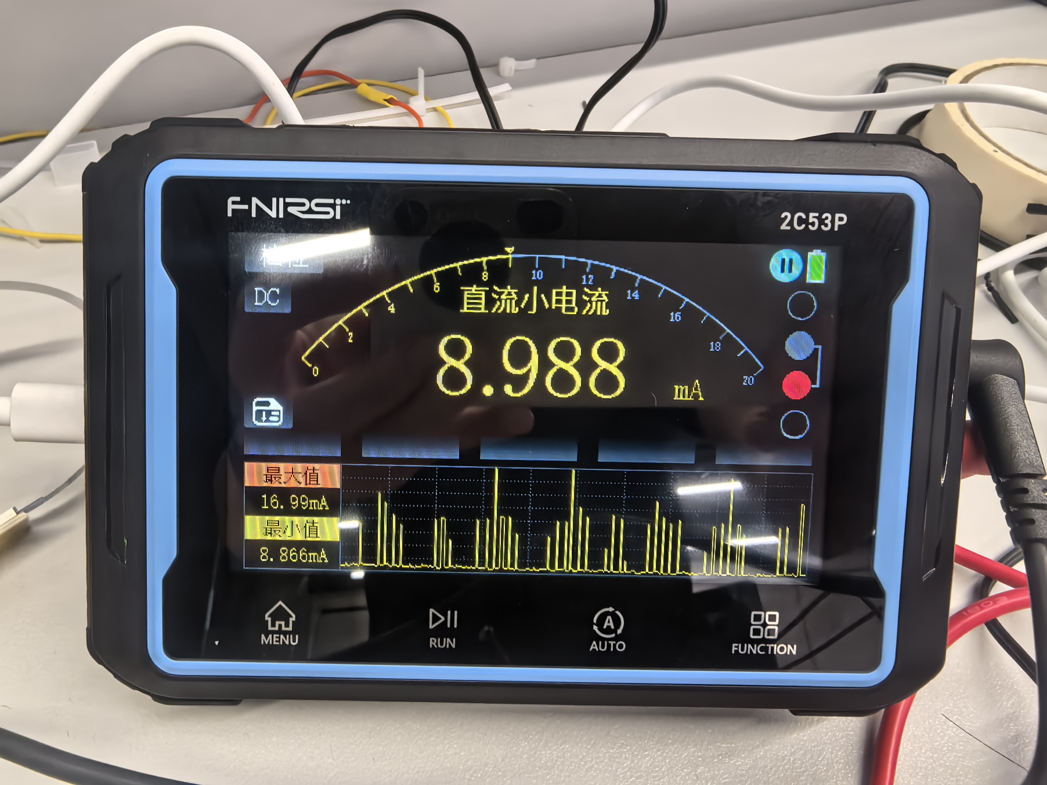
power scalability/DATA/raw/canonical/power_experiment_records/no_transmission/photos/No_transmission/n=1/IMG_20260831_174832.jpg
