Yannas-Sun/E-skin_MSc_final_report/power scalability/DATA/raw/canonical/power_experiment_records/targeted_retests/20260907_M1-M2-M3_MAX_M3/M3_voltage_retest.jpg

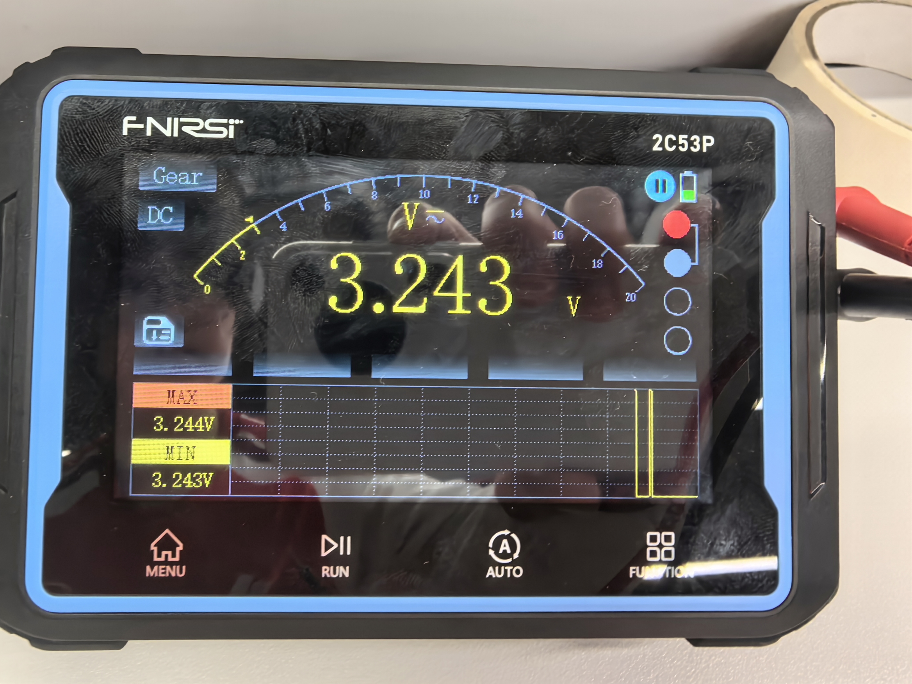
power scalability/DATA/raw/canonical/power_experiment_records/targeted_retests/20260907_M1-M2-M3_MAX_M3/M3_voltage_retest.jpg
