Yannas-Sun/E-skin_MSc_final_report/power scalability/DATA/raw/canonical/power_experiment_records/transmission/n=1/M0/full_load/new_V.jpg

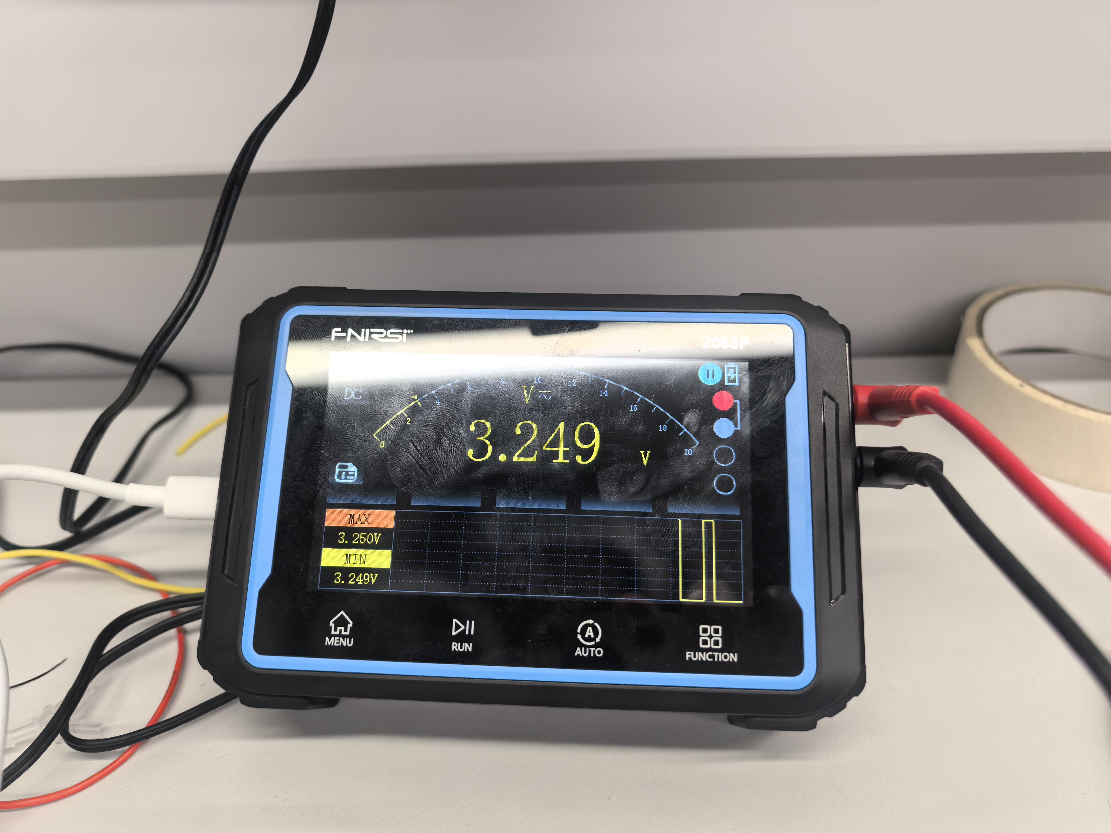
power scalability/DATA/raw/canonical/power_experiment_records/transmission/n=1/M0/full_load/new_V.jpg
