Yannas-Sun/E-skin_MSc_final_report/power scalability/DATA/raw/canonical/power_experiment_records/transmission/n=1/M1/full_load/IMG_20260904_185144.jpg

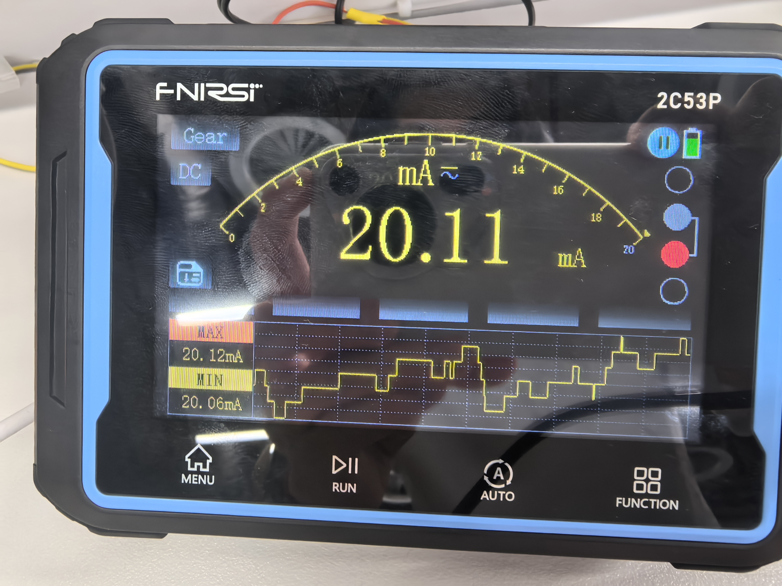
power scalability/DATA/raw/canonical/power_experiment_records/transmission/n=1/M1/full_load/IMG_20260904_185144.jpg
