Yannas-Sun/E-skin_MSc_final_report/power scalability/DATA/raw/canonical/power_experiment_records/transmission/n=2/M0-M1/zero_load/IMG_20260905_113033.jpg

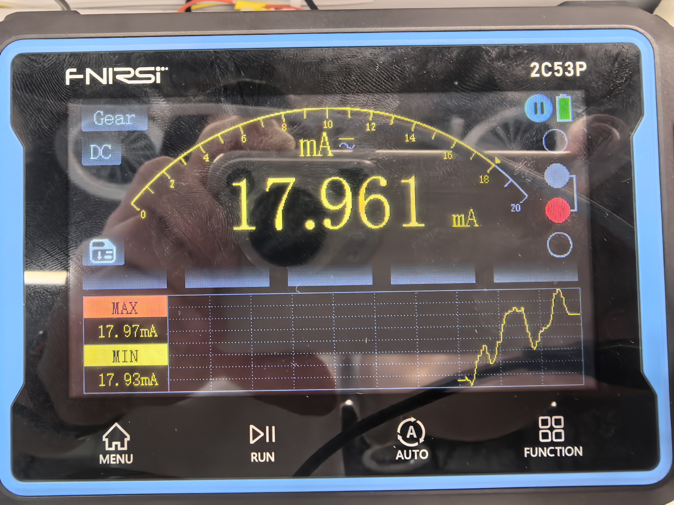
power scalability/DATA/raw/canonical/power_experiment_records/transmission/n=2/M0-M1/zero_load/IMG_20260905_113033.jpg
