Yannas-Sun/E-skin_MSc_final_report/power scalability/DATA/raw/canonical/power_experiment_records/transmission/n=2/M0-M2/zero_load/new_I.jpg

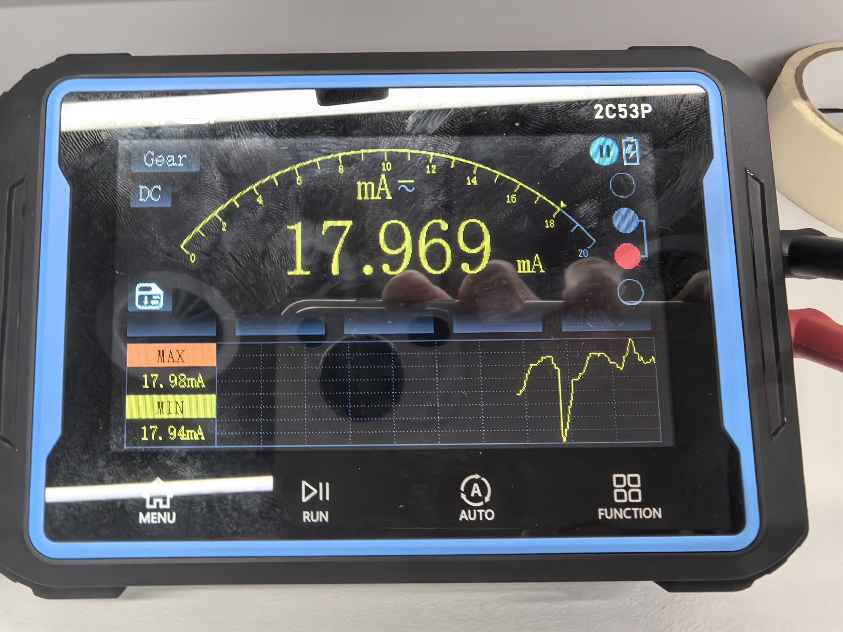
power scalability/DATA/raw/canonical/power_experiment_records/transmission/n=2/M0-M2/zero_load/new_I.jpg
