Yannas-Sun/E-skin_MSc_final_report/power scalability/DATA/raw/canonical/power_experiment_records/transmission/n=2/M1-M2/IMG_20260907_032139.jpg

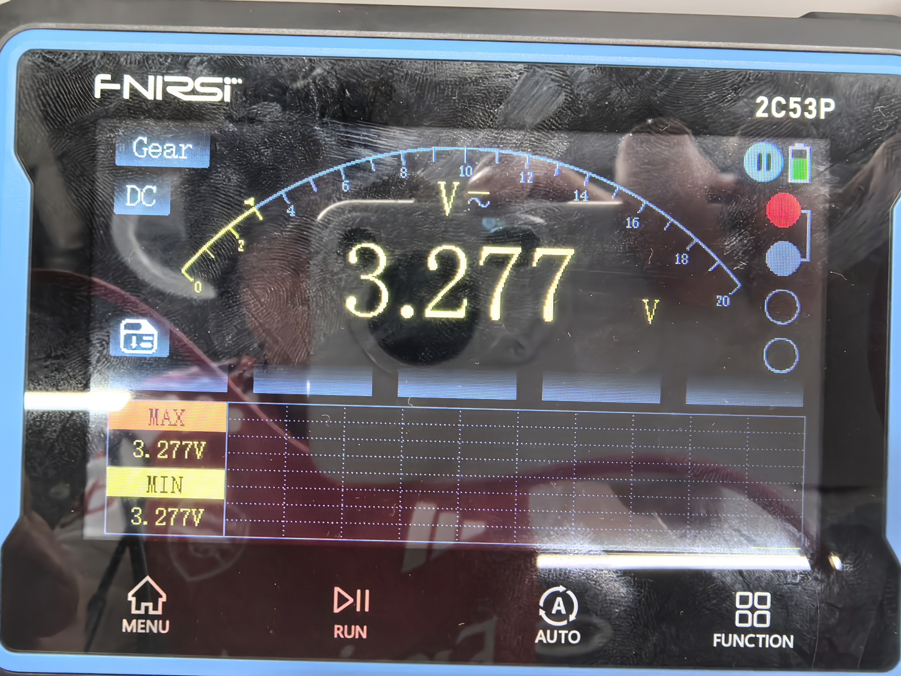
power scalability/DATA/raw/canonical/power_experiment_records/transmission/n=2/M1-M2/IMG_20260907_032139.jpg
