Yannas-Sun/E-skin_MSc_final_report/power scalability/DATA/raw/canonical/power_experiment_records/transmission/n=2/M1-M2/zero_load/IMG_20260906_233351.jpg

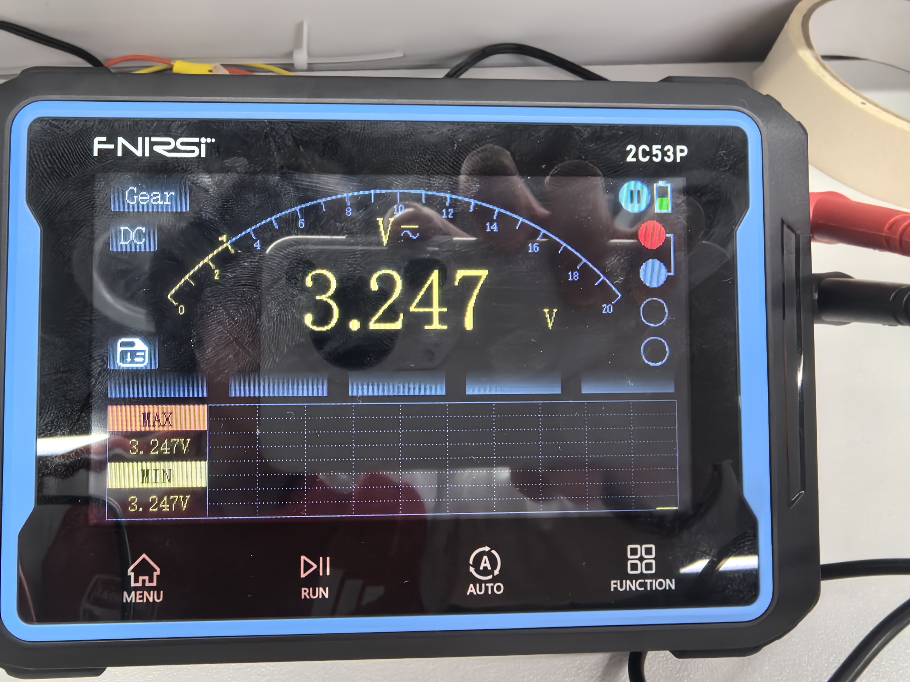
power scalability/DATA/raw/canonical/power_experiment_records/transmission/n=2/M1-M2/zero_load/IMG_20260906_233351.jpg
