Yannas-Sun/E-skin_MSc_final_report/power scalability/DATA/raw/canonical/power_experiment_records/transmission/n=2/M1-M2/zero_load/IMG_20260907_012237.jpg

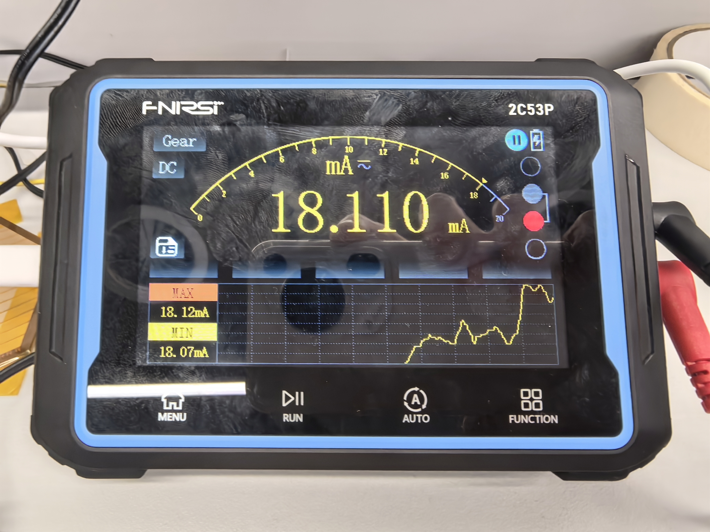
power scalability/DATA/raw/canonical/power_experiment_records/transmission/n=2/M1-M2/zero_load/IMG_20260907_012237.jpg
