Yannas-Sun/E-skin_MSc_final_report/power scalability/DATA/raw/canonical/power_experiment_records/transmission/n=2/M1-M3/IMG_20260907_032708.jpg

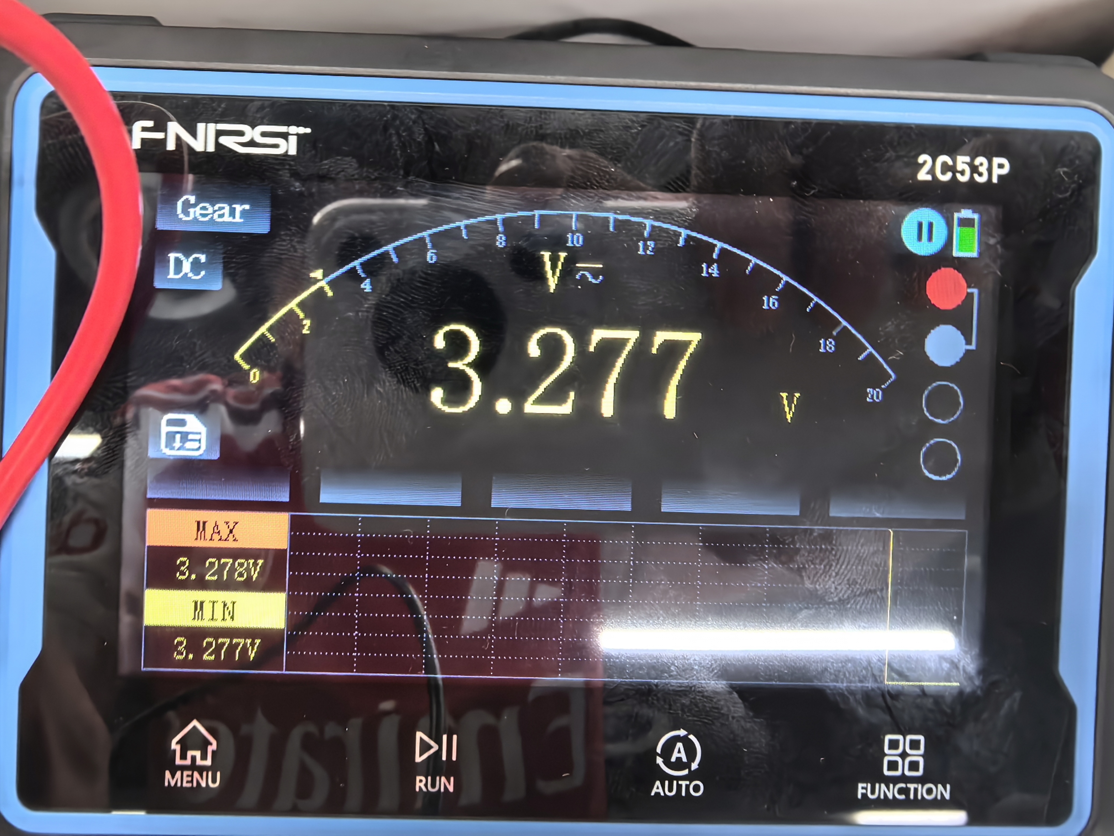
power scalability/DATA/raw/canonical/power_experiment_records/transmission/n=2/M1-M3/IMG_20260907_032708.jpg
