Yannas-Sun/E-skin_MSc_final_report/power scalability/DATA/raw/canonical/power_experiment_records/transmission/n=2/M2-M3/full_load/IMG_20260905_120321.jpg

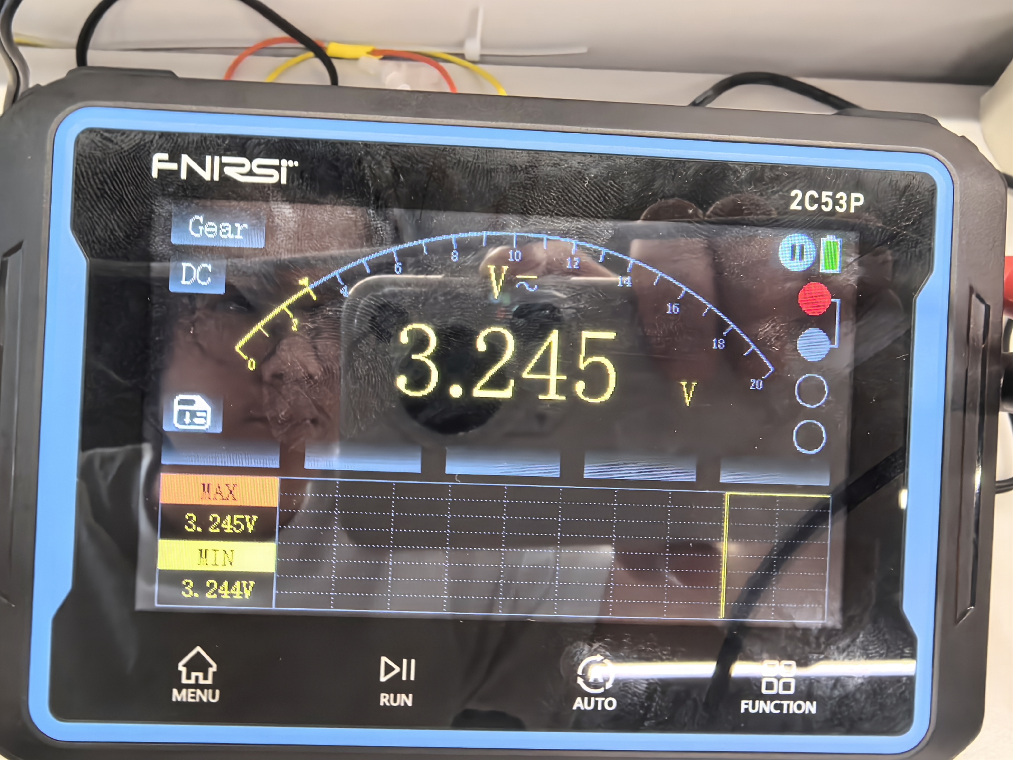
power scalability/DATA/raw/canonical/power_experiment_records/transmission/n=2/M2-M3/full_load/IMG_20260905_120321.jpg
