Yannas-Sun/E-skin_MSc_final_report/power scalability/DATA/raw/canonical/power_experiment_records/transmission/n=3/M0-M1-M2/full_load/IMG_20260905_130948.jpg

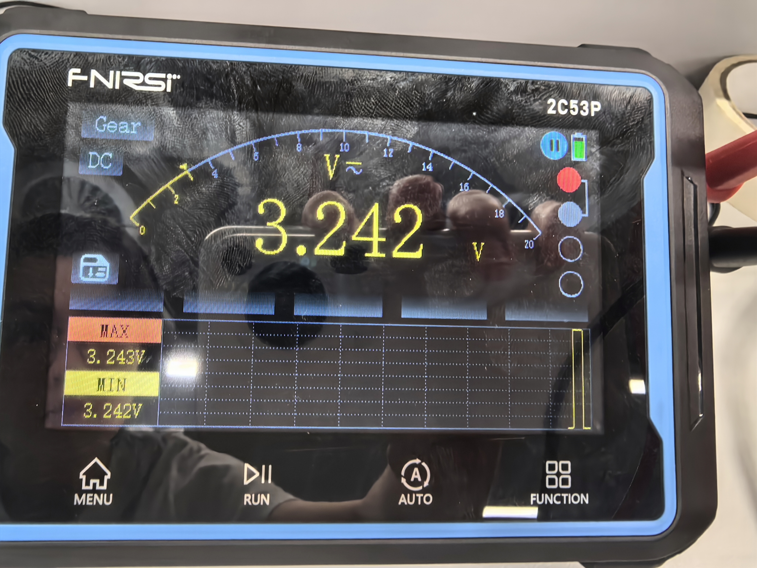
power scalability/DATA/raw/canonical/power_experiment_records/transmission/n=3/M0-M1-M2/full_load/IMG_20260905_130948.jpg
