Yannas-Sun/E-skin_MSc_final_report/power scalability/DATA/raw/canonical/power_experiment_records/transmission/n=3/M0-M2-M3/IMG_20260907_034818.jpg

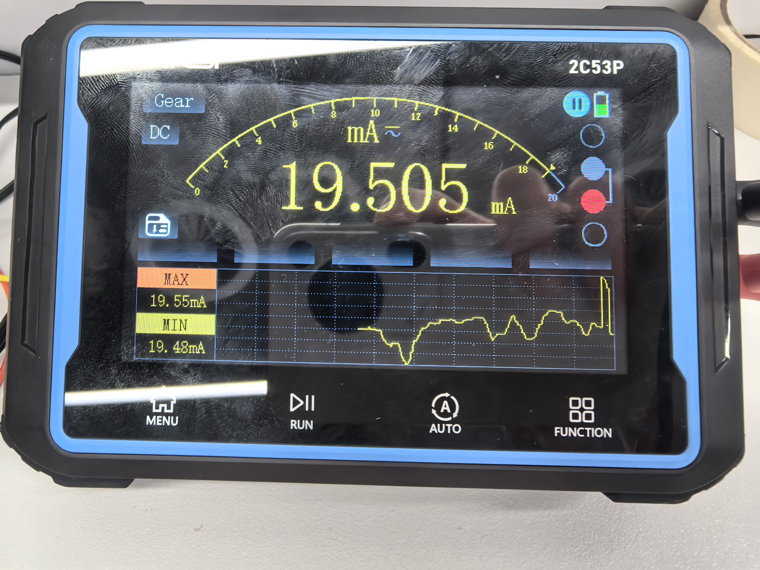
power scalability/DATA/raw/canonical/power_experiment_records/transmission/n=3/M0-M2-M3/IMG_20260907_034818.jpg
