Yannas-Sun/E-skin_MSc_final_report/power scalability/DATA/raw/canonical/power_experiment_records/transmission/n=3/M0-M2-M3/zero_load/IMG_20260907_002315.jpg

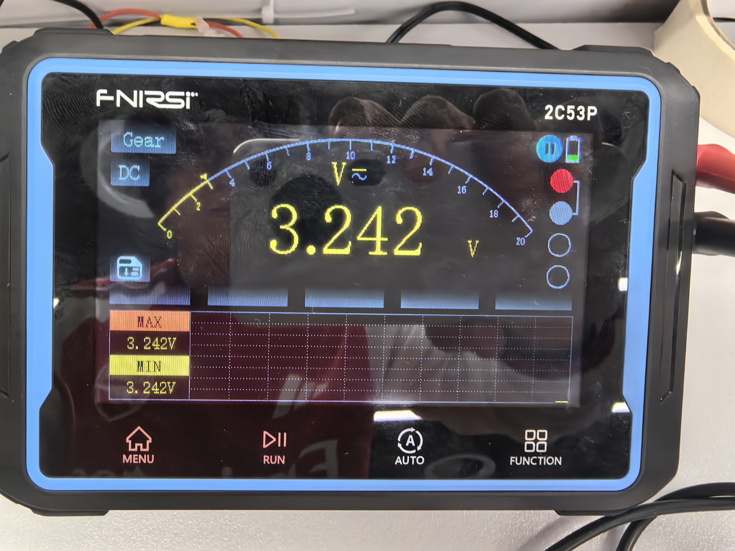
power scalability/DATA/raw/canonical/power_experiment_records/transmission/n=3/M0-M2-M3/zero_load/IMG_20260907_002315.jpg
