Yannas-Sun/E-skin_MSc_final_report/power scalability/DATA/raw/canonical/power_experiment_records/transmission/n=3/M1-M2-M3/full_load/IMG_20260905_131414.jpg

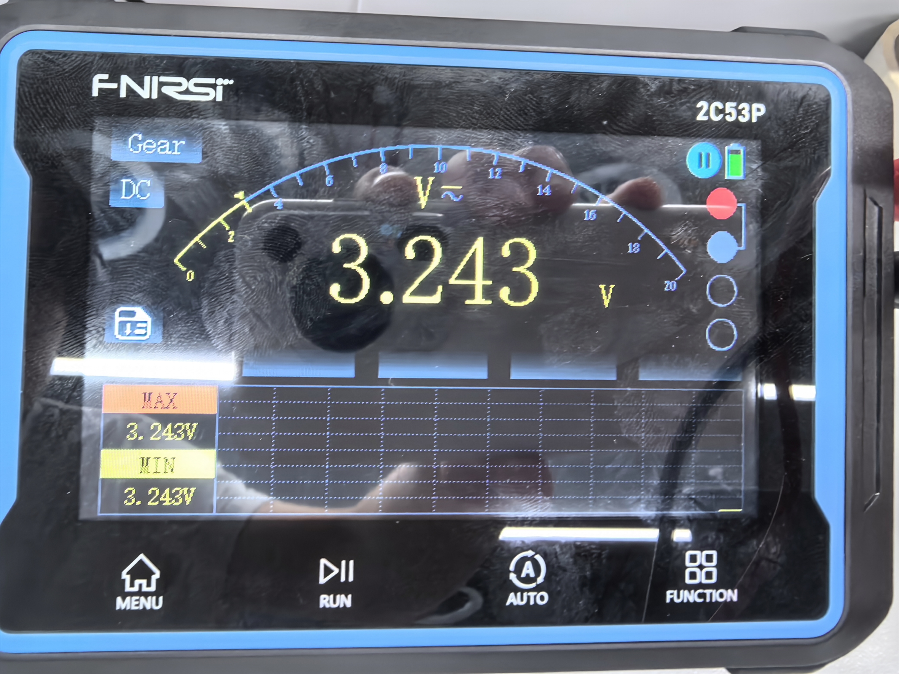
power scalability/DATA/raw/canonical/power_experiment_records/transmission/n=3/M1-M2-M3/full_load/IMG_20260905_131414.jpg
