Yannas-Sun/E-skin_MSc_final_report/power scalability/DATA/raw/canonical/power_experiment_records/transmission/n=4/M0-M1-M2-M3/zero_load/IMG_20260905_135055.jpg

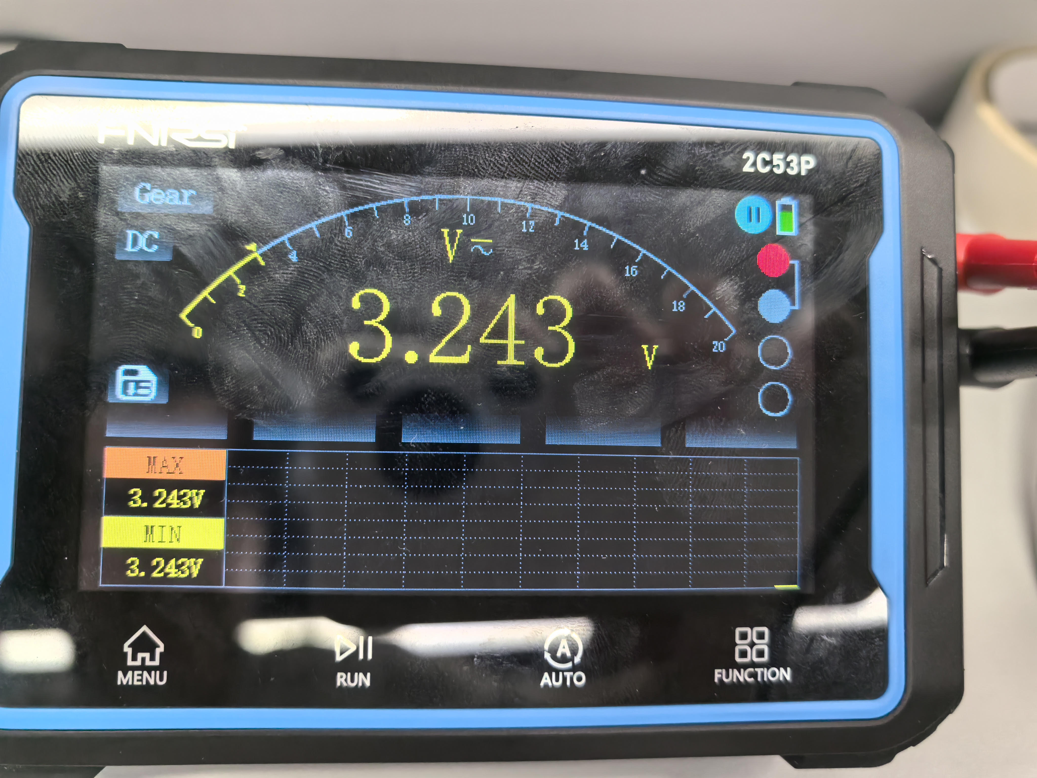
power scalability/DATA/raw/canonical/power_experiment_records/transmission/n=4/M0-M1-M2-M3/zero_load/IMG_20260905_135055.jpg
