Yannas-Sun/E-skin_MSc_final_report/power scalability/DATA/analysis/retest_reviews/m0_zero_retest_20260907/history/before_intake/README.md

# Archived or internal record

This README belongs to power scalability\DATA\analysis\retest_reviews\m0_zero_retest_20260907\history\before_intake, a superseded snapshot, audit workspace or historical report version. It is retained for provenance only and is outside the current report evidence boundary.

See the nearest current README for the release scope. No measurement data were changed.
