Yannas-Sun/E-skin_MSc_final_report/data scalability/history/pre_variable_spi_20260906/data/DELTA/Dynamic_load/M1/Small_area_3x1.6cm/README.md

# Archived or internal record

This README belongs to data scalability\history\pre_variable_spi_20260906\data\DELTA\Dynamic_load\M1\Small_area_3x1.6cm, a superseded snapshot, audit workspace or historical report version. It is retained for provenance only and is outside the current report evidence boundary.

See the nearest current README for the release scope. No measurement data were changed.
