Yannas-Sun/E-skin_MSc_final_report/data scalability/history/pre_variable_spi_20260906/path_map.csv

original_path | archived_path | sha256
D:\study\programming\ESKIN\E-SKIN\docs\Final\data scalability\data\DELTA\Dynamic_load\M1\High_frequency_rolling\README.md | D:\study\programming\ESKIN\E-SKIN\docs\Final\data scalability\history\pre_variable_spi_20260906\data\DELTA\Dynamic_load\M1\High_frequency_rolling\README.md | 45fea126f8c1d3c9d3fd77a5e45a6d27caf12c8968b1128301d009216d0d5ed4
D:\study\programming\ESKIN\E-SKIN\docs\Final\data scalability\data\DELTA\Dynamic_load\M1\High_frequency_rolling\Repeat_1\experiment_log.md | D:\study\programming\ESKIN\E-SKIN\docs\Final\data scalability\history\pre_variable_spi_20260906\data\DELTA\Dynamic_load\M1\High_frequency_rolling\Repeat_1\experiment_log.md | 1a8743d9f9aed5c6004754d883b39d02f99694f5bfcd589ccbb6c272305abeff
D:\study\programming\ESKIN\E-SKIN\docs\Final\data scalability\data\DELTA\Dynamic_load\M1\High_frequency_rolling\Repeat_1\mul1_length_over_time.png | D:\study\programming\ESKIN\E-SKIN\docs\Final\data scalability\history\pre_variable_spi_20260906\data\DELTA\Dynamic_load\M1\High_frequency_rolling\Repeat_1\mul1_length_over_time.png | 7a9e9a8a9e5156894880fdecd3fc524dee6dc3f8943035e630ff3c5b0387c312
D:\study\programming\ESKIN\E-SKIN\docs\Final\data scalability\data\DELTA\Dynamic_load\M1\High_frequency_rolling\Repeat_1\mul1_raw.bin | D:\study\programming\ESKIN\E-SKIN\docs\Final\data scalability\history\pre_variable_spi_20260906\data\DELTA\Dynamic_load\M1\High_frequency_rolling\Repeat_1\mul1_raw.bin | 94964501e7181396e8c2bb6a49d34e15a3896f27e5a4383962311514107c66a3
D:\study\programming\ESKIN\E-SKIN\docs\Final\data scalability\data\DELTA\Dynamic_load\M1\High_frequency_rolling\Repeat_1\packet_log.csv | D:\study\programming\ESKIN\E-SKIN\docs\Final\data scalability\history\pre_variable_spi_20260906\data\DELTA\Dynamic_load\M1\High_frequency_rolling\Repeat_1\packet_log.csv | 35dfae214e89cd7dbc9c5e9b46d27141aad632f9f38d773664a3e3708c87e73b
D:\study\programming\ESKIN\E-SKIN\docs\Final\data scalability\data\DELTA\Dynamic_load\M1\High_frequency_rolling\Repeat_1\plot_generation.log | D:\study\programming\ESKIN\E-SKIN\docs\Final\data scalability\history\pre_variable_spi_20260906\data\DELTA\Dynamic_load\M1\High_frequency_rolling\Repeat_1\plot_generation.log | da8efe5873693c511031bd86b8d9abf6b30dcf8aa0b2ca230f29939f089184fa
D:\study\programming\ESKIN\E-SKIN\docs\Final\data scalability\data\DELTA\Dynamic_load\M1\High_frequency_rolling\Repeat_1\summary.json | D:\study\programming\ESKIN\E-SKIN\docs\Final\data scalability\history\pre_variable_spi_20260906\data\DELTA\Dynamic_load\M1\High_frequency_rolling\Repeat_1\summary.json | cef4076467bf633e80b8a663e60f167e17f519c07737158a64bc6e5f194ac6d0
D:\study\programming\ESKIN\E-SKIN\docs\Final\data scalability\data\DELTA\Dynamic_load\M1\Large_area\README.md | D:\study\programming\ESKIN\E-SKIN\docs\Final\data scalability\history\pre_variable_spi_20260906\data\DELTA\Dynamic_load\M1\Large_area\README.md | 926332fc5febfadbbb40378ddad291528043780b651c4857d906deef2e2a639b
D:\study\programming\ESKIN\E-SKIN\docs\Final\data scalability\data\DELTA\Dynamic_load\M1\Large_area\Repeat_1\experiment_log.md | D:\study\programming\ESKIN\E-SKIN\docs\Final\data scalability\history\pre_variable_spi_20260906\data\DELTA\Dynamic_load\M1\Large_area\Repeat_1\experiment_log.md | 28498d115c5da0b53c10c7a70cdb39768cc7effe9ae79e7a841c37606d9c5409
D:\study\programming\ESKIN\E-SKIN\docs\Final\data scalability\data\DELTA\Dynamic_load\M1\Large_area\Repeat_1\mul1_length_over_time.png | D:\study\programming\ESKIN\E-SKIN\docs\Final\data scalability\history\pre_variable_spi_20260906\data\DELTA\Dynamic_load\M1\Large_area\Repeat_1\mul1_length_over_time.png | 76f6927a2fc432c7dec93d349bc9d3ca7a13ed660770c9e810afda6d59545d79
D:\study\programming\ESKIN\E-SKIN\docs\Final\data scalability\data\DELTA\Dynamic_load\M1\Large_area\Repeat_1\mul1_raw.bin | D:\study\programming\ESKIN\E-SKIN\docs\Final\data scalability\history\pre_variable_spi_20260906\data\DELTA\Dynamic_load\M1\Large_area\Repeat_1\mul1_raw.bin | d3b7c7cc282c1d6bc3ed0daddf76d2e2eaec620592e7ab3da2a066b57d9090a3
D:\study\programming\ESKIN\E-SKIN\docs\Final\data scalability\data\DELTA\Dynamic_load\M1\Large_area\Repeat_1\packet_log.csv | D:\study\programming\ESKIN\E-SKIN\docs\Final\data scalability\history\pre_variable_spi_20260906\data\DELTA\Dynamic_load\M1\Large_area\Repeat_1\packet_log.csv | 618699de898e86c10d74a4ea382791499290a6fb3b9971e4446fdc3affa84fbe
D:\study\programming\ESKIN\E-SKIN\docs\Final\data scalability\data\DELTA\Dynamic_load\M1\Large_area\Repeat_1\plot_generation.log | D:\study\programming\ESKIN\E-SKIN\docs\Final\data scalability\history\pre_variable_spi_20260906\data\DELTA\Dynamic_load\M1\Large_area\Repeat_1\plot_generation.log | 916ca83dbcee60daa9b0ba28e128d9dc2a5c9e6ad811454f9bf18ff083f7fd96
D:\study\programming\ESKIN\E-SKIN\docs\Final\data scalability\data\DELTA\Dynamic_load\M1\Large_area\Repeat_1\summary.json | D:\study\programming\ESKIN\E-SKIN\docs\Final\data scalability\history\pre_variable_spi_20260906\data\DELTA\Dynamic_load\M1\Large_area\Repeat_1\summary.json | 25ee4e4e71c6ae752f16b8154c41a62593b1d91515b4ab807a42f8872868467c
D:\study\programming\ESKIN\E-SKIN\docs\Final\data scalability\data\DELTA\Dynamic_load\M1\Large_area\Repeat_2\experiment_log.md | D:\study\programming\ESKIN\E-SKIN\docs\Final\data scalability\history\pre_variable_spi_20260906\data\DELTA\Dynamic_load\M1\Large_area\Repeat_2\experiment_log.md | 9609564f59794c2fbfc5e37c789e01359c28ccf165ce5862e725198edce8b1d3
D:\study\programming\ESKIN\E-SKIN\docs\Final\data scalability\data\DELTA\Dynamic_load\M1\Large_area\Repeat_2\mul1_length_over_time.png | D:\study\programming\ESKIN\E-SKIN\docs\Final\data scalability\history\pre_variable_spi_20260906\data\DELTA\Dynamic_load\M1\Large_area\Repeat_2\mul1_length_over_time.png | 1f826d5509ac9e4b4e7dfe936e68e262a4d8d7f1be8f73f26983e4405b3d86dd
D:\study\programming\ESKIN\E-SKIN\docs\Final\data scalability\data\DELTA\Dynamic_load\M1\Large_area\Repeat_2\mul1_raw.bin | D:\study\programming\ESKIN\E-SKIN\docs\Final\data scalability\history\pre_variable_spi_20260906\data\DELTA\Dynamic_load\M1\Large_area\Repeat_2\mul1_raw.bin | 328f654f513071b14c7a1e47ad6953a2050fe19fe3752dd6f38ad0ccee1706e5
D:\study\programming\ESKIN\E-SKIN\docs\Final\data scalability\data\DELTA\Dynamic_load\M1\Large_area\Repeat_2\packet_log.csv | D:\study\programming\ESKIN\E-SKIN\docs\Final\data scalability\history\pre_variable_spi_20260906\data\DELTA\Dynamic_load\M1\Large_area\Repeat_2\packet_log.csv | 9cad40018e6fadcfefda100861195997d24ffeb1956cde015f3c5684fbcd1c30
D:\study\programming\ESKIN\E-SKIN\docs\Final\data scalability\data\DELTA\Dynamic_load\M1\Large_area\Repeat_2\plot_generation.log | D:\study\programming\ESKIN\E-SKIN\docs\Final\data scalability\history\pre_variable_spi_20260906\data\DELTA\Dynamic_load\M1\Large_area\Repeat_2\plot_generation.log | 20aec7e4d75988b78f793f280a5fd15d9588fd29e234df456413bd6330db9cd8
D:\study\programming\ESKIN\E-SKIN\docs\Final\data scalability\data\DELTA\Dynamic_load\M1\Large_area\Repeat_2\summary.json | D:\study\programming\ESKIN\E-SKIN\docs\Final\data scalability\history\pre_variable_spi_20260906\data\DELTA\Dynamic_load\M1\Large_area\Repeat_2\summary.json | 125fca03e45e8fae896eedff0aa89c69231ec222bbc6072b2a66952fce28ea35
D:\study\programming\ESKIN\E-SKIN\docs\Final\data scalability\data\DELTA\Dynamic_load\M1\Large_area\Repeat_3\experiment_log.md | D:\study\programming\ESKIN\E-SKIN\docs\Final\data scalability\history\pre_variable_spi_20260906\data\DELTA\Dynamic_load\M1\Large_area\Repeat_3\experiment_log.md | d2768f5b24ca650f66b2daf948ca75dc14f1ad884b0ef9cfb63004c1464b9d9e
D:\study\programming\ESKIN\E-SKIN\docs\Final\data scalability\data\DELTA\Dynamic_load\M1\Large_area\Repeat_3\mul1_length_over_time.png | D:\study\programming\ESKIN\E-SKIN\docs\Final\data scalability\history\pre_variable_spi_20260906\data\DELTA\Dynamic_load\M1\Large_area\Repeat_3\mul1_length_over_time.png | 2f2555a51ac4cd8a9e7e5a0b7da79700d9b9af8f47b2b2a279b9877e0ad1bef8
D:\study\programming\ESKIN\E-SKIN\docs\Final\data scalability\data\DELTA\Dynamic_load\M1\Large_area\Repeat_3\mul1_raw.bin | D:\study\programming\ESKIN\E-SKIN\docs\Final\data scalability\history\pre_variable_spi_20260906\data\DELTA\Dynamic_load\M1\Large_area\Repeat_3\mul1_raw.bin | fd73837900359fb22c051368b9c5c86b07fd569c369d1ffa49adf5f105c67621
D:\study\programming\ESKIN\E-SKIN\docs\Final\data scalability\data\DELTA\Dynamic_load\M1\Large_area\Repeat_3\packet_log.csv | D:\study\programming\ESKIN\E-SKIN\docs\Final\data scalability\history\pre_variable_spi_20260906\data\DELTA\Dynamic_load\M1\Large_area\Repeat_3\packet_log.csv | 47b15e0fe60d0ad96b41a3cad1da0ee534302215a3a091bd496e63b5bf18e134
D:\study\programming\ESKIN\E-SKIN\docs\Final\data scalability\data\DELTA\Dynamic_load\M1\Large_area\Repeat_3\plot_generation.log | D:\study\programming\ESKIN\E-SKIN\docs\Final\data scalability\history\pre_variable_spi_20260906\data\DELTA\Dynamic_load\M1\Large_area\Repeat_3\plot_generation.log | afd2c7867e9fd80f99a11657fa51b53b917af4ac421a688d38cdb6552e91205a
D:\study\programming\ESKIN\E-SKIN\docs\Final\data scalability\data\DELTA\Dynamic_load\M1\Large_area\Repeat_3\summary.json | D:\study\programming\ESKIN\E-SKIN\docs\Final\data scalability\history\pre_variable_spi_20260906\data\DELTA\Dynamic_load\M1\Large_area\Repeat_3\summary.json | 1ef03045e44b3de6ab1761ab13f7d6b3164cbd5e489413ce5aec5349bb9d2301
D:\study\programming\ESKIN\E-SKIN\docs\Final\data scalability\data\DELTA\Dynamic_load\M1\Large_area\Repeat_4\experiment_log.md | D:\study\programming\ESKIN\E-SKIN\docs\Final\data scalability\history\pre_variable_spi_20260906\data\DELTA\Dynamic_load\M1\Large_area\Repeat_4\experiment_log.md | 1562b65a90aa4144c5f2c6967a331d30a4fbbb5ecf68f9a09e3fcc761aca6e3e
D:\study\programming\ESKIN\E-SKIN\docs\Final\data scalability\data\DELTA\Dynamic_load\M1\Large_area\Repeat_4\mul1_length_over_time.png | D:\study\programming\ESKIN\E-SKIN\docs\Final\data scalability\history\pre_variable_spi_20260906\data\DELTA\Dynamic_load\M1\Large_area\Repeat_4\mul1_length_over_time.png | a4e832be70df698ca6fcf89878493b41b6487d0f25d19de0fd0a03faf809254e
D:\study\programming\ESKIN\E-SKIN\docs\Final\data scalability\data\DELTA\Dynamic_load\M1\Large_area\Repeat_4\mul1_raw.bin | D:\study\programming\ESKIN\E-SKIN\docs\Final\data scalability\history\pre_variable_spi_20260906\data\DELTA\Dynamic_load\M1\Large_area\Repeat_4\mul1_raw.bin | 168e6912d3d7adb2e4854abfcf35e8e44e4ab9a587261323240f012b3a0ebaef
D:\study\programming\ESKIN\E-SKIN\docs\Final\data scalability\data\DELTA\Dynamic_load\M1\Large_area\Repeat_4\packet_log.csv | D:\study\programming\ESKIN\E-SKIN\docs\Final\data scalability\history\pre_variable_spi_20260906\data\DELTA\Dynamic_load\M1\Large_area\Repeat_4\packet_log.csv | 6563060fab83ba2d180cff62bb0c0f05a89f8aeba8051de93f428180d2dfaa96
D:\study\programming\ESKIN\E-SKIN\docs\Final\data scalability\data\DELTA\Dynamic_load\M1\Large_area\Repeat_4\plot_generation.log | D:\study\programming\ESKIN\E-SKIN\docs\Final\data scalability\history\pre_variable_spi_20260906\data\DELTA\Dynamic_load\M1\Large_area\Repeat_4\plot_generation.log | a60d2f5f5fd7fb0e214f0d5fd276ef568396b28b8103b69dfc676a0887ad9337
D:\study\programming\ESKIN\E-SKIN\docs\Final\data scalability\data\DELTA\Dynamic_load\M1\Large_area\Repeat_4\summary.json | D:\study\programming\ESKIN\E-SKIN\docs\Final\data scalability\history\pre_variable_spi_20260906\data\DELTA\Dynamic_load\M1\Large_area\Repeat_4\summary.json | 673d40a308506f39e1e610a8e18f19353cb69500540bd8165abebec05238cf13
D:\study\programming\ESKIN\E-SKIN\docs\Final\data scalability\data\DELTA\Dynamic_load\M1\Large_area\Repeat_5\experiment_log.md | D:\study\programming\ESKIN\E-SKIN\docs\Final\data scalability\history\pre_variable_spi_20260906\data\DELTA\Dynamic_load\M1\Large_area\Repeat_5\experiment_log.md | 7d2cb3d607ea56537a96901d6f6dbf23ffa0a18cca4b8957d47584b94dfbdca5
D:\study\programming\ESKIN\E-SKIN\docs\Final\data scalability\data\DELTA\Dynamic_load\M1\Large_area\Repeat_5\mul1_length_over_time.png | D:\study\programming\ESKIN\E-SKIN\docs\Final\data scalability\history\pre_variable_spi_20260906\data\DELTA\Dynamic_load\M1\Large_area\Repeat_5\mul1_length_over_time.png | 56c3aafdd1c7f3e3c1de86db841379d67958b2b58cbf65059519751330a78863
D:\study\programming\ESKIN\E-SKIN\docs\Final\data scalability\data\DELTA\Dynamic_load\M1\Large_area\Repeat_5\mul1_raw.bin | D:\study\programming\ESKIN\E-SKIN\docs\Final\data scalability\history\pre_variable_spi_20260906\data\DELTA\Dynamic_load\M1\Large_area\Repeat_5\mul1_raw.bin | 40044f9017af19b7681b9b072e9e5a23f3a5fbb0c6d92efeffd2cbf9f541bb87
D:\study\programming\ESKIN\E-SKIN\docs\Final\data scalability\data\DELTA\Dynamic_load\M1\Large_area\Repeat_5\packet_log.csv | D:\study\programming\ESKIN\E-SKIN\docs\Final\data scalability\history\pre_variable_spi_20260906\data\DELTA\Dynamic_load\M1\Large_area\Repeat_5\packet_log.csv | b911024979ccb65239ecee6a568225e99b079bd8db1d591b0a33bbfe858270ba
D:\study\programming\ESKIN\E-SKIN\docs\Final\data scalability\data\DELTA\Dynamic_load\M1\Large_area\Repeat_5\plot_generation.log | D:\study\programming\ESKIN\E-SKIN\docs\Final\data scalability\history\pre_variable_spi_20260906\data\DELTA\Dynamic_load\M1\Large_area\Repeat_5\plot_generation.log | e2799a8ff34ae355fdca0d86caea8b4aed84f8b2a433554fec1b0da128f33289
D:\study\programming\ESKIN\E-SKIN\docs\Final\data scalability\data\DELTA\Dynamic_load\M1\Large_area\Repeat_5\summary.json | D:\study\programming\ESKIN\E-SKIN\docs\Final\data scalability\history\pre_variable_spi_20260906\data\DELTA\Dynamic_load\M1\Large_area\Repeat_5\summary.json | 9539102ba705d4f0e83438572b38defc1fca33aef9d3b5d02d01f79fefd1d575
D:\study\programming\ESKIN\E-SKIN\docs\Final\data scalability\data\DELTA\Dynamic_load\M1\Large_area\Repeat_6\experiment_log.md | D:\study\programming\ESKIN\E-SKIN\docs\Final\data scalability\history\pre_variable_spi_20260906\data\DELTA\Dynamic_load\M1\Large_area\Repeat_6\experiment_log.md | da37fd80e0d4174382ac7dcf5ca83bfd35bd3954dcfefbd5cb7a6963bd0dbb1e
D:\study\programming\ESKIN\E-SKIN\docs\Final\data scalability\data\DELTA\Dynamic_load\M1\Large_area\Repeat_6\mul1_length_over_time.png | D:\study\programming\ESKIN\E-SKIN\docs\Final\data scalability\history\pre_variable_spi_20260906\data\DELTA\Dynamic_load\M1\Large_area\Repeat_6\mul1_length_over_time.png | 20c848a37e0b759015ade474536ec20efddc9aaeee0ad53ac36ac573ea5180e6
D:\study\programming\ESKIN\E-SKIN\docs\Final\data scalability\data\DELTA\Dynamic_load\M1\Large_area\Repeat_6\mul1_raw.bin | D:\study\programming\ESKIN\E-SKIN\docs\Final\data scalability\history\pre_variable_spi_20260906\data\DELTA\Dynamic_load\M1\Large_area\Repeat_6\mul1_raw.bin | 0dbf4c8bb3e37462840fc44403f25cc59ceae8a85ec586ece38004edf9828ce4
D:\study\programming\ESKIN\E-SKIN\docs\Final\data scalability\data\DELTA\Dynamic_load\M1\Large_area\Repeat_6\packet_log.csv | D:\study\programming\ESKIN\E-SKIN\docs\Final\data scalability\history\pre_variable_spi_20260906\data\DELTA\Dynamic_load\M1\Large_area\Repeat_6\packet_log.csv | 20c88be804acf4aaf53f1c8ce904e6f3a1108209aeb5845931e7f6e4c3577cab
D:\study\programming\ESKIN\E-SKIN\docs\Final\data scalability\data\DELTA\Dynamic_load\M1\Large_area\Repeat_6\plot_generation.log | D:\study\programming\ESKIN\E-SKIN\docs\Final\data scalability\history\pre_variable_spi_20260906\data\DELTA\Dynamic_load\M1\Large_area\Repeat_6\plot_generation.log | 41b8bdf0778a87986aeb03827a7cc2ee139203008b1122bee56082665688b7eb
D:\study\programming\ESKIN\E-SKIN\docs\Final\data scalability\data\DELTA\Dynamic_load\M1\Large_area\Repeat_6\summary.json | D:\study\programming\ESKIN\E-SKIN\docs\Final\data scalability\history\pre_variable_spi_20260906\data\DELTA\Dynamic_load\M1\Large_area\Repeat_6\summary.json | 3e340f00cb5347fe5989b7952f4d6d4bc4f4e08d5dc2ef7b52e83fbc4f2674c8
D:\study\programming\ESKIN\E-SKIN\docs\Final\data scalability\data\DELTA\Dynamic_load\M1\Small_area_3x1.6cm\README.md | D:\study\programming\ESKIN\E-SKIN\docs\Final\data scalability\history\pre_variable_spi_20260906\data\DELTA\Dynamic_load\M1\Small_area_3x1.6cm\README.md | f7ab1db0fe39c1dc4f255fe4b79e67d49cb6b36fd110441e31b9f3a4f8a27ced
D:\study\programming\ESKIN\E-SKIN\docs\Final\data scalability\data\DELTA\Dynamic_load\M1\Small_area_3x1.6cm\Repeat_1\experiment_log.md | D:\study\programming\ESKIN\E-SKIN\docs\Final\data scalability\history\pre_variable_spi_20260906\data\DELTA\Dynamic_load\M1\Small_area_3x1.6cm\Repeat_1\experiment_log.md | bfe39f9dc3de926e44d4ee22463bb982014b2954f46f52aab45fa92ec94b86ae
D:\study\programming\ESKIN\E-SKIN\docs\Final\data scalability\data\DELTA\Dynamic_load\M1\Small_area_3x1.6cm\Repeat_1\mul1_length_over_time.png | D:\study\programming\ESKIN\E-SKIN\docs\Final\data scalability\history\pre_variable_spi_20260906\data\DELTA\Dynamic_load\M1\Small_area_3x1.6cm\Repeat_1\mul1_length_over_time.png | 7ad092bdc1872bf4ae71c5dbd6677453b7dc93f4b4082e776b5c4f069a854a82
D:\study\programming\ESKIN\E-SKIN\docs\Final\data scalability\data\DELTA\Dynamic_load\M1\Small_area_3x1.6cm\Repeat_1\mul1_raw.bin | D:\study\programming\ESKIN\E-SKIN\docs\Final\data scalability\history\pre_variable_spi_20260906\data\DELTA\Dynamic_load\M1\Small_area_3x1.6cm\Repeat_1\mul1_raw.bin | e4e08e6d3ee88621ecf8229d984cb67d302d1e493c6990041c59b8feeb1804c0
D:\study\programming\ESKIN\E-SKIN\docs\Final\data scalability\data\DELTA\Dynamic_load\M1\Small_area_3x1.6cm\Repeat_1\packet_log.csv | D:\study\programming\ESKIN\E-SKIN\docs\Final\data scalability\history\pre_variable_spi_20260906\data\DELTA\Dynamic_load\M1\Small_area_3x1.6cm\Repeat_1\packet_log.csv | 18459b2d9cd48cee9bb5da2b02a1384a98f809e80f1fd5e87c97e73582bff1a8
D:\study\programming\ESKIN\E-SKIN\docs\Final\data scalability\data\DELTA\Dynamic_load\M1\Small_area_3x1.6cm\Repeat_1\plot_generation.log | D:\study\programming\ESKIN\E-SKIN\docs\Final\data scalability\history\pre_variable_spi_20260906\data\DELTA\Dynamic_load\M1\Small_area_3x1.6cm\Repeat_1\plot_generation.log | 535876fc861579dbefdaa7c79d985db4a2668e15eb5a363cb2f4aef4586b1ade
D:\study\programming\ESKIN\E-SKIN\docs\Final\data scalability\data\DELTA\Dynamic_load\M1\Small_area_3x1.6cm\Repeat_1\summary.json | D:\study\programming\ESKIN\E-SKIN\docs\Final\data scalability\history\pre_variable_spi_20260906\data\DELTA\Dynamic_load\M1\Small_area_3x1.6cm\Repeat_1\summary.json | 45a3b1bf73dec3247cdd9c75f1e56b6783cb3b2787fd52b6c916cfe684437396
D:\study\programming\ESKIN\E-SKIN\docs\Final\data scalability\data\DELTA\Dynamic_load\M1\Small_area_3x1.6cm\Repeat_2\experiment_log.md | D:\study\programming\ESKIN\E-SKIN\docs\Final\data scalability\history\pre_variable_spi_20260906\data\DELTA\Dynamic_load\M1\Small_area_3x1.6cm\Repeat_2\experiment_log.md | cb250b174baf54986405b72cccdf4cbd54280814591ef844c64699c279c47781
D:\study\programming\ESKIN\E-SKIN\docs\Final\data scalability\data\DELTA\Dynamic_load\M1\Small_area_3x1.6cm\Repeat_2\mul1_length_over_time.png | D:\study\programming\ESKIN\E-SKIN\docs\Final\data scalability\history\pre_variable_spi_20260906\data\DELTA\Dynamic_load\M1\Small_area_3x1.6cm\Repeat_2\mul1_length_over_time.png | ef36b5d064ac1110c7bf59b24f8591e0e617cc1940b5e21998303d77ffbe7566
D:\study\programming\ESKIN\E-SKIN\docs\Final\data scalability\data\DELTA\Dynamic_load\M1\Small_area_3x1.6cm\Repeat_2\mul1_raw.bin | D:\study\programming\ESKIN\E-SKIN\docs\Final\data scalability\history\pre_variable_spi_20260906\data\DELTA\Dynamic_load\M1\Small_area_3x1.6cm\Repeat_2\mul1_raw.bin | 62578ea0890ef4179ab69d2cb7fb8dcfe3f95aa33ad3598c627f12587f02ea8d
D:\study\programming\ESKIN\E-SKIN\docs\Final\data scalability\data\DELTA\Dynamic_load\M1\Small_area_3x1.6cm\Repeat_2\packet_log.csv | D:\study\programming\ESKIN\E-SKIN\docs\Final\data scalability\history\pre_variable_spi_20260906\data\DELTA\Dynamic_load\M1\Small_area_3x1.6cm\Repeat_2\packet_log.csv | bfd2deddf32780968efb6d394642f5051afa45b7f409e3a3084becdb0b76bdcb
D:\study\programming\ESKIN\E-SKIN\docs\Final\data scalability\data\DELTA\Dynamic_load\M1\Small_area_3x1.6cm\Repeat_2\plot_generation.log | D:\study\programming\ESKIN\E-SKIN\docs\Final\data scalability\history\pre_variable_spi_20260906\data\DELTA\Dynamic_load\M1\Small_area_3x1.6cm\Repeat_2\plot_generation.log | 611890be52cdc41758e3cc4e0bb60973b86f40fcff19bc0ee36f45edfff86cc6
D:\study\programming\ESKIN\E-SKIN\docs\Final\data scalability\data\DELTA\Dynamic_load\M1\Small_area_3x1.6cm\Repeat_2\summary.json | D:\study\programming\ESKIN\E-SKIN\docs\Final\data scalability\history\pre_variable_spi_20260906\data\DELTA\Dynamic_load\M1\Small_area_3x1.6cm\Repeat_2\summary.json | 3c774cb76fae8fe18a8aebe39f8d2084afc73e542b2bf9779637394acc74be0e
D:\study\programming\ESKIN\E-SKIN\docs\Final\data scalability\data\DELTA\Dynamic_load\M1\Small_area_3x1.6cm\Repeat_3\experiment_log.md | D:\study\programming\ESKIN\E-SKIN\docs\Final\data scalability\history\pre_variable_spi_20260906\data\DELTA\Dynamic_load\M1\Small_area_3x1.6cm\Repeat_3\experiment_log.md | 44e7574c1ee20fc59e6e81d1492d99873bee800a0a3718c9c90db429d2fda1bf
D:\study\programming\ESKIN\E-SKIN\docs\Final\data scalability\data\DELTA\Dynamic_load\M1\Small_area_3x1.6cm\Repeat_3\mul1_length_over_time.png | D:\study\programming\ESKIN\E-SKIN\docs\Final\data scalability\history\pre_variable_spi_20260906\data\DELTA\Dynamic_load\M1\Small_area_3x1.6cm\Repeat_3\mul1_length_over_time.png | 732ee262029351d4f5f8fc2cff11afcdb4def98e93c4f1b0684b83671f58b263
D:\study\programming\ESKIN\E-SKIN\docs\Final\data scalability\data\DELTA\Dynamic_load\M1\Small_area_3x1.6cm\Repeat_3\mul1_raw.bin | D:\study\programming\ESKIN\E-SKIN\docs\Final\data scalability\history\pre_variable_spi_20260906\data\DELTA\Dynamic_load\M1\Small_area_3x1.6cm\Repeat_3\mul1_raw.bin | 2b5c49a20e207b4ed25b84c7da7643219e4bf8c65a8744469a8c54caa18f1f2b
D:\study\programming\ESKIN\E-SKIN\docs\Final\data scalability\data\DELTA\Dynamic_load\M1\Small_area_3x1.6cm\Repeat_3\packet_log.csv | D:\study\programming\ESKIN\E-SKIN\docs\Final\data scalability\history\pre_variable_spi_20260906\data\DELTA\Dynamic_load\M1\Small_area_3x1.6cm\Repeat_3\packet_log.csv | 3acf51b64c12e69cb690287db7350e45d750ed88e71485cf91c96c02bd625a2d
D:\study\programming\ESKIN\E-SKIN\docs\Final\data scalability\data\DELTA\Dynamic_load\M1\Small_area_3x1.6cm\Repeat_3\plot_generation.log | D:\study\programming\ESKIN\E-SKIN\docs\Final\data scalability\history\pre_variable_spi_20260906\data\DELTA\Dynamic_load\M1\Small_area_3x1.6cm\Repeat_3\plot_generation.log | 0dee0f862b06c7ccb7152af66951d0b56601397853579de5e60a132cb2e88282
D:\study\programming\ESKIN\E-SKIN\docs\Final\data scalability\data\DELTA\Dynamic_load\M1\Small_area_3x1.6cm\Repeat_3\summary.json | D:\study\programming\ESKIN\E-SKIN\docs\Final\data scalability\history\pre_variable_spi_20260906\data\DELTA\Dynamic_load\M1\Small_area_3x1.6cm\Repeat_3\summary.json | e0246af500325dd9efdbe1bbc208300dacc5a691e9b195f46a08c330debe157f
D:\study\programming\ESKIN\E-SKIN\docs\Final\data scalability\data\DELTA\Dynamic_load\M1\Small_area_3x1.6cm\Repeat_4\experiment_log.md | D:\study\programming\ESKIN\E-SKIN\docs\Final\data scalability\history\pre_variable_spi_20260906\data\DELTA\Dynamic_load\M1\Small_area_3x1.6cm\Repeat_4\experiment_log.md | d749a660841679238e8c8f3d661fd507fd18ffe09d0189eb746fd87584917206
D:\study\programming\ESKIN\E-SKIN\docs\Final\data scalability\data\DELTA\Dynamic_load\M1\Small_area_3x1.6cm\Repeat_4\mul1_length_over_time.png | D:\study\programming\ESKIN\E-SKIN\docs\Final\data scalability\history\pre_variable_spi_20260906\data\DELTA\Dynamic_load\M1\Small_area_3x1.6cm\Repeat_4\mul1_length_over_time.png | fd4d8cc0bd16317233bac18d38ba4d50c611e6c80f819e11ca7237d668aecae4
D:\study\programming\ESKIN\E-SKIN\docs\Final\data scalability\data\DELTA\Dynamic_load\M1\Small_area_3x1.6cm\Repeat_4\mul1_raw.bin | D:\study\programming\ESKIN\E-SKIN\docs\Final\data scalability\history\pre_variable_spi_20260906\data\DELTA\Dynamic_load\M1\Small_area_3x1.6cm\Repeat_4\mul1_raw.bin | 9eb2c180c74c905c310024bf1cf06a7079ce16ba7fd0ad779f46c148f9ab92aa
D:\study\programming\ESKIN\E-SKIN\docs\Final\data scalability\data\DELTA\Dynamic_load\M1\Small_area_3x1.6cm\Repeat_4\packet_log.csv | D:\study\programming\ESKIN\E-SKIN\docs\Final\data scalability\history\pre_variable_spi_20260906\data\DELTA\Dynamic_load\M1\Small_area_3x1.6cm\Repeat_4\packet_log.csv | 8d56d59716b9e0cb17e3a262c450fc3172d3e839cf378dedcbde675334384a38
D:\study\programming\ESKIN\E-SKIN\docs\Final\data scalability\data\DELTA\Dynamic_load\M1\Small_area_3x1.6cm\Repeat_4\plot_generation.log | D:\study\programming\ESKIN\E-SKIN\docs\Final\data scalability\history\pre_variable_spi_20260906\data\DELTA\Dynamic_load\M1\Small_area_3x1.6cm\Repeat_4\plot_generation.log | eecc62ee036cefec41e2c523152ddc0287ba766c7f4708214160be711844305c
D:\study\programming\ESKIN\E-SKIN\docs\Final\data scalability\data\DELTA\Dynamic_load\M1\Small_area_3x1.6cm\Repeat_4\summary.json | D:\study\programming\ESKIN\E-SKIN\docs\Final\data scalability\history\pre_variable_spi_20260906\data\DELTA\Dynamic_load\M1\Small_area_3x1.6cm\Repeat_4\summary.json | 799edb93a15ce9a7181f2b87db722cac7fc1266c1ddc2bb3b9351aa3c5c2f300
D:\study\programming\ESKIN\E-SKIN\docs\Final\data scalability\data\DELTA\Dynamic_load\M1\Small_area_3x1.6cm\Repeat_5\experiment_log.md | D:\study\programming\ESKIN\E-SKIN\docs\Final\data scalability\history\pre_variable_spi_20260906\data\DELTA\Dynamic_load\M1\Small_area_3x1.6cm\Repeat_5\experiment_log.md | 60b6bf40ae8cc82f7ca86fc952d3cdb9d5e1537a3233a42574066474e5a5651a
D:\study\programming\ESKIN\E-SKIN\docs\Final\data scalability\data\DELTA\Dynamic_load\M1\Small_area_3x1.6cm\Repeat_5\mul1_length_over_time.png | D:\study\programming\ESKIN\E-SKIN\docs\Final\data scalability\history\pre_variable_spi_20260906\data\DELTA\Dynamic_load\M1\Small_area_3x1.6cm\Repeat_5\mul1_length_over_time.png | b11f070c0d4ec990efcc523ac0db2c58ca611821e481e69c3a332b7303b4aff3
D:\study\programming\ESKIN\E-SKIN\docs\Final\data scalability\data\DELTA\Dynamic_load\M1\Small_area_3x1.6cm\Repeat_5\mul1_raw.bin | D:\study\programming\ESKIN\E-SKIN\docs\Final\data scalability\history\pre_variable_spi_20260906\data\DELTA\Dynamic_load\M1\Small_area_3x1.6cm\Repeat_5\mul1_raw.bin | cc3aaa05dbf24fae103ca7ef97d27f89806aa9778f452e165cd1b6a1614d4c65
D:\study\programming\ESKIN\E-SKIN\docs\Final\data scalability\data\DELTA\Dynamic_load\M1\Small_area_3x1.6cm\Repeat_5\packet_log.csv | D:\study\programming\ESKIN\E-SKIN\docs\Final\data scalability\history\pre_variable_spi_20260906\data\DELTA\Dynamic_load\M1\Small_area_3x1.6cm\Repeat_5\packet_log.csv | 4e601793a6f183197facdcb81b849c5dceffa1f1e274fe3a9fa03aff6e02ee79
D:\study\programming\ESKIN\E-SKIN\docs\Final\data scalability\data\DELTA\Dynamic_load\M1\Small_area_3x1.6cm\Repeat_5\plot_generation.log | D:\study\programming\ESKIN\E-SKIN\docs\Final\data scalability\history\pre_variable_spi_20260906\data\DELTA\Dynamic_load\M1\Small_area_3x1.6cm\Repeat_5\plot_generation.log | a88117191189272e7d4ad14cc48d969d418cf8e45fe3167293fab5f0da2752d5
D:\study\programming\ESKIN\E-SKIN\docs\Final\data scalability\data\DELTA\Dynamic_load\M1\Small_area_3x1.6cm\Repeat_5\summary.json | D:\study\programming\ESKIN\E-SKIN\docs\Final\data scalability\history\pre_variable_spi_20260906\data\DELTA\Dynamic_load\M1\Small_area_3x1.6cm\Repeat_5\summary.json | 73b9c1fb9768c9aa32d5f517717e75c2fba18a3612e1c2a349c7c132e4e3a652
D:\study\programming\ESKIN\E-SKIN\docs\Final\data scalability\data\DELTA\Dynamic_load\M1\Small_area_3x1.6cm\Repeat_6\experiment_log.md | D:\study\programming\ESKIN\E-SKIN\docs\Final\data scalability\history\pre_variable_spi_20260906\data\DELTA\Dynamic_load\M1\Small_area_3x1.6cm\Repeat_6\experiment_log.md | 6b6403e9f2987a1de76cce62091995266ea886ce1080ca0e58eadfa20fcf0c7d
D:\study\programming\ESKIN\E-SKIN\docs\Final\data scalability\data\DELTA\Dynamic_load\M1\Small_area_3x1.6cm\Repeat_6\mul1_length_over_time.png | D:\study\programming\ESKIN\E-SKIN\docs\Final\data scalability\history\pre_variable_spi_20260906\data\DELTA\Dynamic_load\M1\Small_area_3x1.6cm\Repeat_6\mul1_length_over_time.png | 56873935c75afe67e7bebf290aaa53684679cc6296db71ba272a679dab4296b7
D:\study\programming\ESKIN\E-SKIN\docs\Final\data scalability\data\DELTA\Dynamic_load\M1\Small_area_3x1.6cm\Repeat_6\mul1_raw.bin | D:\study\programming\ESKIN\E-SKIN\docs\Final\data scalability\history\pre_variable_spi_20260906\data\DELTA\Dynamic_load\M1\Small_area_3x1.6cm\Repeat_6\mul1_raw.bin | 8e4db76b06f4cd42b54ea0b0b272ea16ebe42873822ff39d6dde65ba543ace0b
D:\study\programming\ESKIN\E-SKIN\docs\Final\data scalability\data\DELTA\Dynamic_load\M1\Small_area_3x1.6cm\Repeat_6\packet_log.csv | D:\study\programming\ESKIN\E-SKIN\docs\Final\data scalability\history\pre_variable_spi_20260906\data\DELTA\Dynamic_load\M1\Small_area_3x1.6cm\Repeat_6\packet_log.csv | f27a47b5c7f5bca8090b7a30d1ec4b21830625b6e0830fcfc25f2f136a002773
D:\study\programming\ESKIN\E-SKIN\docs\Final\data scalability\data\DELTA\Dynamic_load\M1\Small_area_3x1.6cm\Repeat_6\plot_generation.log | D:\study\programming\ESKIN\E-SKIN\docs\Final\data scalability\history\pre_variable_spi_20260906\data\DELTA\Dynamic_load\M1\Small_area_3x1.6cm\Repeat_6\plot_generation.log | 97cf12a6891f5e43b49ecc07684839c2c583cfea56de804fef5574180ad6a6a8
D:\study\programming\ESKIN\E-SKIN\docs\Final\data scalability\data\DELTA\Dynamic_load\M1\Small_area_3x1.6cm\Repeat_6\summary.json | D:\study\programming\ESKIN\E-SKIN\docs\Final\data scalability\history\pre_variable_spi_20260906\data\DELTA\Dynamic_load\M1\Small_area_3x1.6cm\Repeat_6\summary.json | 73c55d8d332618021796023c3f0e1baa7b0e7120aed824b8edece8bf68ab6920
D:\study\programming\ESKIN\E-SKIN\docs\Final\data scalability\data\DELTA\Dynamic_load\N=2\M1_M3\Full_coverage_all_FSR\README.md | D:\study\programming\ESKIN\E-SKIN\docs\Final\data scalability\history\pre_variable_spi_20260906\data\DELTA\Dynamic_load\N=2\M1_M3\Full_coverage_all_FSR\README.md | b72344fb562201cb243e3b17703a10625543fb76b31ff6d12f9f6ef99f1c5905
D:\study\programming\ESKIN\E-SKIN\docs\Final\data scalability\data\DELTA\Dynamic_load\N=2\M1_M3\Full_coverage_all_FSR\Repeat_1\experiment_log.md | D:\study\programming\ESKIN\E-SKIN\docs\Final\data scalability\history\pre_variable_spi_20260906\data\DELTA\Dynamic_load\N=2\M1_M3\Full_coverage_all_FSR\Repeat_1\experiment_log.md | 6ecd6b2eff506a834aed9efe595252c64ef7b06828213b6d7495abbc41d46c53
D:\study\programming\ESKIN\E-SKIN\docs\Final\data scalability\data\DELTA\Dynamic_load\N=2\M1_M3\Full_coverage_all_FSR\Repeat_1\mul1_length_over_time.png | D:\study\programming\ESKIN\E-SKIN\docs\Final\data scalability\history\pre_variable_spi_20260906\data\DELTA\Dynamic_load\N=2\M1_M3\Full_coverage_all_FSR\Repeat_1\mul1_length_over_time.png | 3d3784ba0db89ecdd1a7c9f14a0604092150075ba84a2f38745bf1b9743582ce
D:\study\programming\ESKIN\E-SKIN\docs\Final\data scalability\data\DELTA\Dynamic_load\N=2\M1_M3\Full_coverage_all_FSR\Repeat_1\mul1_raw.bin | D:\study\programming\ESKIN\E-SKIN\docs\Final\data scalability\history\pre_variable_spi_20260906\data\DELTA\Dynamic_load\N=2\M1_M3\Full_coverage_all_FSR\Repeat_1\mul1_raw.bin | fb344955c7cbade8eac119cfa81ec97200155b2c3bd6b9c6068bc7aff46be6a3
D:\study\programming\ESKIN\E-SKIN\docs\Final\data scalability\data\DELTA\Dynamic_load\N=2\M1_M3\Full_coverage_all_FSR\Repeat_1\packet_log.csv | D:\study\programming\ESKIN\E-SKIN\docs\Final\data scalability\history\pre_variable_spi_20260906\data\DELTA\Dynamic_load\N=2\M1_M3\Full_coverage_all_FSR\Repeat_1\packet_log.csv | 79db7ae9e1db47fecafec1ff04d74f6c493d673705ed81ca90dc5b33373d92c5
D:\study\programming\ESKIN\E-SKIN\docs\Final\data scalability\data\DELTA\Dynamic_load\N=2\M1_M3\Full_coverage_all_FSR\Repeat_1\plot_generation.log | D:\study\programming\ESKIN\E-SKIN\docs\Final\data scalability\history\pre_variable_spi_20260906\data\DELTA\Dynamic_load\N=2\M1_M3\Full_coverage_all_FSR\Repeat_1\plot_generation.log | 182a1a6ac3daa4ea9db2317a584500149f7cb0a875a82754afba130876d9c2b9
D:\study\programming\ESKIN\E-SKIN\docs\Final\data scalability\data\DELTA\Dynamic_load\N=2\M1_M3\Full_coverage_all_FSR\Repeat_1\summary.json | D:\study\programming\ESKIN\E-SKIN\docs\Final\data scalability\history\pre_variable_spi_20260906\data\DELTA\Dynamic_load\N=2\M1_M3\Full_coverage_all_FSR\Repeat_1\summary.json | 9631eecdef79467c2168d9be0f79d52bda1bb1bea82233f3d6b1d67ee704aa57
D:\study\programming\ESKIN\E-SKIN\docs\Final\data scalability\data\DELTA\Dynamic_load\N=4\M0_M1_M2_M3\Full_coverage_all_FSR\README.md | D:\study\programming\ESKIN\E-SKIN\docs\Final\data scalability\history\pre_variable_spi_20260906\data\DELTA\Dynamic_load\N=4\M0_M1_M2_M3\Full_coverage_all_FSR\README.md | 41e909d2dd8a60e0c52dda53b6ea2f8e2f038470ddb974d7ef795d184e06e9a0
D:\study\programming\ESKIN\E-SKIN\docs\Final\data scalability\data\DELTA\Dynamic_load\N=4\M0_M1_M2_M3\Full_coverage_all_FSR\Repeat_1\experiment_log.md | D:\study\programming\ESKIN\E-SKIN\docs\Final\data scalability\history\pre_variable_spi_20260906\data\DELTA\Dynamic_load\N=4\M0_M1_M2_M3\Full_coverage_all_FSR\Repeat_1\experiment_log.md | 8204217b2b23d4db93146be46a28bc4e400a9a3ab2a5227e4da1f7c61d42bb53
D:\study\programming\ESKIN\E-SKIN\docs\Final\data scalability\data\DELTA\Dynamic_load\N=4\M0_M1_M2_M3\Full_coverage_all_FSR\Repeat_1\mul1_length_over_time.png | D:\study\programming\ESKIN\E-SKIN\docs\Final\data scalability\history\pre_variable_spi_20260906\data\DELTA\Dynamic_load\N=4\M0_M1_M2_M3\Full_coverage_all_FSR\Repeat_1\mul1_length_over_time.png | 9b5b0ab8dc9a785b3da5ee8a60d7f3dc1b15996b57f102930fe177dffd3ad1f2
D:\study\programming\ESKIN\E-SKIN\docs\Final\data scalability\data\DELTA\Dynamic_load\N=4\M0_M1_M2_M3\Full_coverage_all_FSR\Repeat_1\mul1_raw.bin | D:\study\programming\ESKIN\E-SKIN\docs\Final\data scalability\history\pre_variable_spi_20260906\data\DELTA\Dynamic_load\N=4\M0_M1_M2_M3\Full_coverage_all_FSR\Repeat_1\mul1_raw.bin | 7d9ce36c80e8736361e02bc2b594272da904eba7d015effa62d20498c79ef1db
D:\study\programming\ESKIN\E-SKIN\docs\Final\data scalability\data\DELTA\Dynamic_load\N=4\M0_M1_M2_M3\Full_coverage_all_FSR\Repeat_1\packet_log.csv | D:\study\programming\ESKIN\E-SKIN\docs\Final\data scalability\history\pre_variable_spi_20260906\data\DELTA\Dynamic_load\N=4\M0_M1_M2_M3\Full_coverage_all_FSR\Repeat_1\packet_log.csv | 2b2c5326bcccae42a63129b82f92a7bb79ded01a8a837fd41eae86cc2c1173c8
D:\study\programming\ESKIN\E-SKIN\docs\Final\data scalability\data\DELTA\Dynamic_load\N=4\M0_M1_M2_M3\Full_coverage_all_FSR\Repeat_1\plot_generation.log | D:\study\programming\ESKIN\E-SKIN\docs\Final\data scalability\history\pre_variable_spi_20260906\data\DELTA\Dynamic_load\N=4\M0_M1_M2_M3\Full_coverage_all_FSR\Repeat_1\plot_generation.log | 229921c65ac7c3431c4e4a22daf65554afc259ebfca8d1298eaccf84d0e455c4
D:\study\programming\ESKIN\E-SKIN\docs\Final\data scalability\data\DELTA\Dynamic_load\N=4\M0_M1_M2_M3\Full_coverage_all_FSR\Repeat_1\summary.json | D:\study\programming\ESKIN\E-SKIN\docs\Final\data scalability\history\pre_variable_spi_20260906\data\DELTA\Dynamic_load\N=4\M0_M1_M2_M3\Full_coverage_all_FSR\Repeat_1\summary.json | 430794d09f3ad6c0747861e7d9068ac76bbb48cd6a0fd2f28008e8122b7c9b60
D:\study\programming\ESKIN\E-SKIN\docs\Final\data scalability\data\DELTA\Zero_load\N=1\M0\Repeat_1\experiment_log.md | D:\study\programming\ESKIN\E-SKIN\docs\Final\data scalability\history\pre_variable_spi_20260906\data\DELTA\Zero_load\N=1\M0\Repeat_1\experiment_log.md | d649b120f195512a558b4b3fd5c9540e728dd69aa2cad4f150cd95b1a482b024
D:\study\programming\ESKIN\E-SKIN\docs\Final\data scalability\data\DELTA\Zero_load\N=1\M0\Repeat_1\mul1_length_over_time.png | D:\study\programming\ESKIN\E-SKIN\docs\Final\data scalability\history\pre_variable_spi_20260906\data\DELTA\Zero_load\N=1\M0\Repeat_1\mul1_length_over_time.png | 8ee93c10e4ae2845700949f768677b353b5866957016270b5b94dd9ee8c9f09c
D:\study\programming\ESKIN\E-SKIN\docs\Final\data scalability\data\DELTA\Zero_load\N=1\M0\Repeat_1\mul1_raw.bin | D:\study\programming\ESKIN\E-SKIN\docs\Final\data scalability\history\pre_variable_spi_20260906\data\DELTA\Zero_load\N=1\M0\Repeat_1\mul1_raw.bin | dcfbb788325e50024bd14bd7b6ec8323e98d89bd649372595c2b7cc3f9de63c9
D:\study\programming\ESKIN\E-SKIN\docs\Final\data scalability\data\DELTA\Zero_load\N=1\M0\Repeat_1\packet_log.csv | D:\study\programming\ESKIN\E-SKIN\docs\Final\data scalability\history\pre_variable_spi_20260906\data\DELTA\Zero_load\N=1\M0\Repeat_1\packet_log.csv | edeb086c93b83e3c9b55eef67225df7832ca7b59c4d46c9a8b9a4d6d112283df
D:\study\programming\ESKIN\E-SKIN\docs\Final\data scalability\data\DELTA\Zero_load\N=1\M0\Repeat_1\summary.json | D:\study\programming\ESKIN\E-SKIN\docs\Final\data scalability\history\pre_variable_spi_20260906\data\DELTA\Zero_load\N=1\M0\Repeat_1\summary.json | 2af1b99abe060d36bdf4e5a8990644698ac62f9e320084203d59280e0846de00
D:\study\programming\ESKIN\E-SKIN\docs\Final\data scalability\data\DELTA\Zero_load\N=1\M0\Repeat_2\experiment_log.md | D:\study\programming\ESKIN\E-SKIN\docs\Final\data scalability\history\pre_variable_spi_20260906\data\DELTA\Zero_load\N=1\M0\Repeat_2\experiment_log.md | d3670b928256e22de4f5b79b54418ee1602761585b72c4501e8d84b64a5fefd3
D:\study\programming\ESKIN\E-SKIN\docs\Final\data scalability\data\DELTA\Zero_load\N=1\M0\Repeat_2\mul1_length_over_time.png | D:\study\programming\ESKIN\E-SKIN\docs\Final\data scalability\history\pre_variable_spi_20260906\data\DELTA\Zero_load\N=1\M0\Repeat_2\mul1_length_over_time.png | 107f780349f84e0d0f6eab3be26d6ea75719304b749be87a69eaaa5667c4493f
D:\study\programming\ESKIN\E-SKIN\docs\Final\data scalability\data\DELTA\Zero_load\N=1\M0\Repeat_2\mul1_raw.bin | D:\study\programming\ESKIN\E-SKIN\docs\Final\data scalability\history\pre_variable_spi_20260906\data\DELTA\Zero_load\N=1\M0\Repeat_2\mul1_raw.bin | 8a559e9a0e7f558dbb58a751973bd7b86ba63a51cebc03f657749393e6f710e6
D:\study\programming\ESKIN\E-SKIN\docs\Final\data scalability\data\DELTA\Zero_load\N=1\M0\Repeat_2\packet_log.csv | D:\study\programming\ESKIN\E-SKIN\docs\Final\data scalability\history\pre_variable_spi_20260906\data\DELTA\Zero_load\N=1\M0\Repeat_2\packet_log.csv | 2507cab30f5dc4e1c2b4480a40118d57c141b68545cbb6d84debc7c9ac35edf9
D:\study\programming\ESKIN\E-SKIN\docs\Final\data scalability\data\DELTA\Zero_load\N=1\M0\Repeat_2\summary.json | D:\study\programming\ESKIN\E-SKIN\docs\Final\data scalability\history\pre_variable_spi_20260906\data\DELTA\Zero_load\N=1\M0\Repeat_2\summary.json | 32ff7908ade504a9c697530baa79bf874d406f3b5898fc9d5f5c42b6becb9c23
D:\study\programming\ESKIN\E-SKIN\docs\Final\data scalability\data\DELTA\Zero_load\N=1\M0\Repeat_3\experiment_log.md | D:\study\programming\ESKIN\E-SKIN\docs\Final\data scalability\history\pre_variable_spi_20260906\data\DELTA\Zero_load\N=1\M0\Repeat_3\experiment_log.md | 67e8699a809e6015d77d6667d316e2ef72bc07ed92208222b75a6198690a411b
D:\study\programming\ESKIN\E-SKIN\docs\Final\data scalability\data\DELTA\Zero_load\N=1\M0\Repeat_3\mul1_length_over_time.png | D:\study\programming\ESKIN\E-SKIN\docs\Final\data scalability\history\pre_variable_spi_20260906\data\DELTA\Zero_load\N=1\M0\Repeat_3\mul1_length_over_time.png | 698612c800e41358d1c67fd79368f22d93bce291e0737521e9d58df78462cb65
D:\study\programming\ESKIN\E-SKIN\docs\Final\data scalability\data\DELTA\Zero_load\N=1\M0\Repeat_3\mul1_raw.bin | D:\study\programming\ESKIN\E-SKIN\docs\Final\data scalability\history\pre_variable_spi_20260906\data\DELTA\Zero_load\N=1\M0\Repeat_3\mul1_raw.bin | 99e8a9836bf91b463d796e719f3ea454733c9f2e404fa0858894bfa2102e4a04
D:\study\programming\ESKIN\E-SKIN\docs\Final\data scalability\data\DELTA\Zero_load\N=1\M0\Repeat_3\packet_log.csv | D:\study\programming\ESKIN\E-SKIN\docs\Final\data scalability\history\pre_variable_spi_20260906\data\DELTA\Zero_load\N=1\M0\Repeat_3\packet_log.csv | 4505613d7f458e1172aede10c4d83fae3247f802abe4ebf45facaa488fc4eaf6
D:\study\programming\ESKIN\E-SKIN\docs\Final\data scalability\data\DELTA\Zero_load\N=1\M0\Repeat_3\summary.json | D:\study\programming\ESKIN\E-SKIN\docs\Final\data scalability\history\pre_variable_spi_20260906\data\DELTA\Zero_load\N=1\M0\Repeat_3\summary.json | 8d623e648e98fcc13fe9ad385bf6944836aaa858a204d88b0a67ff1c6de5e5fd
D:\study\programming\ESKIN\E-SKIN\docs\Final\data scalability\data\DELTA\Zero_load\N=1\M0\Repeat_4\experiment_log.md | D:\study\programming\ESKIN\E-SKIN\docs\Final\data scalability\history\pre_variable_spi_20260906\data\DELTA\Zero_load\N=1\M0\Repeat_4\experiment_log.md | db9f48f78320134fbd4092fe15da9e8506869aa28642b2cddf2bd2ab2dc2bf8b
D:\study\programming\ESKIN\E-SKIN\docs\Final\data scalability\data\DELTA\Zero_load\N=1\M0\Repeat_4\mul1_length_over_time.png | D:\study\programming\ESKIN\E-SKIN\docs\Final\data scalability\history\pre_variable_spi_20260906\data\DELTA\Zero_load\N=1\M0\Repeat_4\mul1_length_over_time.png | 8419a814aff0c670ab3f542db4142bc5d42762406784a815a446953fc2931c81
D:\study\programming\ESKIN\E-SKIN\docs\Final\data scalability\data\DELTA\Zero_load\N=1\M0\Repeat_4\mul1_raw.bin | D:\study\programming\ESKIN\E-SKIN\docs\Final\data scalability\history\pre_variable_spi_20260906\data\DELTA\Zero_load\N=1\M0\Repeat_4\mul1_raw.bin | 526cc6e60b39c086aabfcf835efd2af8e887ece6e91e4ca7564347f391b9fb83
D:\study\programming\ESKIN\E-SKIN\docs\Final\data scalability\data\DELTA\Zero_load\N=1\M0\Repeat_4\packet_log.csv | D:\study\programming\ESKIN\E-SKIN\docs\Final\data scalability\history\pre_variable_spi_20260906\data\DELTA\Zero_load\N=1\M0\Repeat_4\packet_log.csv | 192283630a21fd572d63d0424ea153824ed14cbecc9bd927da2b5efe9e5dd693
D:\study\programming\ESKIN\E-SKIN\docs\Final\data scalability\data\DELTA\Zero_load\N=1\M0\Repeat_4\plot_generation.log | D:\study\programming\ESKIN\E-SKIN\docs\Final\data scalability\history\pre_variable_spi_20260906\data\DELTA\Zero_load\N=1\M0\Repeat_4\plot_generation.log | 35e908e7f31a8c9dce9fa8e046f758f01ca277c634a16e8609230ab475196e1f
D:\study\programming\ESKIN\E-SKIN\docs\Final\data scalability\data\DELTA\Zero_load\N=1\M0\Repeat_4\summary.json | D:\study\programming\ESKIN\E-SKIN\docs\Final\data scalability\history\pre_variable_spi_20260906\data\DELTA\Zero_load\N=1\M0\Repeat_4\summary.json | 5bfbf0a67f916891fde0179b97fb53d363d856cd0837b4d692905975bc5bad60
D:\study\programming\ESKIN\E-SKIN\docs\Final\data scalability\data\DELTA\Zero_load\N=1\M0\Repeat_5\experiment_log.md | D:\study\programming\ESKIN\E-SKIN\docs\Final\data scalability\history\pre_variable_spi_20260906\data\DELTA\Zero_load\N=1\M0\Repeat_5\experiment_log.md | 3a85d89ed303f11f5736357a31e286c1815bd8f324e6dca52aae2006cd59ab06
D:\study\programming\ESKIN\E-SKIN\docs\Final\data scalability\data\DELTA\Zero_load\N=1\M0\Repeat_5\mul1_length_over_time.png | D:\study\programming\ESKIN\E-SKIN\docs\Final\data scalability\history\pre_variable_spi_20260906\data\DELTA\Zero_load\N=1\M0\Repeat_5\mul1_length_over_time.png | 09590c2b19671803d4108d4ef349f86a6e1313989a577e9a9054fe115b1b4eee
D:\study\programming\ESKIN\E-SKIN\docs\Final\data scalability\data\DELTA\Zero_load\N=1\M0\Repeat_5\mul1_raw.bin | D:\study\programming\ESKIN\E-SKIN\docs\Final\data scalability\history\pre_variable_spi_20260906\data\DELTA\Zero_load\N=1\M0\Repeat_5\mul1_raw.bin | 0a8bd1fe64d8f23c61331d3ba4c3683a702a3d484f543201dc2790ee0f1d4b49
D:\study\programming\ESKIN\E-SKIN\docs\Final\data scalability\data\DELTA\Zero_load\N=1\M0\Repeat_5\packet_log.csv | D:\study\programming\ESKIN\E-SKIN\docs\Final\data scalability\history\pre_variable_spi_20260906\data\DELTA\Zero_load\N=1\M0\Repeat_5\packet_log.csv | 6c9c6bc4c23ee138a10ea84e93d74573aa9dcd975e75046439e04e97b80908d9
D:\study\programming\ESKIN\E-SKIN\docs\Final\data scalability\data\DELTA\Zero_load\N=1\M0\Repeat_5\plot_generation.log | D:\study\programming\ESKIN\E-SKIN\docs\Final\data scalability\history\pre_variable_spi_20260906\data\DELTA\Zero_load\N=1\M0\Repeat_5\plot_generation.log | b74bcc27c22ca19ec595af6805b2141c88f86bffc1bf0b525390f709910b5d1c
D:\study\programming\ESKIN\E-SKIN\docs\Final\data scalability\data\DELTA\Zero_load\N=1\M0\Repeat_5\summary.json | D:\study\programming\ESKIN\E-SKIN\docs\Final\data scalability\history\pre_variable_spi_20260906\data\DELTA\Zero_load\N=1\M0\Repeat_5\summary.json | beadae9aa377eff3538acef6b2ed3c764ad7c50895f2a17745b00bb9306f750a
D:\study\programming\ESKIN\E-SKIN\docs\Final\data scalability\data\DELTA\Zero_load\N=1\M0\Repeat_6\experiment_log.md | D:\study\programming\ESKIN\E-SKIN\docs\Final\data scalability\history\pre_variable_spi_20260906\data\DELTA\Zero_load\N=1\M0\Repeat_6\experiment_log.md | 411c30d8ecf53fb887add7c049e6d02850c0c464ff0945c65735ca336cc7162d
D:\study\programming\ESKIN\E-SKIN\docs\Final\data scalability\data\DELTA\Zero_load\N=1\M0\Repeat_6\mul1_length_over_time.png | D:\study\programming\ESKIN\E-SKIN\docs\Final\data scalability\history\pre_variable_spi_20260906\data\DELTA\Zero_load\N=1\M0\Repeat_6\mul1_length_over_time.png | ebaa14a63e6cfc2f05ed9d9d241b79f83d0861085bef95a8c17705bf4136b862
D:\study\programming\ESKIN\E-SKIN\docs\Final\data scalability\data\DELTA\Zero_load\N=1\M0\Repeat_6\mul1_raw.bin | D:\study\programming\ESKIN\E-SKIN\docs\Final\data scalability\history\pre_variable_spi_20260906\data\DELTA\Zero_load\N=1\M0\Repeat_6\mul1_raw.bin | b13217e57af69c6d7537861a23a0635572939251620771cabd0d9e3fd9319e04
D:\study\programming\ESKIN\E-SKIN\docs\Final\data scalability\data\DELTA\Zero_load\N=1\M0\Repeat_6\packet_log.csv | D:\study\programming\ESKIN\E-SKIN\docs\Final\data scalability\history\pre_variable_spi_20260906\data\DELTA\Zero_load\N=1\M0\Repeat_6\packet_log.csv | b940076f8cadf385d7703a570501a3f86272a39e318fc8eb5e6cb5cb9c3ed1e3
D:\study\programming\ESKIN\E-SKIN\docs\Final\data scalability\data\DELTA\Zero_load\N=1\M0\Repeat_6\plot_generation.log | D:\study\programming\ESKIN\E-SKIN\docs\Final\data scalability\history\pre_variable_spi_20260906\data\DELTA\Zero_load\N=1\M0\Repeat_6\plot_generation.log | eac1f18cf819093c0aefd60cf28511908b94d46ee1be52448526be68683de2bc
D:\study\programming\ESKIN\E-SKIN\docs\Final\data scalability\data\DELTA\Zero_load\N=1\M0\Repeat_6\summary.json | D:\study\programming\ESKIN\E-SKIN\docs\Final\data scalability\history\pre_variable_spi_20260906\data\DELTA\Zero_load\N=1\M0\Repeat_6\summary.json | 60910cac0f4ca0422742dd24e86170987f3a0ea61dd7f351cfe198eb0fa4d35e
D:\study\programming\ESKIN\E-SKIN\docs\Final\data scalability\data\DELTA\Zero_load\N=1\M1\Repeat_1\experiment_log.md | D:\study\programming\ESKIN\E-SKIN\docs\Final\data scalability\history\pre_variable_spi_20260906\data\DELTA\Zero_load\N=1\M1\Repeat_1\experiment_log.md | e39528cc8cc9264dded12d2d5dd225ad7eceab031e56e68a33a9b005444777c1
D:\study\programming\ESKIN\E-SKIN\docs\Final\data scalability\data\DELTA\Zero_load\N=1\M1\Repeat_1\mul1_length_over_time.png | D:\study\programming\ESKIN\E-SKIN\docs\Final\data scalability\history\pre_variable_spi_20260906\data\DELTA\Zero_load\N=1\M1\Repeat_1\mul1_length_over_time.png | 36930d7e2500d7325377f0248c27993b09a3879d3124bf5b598bc5925ae1385b
D:\study\programming\ESKIN\E-SKIN\docs\Final\data scalability\data\DELTA\Zero_load\N=1\M1\Repeat_1\mul1_raw.bin | D:\study\programming\ESKIN\E-SKIN\docs\Final\data scalability\history\pre_variable_spi_20260906\data\DELTA\Zero_load\N=1\M1\Repeat_1\mul1_raw.bin | b1578a3c58b38230a5b4c148a394e0a3feced04aa5b0298e3e64189955fef007
D:\study\programming\ESKIN\E-SKIN\docs\Final\data scalability\data\DELTA\Zero_load\N=1\M1\Repeat_1\packet_log.csv | D:\study\programming\ESKIN\E-SKIN\docs\Final\data scalability\history\pre_variable_spi_20260906\data\DELTA\Zero_load\N=1\M1\Repeat_1\packet_log.csv | 87cc66cf2901fbaee42f752ee6b5ed916d4a1cb262fa7a65cb2dd282ed686a28
D:\study\programming\ESKIN\E-SKIN\docs\Final\data scalability\data\DELTA\Zero_load\N=1\M1\Repeat_1\summary.json | D:\study\programming\ESKIN\E-SKIN\docs\Final\data scalability\history\pre_variable_spi_20260906\data\DELTA\Zero_load\N=1\M1\Repeat_1\summary.json | 9287ba3ef76621183f2d36d65bf1a31f7f7d1195b052864143cca1dd345dd10b
D:\study\programming\ESKIN\E-SKIN\docs\Final\data scalability\data\DELTA\Zero_load\N=1\M1\Repeat_2\experiment_log.md | D:\study\programming\ESKIN\E-SKIN\docs\Final\data scalability\history\pre_variable_spi_20260906\data\DELTA\Zero_load\N=1\M1\Repeat_2\experiment_log.md | df4b4ae3ae815a8893bf8ac984415a76f5e72303b083b24b6b4cf0e7e595a8e1
D:\study\programming\ESKIN\E-SKIN\docs\Final\data scalability\data\DELTA\Zero_load\N=1\M1\Repeat_2\mul1_length_over_time.png | D:\study\programming\ESKIN\E-SKIN\docs\Final\data scalability\history\pre_variable_spi_20260906\data\DELTA\Zero_load\N=1\M1\Repeat_2\mul1_length_over_time.png | b963338dabb1e020d1a4f10f46de250ccc36fd9791d4e8b344651ade307d20c8
D:\study\programming\ESKIN\E-SKIN\docs\Final\data scalability\data\DELTA\Zero_load\N=1\M1\Repeat_2\mul1_raw.bin | D:\study\programming\ESKIN\E-SKIN\docs\Final\data scalability\history\pre_variable_spi_20260906\data\DELTA\Zero_load\N=1\M1\Repeat_2\mul1_raw.bin | 0411e70e74520a1a99994cf9b578b9473f0ff92bbb6b57983627737a0afa305a
D:\study\programming\ESKIN\E-SKIN\docs\Final\data scalability\data\DELTA\Zero_load\N=1\M1\Repeat_2\packet_log.csv | D:\study\programming\ESKIN\E-SKIN\docs\Final\data scalability\history\pre_variable_spi_20260906\data\DELTA\Zero_load\N=1\M1\Repeat_2\packet_log.csv | 3e21052eb682f0e30876e25202c327b521a922e68caa2874ce3891d1a61aace5
D:\study\programming\ESKIN\E-SKIN\docs\Final\data scalability\data\DELTA\Zero_load\N=1\M1\Repeat_2\summary.json | D:\study\programming\ESKIN\E-SKIN\docs\Final\data scalability\history\pre_variable_spi_20260906\data\DELTA\Zero_load\N=1\M1\Repeat_2\summary.json | 0b02cfbcbb103ef2180fcce4bdb3c2e1dfcfcfbd20740c046f5cd4cf610005e5
D:\study\programming\ESKIN\E-SKIN\docs\Final\data scalability\data\DELTA\Zero_load\N=1\M1\Repeat_3\experiment_log.md | D:\study\programming\ESKIN\E-SKIN\docs\Final\data scalability\history\pre_variable_spi_20260906\data\DELTA\Zero_load\N=1\M1\Repeat_3\experiment_log.md | 43bdb73459288abc6cde2d66acd40a8b0aee6496af7b23224420254b6dea6b0b
D:\study\programming\ESKIN\E-SKIN\docs\Final\data scalability\data\DELTA\Zero_load\N=1\M1\Repeat_3\mul1_length_over_time.png | D:\study\programming\ESKIN\E-SKIN\docs\Final\data scalability\history\pre_variable_spi_20260906\data\DELTA\Zero_load\N=1\M1\Repeat_3\mul1_length_over_time.png | 1e92b9d19b9bd2d773361b938e64958107966d5745643c5ef2f62c361d86d8ab
D:\study\programming\ESKIN\E-SKIN\docs\Final\data scalability\data\DELTA\Zero_load\N=1\M1\Repeat_3\mul1_raw.bin | D:\study\programming\ESKIN\E-SKIN\docs\Final\data scalability\history\pre_variable_spi_20260906\data\DELTA\Zero_load\N=1\M1\Repeat_3\mul1_raw.bin | dd6c87b15ee5e2b428a05864935e64491bc1be2d21fc53554b2da3394f152f25
D:\study\programming\ESKIN\E-SKIN\docs\Final\data scalability\data\DELTA\Zero_load\N=1\M1\Repeat_3\packet_log.csv | D:\study\programming\ESKIN\E-SKIN\docs\Final\data scalability\history\pre_variable_spi_20260906\data\DELTA\Zero_load\N=1\M1\Repeat_3\packet_log.csv | c31767844a23fd8fcdff1bdf91e5c6181c936e915d053a10ebeac73abb577479
D:\study\programming\ESKIN\E-SKIN\docs\Final\data scalability\data\DELTA\Zero_load\N=1\M1\Repeat_3\summary.json | D:\study\programming\ESKIN\E-SKIN\docs\Final\data scalability\history\pre_variable_spi_20260906\data\DELTA\Zero_load\N=1\M1\Repeat_3\summary.json | 1283317e45dd52143c025aa6771f7d574046034ef2b35b380f433d45fb025a62
D:\study\programming\ESKIN\E-SKIN\docs\Final\data scalability\data\DELTA\Zero_load\N=1\M1\Repeat_4\experiment_log.md | D:\study\programming\ESKIN\E-SKIN\docs\Final\data scalability\history\pre_variable_spi_20260906\data\DELTA\Zero_load\N=1\M1\Repeat_4\experiment_log.md | 696bb4fba2ef703c658f3659691528a52dca8f63fb73e0ba1ee69e5b972bb0cd
D:\study\programming\ESKIN\E-SKIN\docs\Final\data scalability\data\DELTA\Zero_load\N=1\M1\Repeat_4\mul1_length_over_time.png | D:\study\programming\ESKIN\E-SKIN\docs\Final\data scalability\history\pre_variable_spi_20260906\data\DELTA\Zero_load\N=1\M1\Repeat_4\mul1_length_over_time.png | 86ef517a980095e2b2396c279e3b63a57e8de48faaa56b7d15b632b25802081a
D:\study\programming\ESKIN\E-SKIN\docs\Final\data scalability\data\DELTA\Zero_load\N=1\M1\Repeat_4\mul1_raw.bin | D:\study\programming\ESKIN\E-SKIN\docs\Final\data scalability\history\pre_variable_spi_20260906\data\DELTA\Zero_load\N=1\M1\Repeat_4\mul1_raw.bin | 0a714f96447d8a21c56a41e09d9f5b2c8b3eee0a6f04cfb6f5025249ad0dd7c3
D:\study\programming\ESKIN\E-SKIN\docs\Final\data scalability\data\DELTA\Zero_load\N=1\M1\Repeat_4\packet_log.csv | D:\study\programming\ESKIN\E-SKIN\docs\Final\data scalability\history\pre_variable_spi_20260906\data\DELTA\Zero_load\N=1\M1\Repeat_4\packet_log.csv | 5715dfce7ff9ac6880f3c9b32c3967009f0f876e832f354cbe006ce214a5e74e
D:\study\programming\ESKIN\E-SKIN\docs\Final\data scalability\data\DELTA\Zero_load\N=1\M1\Repeat_4\plot_generation.log | D:\study\programming\ESKIN\E-SKIN\docs\Final\data scalability\history\pre_variable_spi_20260906\data\DELTA\Zero_load\N=1\M1\Repeat_4\plot_generation.log | 1aa7a51e8f00107f14723ea55562f508bd237f09bc5a90baef01dafe5f339d4f
D:\study\programming\ESKIN\E-SKIN\docs\Final\data scalability\data\DELTA\Zero_load\N=1\M1\Repeat_4\summary.json | D:\study\programming\ESKIN\E-SKIN\docs\Final\data scalability\history\pre_variable_spi_20260906\data\DELTA\Zero_load\N=1\M1\Repeat_4\summary.json | 7ef59dacf12073d76ae6f965ed586b8d106f1bd7ed30355e6437ba3fe1cb4707
D:\study\programming\ESKIN\E-SKIN\docs\Final\data scalability\data\DELTA\Zero_load\N=1\M1\Repeat_5\experiment_log.md | D:\study\programming\ESKIN\E-SKIN\docs\Final\data scalability\history\pre_variable_spi_20260906\data\DELTA\Zero_load\N=1\M1\Repeat_5\experiment_log.md | f4448ec495fdca5bf170f2dc503a999c7d1212fe54eb70219560e0d5f7d46ecd
D:\study\programming\ESKIN\E-SKIN\docs\Final\data scalability\data\DELTA\Zero_load\N=1\M1\Repeat_5\mul1_length_over_time.png | D:\study\programming\ESKIN\E-SKIN\docs\Final\data scalability\history\pre_variable_spi_20260906\data\DELTA\Zero_load\N=1\M1\Repeat_5\mul1_length_over_time.png | 2ba61ee3c0f5f045037227e815c7da2b9c6d3173dd69821780e390c5d430c2ec
D:\study\programming\ESKIN\E-SKIN\docs\Final\data scalability\data\DELTA\Zero_load\N=1\M1\Repeat_5\mul1_raw.bin | D:\study\programming\ESKIN\E-SKIN\docs\Final\data scalability\history\pre_variable_spi_20260906\data\DELTA\Zero_load\N=1\M1\Repeat_5\mul1_raw.bin | 450509e371ba22324d4a8eb4d85c54ffdf78235aa2a4fcb6f7521ac471169dee
D:\study\programming\ESKIN\E-SKIN\docs\Final\data scalability\data\DELTA\Zero_load\N=1\M1\Repeat_5\packet_log.csv | D:\study\programming\ESKIN\E-SKIN\docs\Final\data scalability\history\pre_variable_spi_20260906\data\DELTA\Zero_load\N=1\M1\Repeat_5\packet_log.csv | e7f17f52d15dc47a0d4a6ccfdd55237639ef1dbc410be028bfebf019b0e047a0
D:\study\programming\ESKIN\E-SKIN\docs\Final\data scalability\data\DELTA\Zero_load\N=1\M1\Repeat_5\plot_generation.log | D:\study\programming\ESKIN\E-SKIN\docs\Final\data scalability\history\pre_variable_spi_20260906\data\DELTA\Zero_load\N=1\M1\Repeat_5\plot_generation.log | 0c9c18dd43c5485460f77b2d07146229107a4d0b80ec01f89012cc60c589298b
D:\study\programming\ESKIN\E-SKIN\docs\Final\data scalability\data\DELTA\Zero_load\N=1\M1\Repeat_5\summary.json | D:\study\programming\ESKIN\E-SKIN\docs\Final\data scalability\history\pre_variable_spi_20260906\data\DELTA\Zero_load\N=1\M1\Repeat_5\summary.json | bd64c010159d15b24bf385d60450967d5cdafe9a0b68c7b5333f43af046802db
D:\study\programming\ESKIN\E-SKIN\docs\Final\data scalability\data\DELTA\Zero_load\N=1\M2\Repeat_1\experiment_log.md | D:\study\programming\ESKIN\E-SKIN\docs\Final\data scalability\history\pre_variable_spi_20260906\data\DELTA\Zero_load\N=1\M2\Repeat_1\experiment_log.md | 40e01ed32f280124187285f1cbbd1d17ea3328b5fd5a721186ccbefa0c004fb3
D:\study\programming\ESKIN\E-SKIN\docs\Final\data scalability\data\DELTA\Zero_load\N=1\M2\Repeat_1\mul1_length_over_time.png | D:\study\programming\ESKIN\E-SKIN\docs\Final\data scalability\history\pre_variable_spi_20260906\data\DELTA\Zero_load\N=1\M2\Repeat_1\mul1_length_over_time.png | 03d32f1e6b0a5ed809ce753f67ada653ae0b3a430fc8b0094fe7e0f5eb054fcb
D:\study\programming\ESKIN\E-SKIN\docs\Final\data scalability\data\DELTA\Zero_load\N=1\M2\Repeat_1\mul1_raw.bin | D:\study\programming\ESKIN\E-SKIN\docs\Final\data scalability\history\pre_variable_spi_20260906\data\DELTA\Zero_load\N=1\M2\Repeat_1\mul1_raw.bin | 7e38a07e50d2227b9c328cd54433a99949e5440b4a4aeb803b9c123a243c0406
D:\study\programming\ESKIN\E-SKIN\docs\Final\data scalability\data\DELTA\Zero_load\N=1\M2\Repeat_1\packet_log.csv | D:\study\programming\ESKIN\E-SKIN\docs\Final\data scalability\history\pre_variable_spi_20260906\data\DELTA\Zero_load\N=1\M2\Repeat_1\packet_log.csv | 8ff0bd51994b62b7a8339ff7119f937f5c60e0f57765b44404794a74dbc4859a
D:\study\programming\ESKIN\E-SKIN\docs\Final\data scalability\data\DELTA\Zero_load\N=1\M2\Repeat_1\summary.json | D:\study\programming\ESKIN\E-SKIN\docs\Final\data scalability\history\pre_variable_spi_20260906\data\DELTA\Zero_load\N=1\M2\Repeat_1\summary.json | f2af4407c8b7ad77dfd3460ea3532bad186fed1befa804ca2307d4c6ffb4cd49
D:\study\programming\ESKIN\E-SKIN\docs\Final\data scalability\data\DELTA\Zero_load\N=1\M2\Repeat_2\experiment_log.md | D:\study\programming\ESKIN\E-SKIN\docs\Final\data scalability\history\pre_variable_spi_20260906\data\DELTA\Zero_load\N=1\M2\Repeat_2\experiment_log.md | 595ad7cc99bc4cd4930e467564e220b2cea49439fbb17c18f0785475cfdb7026
D:\study\programming\ESKIN\E-SKIN\docs\Final\data scalability\data\DELTA\Zero_load\N=1\M2\Repeat_2\mul1_length_over_time.png | D:\study\programming\ESKIN\E-SKIN\docs\Final\data scalability\history\pre_variable_spi_20260906\data\DELTA\Zero_load\N=1\M2\Repeat_2\mul1_length_over_time.png | ee3abc469b079595dbf741562dbe8b95a30e66afe171009304a9b297872449c8
D:\study\programming\ESKIN\E-SKIN\docs\Final\data scalability\data\DELTA\Zero_load\N=1\M2\Repeat_2\mul1_raw.bin | D:\study\programming\ESKIN\E-SKIN\docs\Final\data scalability\history\pre_variable_spi_20260906\data\DELTA\Zero_load\N=1\M2\Repeat_2\mul1_raw.bin | d7a70cd3bbde7be036e427c3057278baa4ee01dcabed34e2405a28cbd694a5f0
D:\study\programming\ESKIN\E-SKIN\docs\Final\data scalability\data\DELTA\Zero_load\N=1\M2\Repeat_2\packet_log.csv | D:\study\programming\ESKIN\E-SKIN\docs\Final\data scalability\history\pre_variable_spi_20260906\data\DELTA\Zero_load\N=1\M2\Repeat_2\packet_log.csv | 481d6eb106d9d0f3ee9f918ff3de052005ed258641f96129d9673d2b448c5ebf
D:\study\programming\ESKIN\E-SKIN\docs\Final\data scalability\data\DELTA\Zero_load\N=1\M2\Repeat_2\summary.json | D:\study\programming\ESKIN\E-SKIN\docs\Final\data scalability\history\pre_variable_spi_20260906\data\DELTA\Zero_load\N=1\M2\Repeat_2\summary.json | b1342e6cbf6af256617eb147e6aa4608396032feb35cb16320b833396e8062f5
D:\study\programming\ESKIN\E-SKIN\docs\Final\data scalability\data\DELTA\Zero_load\N=1\M2\Repeat_3\experiment_log.md | D:\study\programming\ESKIN\E-SKIN\docs\Final\data scalability\history\pre_variable_spi_20260906\data\DELTA\Zero_load\N=1\M2\Repeat_3\experiment_log.md | 3e5739b69e97b09160cc7e1e7035429f5878813a0f355da1eec3d5ddf61a9604
D:\study\programming\ESKIN\E-SKIN\docs\Final\data scalability\data\DELTA\Zero_load\N=1\M2\Repeat_3\mul1_length_over_time.png | D:\study\programming\ESKIN\E-SKIN\docs\Final\data scalability\history\pre_variable_spi_20260906\data\DELTA\Zero_load\N=1\M2\Repeat_3\mul1_length_over_time.png | 7bb502e3b3320317f624718f67f6859dedaacb68cedb314ff1cf527a6d2e1003
D:\study\programming\ESKIN\E-SKIN\docs\Final\data scalability\data\DELTA\Zero_load\N=1\M2\Repeat_3\mul1_raw.bin | D:\study\programming\ESKIN\E-SKIN\docs\Final\data scalability\history\pre_variable_spi_20260906\data\DELTA\Zero_load\N=1\M2\Repeat_3\mul1_raw.bin | c3f4c7f354bb7018b07716918d2e9cbcdc91a63eb157d6cba7b417e4db87c468
D:\study\programming\ESKIN\E-SKIN\docs\Final\data scalability\data\DELTA\Zero_load\N=1\M2\Repeat_3\packet_log.csv | D:\study\programming\ESKIN\E-SKIN\docs\Final\data scalability\history\pre_variable_spi_20260906\data\DELTA\Zero_load\N=1\M2\Repeat_3\packet_log.csv | fbfa71474650a0669295027ade4b5ad19730b575ff8889ff438ef1e3b374dff1
D:\study\programming\ESKIN\E-SKIN\docs\Final\data scalability\data\DELTA\Zero_load\N=1\M2\Repeat_3\summary.json | D:\study\programming\ESKIN\E-SKIN\docs\Final\data scalability\history\pre_variable_spi_20260906\data\DELTA\Zero_load\N=1\M2\Repeat_3\summary.json | 31be547513a6e22a1eae8794d58084af2975f227efc9d32d787e6ca712d7ffbb
D:\study\programming\ESKIN\E-SKIN\docs\Final\data scalability\data\DELTA\Zero_load\N=1\M2\Repeat_4\experiment_log.md | D:\study\programming\ESKIN\E-SKIN\docs\Final\data scalability\history\pre_variable_spi_20260906\data\DELTA\Zero_load\N=1\M2\Repeat_4\experiment_log.md | d0213e3ed4af95057a821d63d0f455608446761e92395d6f2e85669771fc9806
D:\study\programming\ESKIN\E-SKIN\docs\Final\data scalability\data\DELTA\Zero_load\N=1\M2\Repeat_4\mul1_length_over_time.png | D:\study\programming\ESKIN\E-SKIN\docs\Final\data scalability\history\pre_variable_spi_20260906\data\DELTA\Zero_load\N=1\M2\Repeat_4\mul1_length_over_time.png | 781c784682ff016a66cb264bf62471b522812235e9b178f63181ea02906ea384
D:\study\programming\ESKIN\E-SKIN\docs\Final\data scalability\data\DELTA\Zero_load\N=1\M2\Repeat_4\mul1_raw.bin | D:\study\programming\ESKIN\E-SKIN\docs\Final\data scalability\history\pre_variable_spi_20260906\data\DELTA\Zero_load\N=1\M2\Repeat_4\mul1_raw.bin | cfbf31709c600053874f213b440a1071705dfb06d3f66611d69c4e08708a5f5c
D:\study\programming\ESKIN\E-SKIN\docs\Final\data scalability\data\DELTA\Zero_load\N=1\M2\Repeat_4\packet_log.csv | D:\study\programming\ESKIN\E-SKIN\docs\Final\data scalability\history\pre_variable_spi_20260906\data\DELTA\Zero_load\N=1\M2\Repeat_4\packet_log.csv | aa6633c90cdd3786bf84c1412b10f21921465da51385a3ccc2fc671e17b42109
D:\study\programming\ESKIN\E-SKIN\docs\Final\data scalability\data\DELTA\Zero_load\N=1\M2\Repeat_4\plot_generation.log | D:\study\programming\ESKIN\E-SKIN\docs\Final\data scalability\history\pre_variable_spi_20260906\data\DELTA\Zero_load\N=1\M2\Repeat_4\plot_generation.log | 95f0dfbe8f10befbfefbef00d83048bcc213dbff06bb7dfab9e20a66f9ef428c
D:\study\programming\ESKIN\E-SKIN\docs\Final\data scalability\data\DELTA\Zero_load\N=1\M2\Repeat_4\summary.json | D:\study\programming\ESKIN\E-SKIN\docs\Final\data scalability\history\pre_variable_spi_20260906\data\DELTA\Zero_load\N=1\M2\Repeat_4\summary.json | d62d973f3ea8f98cce1a39d03f5624616df364eb0c19432587637b9bd7d14728
D:\study\programming\ESKIN\E-SKIN\docs\Final\data scalability\data\DELTA\Zero_load\N=1\M2\Repeat_5\experiment_log.md | D:\study\programming\ESKIN\E-SKIN\docs\Final\data scalability\history\pre_variable_spi_20260906\data\DELTA\Zero_load\N=1\M2\Repeat_5\experiment_log.md | 31796a1a5564cba63e76869372d4fb4d6f34aa4e1878269cf11d5bf0497e7c5d
D:\study\programming\ESKIN\E-SKIN\docs\Final\data scalability\data\DELTA\Zero_load\N=1\M2\Repeat_5\mul1_length_over_time.png | D:\study\programming\ESKIN\E-SKIN\docs\Final\data scalability\history\pre_variable_spi_20260906\data\DELTA\Zero_load\N=1\M2\Repeat_5\mul1_length_over_time.png | 77376053aa698d6d6ca945e985f25d93e5a8b89bc1e704d3793b36f577e09ece
D:\study\programming\ESKIN\E-SKIN\docs\Final\data scalability\data\DELTA\Zero_load\N=1\M2\Repeat_5\mul1_raw.bin | D:\study\programming\ESKIN\E-SKIN\docs\Final\data scalability\history\pre_variable_spi_20260906\data\DELTA\Zero_load\N=1\M2\Repeat_5\mul1_raw.bin | 6f7f7c79b4b9c13ef289d45afce714484962f8a54abd330e9f9bbf9cfa66b5f7
D:\study\programming\ESKIN\E-SKIN\docs\Final\data scalability\data\DELTA\Zero_load\N=1\M2\Repeat_5\packet_log.csv | D:\study\programming\ESKIN\E-SKIN\docs\Final\data scalability\history\pre_variable_spi_20260906\data\DELTA\Zero_load\N=1\M2\Repeat_5\packet_log.csv | 63b44d967a8c0cee085425c640bc925256c93cb4fac27fce3520809f11e78db5
D:\study\programming\ESKIN\E-SKIN\docs\Final\data scalability\data\DELTA\Zero_load\N=1\M2\Repeat_5\plot_generation.log | D:\study\programming\ESKIN\E-SKIN\docs\Final\data scalability\history\pre_variable_spi_20260906\data\DELTA\Zero_load\N=1\M2\Repeat_5\plot_generation.log | 1f346cdd2527ddcb155e11dacd8d3bb4336f19d9439c1a288581893617910142
D:\study\programming\ESKIN\E-SKIN\docs\Final\data scalability\data\DELTA\Zero_load\N=1\M2\Repeat_5\summary.json | D:\study\programming\ESKIN\E-SKIN\docs\Final\data scalability\history\pre_variable_spi_20260906\data\DELTA\Zero_load\N=1\M2\Repeat_5\summary.json | ca7f00a6520af62ec4a6bdccc1aeeee361e97969d879e0e00e6c911b439fbb38
D:\study\programming\ESKIN\E-SKIN\docs\Final\data scalability\data\DELTA\Zero_load\N=1\M2\Repeat_6\experiment_log.md | D:\study\programming\ESKIN\E-SKIN\docs\Final\data scalability\history\pre_variable_spi_20260906\data\DELTA\Zero_load\N=1\M2\Repeat_6\experiment_log.md | a98943b161423e3d8ca020ad58b0b86215f5a65773a240ea10305aadfd0fd1d8
D:\study\programming\ESKIN\E-SKIN\docs\Final\data scalability\data\DELTA\Zero_load\N=1\M2\Repeat_6\mul1_length_over_time.png | D:\study\programming\ESKIN\E-SKIN\docs\Final\data scalability\history\pre_variable_spi_20260906\data\DELTA\Zero_load\N=1\M2\Repeat_6\mul1_length_over_time.png | 2c41deb111ed57a743a049960ca96d0dfdff4b819efab3070f716f3782d9b176
D:\study\programming\ESKIN\E-SKIN\docs\Final\data scalability\data\DELTA\Zero_load\N=1\M2\Repeat_6\mul1_raw.bin | D:\study\programming\ESKIN\E-SKIN\docs\Final\data scalability\history\pre_variable_spi_20260906\data\DELTA\Zero_load\N=1\M2\Repeat_6\mul1_raw.bin | 4368e433982e7d6b11147b31c02543686510b47fc3930132b16bd12cbcd72add
D:\study\programming\ESKIN\E-SKIN\docs\Final\data scalability\data\DELTA\Zero_load\N=1\M2\Repeat_6\packet_log.csv | D:\study\programming\ESKIN\E-SKIN\docs\Final\data scalability\history\pre_variable_spi_20260906\data\DELTA\Zero_load\N=1\M2\Repeat_6\packet_log.csv | 3da6974a6d9f07399873ea759e6abcdf74e1ef4a25d234f797131324a8dc3f33
D:\study\programming\ESKIN\E-SKIN\docs\Final\data scalability\data\DELTA\Zero_load\N=1\M2\Repeat_6\plot_generation.log | D:\study\programming\ESKIN\E-SKIN\docs\Final\data scalability\history\pre_variable_spi_20260906\data\DELTA\Zero_load\N=1\M2\Repeat_6\plot_generation.log | e257b924c028997cbc7eb24df816d0b21c0787f75deaf43d363333c81570193e
D:\study\programming\ESKIN\E-SKIN\docs\Final\data scalability\data\DELTA\Zero_load\N=1\M2\Repeat_6\summary.json | D:\study\programming\ESKIN\E-SKIN\docs\Final\data scalability\history\pre_variable_spi_20260906\data\DELTA\Zero_load\N=1\M2\Repeat_6\summary.json | 15a8345c98997a9431cf7a59ff6d7f6cedd19e7978f8cfafc8c1464a40566c3d
D:\study\programming\ESKIN\E-SKIN\docs\Final\data scalability\data\DELTA\Zero_load\N=1\M2\Repeat_7\experiment_log.md | D:\study\programming\ESKIN\E-SKIN\docs\Final\data scalability\history\pre_variable_spi_20260906\data\DELTA\Zero_load\N=1\M2\Repeat_7\experiment_log.md | d41d6c9d758b0cf142a7bf44ff834d5602655977b961482637a37a9d0c3608b4
D:\study\programming\ESKIN\E-SKIN\docs\Final\data scalability\data\DELTA\Zero_load\N=1\M2\Repeat_7\mul1_length_over_time.png | D:\study\programming\ESKIN\E-SKIN\docs\Final\data scalability\history\pre_variable_spi_20260906\data\DELTA\Zero_load\N=1\M2\Repeat_7\mul1_length_over_time.png | 2b02c975ac090bb58fda9b1a3751fa9c44ff3f7a6ec4e16fa3e42830e914465e
D:\study\programming\ESKIN\E-SKIN\docs\Final\data scalability\data\DELTA\Zero_load\N=1\M2\Repeat_7\mul1_raw.bin | D:\study\programming\ESKIN\E-SKIN\docs\Final\data scalability\history\pre_variable_spi_20260906\data\DELTA\Zero_load\N=1\M2\Repeat_7\mul1_raw.bin | 95834b403296498b147c14b701aba9cd1002ed6c00d895db5eeaf350035ad8fb
D:\study\programming\ESKIN\E-SKIN\docs\Final\data scalability\data\DELTA\Zero_load\N=1\M2\Repeat_7\packet_log.csv | D:\study\programming\ESKIN\E-SKIN\docs\Final\data scalability\history\pre_variable_spi_20260906\data\DELTA\Zero_load\N=1\M2\Repeat_7\packet_log.csv | 308dab0293b8e754a013b3b44eac35ff98420b88cd0cdf943af682f17b0bd0e8
D:\study\programming\ESKIN\E-SKIN\docs\Final\data scalability\data\DELTA\Zero_load\N=1\M2\Repeat_7\plot_generation.log | D:\study\programming\ESKIN\E-SKIN\docs\Final\data scalability\history\pre_variable_spi_20260906\data\DELTA\Zero_load\N=1\M2\Repeat_7\plot_generation.log | 01752a946b2446ccfc166725567254837bbd1508c62fb6cadcdf3f191c806f56
D:\study\programming\ESKIN\E-SKIN\docs\Final\data scalability\data\DELTA\Zero_load\N=1\M2\Repeat_7\summary.json | D:\study\programming\ESKIN\E-SKIN\docs\Final\data scalability\history\pre_variable_spi_20260906\data\DELTA\Zero_load\N=1\M2\Repeat_7\summary.json | c1966ea13e0c3d7b4615288e85a17289ce1a5c77762c63bf92a138362cd6f52c
D:\study\programming\ESKIN\E-SKIN\docs\Final\data scalability\data\DELTA\Zero_load\N=1\M3\Repeat_1\experiment_log.md | D:\study\programming\ESKIN\E-SKIN\docs\Final\data scalability\history\pre_variable_spi_20260906\data\DELTA\Zero_load\N=1\M3\Repeat_1\experiment_log.md | 6d78c1a3cfff8e70a4b17f8f4b9634fb7b249363a2a0c85c6006d57cd3ccc6c9
D:\study\programming\ESKIN\E-SKIN\docs\Final\data scalability\data\DELTA\Zero_load\N=1\M3\Repeat_1\mul1_length_over_time.png | D:\study\programming\ESKIN\E-SKIN\docs\Final\data scalability\history\pre_variable_spi_20260906\data\DELTA\Zero_load\N=1\M3\Repeat_1\mul1_length_over_time.png | 5d620fefaf78d848482ccc5634e8e79f6eaca2cbbdbbc2f925f7c7a19ce94ccf
D:\study\programming\ESKIN\E-SKIN\docs\Final\data scalability\data\DELTA\Zero_load\N=1\M3\Repeat_1\mul1_raw.bin | D:\study\programming\ESKIN\E-SKIN\docs\Final\data scalability\history\pre_variable_spi_20260906\data\DELTA\Zero_load\N=1\M3\Repeat_1\mul1_raw.bin | 1abd3877f9a390b680c5c1804f01260f931f0e698d146b25467be011339ff63c
D:\study\programming\ESKIN\E-SKIN\docs\Final\data scalability\data\DELTA\Zero_load\N=1\M3\Repeat_1\packet_log.csv | D:\study\programming\ESKIN\E-SKIN\docs\Final\data scalability\history\pre_variable_spi_20260906\data\DELTA\Zero_load\N=1\M3\Repeat_1\packet_log.csv | 27e3296778a96c69324815719d1aff32decff0e798dc3bbde5a3ad4d3be0dd9e
D:\study\programming\ESKIN\E-SKIN\docs\Final\data scalability\data\DELTA\Zero_load\N=1\M3\Repeat_1\summary.json | D:\study\programming\ESKIN\E-SKIN\docs\Final\data scalability\history\pre_variable_spi_20260906\data\DELTA\Zero_load\N=1\M3\Repeat_1\summary.json | cfbb3f21ba91c95813608bbd03be8ebd4071645d84c15b487f9ae037063d9c08
D:\study\programming\ESKIN\E-SKIN\docs\Final\data scalability\data\DELTA\Zero_load\N=1\M3\Repeat_2\experiment_log.md | D:\study\programming\ESKIN\E-SKIN\docs\Final\data scalability\history\pre_variable_spi_20260906\data\DELTA\Zero_load\N=1\M3\Repeat_2\experiment_log.md | 965fe7fc37052863b7fa6d2173d15a96b0acc662c9e6de1d8dc3cb4c6854a31a
D:\study\programming\ESKIN\E-SKIN\docs\Final\data scalability\data\DELTA\Zero_load\N=1\M3\Repeat_2\mul1_length_over_time.png | D:\study\programming\ESKIN\E-SKIN\docs\Final\data scalability\history\pre_variable_spi_20260906\data\DELTA\Zero_load\N=1\M3\Repeat_2\mul1_length_over_time.png | 0841cd7de2e84c13a9846864ac325f8a97811f2200d2e1db4c095b8206e1d1bc
D:\study\programming\ESKIN\E-SKIN\docs\Final\data scalability\data\DELTA\Zero_load\N=1\M3\Repeat_2\mul1_raw.bin | D:\study\programming\ESKIN\E-SKIN\docs\Final\data scalability\history\pre_variable_spi_20260906\data\DELTA\Zero_load\N=1\M3\Repeat_2\mul1_raw.bin | 1fcf3be218812d2f8a2739c41e05e282359d79331d363a519b02ca3304b27c4b
D:\study\programming\ESKIN\E-SKIN\docs\Final\data scalability\data\DELTA\Zero_load\N=1\M3\Repeat_2\packet_log.csv | D:\study\programming\ESKIN\E-SKIN\docs\Final\data scalability\history\pre_variable_spi_20260906\data\DELTA\Zero_load\N=1\M3\Repeat_2\packet_log.csv | 716547446b6652a7845e14e0084b3d7de58447283866dcd36f966323172f1392
D:\study\programming\ESKIN\E-SKIN\docs\Final\data scalability\data\DELTA\Zero_load\N=1\M3\Repeat_2\summary.json | D:\study\programming\ESKIN\E-SKIN\docs\Final\data scalability\history\pre_variable_spi_20260906\data\DELTA\Zero_load\N=1\M3\Repeat_2\summary.json | 6508a6ee7acf7db09f033297833cfff91f1313f24b03cdea79ad4c7d1c90c2d2
D:\study\programming\ESKIN\E-SKIN\docs\Final\data scalability\data\DELTA\Zero_load\N=1\M3\Repeat_3\experiment_log.md | D:\study\programming\ESKIN\E-SKIN\docs\Final\data scalability\history\pre_variable_spi_20260906\data\DELTA\Zero_load\N=1\M3\Repeat_3\experiment_log.md | 64deb5ce0239379ce08715c2ebba90c68558a21aff98869d603850a09144a48c
D:\study\programming\ESKIN\E-SKIN\docs\Final\data scalability\data\DELTA\Zero_load\N=1\M3\Repeat_3\mul1_length_over_time.png | D:\study\programming\ESKIN\E-SKIN\docs\Final\data scalability\history\pre_variable_spi_20260906\data\DELTA\Zero_load\N=1\M3\Repeat_3\mul1_length_over_time.png | 9a81a7ab49c3da562ad93323169da1e1fa3af690bffa4ab01ef8cff4955acfdc
D:\study\programming\ESKIN\E-SKIN\docs\Final\data scalability\data\DELTA\Zero_load\N=1\M3\Repeat_3\mul1_raw.bin | D:\study\programming\ESKIN\E-SKIN\docs\Final\data scalability\history\pre_variable_spi_20260906\data\DELTA\Zero_load\N=1\M3\Repeat_3\mul1_raw.bin | 45323253213aad32c623cbb6ab6caed9c91504eae6fa231b70996c0c58ea78f6
D:\study\programming\ESKIN\E-SKIN\docs\Final\data scalability\data\DELTA\Zero_load\N=1\M3\Repeat_3\packet_log.csv | D:\study\programming\ESKIN\E-SKIN\docs\Final\data scalability\history\pre_variable_spi_20260906\data\DELTA\Zero_load\N=1\M3\Repeat_3\packet_log.csv | 06c6bc167e9f716695e117c991cc5636043a4ff972628c2d9fed105c93814475
D:\study\programming\ESKIN\E-SKIN\docs\Final\data scalability\data\DELTA\Zero_load\N=1\M3\Repeat_3\summary.json | D:\study\programming\ESKIN\E-SKIN\docs\Final\data scalability\history\pre_variable_spi_20260906\data\DELTA\Zero_load\N=1\M3\Repeat_3\summary.json | 9da05f80574b199d5e5e8e27dd55aa56dedc561214252dac7fc7a9018ed37c61
D:\study\programming\ESKIN\E-SKIN\docs\Final\data scalability\data\DELTA\Zero_load\N=1\M3\Repeat_4\experiment_log.md | D:\study\programming\ESKIN\E-SKIN\docs\Final\data scalability\history\pre_variable_spi_20260906\data\DELTA\Zero_load\N=1\M3\Repeat_4\experiment_log.md | 1ce54e94bf902c5e3f95c02b1f55ad53c88dd4e54ee5fa6f0f9ede53c7690b86
D:\study\programming\ESKIN\E-SKIN\docs\Final\data scalability\data\DELTA\Zero_load\N=1\M3\Repeat_4\mul1_length_over_time.png | D:\study\programming\ESKIN\E-SKIN\docs\Final\data scalability\history\pre_variable_spi_20260906\data\DELTA\Zero_load\N=1\M3\Repeat_4\mul1_length_over_time.png | eddf57343dc9fa601f53dd4648b0ee77f9194382402826c1018709d31a4665b0
D:\study\programming\ESKIN\E-SKIN\docs\Final\data scalability\data\DELTA\Zero_load\N=1\M3\Repeat_4\mul1_raw.bin | D:\study\programming\ESKIN\E-SKIN\docs\Final\data scalability\history\pre_variable_spi_20260906\data\DELTA\Zero_load\N=1\M3\Repeat_4\mul1_raw.bin | 21e768c0f0c25bda92d1820ce984687df2588c0498f0160957f8b52624a76e55
D:\study\programming\ESKIN\E-SKIN\docs\Final\data scalability\data\DELTA\Zero_load\N=1\M3\Repeat_4\packet_log.csv | D:\study\programming\ESKIN\E-SKIN\docs\Final\data scalability\history\pre_variable_spi_20260906\data\DELTA\Zero_load\N=1\M3\Repeat_4\packet_log.csv | 1733eebdc811b7d402ec12b29ecaffa34c99ca0b1a15ffc09b9fb71a0d5a9221
D:\study\programming\ESKIN\E-SKIN\docs\Final\data scalability\data\DELTA\Zero_load\N=1\M3\Repeat_4\plot_generation.log | D:\study\programming\ESKIN\E-SKIN\docs\Final\data scalability\history\pre_variable_spi_20260906\data\DELTA\Zero_load\N=1\M3\Repeat_4\plot_generation.log | 44594b5b9e6f7a8588fd729d5abafe03bea53fd2d0104f0dd632a915bad47b67
D:\study\programming\ESKIN\E-SKIN\docs\Final\data scalability\data\DELTA\Zero_load\N=1\M3\Repeat_4\summary.json | D:\study\programming\ESKIN\E-SKIN\docs\Final\data scalability\history\pre_variable_spi_20260906\data\DELTA\Zero_load\N=1\M3\Repeat_4\summary.json | 2ef38150edde54c32344f24954e0a37a6803dbbae43bb1ce7df3768e12f4708b
D:\study\programming\ESKIN\E-SKIN\docs\Final\data scalability\data\DELTA\Zero_load\N=1\M3\Repeat_5\experiment_log.md | D:\study\programming\ESKIN\E-SKIN\docs\Final\data scalability\history\pre_variable_spi_20260906\data\DELTA\Zero_load\N=1\M3\Repeat_5\experiment_log.md | 4baaec5946c0a51f05c6c32fe0a544cd96452c124477905df9f7f5a2511056ca
D:\study\programming\ESKIN\E-SKIN\docs\Final\data scalability\data\DELTA\Zero_load\N=1\M3\Repeat_5\mul1_length_over_time.png | D:\study\programming\ESKIN\E-SKIN\docs\Final\data scalability\history\pre_variable_spi_20260906\data\DELTA\Zero_load\N=1\M3\Repeat_5\mul1_length_over_time.png | 5f27df9d6bf916060efae3c01033117f42c393642b1e979c250ee025d5b32881
D:\study\programming\ESKIN\E-SKIN\docs\Final\data scalability\data\DELTA\Zero_load\N=1\M3\Repeat_5\mul1_raw.bin | D:\study\programming\ESKIN\E-SKIN\docs\Final\data scalability\history\pre_variable_spi_20260906\data\DELTA\Zero_load\N=1\M3\Repeat_5\mul1_raw.bin | 17602b93678e1bf488ff4f2159bdf360e9ffcca516d98e61021b2be2ece2e34a
D:\study\programming\ESKIN\E-SKIN\docs\Final\data scalability\data\DELTA\Zero_load\N=1\M3\Repeat_5\packet_log.csv | D:\study\programming\ESKIN\E-SKIN\docs\Final\data scalability\history\pre_variable_spi_20260906\data\DELTA\Zero_load\N=1\M3\Repeat_5\packet_log.csv | 57940c5b7f47341682382cfa6d5f5871b1466d131acff1f23a6588b672cf647c
D:\study\programming\ESKIN\E-SKIN\docs\Final\data scalability\data\DELTA\Zero_load\N=1\M3\Repeat_5\plot_generation.log | D:\study\programming\ESKIN\E-SKIN\docs\Final\data scalability\history\pre_variable_spi_20260906\data\DELTA\Zero_load\N=1\M3\Repeat_5\plot_generation.log | 183213ae14a9dc691dd5f289db2a66694789c0a0a7c26ecc9f33947c77ffb37b
D:\study\programming\ESKIN\E-SKIN\docs\Final\data scalability\data\DELTA\Zero_load\N=1\M3\Repeat_5\summary.json | D:\study\programming\ESKIN\E-SKIN\docs\Final\data scalability\history\pre_variable_spi_20260906\data\DELTA\Zero_load\N=1\M3\Repeat_5\summary.json | c0ae7d90923060d3e3d9e447e012b07a44eb93aeeb6af88e8e15b21698c27848
D:\study\programming\ESKIN\E-SKIN\docs\Final\data scalability\data\DELTA\Zero_load\N=1\M3\Repeat_6\experiment_log.md | D:\study\programming\ESKIN\E-SKIN\docs\Final\data scalability\history\pre_variable_spi_20260906\data\DELTA\Zero_load\N=1\M3\Repeat_6\experiment_log.md | 615143e4885a8b045697f15192b45ed4036cb8dc15eea0023ec8f636e4c8a090
D:\study\programming\ESKIN\E-SKIN\docs\Final\data scalability\data\DELTA\Zero_load\N=1\M3\Repeat_6\mul1_length_over_time.png | D:\study\programming\ESKIN\E-SKIN\docs\Final\data scalability\history\pre_variable_spi_20260906\data\DELTA\Zero_load\N=1\M3\Repeat_6\mul1_length_over_time.png | 19b9a36faeed57d62948d8011cbe9ba2a660dfac347dd8602c95065f264c0ac6
D:\study\programming\ESKIN\E-SKIN\docs\Final\data scalability\data\DELTA\Zero_load\N=1\M3\Repeat_6\mul1_raw.bin | D:\study\programming\ESKIN\E-SKIN\docs\Final\data scalability\history\pre_variable_spi_20260906\data\DELTA\Zero_load\N=1\M3\Repeat_6\mul1_raw.bin | f6e5c5963549f76dbd0c1c73509f91d49867dbf5433b64cddd5818bb1df6ba4e
D:\study\programming\ESKIN\E-SKIN\docs\Final\data scalability\data\DELTA\Zero_load\N=1\M3\Repeat_6\packet_log.csv | D:\study\programming\ESKIN\E-SKIN\docs\Final\data scalability\history\pre_variable_spi_20260906\data\DELTA\Zero_load\N=1\M3\Repeat_6\packet_log.csv | da763e58f079bd5f7c1d89ca6c64693e81cbbafcd24945fc70e8a8fada92c4ea
D:\study\programming\ESKIN\E-SKIN\docs\Final\data scalability\data\DELTA\Zero_load\N=1\M3\Repeat_6\plot_generation.log | D:\study\programming\ESKIN\E-SKIN\docs\Final\data scalability\history\pre_variable_spi_20260906\data\DELTA\Zero_load\N=1\M3\Repeat_6\plot_generation.log | 7cf8b75c50b13ae3c006c74af85bb4734a4e41c3d01e450c827446556f954d08
D:\study\programming\ESKIN\E-SKIN\docs\Final\data scalability\data\DELTA\Zero_load\N=1\M3\Repeat_6\summary.json | D:\study\programming\ESKIN\E-SKIN\docs\Final\data scalability\history\pre_variable_spi_20260906\data\DELTA\Zero_load\N=1\M3\Repeat_6\summary.json | f258e9892121f272aa69fdc3f25ff830d471a390f8c10be8945efa916c986699
D:\study\programming\ESKIN\E-SKIN\docs\Final\data scalability\data\DELTA\Zero_load\N=2\M0_M1\experiment_log.md | D:\study\programming\ESKIN\E-SKIN\docs\Final\data scalability\history\pre_variable_spi_20260906\data\DELTA\Zero_load\N=2\M0_M1\experiment_log.md | f0ea4cf566ab3c04871981ac88eb0478b37693db6aec4264ade14f33f59ac875
D:\study\programming\ESKIN\E-SKIN\docs\Final\data scalability\data\DELTA\Zero_load\N=2\M0_M1\mul1_length_over_time.png | D:\study\programming\ESKIN\E-SKIN\docs\Final\data scalability\history\pre_variable_spi_20260906\data\DELTA\Zero_load\N=2\M0_M1\mul1_length_over_time.png | 485d6939b672609d324101e4dd659ac9466ab89ea4cde53660d7aa92577277fe
D:\study\programming\ESKIN\E-SKIN\docs\Final\data scalability\data\DELTA\Zero_load\N=2\M0_M1\mul1_raw.bin | D:\study\programming\ESKIN\E-SKIN\docs\Final\data scalability\history\pre_variable_spi_20260906\data\DELTA\Zero_load\N=2\M0_M1\mul1_raw.bin | 567054465b03a4962cc200e621942e29d48bb54abe83db9d4b31bfef38819870
D:\study\programming\ESKIN\E-SKIN\docs\Final\data scalability\data\DELTA\Zero_load\N=2\M0_M1\packet_log.csv | D:\study\programming\ESKIN\E-SKIN\docs\Final\data scalability\history\pre_variable_spi_20260906\data\DELTA\Zero_load\N=2\M0_M1\packet_log.csv | 260cc813f7a46b86c52be1d4a1e967db171b745c1f01af965d3fb41433a4b8c6
D:\study\programming\ESKIN\E-SKIN\docs\Final\data scalability\data\DELTA\Zero_load\N=2\M0_M1\summary.json | D:\study\programming\ESKIN\E-SKIN\docs\Final\data scalability\history\pre_variable_spi_20260906\data\DELTA\Zero_load\N=2\M0_M1\summary.json | 193f2b9942bf6c47c0b0e4118fc97d978dc098fa4535e08a75bfb2f10c8a2138
D:\study\programming\ESKIN\E-SKIN\docs\Final\data scalability\data\DELTA\Zero_load\N=2\M0_M2\experiment_log.md | D:\study\programming\ESKIN\E-SKIN\docs\Final\data scalability\history\pre_variable_spi_20260906\data\DELTA\Zero_load\N=2\M0_M2\experiment_log.md | 2119ce88665ef9c334ef8d0988e299bac4e63bcf4b441ba4d2337ebd13fd8fc2
D:\study\programming\ESKIN\E-SKIN\docs\Final\data scalability\data\DELTA\Zero_load\N=2\M0_M2\mul1_length_over_time.png | D:\study\programming\ESKIN\E-SKIN\docs\Final\data scalability\history\pre_variable_spi_20260906\data\DELTA\Zero_load\N=2\M0_M2\mul1_length_over_time.png | b79ffd9230fb189678e5acf3f30d121866e9422390005bb3a9f3ed6ad3f39e1c
D:\study\programming\ESKIN\E-SKIN\docs\Final\data scalability\data\DELTA\Zero_load\N=2\M0_M2\mul1_raw.bin | D:\study\programming\ESKIN\E-SKIN\docs\Final\data scalability\history\pre_variable_spi_20260906\data\DELTA\Zero_load\N=2\M0_M2\mul1_raw.bin | 2f18f4eff508406fe9949fabeaa4d5c465627d22c30b80a69008e22ac7091f52
D:\study\programming\ESKIN\E-SKIN\docs\Final\data scalability\data\DELTA\Zero_load\N=2\M0_M2\packet_log.csv | D:\study\programming\ESKIN\E-SKIN\docs\Final\data scalability\history\pre_variable_spi_20260906\data\DELTA\Zero_load\N=2\M0_M2\packet_log.csv | 6198376faf2f2fb087506d02b295b3ce8cc7c7f37582d3101dbbfaa6b8757ec8
D:\study\programming\ESKIN\E-SKIN\docs\Final\data scalability\data\DELTA\Zero_load\N=2\M0_M2\summary.json | D:\study\programming\ESKIN\E-SKIN\docs\Final\data scalability\history\pre_variable_spi_20260906\data\DELTA\Zero_load\N=2\M0_M2\summary.json | 2bb51013e01eab6e3e078f152495c46717b979d7073f0930ea85a8a32c38caf5
D:\study\programming\ESKIN\E-SKIN\docs\Final\data scalability\data\DELTA\Zero_load\N=2\M0_M3\experiment_log.md | D:\study\programming\ESKIN\E-SKIN\docs\Final\data scalability\history\pre_variable_spi_20260906\data\DELTA\Zero_load\N=2\M0_M3\experiment_log.md | 5b7c19ead2b9f18308def5bfce2f3f42c1519a4b024cb720b6c47604f6859bd6
D:\study\programming\ESKIN\E-SKIN\docs\Final\data scalability\data\DELTA\Zero_load\N=2\M0_M3\mul1_length_over_time.png | D:\study\programming\ESKIN\E-SKIN\docs\Final\data scalability\history\pre_variable_spi_20260906\data\DELTA\Zero_load\N=2\M0_M3\mul1_length_over_time.png | efa58e5b87d808210e3052c6839f2e90eceace51891a449d3baf3ee5343bef90
D:\study\programming\ESKIN\E-SKIN\docs\Final\data scalability\data\DELTA\Zero_load\N=2\M0_M3\mul1_raw.bin | D:\study\programming\ESKIN\E-SKIN\docs\Final\data scalability\history\pre_variable_spi_20260906\data\DELTA\Zero_load\N=2\M0_M3\mul1_raw.bin | bc43c8e220813d0e361e0ad235dd12afb1b14c6ac6d8b263647fef3ecad59e6c
D:\study\programming\ESKIN\E-SKIN\docs\Final\data scalability\data\DELTA\Zero_load\N=2\M0_M3\packet_log.csv | D:\study\programming\ESKIN\E-SKIN\docs\Final\data scalability\history\pre_variable_spi_20260906\data\DELTA\Zero_load\N=2\M0_M3\packet_log.csv | 7d7c93af9b40605c129643fbf3a0659ba85186e0344d6330c9d60b6f38f78213
D:\study\programming\ESKIN\E-SKIN\docs\Final\data scalability\data\DELTA\Zero_load\N=2\M0_M3\summary.json | D:\study\programming\ESKIN\E-SKIN\docs\Final\data scalability\history\pre_variable_spi_20260906\data\DELTA\Zero_load\N=2\M0_M3\summary.json | aa22ba0a5190225a424e7070e3ae86433b1c744ef29994d3236fc6bb9186ac46
D:\study\programming\ESKIN\E-SKIN\docs\Final\data scalability\data\DELTA\Zero_load\N=2\M1_M2\experiment_log.md | D:\study\programming\ESKIN\E-SKIN\docs\Final\data scalability\history\pre_variable_spi_20260906\data\DELTA\Zero_load\N=2\M1_M2\experiment_log.md | 39294f117874f1992e50494bc6c532fb82fd8cb61d9399205278c2ebb8509da8
D:\study\programming\ESKIN\E-SKIN\docs\Final\data scalability\data\DELTA\Zero_load\N=2\M1_M2\mul1_length_over_time.png | D:\study\programming\ESKIN\E-SKIN\docs\Final\data scalability\history\pre_variable_spi_20260906\data\DELTA\Zero_load\N=2\M1_M2\mul1_length_over_time.png | 80a58f2a45aaf58584db4c56eb9fbe0f638f43ea377856d1db2a2281cd7bbc2b
D:\study\programming\ESKIN\E-SKIN\docs\Final\data scalability\data\DELTA\Zero_load\N=2\M1_M2\mul1_raw.bin | D:\study\programming\ESKIN\E-SKIN\docs\Final\data scalability\history\pre_variable_spi_20260906\data\DELTA\Zero_load\N=2\M1_M2\mul1_raw.bin | 8e6f347a83abc6868717b1d10fecd261c3eb5335696648b2e4a990e80b3b7246
D:\study\programming\ESKIN\E-SKIN\docs\Final\data scalability\data\DELTA\Zero_load\N=2\M1_M2\packet_log.csv | D:\study\programming\ESKIN\E-SKIN\docs\Final\data scalability\history\pre_variable_spi_20260906\data\DELTA\Zero_load\N=2\M1_M2\packet_log.csv | a415d64c7e32c6e0c75cbb2cca00e95fc622f0c78dce1338d0fce644245b41ec
D:\study\programming\ESKIN\E-SKIN\docs\Final\data scalability\data\DELTA\Zero_load\N=2\M1_M2\summary.json | D:\study\programming\ESKIN\E-SKIN\docs\Final\data scalability\history\pre_variable_spi_20260906\data\DELTA\Zero_load\N=2\M1_M2\summary.json | 3b29327e6d846ae05cadc34679f6a09a3757be520c870aca35c8dd9d53958034
D:\study\programming\ESKIN\E-SKIN\docs\Final\data scalability\data\DELTA\Zero_load\N=2\M1_M3\experiment_log.md | D:\study\programming\ESKIN\E-SKIN\docs\Final\data scalability\history\pre_variable_spi_20260906\data\DELTA\Zero_load\N=2\M1_M3\experiment_log.md | 0a57d8941adb3bf6b469d42c6cf4c0bcc0b0905455fa1a552ae85ae6789cdbee
D:\study\programming\ESKIN\E-SKIN\docs\Final\data scalability\data\DELTA\Zero_load\N=2\M1_M3\mul1_length_over_time.png | D:\study\programming\ESKIN\E-SKIN\docs\Final\data scalability\history\pre_variable_spi_20260906\data\DELTA\Zero_load\N=2\M1_M3\mul1_length_over_time.png | 1076483a372858848ade6fc2c18b9338fa6dd8b5d993728ae5243f848c4f048c
D:\study\programming\ESKIN\E-SKIN\docs\Final\data scalability\data\DELTA\Zero_load\N=2\M1_M3\mul1_raw.bin | D:\study\programming\ESKIN\E-SKIN\docs\Final\data scalability\history\pre_variable_spi_20260906\data\DELTA\Zero_load\N=2\M1_M3\mul1_raw.bin | a9aeb3d087b64fd1abc84f6210a6e5cf4b3cb718297131fe3c940ecbede61af2
D:\study\programming\ESKIN\E-SKIN\docs\Final\data scalability\data\DELTA\Zero_load\N=2\M1_M3\packet_log.csv | D:\study\programming\ESKIN\E-SKIN\docs\Final\data scalability\history\pre_variable_spi_20260906\data\DELTA\Zero_load\N=2\M1_M3\packet_log.csv | 5663c3effe45156e02adfe5c7617b5ae7beadf2dd53ab5cdea3013603af75c26
D:\study\programming\ESKIN\E-SKIN\docs\Final\data scalability\data\DELTA\Zero_load\N=2\M1_M3\summary.json | D:\study\programming\ESKIN\E-SKIN\docs\Final\data scalability\history\pre_variable_spi_20260906\data\DELTA\Zero_load\N=2\M1_M3\summary.json | 4f6bea449ceb0ad3b28b7d07e8d36fa96d65d87343af56d4276603e6b29e00e0
D:\study\programming\ESKIN\E-SKIN\docs\Final\data scalability\data\DELTA\Zero_load\N=2\M2_M3\experiment_log.md | D:\study\programming\ESKIN\E-SKIN\docs\Final\data scalability\history\pre_variable_spi_20260906\data\DELTA\Zero_load\N=2\M2_M3\experiment_log.md | 9c0a860b7a8a0aa58bf6136c07975a7731af417125bb31a5bb88f5a3340fc203
D:\study\programming\ESKIN\E-SKIN\docs\Final\data scalability\data\DELTA\Zero_load\N=2\M2_M3\mul1_length_over_time.png | D:\study\programming\ESKIN\E-SKIN\docs\Final\data scalability\history\pre_variable_spi_20260906\data\DELTA\Zero_load\N=2\M2_M3\mul1_length_over_time.png | ec4f840de391d79354a83d529370937e7fdc5df6465bc09817196abf3c627d50
D:\study\programming\ESKIN\E-SKIN\docs\Final\data scalability\data\DELTA\Zero_load\N=2\M2_M3\mul1_raw.bin | D:\study\programming\ESKIN\E-SKIN\docs\Final\data scalability\history\pre_variable_spi_20260906\data\DELTA\Zero_load\N=2\M2_M3\mul1_raw.bin | 3db85a27eeca1aa9b757b151b6a03020c5e19fefaa437b8630140288a8ea3c70
D:\study\programming\ESKIN\E-SKIN\docs\Final\data scalability\data\DELTA\Zero_load\N=2\M2_M3\packet_log.csv | D:\study\programming\ESKIN\E-SKIN\docs\Final\data scalability\history\pre_variable_spi_20260906\data\DELTA\Zero_load\N=2\M2_M3\packet_log.csv | 50ca3c3ce080cdbcbc9b1b8f8699b7dcee8458ee0ffa8c3057212f962e1a72a6
D:\study\programming\ESKIN\E-SKIN\docs\Final\data scalability\data\DELTA\Zero_load\N=2\M2_M3\summary.json | D:\study\programming\ESKIN\E-SKIN\docs\Final\data scalability\history\pre_variable_spi_20260906\data\DELTA\Zero_load\N=2\M2_M3\summary.json | e554fe44f7ea9b156dd5f475f7860a303fe5543427f8ce43a14f7d8cd73f378f
D:\study\programming\ESKIN\E-SKIN\docs\Final\data scalability\data\DELTA\Zero_load\N=3\M0_M1_M2\experiment_log.md | D:\study\programming\ESKIN\E-SKIN\docs\Final\data scalability\history\pre_variable_spi_20260906\data\DELTA\Zero_load\N=3\M0_M1_M2\experiment_log.md | 77373b964e740c45a42f7112cea942b9ce249506279586745e9e4eb4fa584af2
D:\study\programming\ESKIN\E-SKIN\docs\Final\data scalability\data\DELTA\Zero_load\N=3\M0_M1_M2\mul1_length_over_time.png | D:\study\programming\ESKIN\E-SKIN\docs\Final\data scalability\history\pre_variable_spi_20260906\data\DELTA\Zero_load\N=3\M0_M1_M2\mul1_length_over_time.png | acd5316b3c8759e30a277ed5ffe66acdbd22a47d20c465386c0ac009c4fdef10
D:\study\programming\ESKIN\E-SKIN\docs\Final\data scalability\data\DELTA\Zero_load\N=3\M0_M1_M2\mul1_raw.bin | D:\study\programming\ESKIN\E-SKIN\docs\Final\data scalability\history\pre_variable_spi_20260906\data\DELTA\Zero_load\N=3\M0_M1_M2\mul1_raw.bin | 6a9e6eb91d239ea50ba7aee27cae7e6edf8a04edcb864877c51af901aa7cdf73
D:\study\programming\ESKIN\E-SKIN\docs\Final\data scalability\data\DELTA\Zero_load\N=3\M0_M1_M2\packet_log.csv | D:\study\programming\ESKIN\E-SKIN\docs\Final\data scalability\history\pre_variable_spi_20260906\data\DELTA\Zero_load\N=3\M0_M1_M2\packet_log.csv | 5472b93bc3a7a185c1f916c37c3719c2c2764929d9a56257584dc0115b5fe902
D:\study\programming\ESKIN\E-SKIN\docs\Final\data scalability\data\DELTA\Zero_load\N=3\M0_M1_M2\summary.json | D:\study\programming\ESKIN\E-SKIN\docs\Final\data scalability\history\pre_variable_spi_20260906\data\DELTA\Zero_load\N=3\M0_M1_M2\summary.json | 255a6aab9f1fae3ecf5aea5f34a26da5ef681ecec2da91b0cda693b168b6b991
D:\study\programming\ESKIN\E-SKIN\docs\Final\data scalability\data\DELTA\Zero_load\N=3\M0_M1_M3\Repeat_1\experiment_log.md | D:\study\programming\ESKIN\E-SKIN\docs\Final\data scalability\history\pre_variable_spi_20260906\data\DELTA\Zero_load\N=3\M0_M1_M3\Repeat_1\experiment_log.md | 84cd767d31635f5f33a2f13d354e23f0b4c64cf67318277461ca52526b6aa60d
D:\study\programming\ESKIN\E-SKIN\docs\Final\data scalability\data\DELTA\Zero_load\N=3\M0_M1_M3\Repeat_1\mul1_length_over_time.png | D:\study\programming\ESKIN\E-SKIN\docs\Final\data scalability\history\pre_variable_spi_20260906\data\DELTA\Zero_load\N=3\M0_M1_M3\Repeat_1\mul1_length_over_time.png | 2a6191d6a680ac2c2cdb058e30262673c3f0b45632e58c6bbda361e65f65aa35
D:\study\programming\ESKIN\E-SKIN\docs\Final\data scalability\data\DELTA\Zero_load\N=3\M0_M1_M3\Repeat_1\mul1_raw.bin | D:\study\programming\ESKIN\E-SKIN\docs\Final\data scalability\history\pre_variable_spi_20260906\data\DELTA\Zero_load\N=3\M0_M1_M3\Repeat_1\mul1_raw.bin | 4cc7f86fb5f6b23e32e9586876b1182eaa7b834b43b0db933ef4c1209ccc4584
D:\study\programming\ESKIN\E-SKIN\docs\Final\data scalability\data\DELTA\Zero_load\N=3\M0_M1_M3\Repeat_1\packet_log.csv | D:\study\programming\ESKIN\E-SKIN\docs\Final\data scalability\history\pre_variable_spi_20260906\data\DELTA\Zero_load\N=3\M0_M1_M3\Repeat_1\packet_log.csv | df2717b40b9f5db9a537ccebfa5d4ff8612ccda7b36b7ee106c1c07e26d33e49
D:\study\programming\ESKIN\E-SKIN\docs\Final\data scalability\data\DELTA\Zero_load\N=3\M0_M1_M3\Repeat_1\plot_generation.log | D:\study\programming\ESKIN\E-SKIN\docs\Final\data scalability\history\pre_variable_spi_20260906\data\DELTA\Zero_load\N=3\M0_M1_M3\Repeat_1\plot_generation.log | 30900253619f687f65211b7c48b9e1fda0876d0c4424d18e4c0b92d6e64ee870
D:\study\programming\ESKIN\E-SKIN\docs\Final\data scalability\data\DELTA\Zero_load\N=3\M0_M1_M3\Repeat_1\summary.json | D:\study\programming\ESKIN\E-SKIN\docs\Final\data scalability\history\pre_variable_spi_20260906\data\DELTA\Zero_load\N=3\M0_M1_M3\Repeat_1\summary.json | 1245662fcaeb561dd30dd02c55760fd4f238a3b6ffdd0bcd091fe96cdbc86302
D:\study\programming\ESKIN\E-SKIN\docs\Final\data scalability\data\DELTA\Zero_load\N=3\M0_M1_M3\Repeat_2\experiment_log.md | D:\study\programming\ESKIN\E-SKIN\docs\Final\data scalability\history\pre_variable_spi_20260906\data\DELTA\Zero_load\N=3\M0_M1_M3\Repeat_2\experiment_log.md | f6aa6d571636057bffdaf83d3c8bb433048094afc2a74c00accc0bee7751853b
D:\study\programming\ESKIN\E-SKIN\docs\Final\data scalability\data\DELTA\Zero_load\N=3\M0_M1_M3\Repeat_2\mul1_length_over_time.png | D:\study\programming\ESKIN\E-SKIN\docs\Final\data scalability\history\pre_variable_spi_20260906\data\DELTA\Zero_load\N=3\M0_M1_M3\Repeat_2\mul1_length_over_time.png | ee1883be830ea00cb56b42dc7ef489cfbcb56e1df17a825e7d77e3ee449b03ee
D:\study\programming\ESKIN\E-SKIN\docs\Final\data scalability\data\DELTA\Zero_load\N=3\M0_M1_M3\Repeat_2\mul1_raw.bin | D:\study\programming\ESKIN\E-SKIN\docs\Final\data scalability\history\pre_variable_spi_20260906\data\DELTA\Zero_load\N=3\M0_M1_M3\Repeat_2\mul1_raw.bin | 1bce6cfe95c52ea65edc6ff7d6005d57233b8c7190ec15dc17c4df25012a792e
D:\study\programming\ESKIN\E-SKIN\docs\Final\data scalability\data\DELTA\Zero_load\N=3\M0_M1_M3\Repeat_2\packet_log.csv | D:\study\programming\ESKIN\E-SKIN\docs\Final\data scalability\history\pre_variable_spi_20260906\data\DELTA\Zero_load\N=3\M0_M1_M3\Repeat_2\packet_log.csv | 34dc14a8715411cb9a5e966637862a0391b20e93346bd8520ebdbf37405e1bc6
D:\study\programming\ESKIN\E-SKIN\docs\Final\data scalability\data\DELTA\Zero_load\N=3\M0_M1_M3\Repeat_2\plot_generation.log | D:\study\programming\ESKIN\E-SKIN\docs\Final\data scalability\history\pre_variable_spi_20260906\data\DELTA\Zero_load\N=3\M0_M1_M3\Repeat_2\plot_generation.log | aae76ade1bca2e4e9192da2c85dc33e762028f15ab16ce4bd8f3b26bb1d41085
D:\study\programming\ESKIN\E-SKIN\docs\Final\data scalability\data\DELTA\Zero_load\N=3\M0_M1_M3\Repeat_2\summary.json | D:\study\programming\ESKIN\E-SKIN\docs\Final\data scalability\history\pre_variable_spi_20260906\data\DELTA\Zero_load\N=3\M0_M1_M3\Repeat_2\summary.json | f23eaccaad65fe7f79a6cad3e27694a5f92fb9eff0ec3665c7ec64a3c5584b77
D:\study\programming\ESKIN\E-SKIN\docs\Final\data scalability\data\DELTA\Zero_load\N=3\M0_M1_M3\Repeat_3\experiment_log.md | D:\study\programming\ESKIN\E-SKIN\docs\Final\data scalability\history\pre_variable_spi_20260906\data\DELTA\Zero_load\N=3\M0_M1_M3\Repeat_3\experiment_log.md | b4f08b5e714e34d52a59a7d90922e73a009054db3f430d8beb5398390da5ce5d
D:\study\programming\ESKIN\E-SKIN\docs\Final\data scalability\data\DELTA\Zero_load\N=3\M0_M1_M3\Repeat_3\mul1_length_over_time.png | D:\study\programming\ESKIN\E-SKIN\docs\Final\data scalability\history\pre_variable_spi_20260906\data\DELTA\Zero_load\N=3\M0_M1_M3\Repeat_3\mul1_length_over_time.png | c670ef7748be6b43c735b58e8870288940e6eb07f9bcf4b4121ec39ffb778696
D:\study\programming\ESKIN\E-SKIN\docs\Final\data scalability\data\DELTA\Zero_load\N=3\M0_M1_M3\Repeat_3\mul1_raw.bin | D:\study\programming\ESKIN\E-SKIN\docs\Final\data scalability\history\pre_variable_spi_20260906\data\DELTA\Zero_load\N=3\M0_M1_M3\Repeat_3\mul1_raw.bin | f2df05493851cb1954c116ee791ccca8e95e3ba0adc284f30769cf6faeed2ff9
D:\study\programming\ESKIN\E-SKIN\docs\Final\data scalability\data\DELTA\Zero_load\N=3\M0_M1_M3\Repeat_3\packet_log.csv | D:\study\programming\ESKIN\E-SKIN\docs\Final\data scalability\history\pre_variable_spi_20260906\data\DELTA\Zero_load\N=3\M0_M1_M3\Repeat_3\packet_log.csv | 09a73faf9f434a2da0b3b9ba9b4b7acb34b6548fb799f943f51d5c718ad9e402
D:\study\programming\ESKIN\E-SKIN\docs\Final\data scalability\data\DELTA\Zero_load\N=3\M0_M1_M3\Repeat_3\plot_generation.log | D:\study\programming\ESKIN\E-SKIN\docs\Final\data scalability\history\pre_variable_spi_20260906\data\DELTA\Zero_load\N=3\M0_M1_M3\Repeat_3\plot_generation.log | 837fdf65243b98e686eaa6e75b131bee45b7c6dc2daba1f2f5ffff8a7a2d2311
D:\study\programming\ESKIN\E-SKIN\docs\Final\data scalability\data\DELTA\Zero_load\N=3\M0_M1_M3\Repeat_3\summary.json | D:\study\programming\ESKIN\E-SKIN\docs\Final\data scalability\history\pre_variable_spi_20260906\data\DELTA\Zero_load\N=3\M0_M1_M3\Repeat_3\summary.json | b7945e205cbd12a272021ebc3854a119b786b58c9664480fd12cc38c4ec73cb0
D:\study\programming\ESKIN\E-SKIN\docs\Final\data scalability\data\DELTA\Zero_load\N=3\M0_M1_M3\Repeat_4\experiment_log.md | D:\study\programming\ESKIN\E-SKIN\docs\Final\data scalability\history\pre_variable_spi_20260906\data\DELTA\Zero_load\N=3\M0_M1_M3\Repeat_4\experiment_log.md | 7540f258b85685f7026c3fbaf8be0b65852f194661b3cd4151a5efe61fa150f9
D:\study\programming\ESKIN\E-SKIN\docs\Final\data scalability\data\DELTA\Zero_load\N=3\M0_M1_M3\Repeat_4\mul1_length_over_time.png | D:\study\programming\ESKIN\E-SKIN\docs\Final\data scalability\history\pre_variable_spi_20260906\data\DELTA\Zero_load\N=3\M0_M1_M3\Repeat_4\mul1_length_over_time.png | be1475bb69a4bc6666583607f362ffc639aae0085a8d16f27247da0b1fd3d719
D:\study\programming\ESKIN\E-SKIN\docs\Final\data scalability\data\DELTA\Zero_load\N=3\M0_M1_M3\Repeat_4\mul1_raw.bin | D:\study\programming\ESKIN\E-SKIN\docs\Final\data scalability\history\pre_variable_spi_20260906\data\DELTA\Zero_load\N=3\M0_M1_M3\Repeat_4\mul1_raw.bin | e56306576d7598ec904383ce4f9bb6a8de642c39492fcd4559a24296847694e0
D:\study\programming\ESKIN\E-SKIN\docs\Final\data scalability\data\DELTA\Zero_load\N=3\M0_M1_M3\Repeat_4\packet_log.csv | D:\study\programming\ESKIN\E-SKIN\docs\Final\data scalability\history\pre_variable_spi_20260906\data\DELTA\Zero_load\N=3\M0_M1_M3\Repeat_4\packet_log.csv | 0f913f330a58fe4f9a7c653c1557c3f81f70935b54bbe40971f83190d4d7f5a7
D:\study\programming\ESKIN\E-SKIN\docs\Final\data scalability\data\DELTA\Zero_load\N=3\M0_M1_M3\Repeat_4\plot_generation.log | D:\study\programming\ESKIN\E-SKIN\docs\Final\data scalability\history\pre_variable_spi_20260906\data\DELTA\Zero_load\N=3\M0_M1_M3\Repeat_4\plot_generation.log | a611d32f294fcefd486fa9b06ab7997a7b532ac1defba1b0db9e3d62470efa72
D:\study\programming\ESKIN\E-SKIN\docs\Final\data scalability\data\DELTA\Zero_load\N=3\M0_M1_M3\Repeat_4\summary.json | D:\study\programming\ESKIN\E-SKIN\docs\Final\data scalability\history\pre_variable_spi_20260906\data\DELTA\Zero_load\N=3\M0_M1_M3\Repeat_4\summary.json | 5f6d63503928e59cd99984c6372c25ec9744f14a2c56ebcff6efee8431fa7a70
D:\study\programming\ESKIN\E-SKIN\docs\Final\data scalability\data\DELTA\Zero_load\N=3\M0_M2_M3\Repeat_1\experiment_log.md | D:\study\programming\ESKIN\E-SKIN\docs\Final\data scalability\history\pre_variable_spi_20260906\data\DELTA\Zero_load\N=3\M0_M2_M3\Repeat_1\experiment_log.md | 44084a43cc53698b7c63d10e5ad3785cb1c633f7f2f6b07a56f0eb2cf34f3cb5
D:\study\programming\ESKIN\E-SKIN\docs\Final\data scalability\data\DELTA\Zero_load\N=3\M0_M2_M3\Repeat_1\mul1_length_over_time.png | D:\study\programming\ESKIN\E-SKIN\docs\Final\data scalability\history\pre_variable_spi_20260906\data\DELTA\Zero_load\N=3\M0_M2_M3\Repeat_1\mul1_length_over_time.png | 88ed0898f13a384de3374ecc4fd1311c3ac7e66bd5631be4714b477f4650ae45
D:\study\programming\ESKIN\E-SKIN\docs\Final\data scalability\data\DELTA\Zero_load\N=3\M0_M2_M3\Repeat_1\mul1_raw.bin | D:\study\programming\ESKIN\E-SKIN\docs\Final\data scalability\history\pre_variable_spi_20260906\data\DELTA\Zero_load\N=3\M0_M2_M3\Repeat_1\mul1_raw.bin | 7670634e7d5faafb7c086578184eb52fea41999ef67284ced13b24f8d35b2acb
D:\study\programming\ESKIN\E-SKIN\docs\Final\data scalability\data\DELTA\Zero_load\N=3\M0_M2_M3\Repeat_1\packet_log.csv | D:\study\programming\ESKIN\E-SKIN\docs\Final\data scalability\history\pre_variable_spi_20260906\data\DELTA\Zero_load\N=3\M0_M2_M3\Repeat_1\packet_log.csv | 6b1e4e07191b89d63a5730122af426b53bf544ad6c6e98e8598d2645ab72b70b
D:\study\programming\ESKIN\E-SKIN\docs\Final\data scalability\data\DELTA\Zero_load\N=3\M0_M2_M3\Repeat_1\plot_generation.log | D:\study\programming\ESKIN\E-SKIN\docs\Final\data scalability\history\pre_variable_spi_20260906\data\DELTA\Zero_load\N=3\M0_M2_M3\Repeat_1\plot_generation.log | ebab0ef2fa390616e54012206315b2343c10536392957d60e480bc0a5fa3c6eb
D:\study\programming\ESKIN\E-SKIN\docs\Final\data scalability\data\DELTA\Zero_load\N=3\M0_M2_M3\Repeat_1\summary.json | D:\study\programming\ESKIN\E-SKIN\docs\Final\data scalability\history\pre_variable_spi_20260906\data\DELTA\Zero_load\N=3\M0_M2_M3\Repeat_1\summary.json | 5f7e0a9a945f44c9c8d3fd05c684d7ea0b9a8cd90e943305c9ddb8390910b7ba
D:\study\programming\ESKIN\E-SKIN\docs\Final\data scalability\data\DELTA\Zero_load\N=3\M0_M2_M3\Repeat_2\experiment_log.md | D:\study\programming\ESKIN\E-SKIN\docs\Final\data scalability\history\pre_variable_spi_20260906\data\DELTA\Zero_load\N=3\M0_M2_M3\Repeat_2\experiment_log.md | 8a71de86494456461fd55395dbf0d7c919a0be4d0a40dd57c6db6652bd9332b4
D:\study\programming\ESKIN\E-SKIN\docs\Final\data scalability\data\DELTA\Zero_load\N=3\M0_M2_M3\Repeat_2\mul1_length_over_time.png | D:\study\programming\ESKIN\E-SKIN\docs\Final\data scalability\history\pre_variable_spi_20260906\data\DELTA\Zero_load\N=3\M0_M2_M3\Repeat_2\mul1_length_over_time.png | 499fcc52f260dbd38465e8ed94d8d56d69b4ba473afb3876a64fe8062d2b1fd0
D:\study\programming\ESKIN\E-SKIN\docs\Final\data scalability\data\DELTA\Zero_load\N=3\M0_M2_M3\Repeat_2\mul1_raw.bin | D:\study\programming\ESKIN\E-SKIN\docs\Final\data scalability\history\pre_variable_spi_20260906\data\DELTA\Zero_load\N=3\M0_M2_M3\Repeat_2\mul1_raw.bin | 647a1096e0ee062ab72142beeb851f03c25d7b67eeb5fff9cbd4161f1388299b
D:\study\programming\ESKIN\E-SKIN\docs\Final\data scalability\data\DELTA\Zero_load\N=3\M0_M2_M3\Repeat_2\packet_log.csv | D:\study\programming\ESKIN\E-SKIN\docs\Final\data scalability\history\pre_variable_spi_20260906\data\DELTA\Zero_load\N=3\M0_M2_M3\Repeat_2\packet_log.csv | 215011ea2efe4898aeef8672aa750861eb4c926981abd0bfae711f14c2717948
D:\study\programming\ESKIN\E-SKIN\docs\Final\data scalability\data\DELTA\Zero_load\N=3\M0_M2_M3\Repeat_2\plot_generation.log | D:\study\programming\ESKIN\E-SKIN\docs\Final\data scalability\history\pre_variable_spi_20260906\data\DELTA\Zero_load\N=3\M0_M2_M3\Repeat_2\plot_generation.log | deec9a80d11d6ec950386ebf6f3ac6bdf04f89c0fa5cf912e36b59a32ed58178
D:\study\programming\ESKIN\E-SKIN\docs\Final\data scalability\data\DELTA\Zero_load\N=3\M0_M2_M3\Repeat_2\summary.json | D:\study\programming\ESKIN\E-SKIN\docs\Final\data scalability\history\pre_variable_spi_20260906\data\DELTA\Zero_load\N=3\M0_M2_M3\Repeat_2\summary.json | f50438f94d52ea722de47f11cdb0bda5acf892efa9c3678c04fa6997c38fad63
D:\study\programming\ESKIN\E-SKIN\docs\Final\data scalability\data\DELTA\Zero_load\N=3\M0_M2_M3\Repeat_3\experiment_log.md | D:\study\programming\ESKIN\E-SKIN\docs\Final\data scalability\history\pre_variable_spi_20260906\data\DELTA\Zero_load\N=3\M0_M2_M3\Repeat_3\experiment_log.md | 73a2be15b4862b3d4fc8e62b74207302128a8343856055e72a882d5ecaeba36f
D:\study\programming\ESKIN\E-SKIN\docs\Final\data scalability\data\DELTA\Zero_load\N=3\M0_M2_M3\Repeat_3\mul1_length_over_time.png | D:\study\programming\ESKIN\E-SKIN\docs\Final\data scalability\history\pre_variable_spi_20260906\data\DELTA\Zero_load\N=3\M0_M2_M3\Repeat_3\mul1_length_over_time.png | 3ffa9b9867b13ff8ec63c425fcd7c542f76987deeb31f55f848cfc32440db927
D:\study\programming\ESKIN\E-SKIN\docs\Final\data scalability\data\DELTA\Zero_load\N=3\M0_M2_M3\Repeat_3\mul1_raw.bin | D:\study\programming\ESKIN\E-SKIN\docs\Final\data scalability\history\pre_variable_spi_20260906\data\DELTA\Zero_load\N=3\M0_M2_M3\Repeat_3\mul1_raw.bin | 4a3209ae0fb1150d3f8ca31a0ce677705858404094a451fc166d00077fcc9fa1
D:\study\programming\ESKIN\E-SKIN\docs\Final\data scalability\data\DELTA\Zero_load\N=3\M0_M2_M3\Repeat_3\packet_log.csv | D:\study\programming\ESKIN\E-SKIN\docs\Final\data scalability\history\pre_variable_spi_20260906\data\DELTA\Zero_load\N=3\M0_M2_M3\Repeat_3\packet_log.csv | 55d1dffcbc58f59a048e5f9c04dd512421397a9a99ac4a47a558ac4190a63853
D:\study\programming\ESKIN\E-SKIN\docs\Final\data scalability\data\DELTA\Zero_load\N=3\M0_M2_M3\Repeat_3\plot_generation.log | D:\study\programming\ESKIN\E-SKIN\docs\Final\data scalability\history\pre_variable_spi_20260906\data\DELTA\Zero_load\N=3\M0_M2_M3\Repeat_3\plot_generation.log | b363787b70f3175f6926960b7d5efa7ab5c12b4336c9c7a832288ed20feef15c
D:\study\programming\ESKIN\E-SKIN\docs\Final\data scalability\data\DELTA\Zero_load\N=3\M0_M2_M3\Repeat_3\summary.json | D:\study\programming\ESKIN\E-SKIN\docs\Final\data scalability\history\pre_variable_spi_20260906\data\DELTA\Zero_load\N=3\M0_M2_M3\Repeat_3\summary.json | 8f88edc8e7e22c63d9679354c69f87c2212eb23bbb104d289ee251779503888a
D:\study\programming\ESKIN\E-SKIN\docs\Final\data scalability\data\DELTA\Zero_load\N=3\M0_M2_M3\Repeat_4\experiment_log.md | D:\study\programming\ESKIN\E-SKIN\docs\Final\data scalability\history\pre_variable_spi_20260906\data\DELTA\Zero_load\N=3\M0_M2_M3\Repeat_4\experiment_log.md | 5f92509c0435a31dfb44f638b1b7cf77482c814129e9027d614a4fe7f3205b3b
D:\study\programming\ESKIN\E-SKIN\docs\Final\data scalability\data\DELTA\Zero_load\N=3\M0_M2_M3\Repeat_4\mul1_length_over_time.png | D:\study\programming\ESKIN\E-SKIN\docs\Final\data scalability\history\pre_variable_spi_20260906\data\DELTA\Zero_load\N=3\M0_M2_M3\Repeat_4\mul1_length_over_time.png | 6c1c43990cdc6460f098217ad64a17807424d1821a3f083b9b6979d7f9fa9b91
D:\study\programming\ESKIN\E-SKIN\docs\Final\data scalability\data\DELTA\Zero_load\N=3\M0_M2_M3\Repeat_4\mul1_raw.bin | D:\study\programming\ESKIN\E-SKIN\docs\Final\data scalability\history\pre_variable_spi_20260906\data\DELTA\Zero_load\N=3\M0_M2_M3\Repeat_4\mul1_raw.bin | 125608090a164f312b0c181e59064486388aa92d49690420cd50cb63010766cf
D:\study\programming\ESKIN\E-SKIN\docs\Final\data scalability\data\DELTA\Zero_load\N=3\M0_M2_M3\Repeat_4\packet_log.csv | D:\study\programming\ESKIN\E-SKIN\docs\Final\data scalability\history\pre_variable_spi_20260906\data\DELTA\Zero_load\N=3\M0_M2_M3\Repeat_4\packet_log.csv | 6e5635c8623204dfea73cb9998a3a2365d872bb7d37294980afc5b6aba10a65c
D:\study\programming\ESKIN\E-SKIN\docs\Final\data scalability\data\DELTA\Zero_load\N=3\M0_M2_M3\Repeat_4\plot_generation.log | D:\study\programming\ESKIN\E-SKIN\docs\Final\data scalability\history\pre_variable_spi_20260906\data\DELTA\Zero_load\N=3\M0_M2_M3\Repeat_4\plot_generation.log | 59c882ac84068b283362916b3f5d2e10c92afd34db868f5b7dfc0ffb011833c1
D:\study\programming\ESKIN\E-SKIN\docs\Final\data scalability\data\DELTA\Zero_load\N=3\M0_M2_M3\Repeat_4\summary.json | D:\study\programming\ESKIN\E-SKIN\docs\Final\data scalability\history\pre_variable_spi_20260906\data\DELTA\Zero_load\N=3\M0_M2_M3\Repeat_4\summary.json | 3ef9c3cca6c337106d18ca3a1af8ede44480a15693ba548e48b91373afcb8749
D:\study\programming\ESKIN\E-SKIN\docs\Final\data scalability\data\DELTA\Zero_load\N=3\M1_M2_M3\Repeat_1\experiment_log.md | D:\study\programming\ESKIN\E-SKIN\docs\Final\data scalability\history\pre_variable_spi_20260906\data\DELTA\Zero_load\N=3\M1_M2_M3\Repeat_1\experiment_log.md | b6406423d65fb95f2122df18bd46a5c2790b68f4b29d02f7193476ce378386af
D:\study\programming\ESKIN\E-SKIN\docs\Final\data scalability\data\DELTA\Zero_load\N=3\M1_M2_M3\Repeat_1\mul1_length_over_time.png | D:\study\programming\ESKIN\E-SKIN\docs\Final\data scalability\history\pre_variable_spi_20260906\data\DELTA\Zero_load\N=3\M1_M2_M3\Repeat_1\mul1_length_over_time.png | d9ad8e17696a98eed0365b04b9481fafdc71e95585292acec69acee7b6f35cd1
D:\study\programming\ESKIN\E-SKIN\docs\Final\data scalability\data\DELTA\Zero_load\N=3\M1_M2_M3\Repeat_1\mul1_raw.bin | D:\study\programming\ESKIN\E-SKIN\docs\Final\data scalability\history\pre_variable_spi_20260906\data\DELTA\Zero_load\N=3\M1_M2_M3\Repeat_1\mul1_raw.bin | 41844620bc845991c149abca7f3681fe8994c0ff4809ca24edbf57716fdc6695
D:\study\programming\ESKIN\E-SKIN\docs\Final\data scalability\data\DELTA\Zero_load\N=3\M1_M2_M3\Repeat_1\packet_log.csv | D:\study\programming\ESKIN\E-SKIN\docs\Final\data scalability\history\pre_variable_spi_20260906\data\DELTA\Zero_load\N=3\M1_M2_M3\Repeat_1\packet_log.csv | 6d2eeb3613971dc9a25b2812b3a7214c0ca54c0cfa63424fafcd5083327cdcc5
D:\study\programming\ESKIN\E-SKIN\docs\Final\data scalability\data\DELTA\Zero_load\N=3\M1_M2_M3\Repeat_1\plot_generation.log | D:\study\programming\ESKIN\E-SKIN\docs\Final\data scalability\history\pre_variable_spi_20260906\data\DELTA\Zero_load\N=3\M1_M2_M3\Repeat_1\plot_generation.log | 55cdd683553d62c62ee8c9edceaa292c7d66564b1cd4df5b11ecf098ed6b8479
D:\study\programming\ESKIN\E-SKIN\docs\Final\data scalability\data\DELTA\Zero_load\N=3\M1_M2_M3\Repeat_1\summary.json | D:\study\programming\ESKIN\E-SKIN\docs\Final\data scalability\history\pre_variable_spi_20260906\data\DELTA\Zero_load\N=3\M1_M2_M3\Repeat_1\summary.json | d4a299a0e68296aeb130fee1f04fdcb50cabef1987a04b625f668684bf6c72fc
D:\study\programming\ESKIN\E-SKIN\docs\Final\data scalability\data\DELTA\Zero_load\N=3\M1_M2_M3\Repeat_2\experiment_log.md | D:\study\programming\ESKIN\E-SKIN\docs\Final\data scalability\history\pre_variable_spi_20260906\data\DELTA\Zero_load\N=3\M1_M2_M3\Repeat_2\experiment_log.md | cfc51ef4d336dd9527f9b11ff83afcd61ba951b2c72c999df5d2ae4c022cf343
D:\study\programming\ESKIN\E-SKIN\docs\Final\data scalability\data\DELTA\Zero_load\N=3\M1_M2_M3\Repeat_2\mul1_length_over_time.png | D:\study\programming\ESKIN\E-SKIN\docs\Final\data scalability\history\pre_variable_spi_20260906\data\DELTA\Zero_load\N=3\M1_M2_M3\Repeat_2\mul1_length_over_time.png | 1d51e0ceea44a1fdf8c67e40be24cdfe61e7d4b5667091a21b185e71aa28150b
D:\study\programming\ESKIN\E-SKIN\docs\Final\data scalability\data\DELTA\Zero_load\N=3\M1_M2_M3\Repeat_2\mul1_raw.bin | D:\study\programming\ESKIN\E-SKIN\docs\Final\data scalability\history\pre_variable_spi_20260906\data\DELTA\Zero_load\N=3\M1_M2_M3\Repeat_2\mul1_raw.bin | 08e6ad6be4a83eeb92aad01a15199bae7a23a4817019f76659b1174f6e1308d1
D:\study\programming\ESKIN\E-SKIN\docs\Final\data scalability\data\DELTA\Zero_load\N=3\M1_M2_M3\Repeat_2\packet_log.csv | D:\study\programming\ESKIN\E-SKIN\docs\Final\data scalability\history\pre_variable_spi_20260906\data\DELTA\Zero_load\N=3\M1_M2_M3\Repeat_2\packet_log.csv | 02d5f689ca676161ef5b7c96b799668793c8d3cf1957b66a9ef1d5ca68e17404
D:\study\programming\ESKIN\E-SKIN\docs\Final\data scalability\data\DELTA\Zero_load\N=3\M1_M2_M3\Repeat_2\plot_generation.log | D:\study\programming\ESKIN\E-SKIN\docs\Final\data scalability\history\pre_variable_spi_20260906\data\DELTA\Zero_load\N=3\M1_M2_M3\Repeat_2\plot_generation.log | b315eafeb455d75e3f59458ae3ed4d3af76314461c365398076e217f50ae485a
D:\study\programming\ESKIN\E-SKIN\docs\Final\data scalability\data\DELTA\Zero_load\N=3\M1_M2_M3\Repeat_2\summary.json | D:\study\programming\ESKIN\E-SKIN\docs\Final\data scalability\history\pre_variable_spi_20260906\data\DELTA\Zero_load\N=3\M1_M2_M3\Repeat_2\summary.json | 52e86fe4254d3e2baa88eb69d8a0eb2a668087d3107484267eee4794ea1c3772
D:\study\programming\ESKIN\E-SKIN\docs\Final\data scalability\data\DELTA\Zero_load\N=3\M1_M2_M3\Repeat_3\experiment_log.md | D:\study\programming\ESKIN\E-SKIN\docs\Final\data scalability\history\pre_variable_spi_20260906\data\DELTA\Zero_load\N=3\M1_M2_M3\Repeat_3\experiment_log.md | da1d8907c03beedc84053a8e6da424e165fa5c2155ab8f1b3fb63ddefe0a7f85
D:\study\programming\ESKIN\E-SKIN\docs\Final\data scalability\data\DELTA\Zero_load\N=3\M1_M2_M3\Repeat_3\mul1_length_over_time.png | D:\study\programming\ESKIN\E-SKIN\docs\Final\data scalability\history\pre_variable_spi_20260906\data\DELTA\Zero_load\N=3\M1_M2_M3\Repeat_3\mul1_length_over_time.png | ff4ff5d4cfb47031fda2ee012b4c8c6245b0de374dfdd3c275f15dad1f403de6
D:\study\programming\ESKIN\E-SKIN\docs\Final\data scalability\data\DELTA\Zero_load\N=3\M1_M2_M3\Repeat_3\mul1_raw.bin | D:\study\programming\ESKIN\E-SKIN\docs\Final\data scalability\history\pre_variable_spi_20260906\data\DELTA\Zero_load\N=3\M1_M2_M3\Repeat_3\mul1_raw.bin | 07dd5b18fc6f2901b7d1f790afce81ad8559c9168d08eaabbd16e763636f5e88
D:\study\programming\ESKIN\E-SKIN\docs\Final\data scalability\data\DELTA\Zero_load\N=3\M1_M2_M3\Repeat_3\packet_log.csv | D:\study\programming\ESKIN\E-SKIN\docs\Final\data scalability\history\pre_variable_spi_20260906\data\DELTA\Zero_load\N=3\M1_M2_M3\Repeat_3\packet_log.csv | 59197d48641d7ef7a9687d47b443bb79321a70b24830a6d8e4af598c4f7770bf
D:\study\programming\ESKIN\E-SKIN\docs\Final\data scalability\data\DELTA\Zero_load\N=3\M1_M2_M3\Repeat_3\plot_generation.log | D:\study\programming\ESKIN\E-SKIN\docs\Final\data scalability\history\pre_variable_spi_20260906\data\DELTA\Zero_load\N=3\M1_M2_M3\Repeat_3\plot_generation.log | 38be80d5188aab0bbe5135672d197f06ec505d2d7059476722ed74d616200965
D:\study\programming\ESKIN\E-SKIN\docs\Final\data scalability\data\DELTA\Zero_load\N=3\M1_M2_M3\Repeat_3\summary.json | D:\study\programming\ESKIN\E-SKIN\docs\Final\data scalability\history\pre_variable_spi_20260906\data\DELTA\Zero_load\N=3\M1_M2_M3\Repeat_3\summary.json | f379ebccbee54eb907b6e7d9b99f9238e8c0d8a3d71e2772f8b65c8ec0a156c5
D:\study\programming\ESKIN\E-SKIN\docs\Final\data scalability\data\DELTA\Zero_load\N=3\M1_M2_M3\Repeat_4\experiment_log.md | D:\study\programming\ESKIN\E-SKIN\docs\Final\data scalability\history\pre_variable_spi_20260906\data\DELTA\Zero_load\N=3\M1_M2_M3\Repeat_4\experiment_log.md | 1df31aaeedf9f25b41a325b0d275a6f0e312e82399742ca9717cda6032998449
D:\study\programming\ESKIN\E-SKIN\docs\Final\data scalability\data\DELTA\Zero_load\N=3\M1_M2_M3\Repeat_4\mul1_length_over_time.png | D:\study\programming\ESKIN\E-SKIN\docs\Final\data scalability\history\pre_variable_spi_20260906\data\DELTA\Zero_load\N=3\M1_M2_M3\Repeat_4\mul1_length_over_time.png | 94546247d6fb8939bfbbec2e6eac90fbd5a8e3a4fe651b747aa5208faf4bef9d
D:\study\programming\ESKIN\E-SKIN\docs\Final\data scalability\data\DELTA\Zero_load\N=3\M1_M2_M3\Repeat_4\mul1_raw.bin | D:\study\programming\ESKIN\E-SKIN\docs\Final\data scalability\history\pre_variable_spi_20260906\data\DELTA\Zero_load\N=3\M1_M2_M3\Repeat_4\mul1_raw.bin | dc8ce35a1656203e3b0175ca128fe290d62b4cfe7effb0b14681be2217aa35a0
D:\study\programming\ESKIN\E-SKIN\docs\Final\data scalability\data\DELTA\Zero_load\N=3\M1_M2_M3\Repeat_4\packet_log.csv | D:\study\programming\ESKIN\E-SKIN\docs\Final\data scalability\history\pre_variable_spi_20260906\data\DELTA\Zero_load\N=3\M1_M2_M3\Repeat_4\packet_log.csv | a7a6261c565be5ce1750ac76296e9df17adbbceeaf72fd8e3875379d675007a4
D:\study\programming\ESKIN\E-SKIN\docs\Final\data scalability\data\DELTA\Zero_load\N=3\M1_M2_M3\Repeat_4\plot_generation.log | D:\study\programming\ESKIN\E-SKIN\docs\Final\data scalability\history\pre_variable_spi_20260906\data\DELTA\Zero_load\N=3\M1_M2_M3\Repeat_4\plot_generation.log | 68d0ff1fa7377678d18d88597349361d8a0b288af9d9735c95c1fa6d129b6ec1
D:\study\programming\ESKIN\E-SKIN\docs\Final\data scalability\data\DELTA\Zero_load\N=3\M1_M2_M3\Repeat_4\summary.json | D:\study\programming\ESKIN\E-SKIN\docs\Final\data scalability\history\pre_variable_spi_20260906\data\DELTA\Zero_load\N=3\M1_M2_M3\Repeat_4\summary.json | a9ad5b5f88f3d0f2f94bf071ff06394b65adc192e13c1572b0183257ef070755
D:\study\programming\ESKIN\E-SKIN\docs\Final\data scalability\data\DELTA\Zero_load\N=4\M0_M1_M2_M3\R1\experiment_log.md | D:\study\programming\ESKIN\E-SKIN\docs\Final\data scalability\history\pre_variable_spi_20260906\data\DELTA\Zero_load\N=4\M0_M1_M2_M3\R1\experiment_log.md | 2d0e2d33de57b3adedf69b0a0c3e8609f322ee766ca6af4cdbac4d6707e4ca41
D:\study\programming\ESKIN\E-SKIN\docs\Final\data scalability\data\DELTA\Zero_load\N=4\M0_M1_M2_M3\R1\mul1_length_over_time.png | D:\study\programming\ESKIN\E-SKIN\docs\Final\data scalability\history\pre_variable_spi_20260906\data\DELTA\Zero_load\N=4\M0_M1_M2_M3\R1\mul1_length_over_time.png | 24aac65fead0bcc7bdf933ee048c26a184400a1513b4b993f6289c4f88070787
D:\study\programming\ESKIN\E-SKIN\docs\Final\data scalability\data\DELTA\Zero_load\N=4\M0_M1_M2_M3\R1\mul1_raw.bin | D:\study\programming\ESKIN\E-SKIN\docs\Final\data scalability\history\pre_variable_spi_20260906\data\DELTA\Zero_load\N=4\M0_M1_M2_M3\R1\mul1_raw.bin | 410d63d67576cbd38d0b2dad7a6b08be19da0f7234cbc8bfc2f918ae4276656b
D:\study\programming\ESKIN\E-SKIN\docs\Final\data scalability\data\DELTA\Zero_load\N=4\M0_M1_M2_M3\R1\packet_log.csv | D:\study\programming\ESKIN\E-SKIN\docs\Final\data scalability\history\pre_variable_spi_20260906\data\DELTA\Zero_load\N=4\M0_M1_M2_M3\R1\packet_log.csv | 0dd624e5d788190e5e3103bfe2684cca033e4e876155cc0a9142981ac9dfec65
D:\study\programming\ESKIN\E-SKIN\docs\Final\data scalability\data\DELTA\Zero_load\N=4\M0_M1_M2_M3\R1\plot_generation.log | D:\study\programming\ESKIN\E-SKIN\docs\Final\data scalability\history\pre_variable_spi_20260906\data\DELTA\Zero_load\N=4\M0_M1_M2_M3\R1\plot_generation.log | b89a73a6f27389d3c0dc8c726b16746644adb137a8a1423010a088598ee097e8
D:\study\programming\ESKIN\E-SKIN\docs\Final\data scalability\data\DELTA\Zero_load\N=4\M0_M1_M2_M3\R1\summary.json | D:\study\programming\ESKIN\E-SKIN\docs\Final\data scalability\history\pre_variable_spi_20260906\data\DELTA\Zero_load\N=4\M0_M1_M2_M3\R1\summary.json | 10170617ac72a33cc413899cacc697f922738b7413fbcdbab34bc16778a4d66b
D:\study\programming\ESKIN\E-SKIN\docs\Final\data scalability\data\DELTA\Zero_load\N=4\M0_M1_M2_M3\R2\experiment_log.md | D:\study\programming\ESKIN\E-SKIN\docs\Final\data scalability\history\pre_variable_spi_20260906\data\DELTA\Zero_load\N=4\M0_M1_M2_M3\R2\experiment_log.md | b6f85cac3f42cf7815027e863bfc9e8bb302ab87e85fbc32c550da14049c69ba
D:\study\programming\ESKIN\E-SKIN\docs\Final\data scalability\data\DELTA\Zero_load\N=4\M0_M1_M2_M3\R2\mul1_length_over_time.png | D:\study\programming\ESKIN\E-SKIN\docs\Final\data scalability\history\pre_variable_spi_20260906\data\DELTA\Zero_load\N=4\M0_M1_M2_M3\R2\mul1_length_over_time.png | 728225f0e3df5f2ae527a60389b2ad317968dfc54e8bf8dd06266ab7c4470641
D:\study\programming\ESKIN\E-SKIN\docs\Final\data scalability\data\DELTA\Zero_load\N=4\M0_M1_M2_M3\R2\mul1_raw.bin | D:\study\programming\ESKIN\E-SKIN\docs\Final\data scalability\history\pre_variable_spi_20260906\data\DELTA\Zero_load\N=4\M0_M1_M2_M3\R2\mul1_raw.bin | 4537143f153760bfc57b16e7f164ab3ad62f67ed5276c97c6f1dc80b70b0a6af
D:\study\programming\ESKIN\E-SKIN\docs\Final\data scalability\data\DELTA\Zero_load\N=4\M0_M1_M2_M3\R2\packet_log.csv | D:\study\programming\ESKIN\E-SKIN\docs\Final\data scalability\history\pre_variable_spi_20260906\data\DELTA\Zero_load\N=4\M0_M1_M2_M3\R2\packet_log.csv | eaf80b4e3f0837f575b434132c774865cf868729d78d6c3d5a0944484622208e
D:\study\programming\ESKIN\E-SKIN\docs\Final\data scalability\data\DELTA\Zero_load\N=4\M0_M1_M2_M3\R2\plot_generation.log | D:\study\programming\ESKIN\E-SKIN\docs\Final\data scalability\history\pre_variable_spi_20260906\data\DELTA\Zero_load\N=4\M0_M1_M2_M3\R2\plot_generation.log | 06b4afb1034d47884b625cffb118d82c79f9df0b17fe478190982ae17a376f79
D:\study\programming\ESKIN\E-SKIN\docs\Final\data scalability\data\DELTA\Zero_load\N=4\M0_M1_M2_M3\R2\summary.json | D:\study\programming\ESKIN\E-SKIN\docs\Final\data scalability\history\pre_variable_spi_20260906\data\DELTA\Zero_load\N=4\M0_M1_M2_M3\R2\summary.json | a218a06a81852263915699ca17f05646b620a83f5e4e72725a85b09452aca6c8
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
