Yannas-Sun/E-skin_MSc_final_report/data scalability/analysis/20260907_final_data_review/history/superseded_111_102_20260913/evidence_review.md

# Data 实验证据复核：完成范围、论文结论与限制

本复核只读取现有索引、已完成的独立审计和逐段统计，没有重扫 raw、修改原数据、索引或论文。统计输入按固定 run_id 筛选；部分 statistics.csv 含历史或其他加载场景对照，不能仅用 scope=main 汇总整份文件。输入路径及哈希、完整数值保存在 [evidence_review.json](evidence_review.json)。

**FULL 与 DELTA 的零负载 N=1～4 主矩阵已经完成，分别覆盖四槽位的全部 15 种非空组合。可以将这套零负载图表写为本轮新版固件实测结果。动态结果需要按实际场景分别表述：独立通过的完整新增批次为 N=1 三类加载与 N=2 同时大面积加载，共 12 条；N=4 的独立审计已经完成，结果为 1 PASS、2 CHECK，整个批次作为诊断保留。**

## 1. 已完成的范围

|类别|已采记录|目前可明确采用的结果|统计单位|
|---|---:|---|---|
|FULL 零载|48|45 条完整主矩阵；全部历史保留|15 组合，每组合一个完整批次、3 个时间窗口|
|DELTA 零载|45|45 条全部通过独立主窗口审计|15 组合，每组合一个批次、3 个时间窗口|
|最早 M1 大面积动态|3|诊断记录；全部独立 CHECK|12 次内序号回退至 2、2 次前跳，不进入无异常动态统计|
|后续 M1 大面积动态|3|主窗口独立 PASS|同一设置的 3 个时间窗口|
|M1 大面积反复按压/释放|3|主窗口独立 PASS；与上一行分别报告|同一设置的 3 个时间窗口|
|M1 rolling|3|主窗口独立 PASS|同一设置的 3 个时间窗口|
|N=2，M1＋M3 同时大面积覆盖|3|主窗口独立 PASS|同一设置的 3 个时间窗口|
|N=4，四模块同时全覆盖|3|独立审计完成：R1 PASS、R2/R3 CHECK；整个批次保留为诊断|不能将整个批次称为 n=3 无异常结果|
|固定证据快照合计|111|零载主矩阵 90 条＋完整 PASS 动态批次 12 条＝分析选择 102 条|不将不同场景合并为同一重复组|

FULL 的 48 条中，原主窗口为 **47 PASS、1 CHECK**。被完整补测批次替换的原 M0＋M1＋M2 批次共三条，其中仅一条失败，另外两条 PASS 是合格补充记录；“未选入 primary”不等于“失败”。主矩阵整体采用补测批次，避免按帧率挑选单次记录。旧失败仍保留用于可靠性和故障讨论。

后续 15 条动态记录的原 metadata 误填 zero_load，应使用各次用户确认的条件纠正说明分类，原始标签保持作为来源。它们不能因为原标签是 zero_load 而进入已经完成的零载矩阵。全部 111 条记录保留；分析选择以完整批次为单位，不单独把 N=4 的 R1 纳入无异常动态结果。

N=4 的 R2 和 R3 各有一次外层序号缺口，各缺 4 个序号值，并且各有 7 次模块内序号前跳事件。R2 另有一个 CRC 有效的 40 B MUL1，四个目标模块均未更新，共缺 4 次预期更新。两段的 CRC、已观测 DELTA base 链及建立锚点后未能应用的 ESKD 计数均为 0；这说明收到的数据能通过校验和继续重建，并不能抵消已经观察到的传输间断。序号事件数量不能直接换算为物理扫描丢失数量，具体故障原因尚未确定。

## 2. 零载 N=1～4 主结果

下表均值以各组合等权计算，每组合恰有三段，因此数值也等于该 N 的全部主矩阵时间窗口均值。这里的 SD 是 **跨时间窗口的样本 SD，包含组合间差异和同一组合内时间波动**，不是扫描帧之间的 SD，也不是独立装配不确定度。JSON 另存组合间均值的 SD；N=4 只有一个组合，其组合间 SD 不可估计。

|N|组合数|每模式时间窗口 n|FULL 包长 B|FULL USB Mbit/s，均值 ± SD|DELTA 平均包长 B，均值 ± SD|DELTA USB Mbit/s，均值 ± SD|
|---:|---:|---:|---:|---:|---:|---:|
|1|4|12|1084|1.736573 ± 0.001025|145.237425 ± 16.496510|0.232562 ± 0.026405|
|2|6|18|2128|3.407991 ± 0.001895|251.981573 ± 16.360553|0.403900 ± 0.025933|
|3|4|12|3172|5.076696 ± 0.007657|360.740241 ± 24.153549|0.577646 ± 0.038721|
|4|1|3|4216|6.747828 ± 0.001148|475.147794 ± 5.719526|0.762543 ± 0.012375|

|N|FULL PC 完成包率 Hz，均值 ± SD|DELTA PC 完成包率 Hz，均值 ± SD|DELTA 普通内帧 K，均值 ± SD|同包率 USB 字节减少比例|
|---:|---:|---:|---:|---:|
|1|200.250620 ± 0.118177|200.157930 ± 0.277828|8.255808 ± 8.289100|86.6017%|
|2|200.187469 ± 0.111305|200.372639 ± 0.945787|8.641245 ± 4.106754|88.1588%|
|3|200.058965 ± 0.301737|200.159127 ± 0.053074|9.102066 ± 4.045633|88.6274%|
|4|200.066062 ± 0.034040|200.600197 ± 0.845397|10.044483 ± 0.717198|88.7299%|

K 的这一层 SD 为逐段 K 均值之间的变化，不是段内单帧 K 分布的 SD。各个组合自己的均值 ± SD、n=3、batch_n=1 应优先用于比较同一组合的重复性；跨 N 总表只是描述汇总。同一批实体模块在不同组合中重复出现，各组合也不能当作相互独立的板卡样本。

FULL 包长满足 `(24+4M)+1044N`，当前 M=4，因此四种 N 的合法完整包长固定。DELTA 包长和流量已经包含观测到的全部 ESKF。上述减少比例按 `1 − mean(L_DELTA)/L_FULL` 计算，为相同实际包率的字节比较，不是以两个实验各自流量的比值代替字节模型核验。

USB 指标是完整有效 MUL1 字节在 PC 完成窗口内的速率，不包含 USB 物理事务全部开销。实际包率略高于或低于目标 200 Hz，不自动等于物理扫描频率变化或丢帧；PC 接收批处理也会改变固定窗口计数。

## 3. 已通过的动态结果

下表均采用固定约 10–40 s 主窗口，含窗口内静息和加载阶段，并计入 ESKF。每行 n=3、batch_n=1，SD 为三个连续时间窗口之间的样本 SD，不能把各行混合成一个更大的同条件重复组。

|实际场景|模块|平均 MUL1 B|USB Mbit/s，均值 ± SD|普通 ESKD 平均 K|ESKF 总比例均值|同包率字节节省|
|---|---|---:|---:|---:|---:|---:|
|后续大面积动态|M1|282.4190|0.452052 ± 0.007582|76.8350|0.58859%|73.95%|
|反复按压、释放|M1|210.6374|0.337729 ± 0.016879|41.1050|0.50446%|80.57%|
|Rolling|M1|357.7184|0.573369 ± 0.017977|115.0377|0.49909%|67.00%|
|同时大面积覆盖|M1＋M3|510.9032|0.815880 ± 0.017786|73.0537|0.65672%|75.99%|

完整包长、K、q 的段间 SD 和固定 run_id 见 JSON。N=2 的 K 为各 run 普通模块内帧合并后的均值；每模块 K 和 q 应另外报告，不能把这一数值当成两个模块具有完全相同的活动量。

这些结果支持：DELTA 的实际成本取决于普通变化单元数量的分布、活动持续时间以及 ESKF 占比。Rolling 的普通 K 峰值可以低于按压/释放，但平均 K 和平均流量更高，故不能只用峰值说明压缩效果。跨场景外部力、面积、节奏和活动比例未严格量化，不能把差异解释成算法版本改进或退化。

N=2 主窗口共有 236 个 ESKF 内帧，但只有 232 个包含任意 ESKF 的外层 MUL1，其中 4 个含两模块同时 ESKF。内帧比例与外包比例分母不同；不能把所有含 ESKF 的包都按“两模块 FULL”计费。正确模型按每模块类型和 K 求和。

## 4. 可以用于论文的结论

1. **新版固件零载 N=1～4 的完整实测矩阵已经成立。** 可以替换旧固件的对应 FULL/DELTA 零载图、表及统计，明确每组合的三次时间重复和所测四个槽位范围。
2. **FULL 每包字节数模型和包含 ESKF 的 DELTA 平均字节模型有逐包审计证据。** 比较时用实际包长和实际包率，避免把目标帧率与实测帧率的差异叫作字节模型误差。
3. **零载下 DELTA 的有效 USB 字节量相对同 N FULL 约减少 86.6%–88.7%。** 该范围限定于本批输入条件、阈值和包结构，不作为所有动态负载的固定压缩率。
4. **N=1 多种动态场景及 N=2 同时加载已有完整三段 PASS 证据。** 可以报告各场景 K、q、包长和实际流量，说明同步完整帧并不必然伴随传输异常；N=4 的混合资格批次另外报告诊断结果。
5. **可靠性表述应限于明确审计通过的窗口。** 可写“在所列主窗口内未发现相应 CRC、内外序号、DELTA base 链或目标模块更新异常”；不能写“系统绝不丢帧”或“所有实验均无错误”。

这里的“新版固件实测”指本轮新固件采集流程及其记录来源；本地文件哈希、10 MHz 配置字段和通信槽位编号不是设备 flash 回读、SCK 波形或实体板卡唯一身份。应在方法或限制中说明，而不是将其误列为新的硬件验证。

## 5. 仍需如实交代的问题

- **故障原因未解决。** 最早 M1 大面积批次 12 次序号回退至 2、两次前跳仍是诊断事实。后续同类 PASS 表示没有再次观察到，不等于故障已永久消除。N=4 独立审计进一步确认 R2/R3 的内外序号间断及 R2 的四模块缺更新；这些是已完成的异常检查结果，具体软硬件根因仍待定位。
- **固定 K 扩展仍是条件假设。** 零载 K 均值随 N 从约 8.26 增至 10.04，组合及模块差异仍存在；动态“同时加载”也不意味着每模块载荷或 K 完全相同。理论固定 K 图可保留为受控假设下的外推，不能写成所有实测场景遵循同一个 K。
- **ESKF 原因没有逐帧编码。** 可以统计总 q 和时间分布，可以描述约一秒的节奏或密集事件；通常不能唯一拆分定时、高 K 回退、手动和故障恢复比例。普通 ESKD 的最大 K 也不能反推出 ESKF 当时的变化数量。
- **物理扫描丢失与 SPI 时钟尚不能靠 USB 日志证明。** CRC、模块序号、base 和缺更新检查各有范围；PC 时间与 Teensy 入队时间都不是直接扫描产生计数或逻辑分析仪时钟计数。40 MHz 容量数字仍是理论；日志中的 10 MHz 来源是配置，不能在本次总结中新增“已测波形”的说法。
- **重复层级与输入描述有限。** 三连录提供时间重复；独立装配、精确力、面积、加载层、动作节奏和唯一板卡身份仍不完整。误填 zero_load 的动态条件应使用确认记录追溯，不能更改原始测量文件来掩盖标签来源。

## 6. 缺少的场景如何处理

已审计的新固件快照中没有单独的小面积动态批次，也没有 N=3 动态批次。N=4 动态三段已审计，整个批次保留为诊断而不进入完整 PASS 动态统计。因此：

- 若论文主扩展结果使用已经完成的零载 N=1～4，动态部分展示 N=1 场景差异及已通过的多模块实例，**现有数据足以编写限定范围的报告，不需要把所有未做实验设为交稿阻塞条件**。
- 若保留“新固件小面积对大面积”的实测比较，需要小面积新数据，或者删去/明确隔离旧固件的小面积结果。
- 若图名声称“动态 N=1～4 全部实测”，必须有对应 N=3 实测点，并准确处理 N=4 的失败与可用子集；不能插值后称为实测。也可改成已测 N 的离散比较，主动缩小声明范围。
- 若要新增“变量 SPI 确实减少了线路时钟数”“40 MHz 已验证”“受控失帧恢复耗时”等更强声明，需要相应专门证据；不提出这些声明时，将未验证范围写入限制即可。

Power 与 Calibration 不在本次 Data 重测范围，不需要为本总结重做。最终分类和总索引正在由主代理汇总；本复核不将旧的 96 条索引误当作当前 111 条固定快照的完整清单。

主要依据：[FULL 主矩阵](../../data/FULL/primary_matrix.csv)、[DELTA 零载统计](../20260907_delta_zero_review/stats_by_n_balanced.csv)、[大面积补测审查](../20260907_delta_followup_review/REVIEW_CN.md)、[按压/释放审查](../20260907_delta_press_release_review/REVIEW_CN.md)、[Rolling 审查](../20260907_delta_rolling_review/REVIEW_CN.md)、[N=2 同时加载审查](../20260907_n2_large_area_review/REVIEW_CN.md)、[最早动态异常审查](../20260907_delta_large_area_review/raw_audit_CN.md)、[N=4 独立审计](../20260907_n4_full_coverage_review/raw_audit.md)、[N=4 资格判定](../20260907_n4_full_coverage_review/qualification.json)。
