Yannas-Sun/E-skin_MSc_final_report/data scalability/analysis/20260907_final_data_review/history/superseded_111_102_20260913/FINAL_SUMMARY_CN.md

# Data 最终实验总结与分类记录（2026-09-07）

**本轮数据已全部整理：111条记录，未分类时间戳目录为0。新版固件FULL与DELTA零载N=1～4主矩阵完整；最后N=4同时全覆盖动态批次有两段异常，需要在报告中如实保留。**

## 完成范围与统计资格

| 类别 | 全部记录 | 主窗符合现有完整性检查 | CHECK | 完整批次入选记录 |
|---|---:|---:|---:|---:|
| FULL零载 | 48 | 47 | 1 | 45 |
| DELTA零载 | 45 | 45 | 0 | 45 |
| DELTA动态 | 18 | 13 | 5 | 12 |
| 合计 | 111 | 105 | 6 | 102 |

以上均指主窗口，不把原始全程CHECK改为PASS，也不把105/111当作独立试验的总体可靠性估计。FULL原M012批次三条被完整补测批次替换，其中仅一条CHECK，另外两条PASS保留为补充。动态13条主窗PASS中，N4 R1只有单段通过，未凑入完整三次重复的性能子集。

零载每种模式均为15个模块组合×3个连续窗口，共45条。n=3是同一设置下的时间重复，未建立三次独立装配。正式零载primary_matrix.csv仍为90条；dynamic_analysis_selected.csv另列12条；analysis_selected.csv合并这两种明确筛选口径为102条，使用时仍须按模式、条件和批次筛选。

## 最后一批 N=4：一段通过，两段有记录缺口

用户确认M0、M1、M2、M3同时全覆盖按下，模式仍是DELTA。三段各40 s，主分析窗口固定为10–40 s。原文件中zero_load标签保留为来源，派生条件改记large_area / full_coverage_all_modules。没有按错误时段或帧率剪裁记录。

| Repeat | 独立主窗 | 包率 / Hz | 平均包长 / B | 有效USB / Mbit/s | 外层缺号 | 内序号事件 | 已收到包内缺模块更新 |
|---:|---|---:|---:|---:|---:|---:|---:|
| 1 | PASS | 199.243 | 1619.42 | 2.581268 | 0 | 0 | 0 |
| 2 | CHECK REQUIRED | 195.050 | 1674.13 | 2.612307 | 4 | 7 | 4 |
| 3 | CHECK REQUIRED | 195.955 | 1729.55 | 2.711311 | 4 | 7 | 0 |

R2在22.7522755 s出现760731→760736的外层缺号，桥端相邻包间隔522 ms；该760736包为40 B，CRC有效，但四槽均没有有效更新。22.8446298 s四槽有效ESKF到达；其模块内序号前跳，之后M0～M2又各发生一次前跳。R3在16.7725519 s出现767419→767424、桥端453 ms间隔和四槽ESKF前跳，之后M0～M2再次前跳。两段各7次内序号事件，共14次；外层共有8个未观测编号。

全部已解析候选的内外CRC、布局、K和base链检查正常；有效ESKF后建立了基线，随后收到的ESKD可应用，锚点后未应用ESKD为0。**这些事实不能填补未观测编号，不能说“只因PC缓冲、系统没有丢帧”，也不能确定是ESKF、高K或SCK导致。** 外层与模块内的编号缺口分别报告，不能直接相加为物理扫描丢失数。

三段全部保留的诊断均值±样本SD：包率196.749261±2.206474 Hz，包长1674.366648±55.065612 B，有效USB 2.634962±0.067917 Mbit/s，普通内帧K=160.576658±6.811278，ESKF内帧比例0.542338%±0.034258个百分点。相同已观测包率下，相对4216 B FULL的字节减少约60.29%；因为该组含缺号和空更新包，此数值不能当作无损压缩性能结论。

只有R1主窗口独立通过，n=1无法计算段间SD。R1仍可作为明确标注的单段实例；整个N4批次作为诊断资料保留，不加入完整三次通过的动态性能子集。全程的初始1308个无锚点ESKD和尾片1/1/1 B与主窗内部事件分开记录。

[N4独立审计](../20260907_n4_full_coverage_review/raw_audit.md) / [逐模块统计及字节模型](../20260907_n4_full_coverage_review/statistics.md)。

## N=1～4 零载主结果

| N | 组合数 | 每模式时间窗 n | FULL 有效USB / Mbit/s | DELTA零载有效USB / Mbit/s |
|---:|---:|---:|---:|---:|
| 1 | 4 | 12 | 1.736573 ± 0.001025 | 0.232562 ± 0.026405 |
| 2 | 6 | 18 | 3.407991 ± 0.001895 | 0.403900 ± 0.025933 |
| 3 | 4 | 12 | 5.076696 ± 0.007657 | 0.577646 ± 0.038721 |
| 4 | 1 | 3 | 6.747828 ± 0.001148 | 0.762543 ± 0.012375 |

各组合等权，每组合恰有三段。表中SD为同N下各时间窗口均值的样本SD，包含组合间差异及时间波动；并非独立板卡或装配的不确定度。每个具体组合的n=3统计仍保存在原group_statistics.csv。

FULL包长为1084/2128/3172/4216 B；DELTA零载平均包长约145.24/251.98/360.74/475.15 B。按相同实际包率比较，DELTA有效包字节减少约86.60%～88.73%，已经包含ESKF成本。USB指标是完整有效MUL1的字节速率，不含USB物理事务全部开销。

## 各动态场景

| 动态场景 | 记录 n | 主窗 PASS / CHECK | 平均包长 / B | 有效USB / Mbit/s |
|---|---:|---:|---:|---:|
| 最早M1大面积批次（诊断） | 3 | 0 / 3 | 272.23 ± 11.24 | 0.433820 ± 0.019034 |
| M1大面积后续批次 | 3 | 3 / 0 | 282.42 ± 4.74 | 0.452052 ± 0.007582 |
| M1大面积反复按压/释放 | 3 | 3 / 0 | 210.64 ± 10.57 | 0.337729 ± 0.016879 |
| M1 Rolling | 3 | 3 / 0 | 357.72 ± 11.18 | 0.573369 ± 0.017977 |
| M1＋M3同时大面积覆盖 | 3 | 3 / 0 | 510.90 ± 11.14 | 0.815880 ± 0.017786 |
| M0～M3同时全覆盖（诊断） | 3 | 1 / 2 | 1674.37 ± 55.07 | 2.634962 ± 0.067917 |

每行保留一个实际三连录批次，均值±样本SD跨三个主窗口计算。含CHECK的行是诊断统计；后续PASS不覆盖最早的失败记录，不将不同动作合并成同一个重复组。同时加载不代表各模块受力、覆盖面积或K相等。

四个完整通过批次的同包率字节减少分别为73.95%、80.57%、67.00%、75.99%。Rolling平均K和流量较高，说明压缩效果还取决于活动持续时间，不能仅看一次峰值。N2两模块均出现合法K=480，且额外密集ESKF期间仍通过检查，故“大量变化或出现ESKF必然产生错误”不受数据支持。

## 协议模型如何使用这些数据

当前M=4是最大槽位数，N是实际模块数，固定外层开销24+4M=40 B。每个普通模块ESKD为84+2K B，ESKF为1044 B，等长交点K=480与N无关。对实际已观测包逐帧求和：

`B = 40P + 84n_D + 2ΣK_D + 1044n_F`（本批无额外诊断payload）。

该字节账包含全部ESKF；对N4 R2的40 B无更新包，内帧数为0，不能按正常四模块K=0包376 B计费。平均模型应逐模块用有效更新覆盖率c_m、其ESKF比例q_m和普通帧K：

`L_mean = 40 + Σ_m c_m[(1-q_m)(84+2K_mean,D,m) + 1044q_m]`。

q_m分母为该模块有效内帧数；含任一ESKF的外包比例另有分母，不能互换。没有原因编码的ESKF，不能精确分拆为定时、高K回退、手动或故障恢复。更新覆盖率只覆盖已观测包中的模块更新，不能隐藏外层缺号。

零载K跨N均值约8.26、8.64、9.10、10.04；固定K外推仍是条件假设。字节模型与吞吐比较应分开使用实测包长和实测包率；不能把目标200 Hz与实测完成包率的差异称作逐帧字节模型误差。

## 分类及原始数据保护

本次搬迁15条、140个已有文件，共144,509,120 B，其中90个为六类原始测量文件。搬迁前后所有文件SHA-256一致，现有图也随目录保留。原始summary、记录状态、错误证据、run_id、batch_id、Repeat及嵌入旧路径不改写。根path_map.csv现有666条原始测量文件映射；根和DELTA层derived_path_map.csv仅记录本轮15条的50个派生文件，不是全部历史绘图清单。

新增记录目的地均在DELTA/Dynamic_load下：

| 批次 | 相对路径 |
|---|---|
| M1大面积后续三条 | N=1/200Hz/M1/Large_area/Batch_20260907_050453_154588/Repeat_1～3 |
| M1反复按压/释放 | N=1/200Hz/M1/Large_area_press_release/Repeat_1～3 |
| M1 Rolling | N=1/200Hz/M1/Rolling/Repeat_1～3 |
| N2同时大面积覆盖 | N=2/200Hz/M1_M3/Large_area_simultaneous/Repeat_1～3 |
| N4同时全覆盖 | N=4/200Hz/M0_M1_M2_M3/Full_coverage_all_modules/Repeat_1～3 |

最早M1大面积CHECK三条仍留在Large_area/Repeat_1～3，与后续批次分开。旧固件history/pre_variable_spi_20260906未动。FULL与DELTA零载专用视图和原90条主矩阵哈希不变；旧96条总索引的已有字段原值保留。分类前的catalog已备份到本目录before_catalog。

原审计报告与脚本描述的是分类前的固定快照，因此其中时间戳路径属于来源证据。当前路径用run_index.csv或path_map.csv解析；支持from-snapshot的统计脚本可从派生快照复现。不要直接运行旧分类快照去覆盖当前111条索引。

## 论文可更新项与保留限制

- [x] FULL、DELTA零载N=1～4全部组合的新固件数据已齐，每组合三段重复。
- [x] 动态场景标签已按用户确认分类，未混入零载统计。
- [x] 各批次均值、样本SD、n及重复层级已记录；异常和补测批次保留。
- [x] 实际包长、实际完成包率、有效USB流量、普通K及全部ESKF分别统计。
- [x] 新增动态已检查跨ESKF的模块序号、CRC、base链和目标更新，失败批次独立列出。
- [ ] N4动态尚未获得完整三段无错误结果，异常机制仍未定位；如保留“四模块动态无错”声明，需要针对性排查后补测整批，不需要因此重做已通过的零载矩阵。
- [ ] 新固件没有N3动态或单独小面积动态记录；对应图只能展示已测场景，或明确区分历史数据，不能补点后称为实测。
- [ ] 定时与特殊ESKF原因的精确归类、物理丢扫数和线路SPI时钟波形未由本次USB日志证明。40 MHz仍为理论条件；本批日志的10 MHz字段为本地配置来源。
- [ ] K固定、各模块相同载荷、唯一板卡身份和独立装配重复不应写成已验证事实。

因此当前足以完成限定范围的Data章节：新版N=1～4零载扩展实测、已通过的动态案例，以及N4高活动输入下观察到的完整性限制。Power和Calibration不在本次重测范围。本文档是实验与数据总结，论文图表/PDF仍需按上述新索引更新。

[全部111条索引](../../data/run_index.csv) / [102条选定分析记录](../../data/analysis_selected.csv) / [所有动态批次诊断统计](../../data/dynamic_diagnostic_statistics.csv) / [搬迁核验](organization_verification.json) / [索引核验](catalog_validation.json) / [独立证据复核](evidence_review.md)。
