Yannas-Sun/E-skin_MSc_final_report/data scalability/history/pre_variable_spi_20260906/data/DELTA/Dynamic_load/M1/Small_area_3x1.6cm/Repeat_4/mul1_length_over_time.png

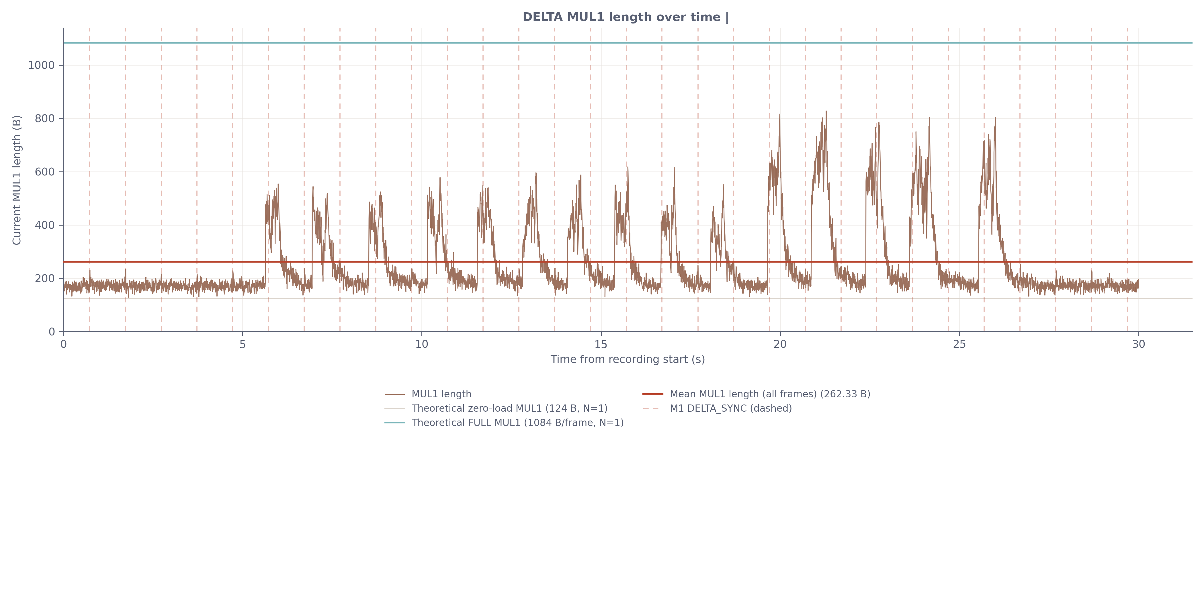
data scalability/history/pre_variable_spi_20260906/data/DELTA/Dynamic_load/M1/Small_area_3x1.6cm/Repeat_4/mul1_length_over_time.png
