Yannas-Sun/E-skin_MSc_final_report/data scalability/history/pre_variable_spi_20260906/data/DELTA/Dynamic_load/N=2/M1_M3/Full_coverage_all_FSR/Repeat_1/mul1_length_over_time.png

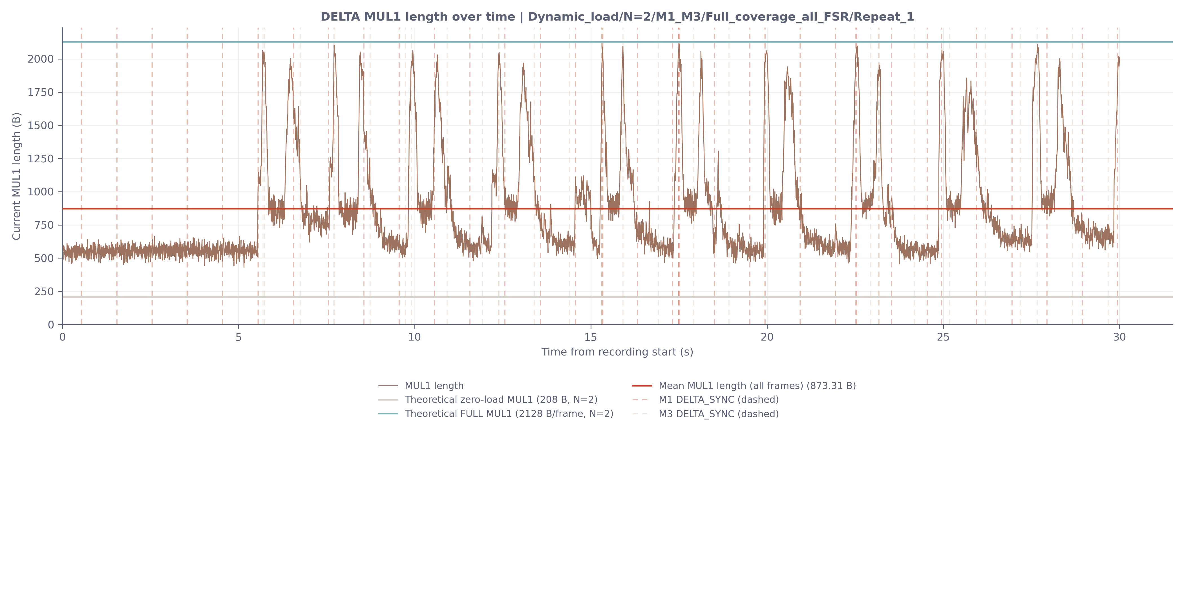
data scalability/history/pre_variable_spi_20260906/data/DELTA/Dynamic_load/N=2/M1_M3/Full_coverage_all_FSR/Repeat_1/mul1_length_over_time.png
