Yannas-Sun/E-skin_MSc_final_report/data scalability/history/pre_variable_spi_20260906/data/DELTA/Zero_load/N=1/M0/Repeat_6/mul1_length_over_time.png

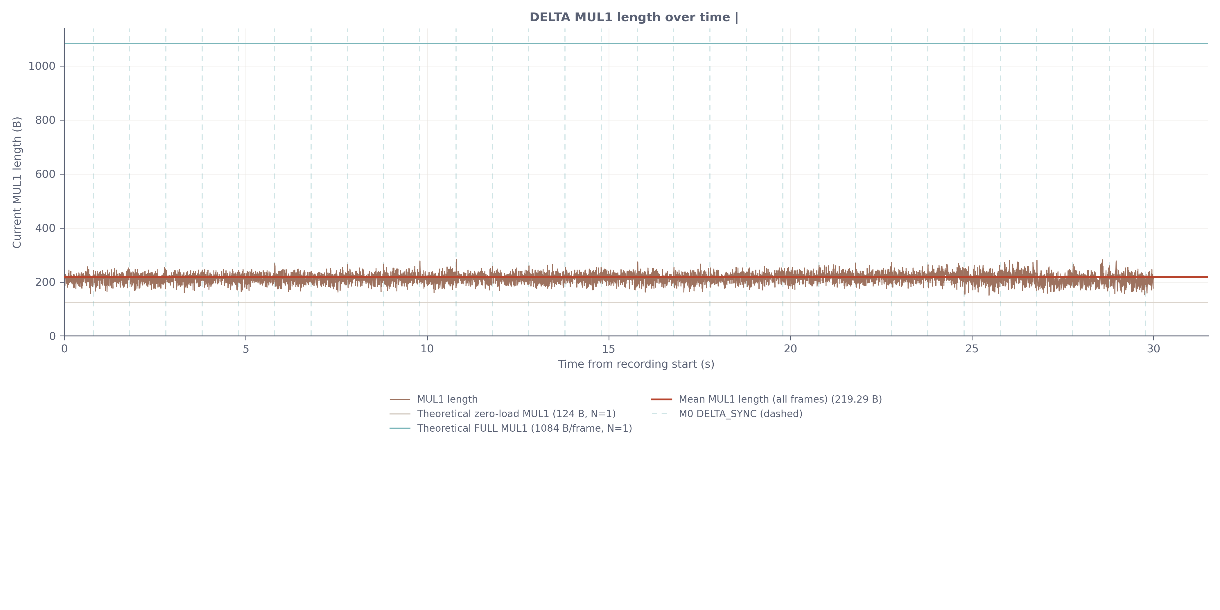
data scalability/history/pre_variable_spi_20260906/data/DELTA/Zero_load/N=1/M0/Repeat_6/mul1_length_over_time.png
