Yannas-Sun/E-skin_MSc_final_report/data scalability/history/pre_variable_spi_20260906/data/DELTA/Zero_load/N=3/M0_M1_M3/Repeat_2/mul1_length_over_time.png

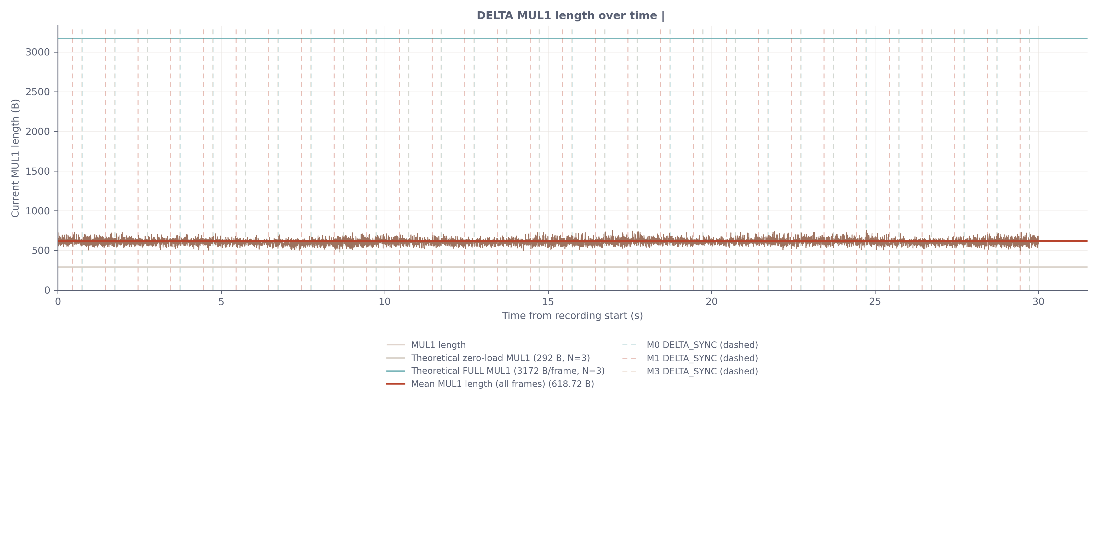
data scalability/history/pre_variable_spi_20260906/data/DELTA/Zero_load/N=3/M0_M1_M3/Repeat_2/mul1_length_over_time.png
