Yannas-Sun/E-skin_MSc_final_report/power scalability/DATA/analysis/current/report_v2_8_figures/current_power_scaling.pdf

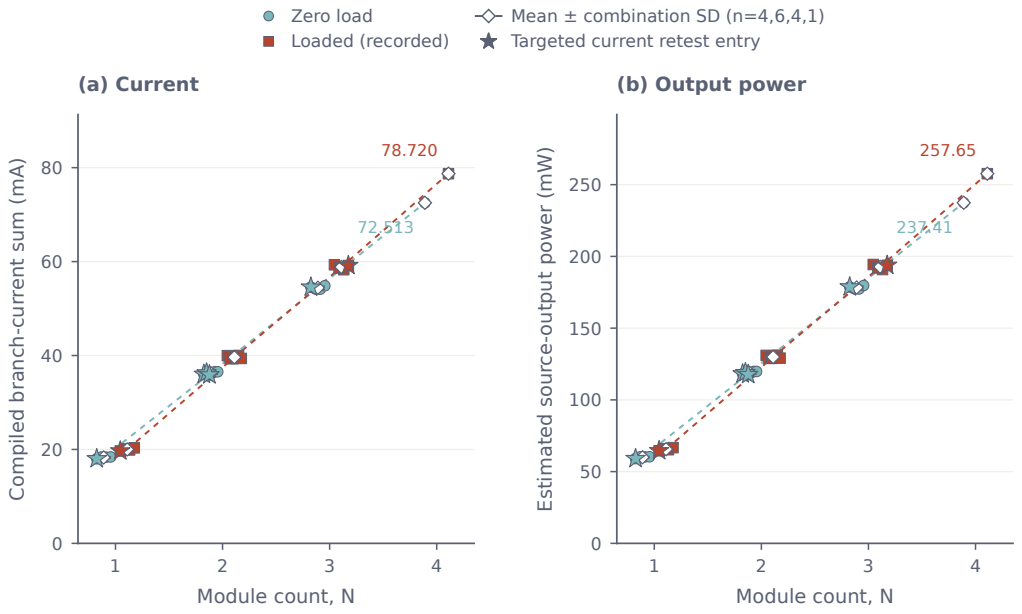
[picture p297: page 1]
Module count, N; (a) Current; (b) Output power; Zero load Loaded (recorded)

Mean ± combination SD (n=4,6,4,1)
Targeted current retest entry

Estimated source-output power (mW)

Compiled branch-current sum (mA)
