Yannas-Sun/E-skin_MSc_final_report/power scalability/DATA/analysis/current/report_v2_8_figures/voltage_scaling.pdf

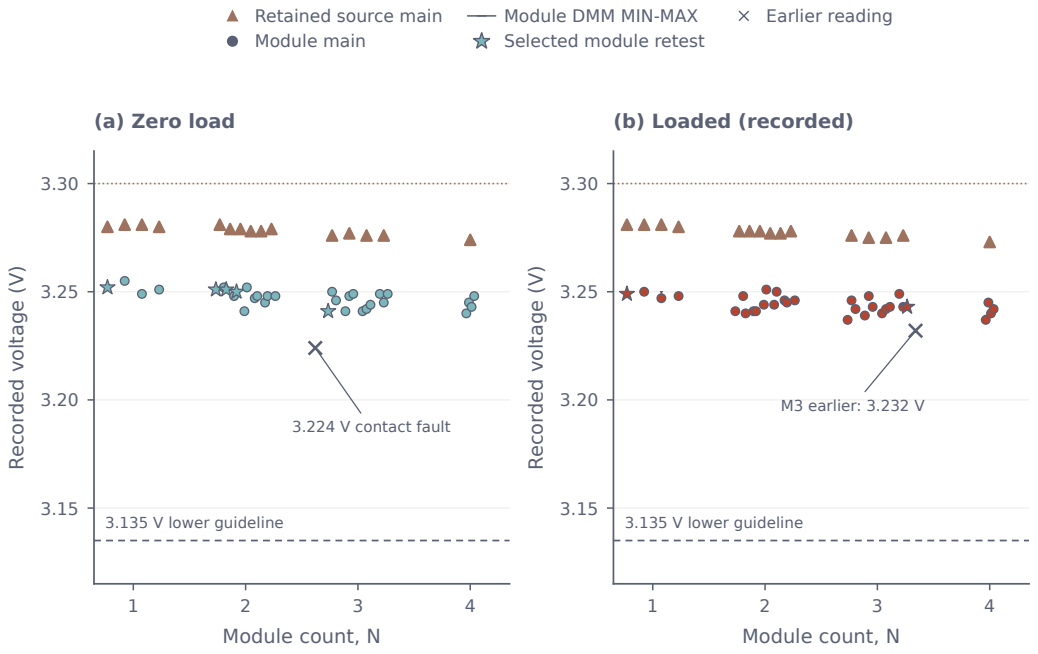
[picture p298: page 1]
Module count, N; Recorded voltage (V); 3.135 V lower guideline; 3.224 V contact fault; (a) Zero load; M3 earlier: 3.232 V; (b) Loaded (recorded); Earlier reading

Retained source main
Module main

Module DMM MIN-MAX
Selected module retest
