Yannas-Sun/E-skin_MSc_final_report/power scalability/DATA/analysis/current/report_v2_8_figures/branch_current_balance.pdf

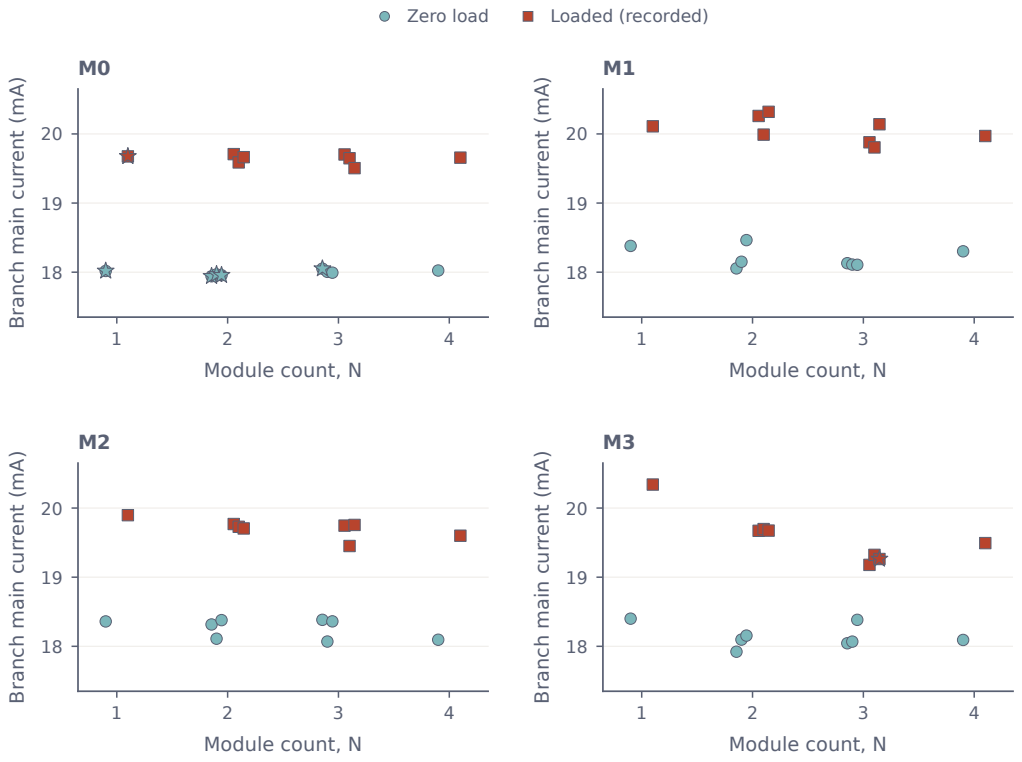
[picture p299: page 1]
Module count, N; Zero load; Loaded (recorded)

Branch main current (mA)
