Yannas-Sun/E-skin_MSc_final_report/power scalability/DATA/analysis/current/report_v2_8_figures/independent_current_prediction.pdf

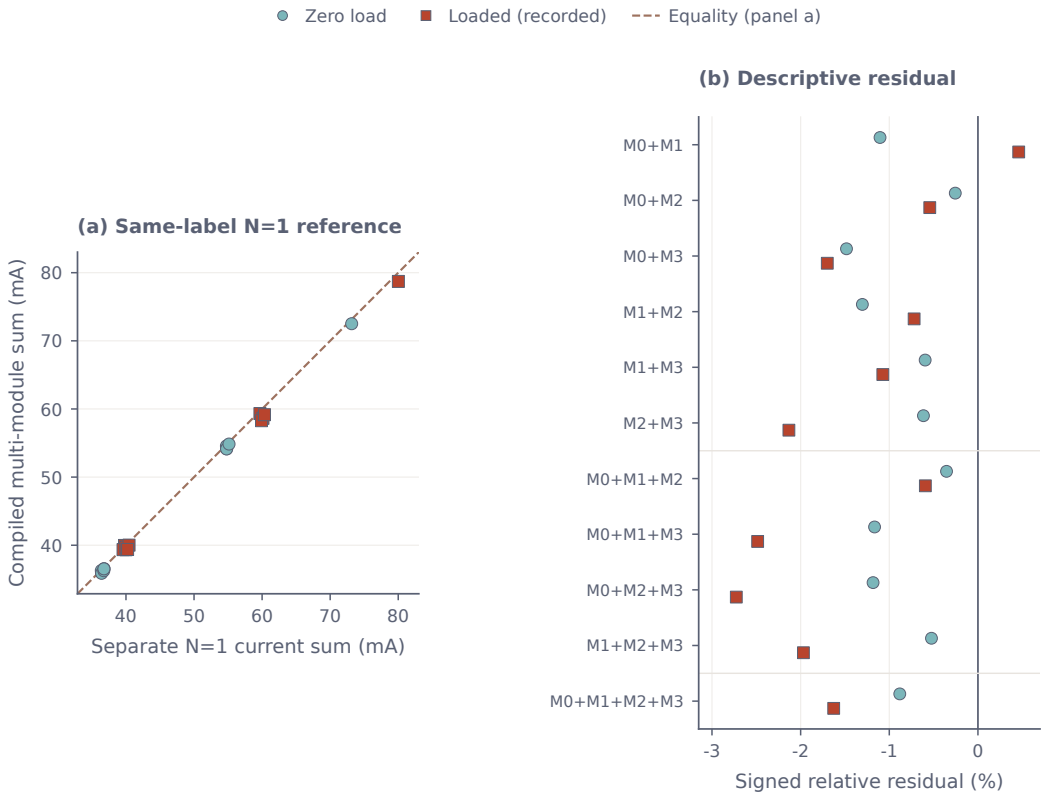
[picture p300: page 1]
(b) Descriptive residual; Zero load; Loaded (recorded); Equality (panel a)

(a) Same-label N=1 reference

Compiled multi-module sum (mA)

Separate N=1 current sum (mA)

Signed relative residual (%)
