Yannas-Sun/E-skin_MSc_final_report/power scalability/DATA/analysis/current/report_v2_8_figures/temperature_scaling.pdf

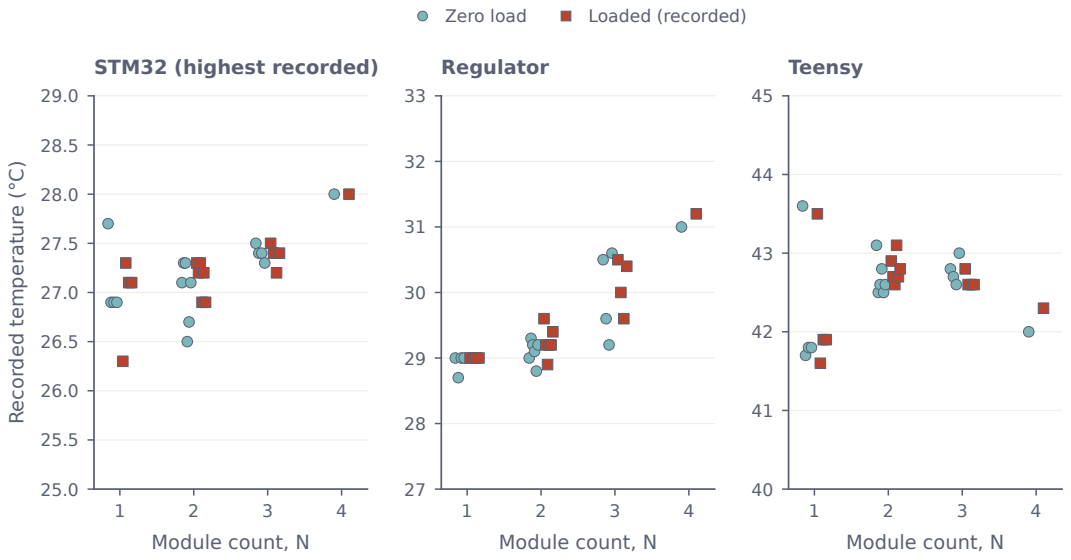
[picture p301: page 1]
Module count, N; Recorded temperature (°C); STM32 (highest recorded); Regulator; Teensy; Zero load; Loaded (recorded)
