Yannas-Sun/E-skin_MSc_final_report/data scalability/figures/exports/02_usb_theoretical_3d.pdf

# 02A USB: theoretical application-data demand

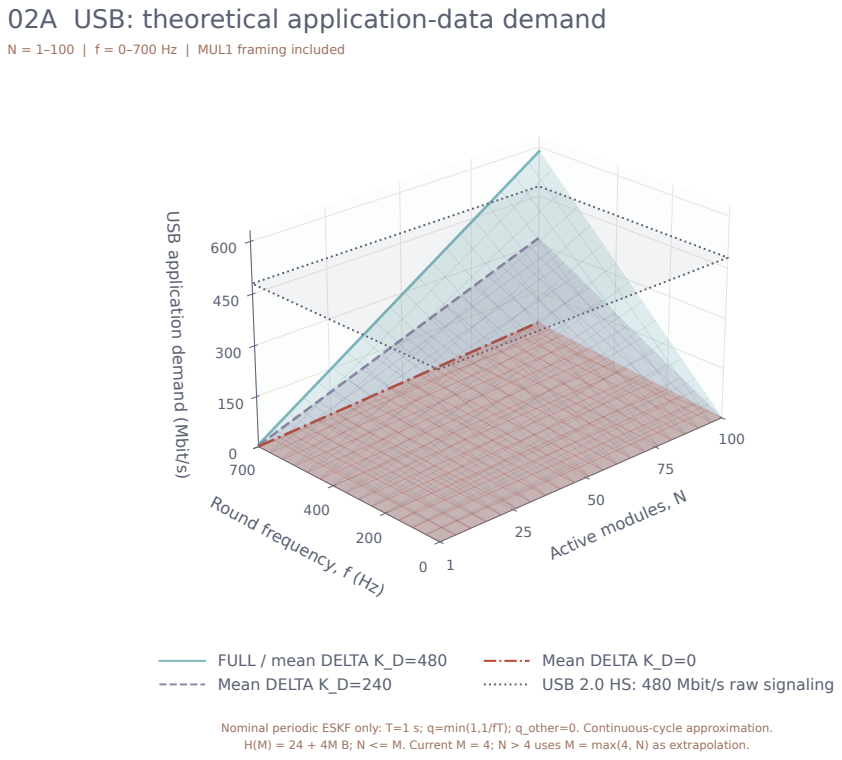
[picture p302: page 1]
Active modules, N

N = 1–100 | f = 0–700 Hz | MUL1 framing included

USB application demand (Mbit/s)

Round frequency, f (Hz)

FULL / mean DELTA K_D=480
Mean DELTA K_D=240

Mean DELTA K_D=0
USB 2.0 HS: 480 Mbit/s raw signaling

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
