Yannas-Sun/E-skin_MSc_final_report/data scalability/figures/exports/02c_host_spi_theoretical_3d.pdf

# 02C Host SPI: mean DELTA demand

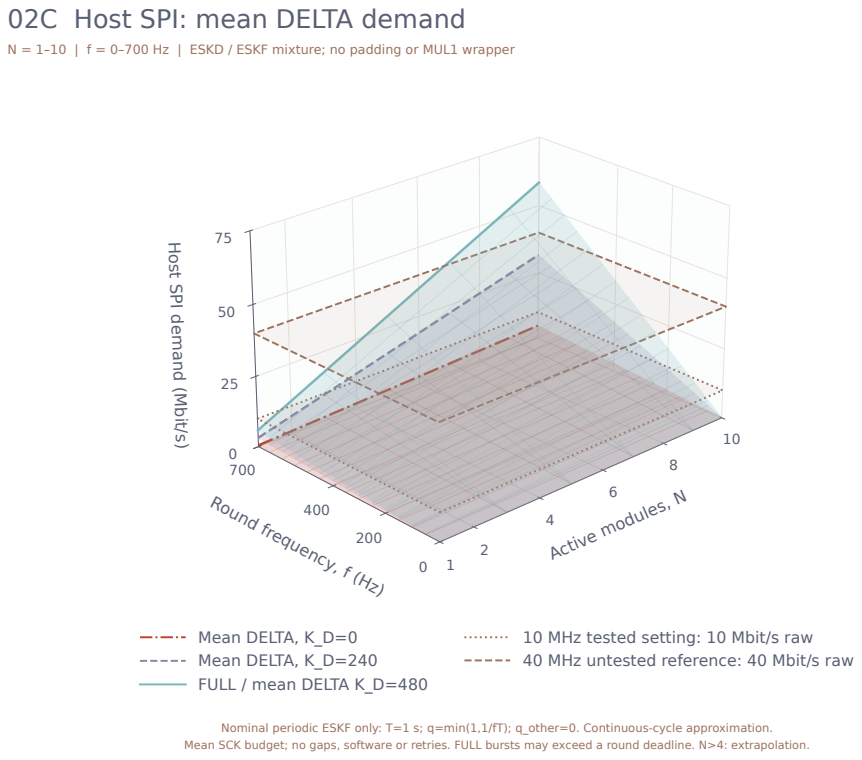
[picture p303: page 1]
Active modules, N

N = 1–10 | f = 0–700 Hz | ESKD / ESKF mixture; no padding or MUL1 wrapper

Host SPI demand (Mbit/s)

Round frequency, f (Hz)

Mean DELTA, K_D=0
Mean DELTA, K_D=240
FULL / mean DELTA K_D=480

10 MHz tested setting: 10 Mbit/s raw
40 MHz untested reference: 40 Mbit/s raw

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
