Yannas-Sun/E-skin_MSc_final_report/power scalability/DATA/analysis/current/voltage_drop_by_N_20260907/module_drop_N1_N4.pdf

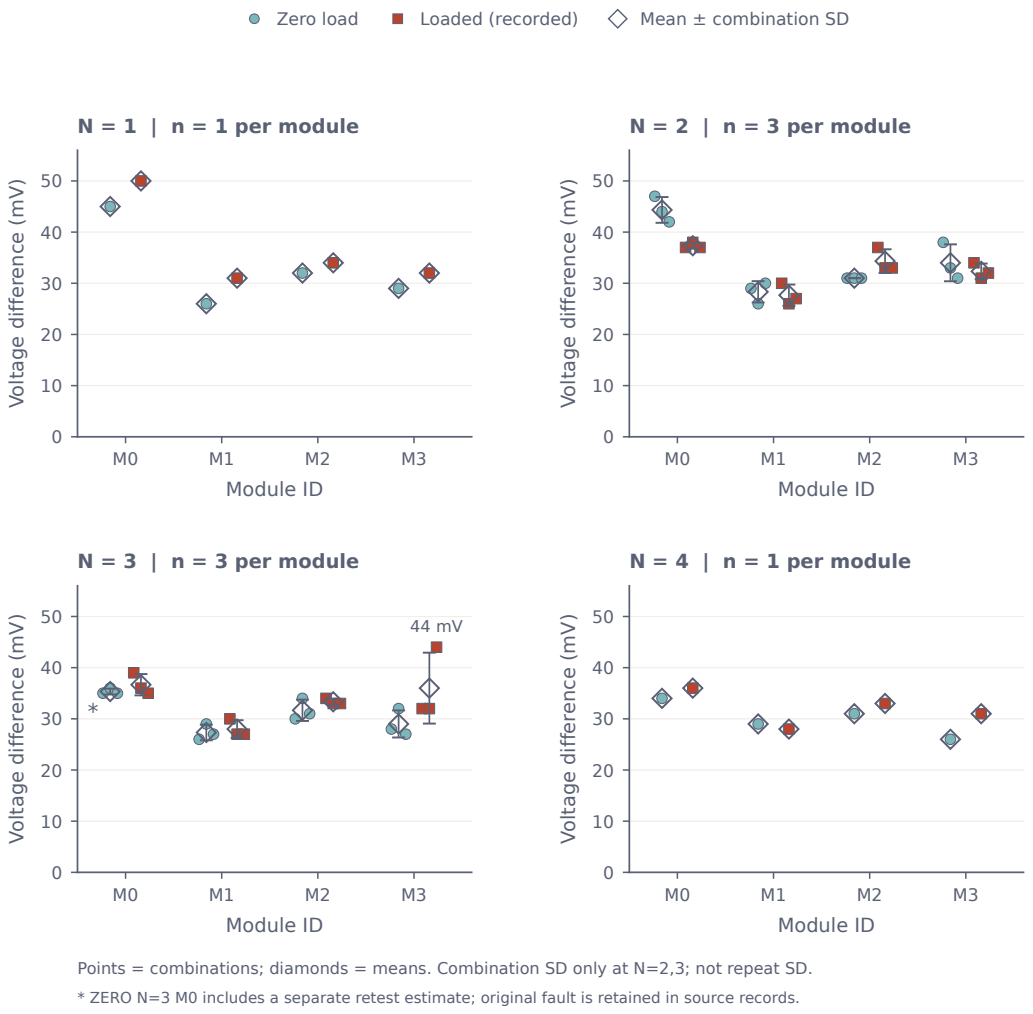
[picture p304: page 1]
Module ID; N = 1 | n = 1 per module; N = 2 | n = 3 per module; N = 3 | n = 3 per module; N = 4 | n = 1 per module; Zero load; Loaded (recorded); Mean ± combination SD

Voltage difference (mV)

Points = combinations; diamonds = means. Combination SD only at N=2,3; not repeat SD.
* ZERO N=3 M0 includes a separate retest estimate; original fault is retained in source records.
