Yannas-Sun/E-skin_MSc_final_report/Calibration scalability/DATA/module_1/FSR1/evaluation/analysis/dispersion/dispersion_cv.pdf

# M1 FSR1 | Coefficient of variation

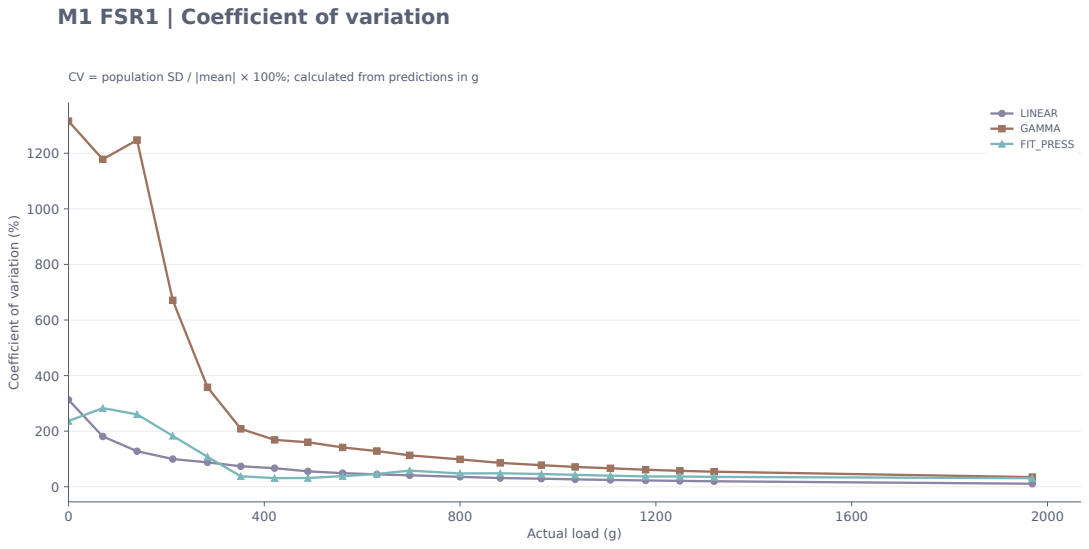
[picture p307: page 1]
Actual load (g); LINEAR GAMMA FIT_PRESS

CV = population SD / |mean| × 100%; calculated from predictions in g

Coefficient of variation (%)
