Yannas-Sun/E-skin_MSc_final_report/Calibration scalability/DATA/module_1/FSR1/evaluation/analysis/dispersion/dispersion_iqr.pdf

## M1 FSR1 | Interquartile range

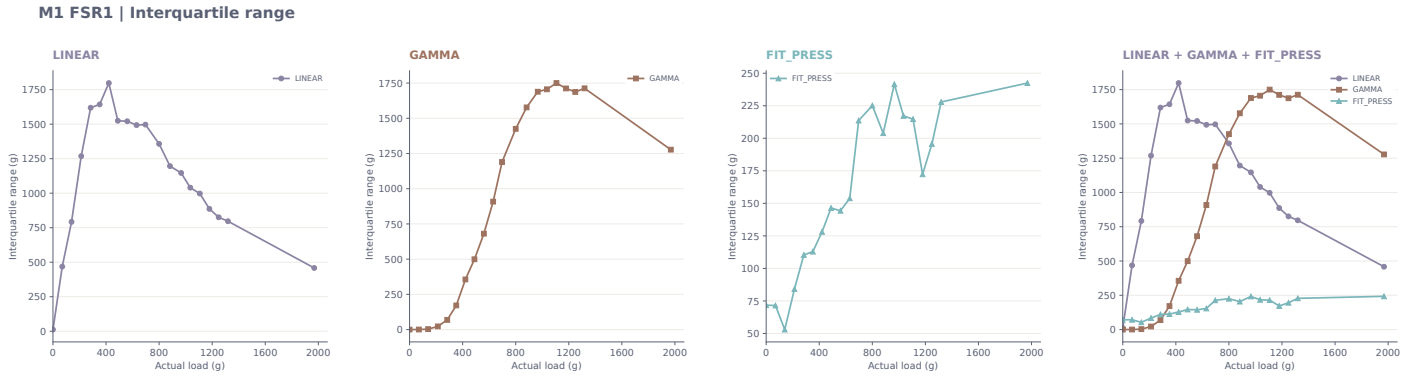
[picture p308: page 1]
Actual load (g); Interquartile range (g); LINEAR; GAMMA; FIT_PRESS; LINEAR + GAMMA + FIT_PRESS; LINEAR GAMMA FIT_PRESS
