Yannas-Sun/E-skin_MSc_final_report/Calibration scalability/DATA/module_1/FSR1/evaluation/analysis/dispersion/dispersion_mad.pdf

## M1 FSR1 | Median absolute deviation

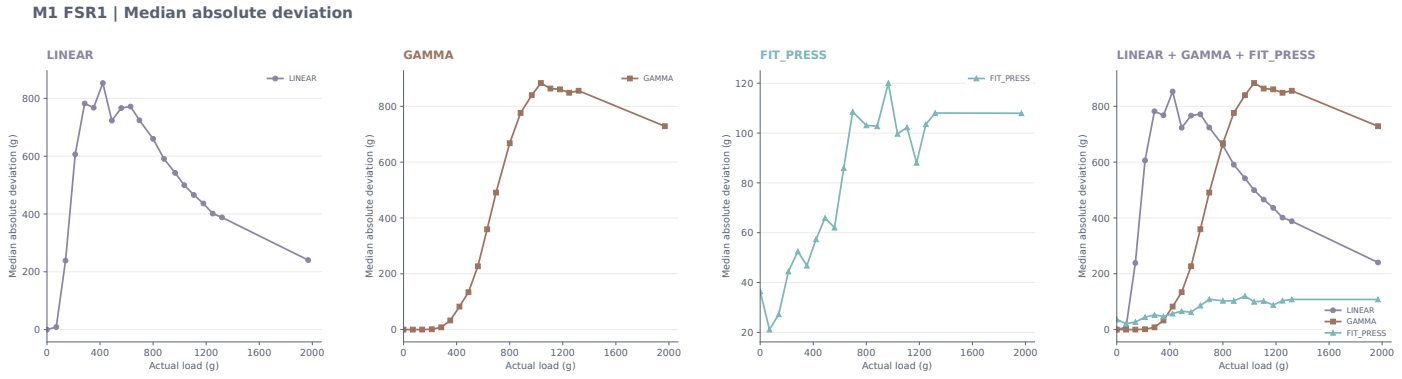
[picture p309: page 1]
Actual load (g); LINEAR; GAMMA; FIT_PRESS; LINEAR + GAMMA + FIT_PRESS; LINEAR GAMMA FIT_PRESS

Median absolute deviation (g)
