Yannas-Sun/E-skin_MSc_final_report/Calibration scalability/DATA/module_1/FSR1/evaluation/analysis/dispersion/dispersion_sd.pdf

## M1 FSR1 | Population standard deviation

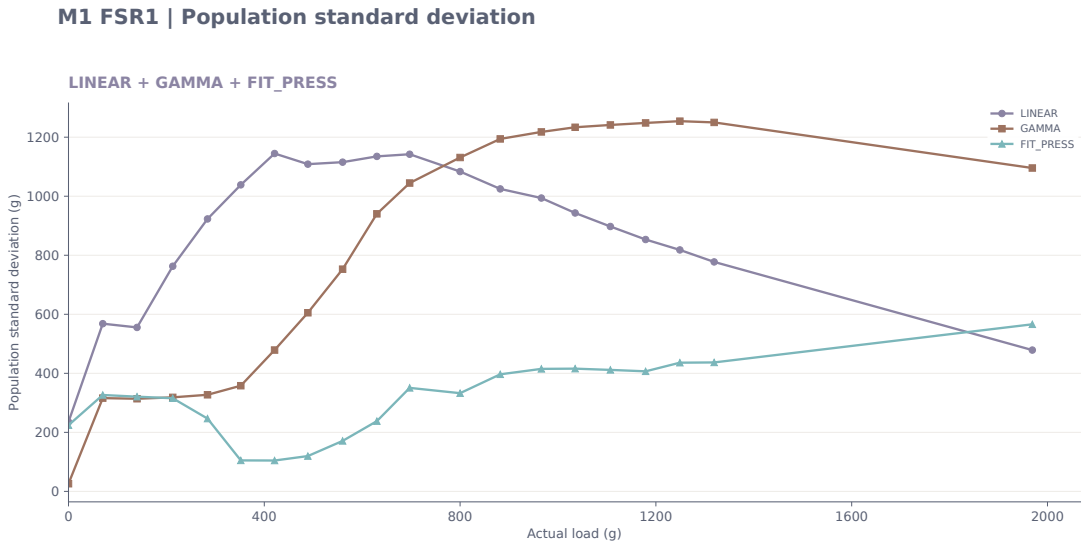
[picture p310: page 1]
Actual load (g); LINEAR + GAMMA + FIT_PRESS; GAMMA

LINEAR

FIT_PRESS

Population standard deviation (g)
