Yannas-Sun/E-skin_MSc_final_report/Calibration scalability/DATA/module_1/FSR1/evaluation/analysis/dispersion/dispersion_variance.pdf

## M1 FSR1 | Population variance

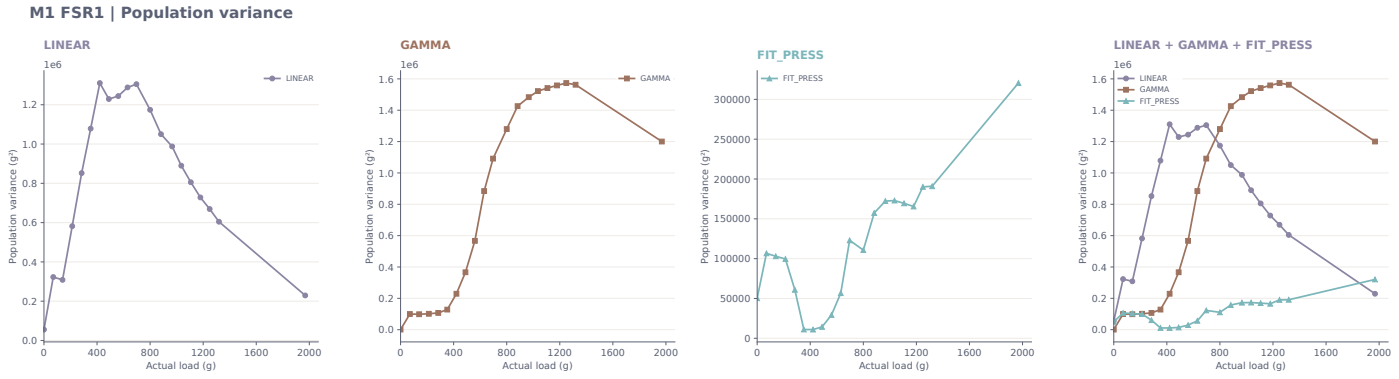
[picture p311: page 1]
Actual load (g); LINEAR; GAMMA; FIT_PRESS; LINEAR + GAMMA + FIT_PRESS; LINEAR GAMMA FIT_PRESS

Population variance (g²)
