Yannas-Sun/E-skin_MSc_final_report/Calibration scalability/DATA/module_1/FSR1/evaluation/analysis/error/load_error_vs_load.pdf

# M1 FSR1 | Load error: inferred minus actual

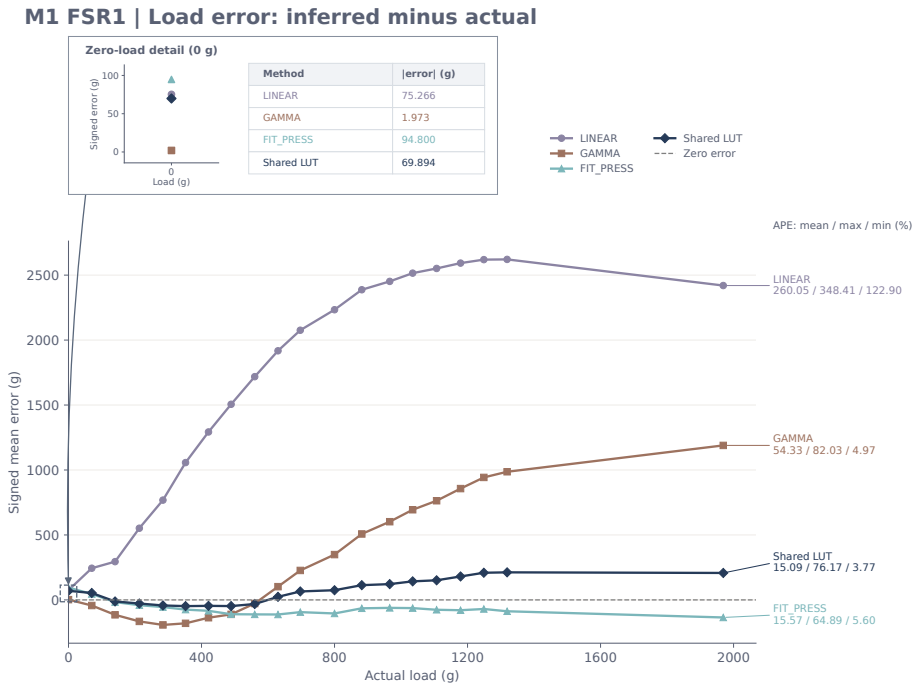
[picture p312: page 1]
Actual load (g); FIT_PRESS 15.57 / 64.89 / 5.60; Shared LUT 15.09 / 76.17 / 3.77; GAMMA 54.33 / 82.03 / 4.97; LINEAR 260.05 / 348.41 / 122.90; LINEAR GAMMA FIT_PRESS; Shared LUT Zero error; 0 Load (g); Signed error (g)

Zero-load detail (0 g)

Method | |error| (g)

LINEAR | 75.266

GAMMA | 1.973

FIT_PRESS | 94.800

Shared LUT | 69.894

APE: mean / max / min (%)

Signed mean error (g)
