Yannas-Sun/E-skin_MSc_final_report/Calibration scalability/DATA/module_1/FSR2/evaluation/analysis/dispersion/dispersion_comparison.pdf

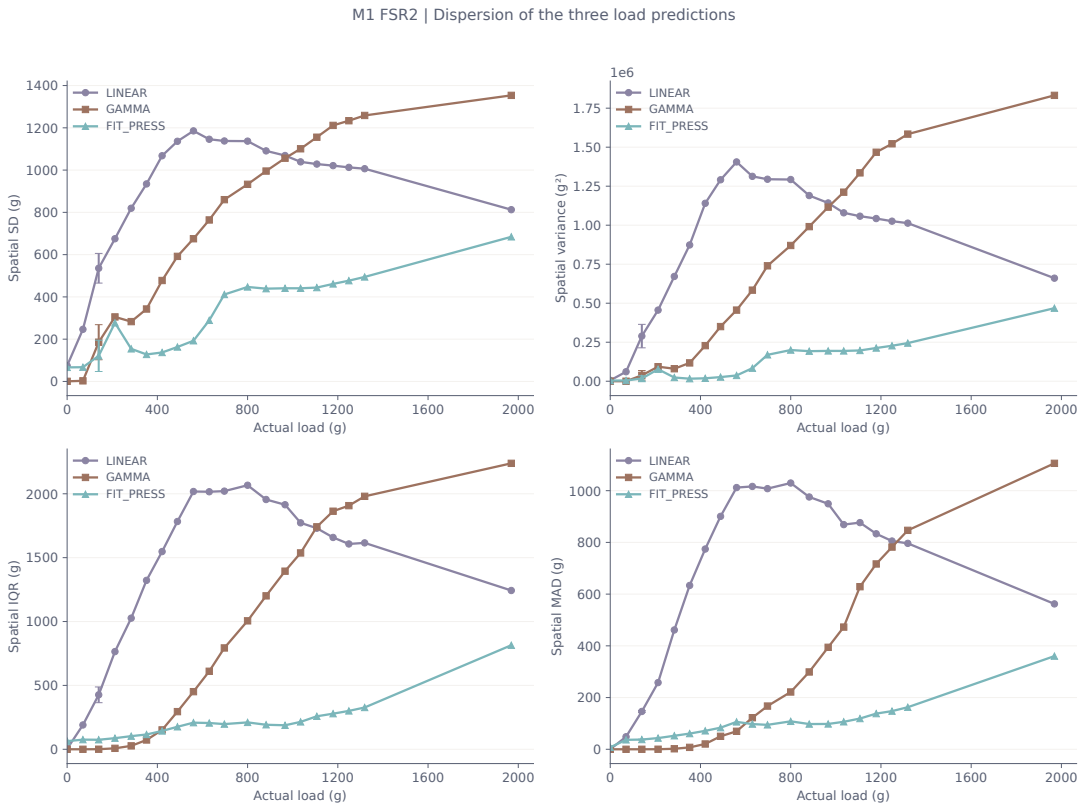
[picture p313: page 1]
Actual load (g); Spatial SD (g); LINEAR GAMMA FIT_PRESS; Spatial IQR (g); Spatial MAD (g)

M1 FSR2 | Dispersion of the three load predictions

Spatial variance (g²)
