Yannas-Sun/E-skin_MSc_final_report/Calibration scalability/DATA/module_1/FSR2/evaluation/analysis/dispersion/dispersion_mad.pdf

## M1 FSR2 | Median absolute deviation

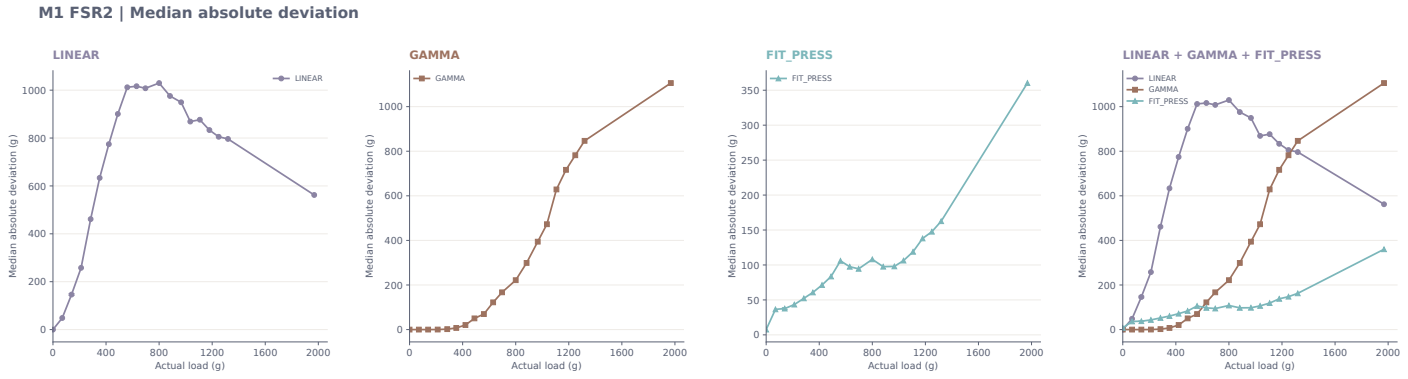
[picture p315: page 1]
Actual load (g); LINEAR; GAMMA; FIT_PRESS; LINEAR + GAMMA + FIT_PRESS; LINEAR GAMMA FIT_PRESS

Median absolute deviation (g)
