Yannas-Sun/E-skin_MSc_final_report/Calibration scalability/DATA/module_1/FSR2/evaluation/analysis/dispersion/dispersion_sd.pdf

## M1 FSR2 | Population standard deviation

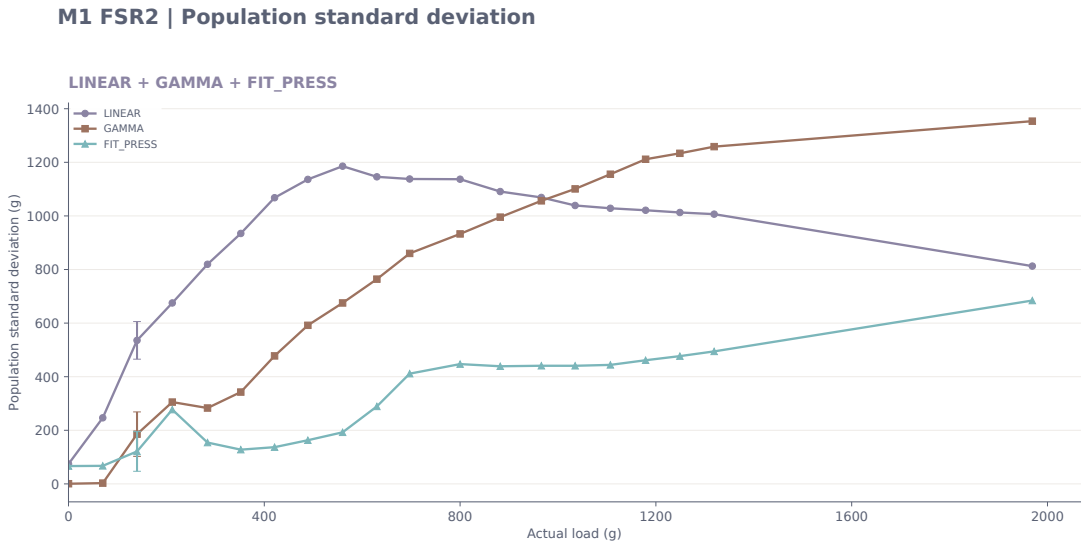
[picture p316: page 1]
Actual load (g); LINEAR + GAMMA + FIT_PRESS; LINEAR GAMMA FIT_PRESS

Population standard deviation (g)
