Yannas-Sun/E-skin_MSc_final_report/Calibration scalability/DATA/module_1/FSR2/evaluation/analysis/error/load_error_vs_load.pdf

# M1 FSR2 | Load error: inferred minus actual

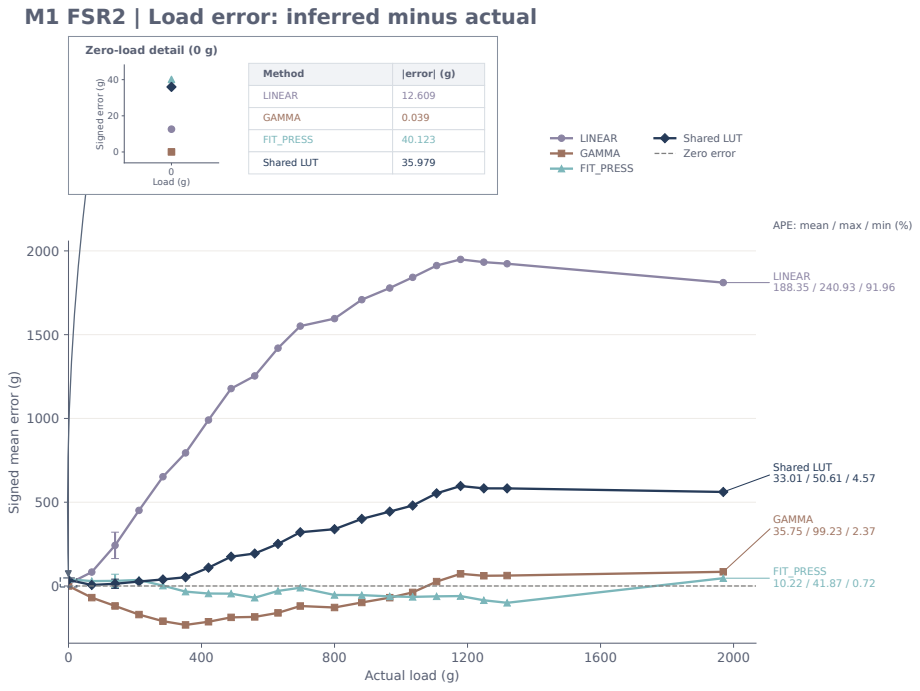
[picture p318: page 1]
Actual load (g); FIT_PRESS 10.22 / 41.87 / 0.72; GAMMA 35.75 / 99.23 / 2.37; Shared LUT 33.01 / 50.61 / 4.57; LINEAR 188.35 / 240.93 / 91.96; LINEAR GAMMA FIT_PRESS; Shared LUT Zero error; Method; |error| (g); LINEAR; GAMMA; FIT_PRESS; Shared LUT; 0 Load (g); Signed error (g)

Zero-load detail (0 g)

APE: mean / max / min (%)

Signed mean error (g)
