Yannas-Sun/E-skin_MSc_final_report/power scalability/archive/legacy_analysis/DATA_analysis/figures/current_power_scaling.pdf

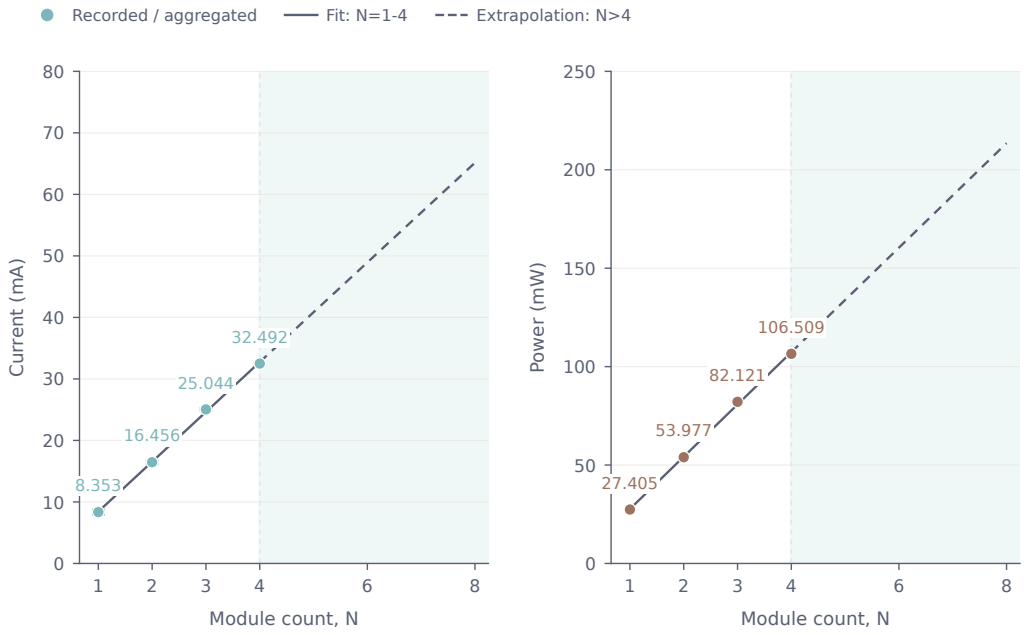
[picture p319: page 1]
Module count, N; Current (mA); Power (mW); Recorded / aggregated; Fit: N=1-4; Extrapolation: N>4
