Yannas-Sun/E-skin_MSc_final_report/Imperial College Individual Project Template_LaTeX/figures/data/v2_9/data_length_traces.pdf

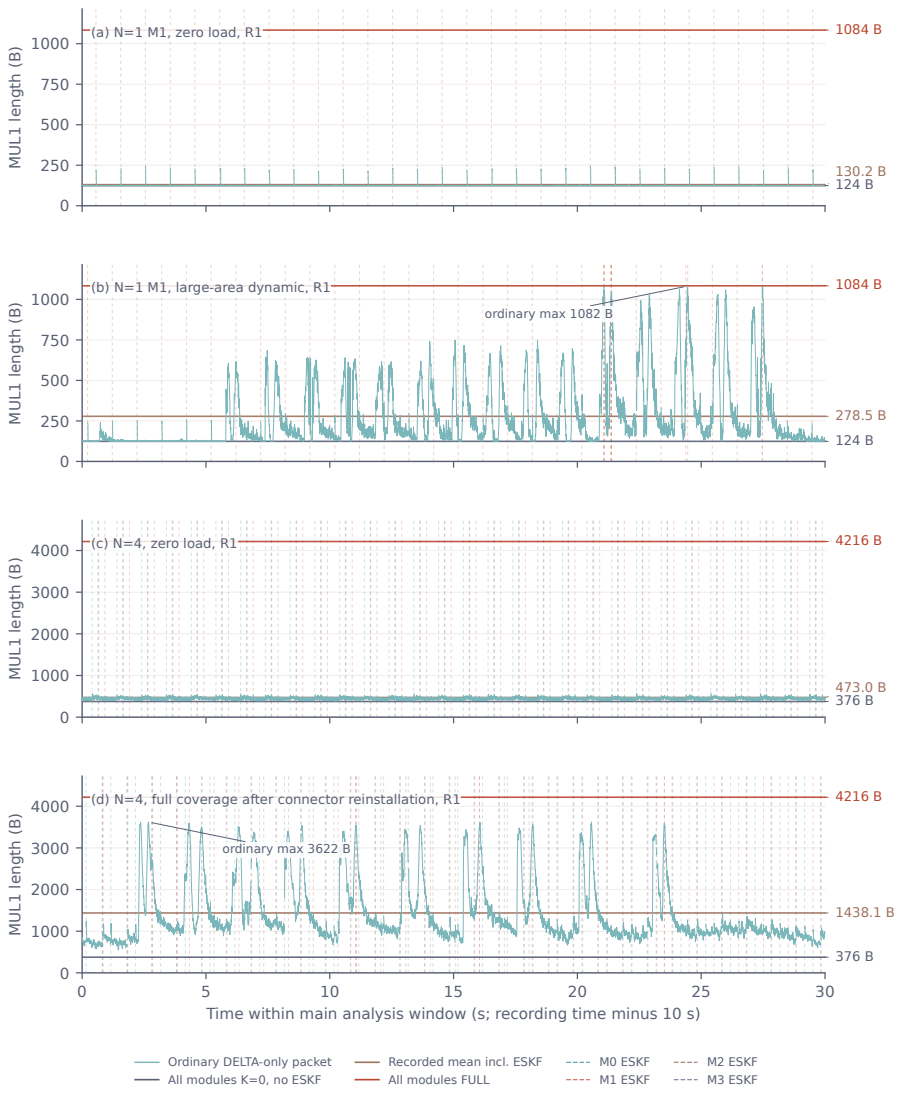
[picture p320: page 1]
MUL1 length (B); (a) N=1 M1, zero load, R1; ordinary max 1082 B; (c) N=4, zero load, R1; M0 ESKF M1 ESKF; M2 ESKF M3 ESKF

(b) N=1 M1, large-area dynamic, R1

(d) N=4, full coverage after connector reinstallation, R1

ordinary max 3622 B

Time within main analysis window (s; recording time minus 10 s)

Ordinary DELTA-only packet
All modules K=0, no ESKF

Recorded mean incl. ESKF
All modules FULL
