Yannas-Sun/E-skin_MSc_final_report/hardware/prototype/mainboard/design/mainboard.cir

.title KiCad schematic
R_LED1 Net-_D1-K_ GND 1k
D1 Net-_D1-K_ +3.3V LED
R1 /FPGA_3V3_IN +3.3V 0
MOUNT6 __MOUNT6
MOUNT2 __MOUNT2
MOUNT3 __MOUNT3
MOUNT4 __MOUNT4
MOUNT5 __MOUNT5
MOUNT1 __MOUNT1
C17 GND +3.3V 100n
C18 GND +3.3V 10u
J2 __J2
ADC_SPI_HDR1 __ADC_SPI_HDR1
J1 __J1
C2 +3.3V GND 100n
RN1 __RN1
MUX_CTRL_HDR1 __MUX_CTRL_HDR1
SWD_HDR1 __SWD_HDR1
MCU1 __MCU1
C5 GND +3.3V 100n
C1 GND +3.3V 100n
C6 GND +3.3V 100n
COL_FPC1 __COL_FPC1
COL_FPC2 __COL_FPC2
RN3 __RN3
RN2 __RN2
COL_ADC1 __COL_ADC1
RN5 __RN5
COL_ADC2 __COL_ADC2
ROW_FPC1 __ROW_FPC1
R_MUX2_COM1 +3.3V Net-_ROW_MUX2-COM_ 1k
ROW_MUX2 __ROW_MUX2
ROW_FPC2 __ROW_FPC2
C8 +3.3V GND 100n
C15 GND +3.3V 100n
ROW_MUX1 __ROW_MUX1
R_MUX1_COM1 +3.3V Net-_ROW_MUX1-COM_ 1k
C16 GND +3.3V 100n
ACC_DEC1 __ACC_DEC1
C7 GND +3.3V 100n
ACC_FPC1 __ACC_FPC1
C14 GND +3.3V 100n
C9 GND +3.3V 100n
C10 GND +3.3V 100n
C13 GND +3.3V 100n
C11 GND +3.3V 100n
C12 GND +3.3V 100n
RN4 __RN4
.end
