Yannas-Sun/E-skin_MSc_final_report/power scalability/DATA/raw/canonical/power_experiment_records/no_transmission/n=2/M0-M1/zero_load/PS01_N2_F200_ZERO_M0-M1_STANDBY_R1.yaml

run_id: PS01_N2_F200_ZERO_M0-M1_STANDBY_R1
date:
measurement_start_time:
operator:

record_status: MEASURED
data_quality: INCOMPLETE

module_count: 2
module_ids: Module0,Module1
frequency_hz: 200
protocol_mode: FULL
load: ZERO
load_mass_g: 0
load_area_mm2: 0
load_application: NONE
acc_used: NO

host_controller: Teensy 4.1
host_connected_to_modules: YES
host_software_running: YES
host_power_source: USB
host_power_status: STABLE_USB_SUPPLY
host_gui_state: CLOSED
host_usb_polling_state: BLOCKED_STANDBY_NO_CONTINUOUS_USB_READ
module_signal_connection: HOST_SPI
stm32_swd_connection: DISCONNECTED

power_supply_v: 3.3
power_supply_model: LM2596
power_topology: INDEPENDENT_PARALLEL_BRANCHES
power_return: COMMON_GND
power_supply_current_limit_setting_mA: NOT_AVAILABLE

DMM_current_range: mA
current_measurement_method: SEPARATE_BRANCH
measurement_duration_s: 10
warmup_duration_s: 30
V_source_avg_V: 3.280
V_source_min_V: 3.280
V_source_max_V: 3.280

V_module0_avg_V: 3.263
V_module0_min_V: 3.262
V_module0_max_V: 3.264
V_module1_avg_V: 3.269
V_module1_min_V: 3.268
V_module1_max_V: 3.270

I_module0_avg_mA: 8.086
I_module0_min_mA: 8.081
I_module0_max_mA: 16.19
I_module0_peak_instant_mA: 16.19
I_module1_avg_mA: 8.181
I_module1_min_mA: 8.157
I_module1_max_mA: 16.21
I_module1_peak_instant_mA: 16.21

T_start_C: 25.2
T_module0_stm32_C: 25.9
T_module1_stm32_C: 26.1
T_regulator_C: 29.3
T_teensy_C: 45.7

# Default is 0; replace with the observed count if an event occurs.
reset_count: 0
current_limit_count: 0
brownout_count: 0
data_stop_count: 0
data_gap_count: 0
other_fault: 0
observation:
conclusion:
