Yannas-Sun/E-skin_MSc_final_report/power scalability/DATA/raw/canonical/power_experiment_records/transmission/n=3/M0-M1-M2/full_load/PS01_N3_F200_MAX_M0-M1-M2_USB_RX_R1.yaml

run_id: PS01_N3_F200_MAX_M0-M1-M2_USB_RX_R1
date:
measurement_start_time:
operator:

record_status: MEASURED
data_quality: COMPLETE

module_count: 3
module_ids: Module0,Module1,Module2
frequency_hz: 200
protocol_mode: FULL
load: MAX
load_mass_g: 2000
load_area_mm2:
load_application:
acc_used: NO

host_controller: Teensy 4.1
host_connected_to_modules: YES
host_software_running: YES
host_power_source: USB
host_power_status: STABLE_USB_SUPPLY
host_gui_state: OPEN_IDLE
host_usb_polling_state: CONTINUOUS_USB_READ
module_signal_connection: HOST_SPI
stm32_swd_connection: DISCONNECTED

power_supply_v: 3.3
power_supply_model: LM2596
power_topology: INDEPENDENT_PARALLEL_BRANCHES
power_return: COMMON_GND
power_supply_current_limit_setting_mA: NOT_AVAILABLE

DMM_current_range: mA
current_measurement_method: SEPARATE_BRANCH
measurement_duration_s: 10
warmup_duration_s: 30
V_source_avg_V: 3.276
V_source_min_V: 3.275
V_source_max_V: 3.276

V_module0_avg_V: 3.237
V_module0_min_V: 3.237
V_module0_max_V: 3.237
V_module1_avg_V: 3.246
V_module1_min_V: 3.246
V_module1_max_V: 3.246
V_module2_avg_V: 3.242
V_module2_min_V: 3.242
V_module2_max_V: 3.243

I_module0_avg_mA: 19.703
I_module0_min_mA: 19.69
I_module0_max_mA: 19.73
I_module0_peak_instant_mA: N/A
I_module1_avg_mA: 19.879
I_module1_min_mA: 19.86
I_module1_max_mA: 19.89
I_module1_peak_instant_mA: N/A
I_module2_avg_mA: 19.746
I_module2_min_mA: 19.74
I_module2_max_mA: 19.77
I_module2_peak_instant_mA: N/A

T_start_C:
T_module0_stm32_C: 27.5
T_module1_stm32_C: 27.2
T_module2_stm32_C: 26.8
T_regulator_C: 30.5
T_teensy_C: 42.8

# Default is 0; replace with the observed count if an event occurs.
reset_count: 0
current_limit_count: 0
brownout_count: 0
data_stop_count: 0
data_gap_count: 0
other_fault: 0
observation:
conclusion:
