Yannas-Sun/E-skin_MSc_final_report/Calibration scalability/script/Main/calibration_shared_endpoints.py

"""Whole-layer calibration with two-point endpoints derived from one sweep."""
from __future__ import annotations

import json
import queue
import subprocess
import sys
import threading
import time
import textwrap
from datetime import datetime, timezone
from pathlib import Path

import numpy as np

from Calibration.calibrate_fsr import build_from_sweep, save_calibration
from calibration_measurement import CalibrationMeasurementMixin

PROTOCOL = "whole_layer_shared_endpoints_v3"
FRAME_COUNT = 200
TIMEOUT = 20.0
MODEL_DIR = Path(__file__).resolve().parent / "Model"


def now():
    return datetime.now(timezone.utc).isoformat()


def stamp():
    return datetime.now().strftime("%Y%m%d_%H%M%S_%f")


def save_sweep(root, *, module_id, fsr, points, source, started_at):
    loads = {float(p["pressure"]) for p in points}
    if len(loads) < 3 or 0.0 not in loads or max(loads) <= 0:
        raise ValueError("Record 0 g, intermediate load(s), and a final maximum load")
    if any(not np.isfinite(p) or p < 0 for p in loads):
        raise ValueError("All loads must be finite and nonnegative")
    if float(points[-1]["pressure"]) != max(loads):
        raise ValueError("The last recorded load must equal the maximum load")
    if float(points[0]["pressure"]) != 0:
        raise ValueError("The first recorded load must be 0 g")
    for point in points:
        frames = np.asarray(point["raw_frames"], dtype=float)
        raw = np.asarray(point["raw_adc"], dtype=float)
        if (frames.shape != (FRAME_COUNT, 16, 16) or not np.isfinite(frames).all()
                or np.any(frames < 0) or np.any(frames > 4095) or np.any(frames != np.floor(frames))):
            raise ValueError("Each load needs 200 complete FULL frames")
        if not np.array_equal(raw, np.median(frames, axis=0)):
            raise ValueError("Each load must use the per-cell median")
    data = {
        "format": "e-skin-fsr-pressure-response-sweep", "version": 3,
        "protocol_id": PROTOCOL, "load_range_g": [0, max(loads)],
        "capture_scope": "whole_layer", "created_at": now(), "started_at": started_at,
        "module_id": module_id, "fsr": fsr, "matrix": {"rows": 16, "columns": 16},
        "response": {"type": "raw_adc_code", "adc_bits": 12, "maximum_code": 4095},
        "pressure": {"unit": "g", "meaning": "applied whole-layer calibration mass"},
        "acquisition": {"frames_per_point": FRAME_COUNT, "aggregation": "per-cell median",
                        "accepted_family": "FULL", "loading_geometry": "fixed whole-layer fixture"},
        "source": source, "points": points,
    }
    directory = root / "DATA" / f"module_{module_id}" / fsr / "fit" / "raw"
    directory.mkdir(parents=True, exist_ok=True)
    path = directory / f"{fsr}_pressure_sweep_{stamp()}.json"
    with path.open("x", encoding="utf-8") as handle:
        json.dump(data, handle, indent=2, allow_nan=False)
    return path
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
